DvidMakesThings/HW_10-In-Rack_PDU/docs/doxygen/latex/power__mgr_8c.tex

\doxysection{src/\+Software/\+ENERGIS\+\_\+\+RTOS/src/misc/power\+\_\+mgr.c File Reference}
\hypertarget{power__mgr_8c}{}\label{power__mgr_8c}\index{src/Software/ENERGIS\_RTOS/src/misc/power\_mgr.c@{src/Software/ENERGIS\_RTOS/src/misc/power\_mgr.c}}
{\ttfamily \#include "{}CONFIG.\+h"{}}\newline
Include dependency graph for power\+\_\+mgr.\+c\+:\nopagebreak
\begin{figure}[H]
\begin{center}
\leavevmode
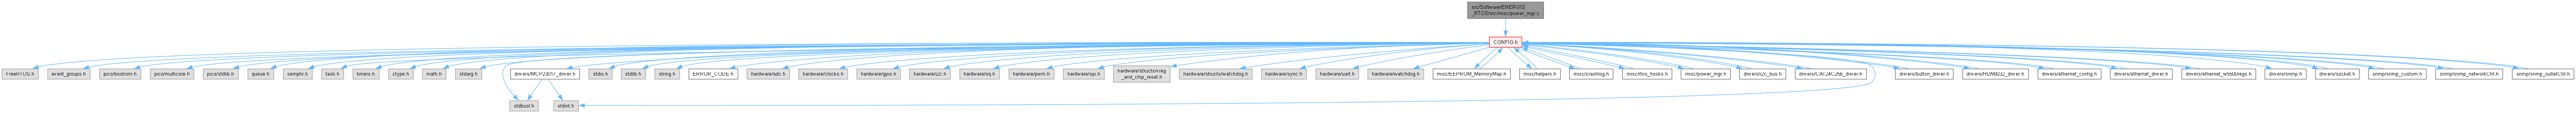
[picture p25: docs/doxygen/html/power__mgr_8c__incl.png]

\end{center}
\end{figure}
\doxysubsubsection*{Macros}
\begin{DoxyCompactItemize}
\item 
\#define \mbox{\hyperlink{power__mgr_8c_ab401161121a77906483bddf8a325013a}{POWER\+\_\+\+MGR\+\_\+\+TAG}}~"{}\mbox{[}Power\+Mgr\mbox{]}"{}
\end{DoxyCompactItemize}
\doxysubsubsection*{Functions}
\begin{DoxyCompactItemize}
\item 
static void \mbox{\hyperlink{power__mgr_8c_acf3f068b9c2b4714ec8b7b1eb2eff1e9}{turn\+\_\+off\+\_\+all\+\_\+relays}} (void)
\begin{DoxyCompactList}\small\item\em Disable all relay outputs using Switch\+Task API. \end{DoxyCompactList}\item 
static void \mbox{\hyperlink{power__mgr_8c_a61f31550510de9c4f3196700e41216ff}{turn\+\_\+off\+\_\+leds\+\_\+except\+\_\+pwr}} (void)
\begin{DoxyCompactList}\small\item\em Disable display LEDs except PWR\+\_\+\+LED for standby indication. \end{DoxyCompactList}\item 
static void \mbox{\hyperlink{power__mgr_8c_ae6615d2590136a1a1be071dce3a0690d}{turn\+\_\+off\+\_\+selection\+\_\+leds}} (void)
\begin{DoxyCompactList}\small\item\em Disable all channel selection LEDs. \end{DoxyCompactList}\item 
static void \mbox{\hyperlink{power__mgr_8c_af91a61d8ecbe1011e8a24851ca9602b6}{w5500\+\_\+hold\+\_\+reset}} (void)
\begin{DoxyCompactList}\small\item\em Assert W5500 hardware reset to disable Ethernet. \end{DoxyCompactList}\item 
static void \mbox{\hyperlink{power__mgr_8c_a0c57fadaa1a399b1257ebd7203e7884e}{w5500\+\_\+release\+\_\+reset}} (void)
\begin{DoxyCompactList}\small\item\em Deassert W5500 hardware reset to enable Ethernet. \end{DoxyCompactList}\item 
static void \mbox{\hyperlink{power__mgr_8c_afef33669bd179ec2e445c223bb1272a3}{set\+\_\+pwr\+\_\+led\+\_\+tracked}} (bool on)
\begin{DoxyCompactList}\small\item\em Set PWR\+\_\+\+LED state with change tracking. \end{DoxyCompactList}\item 
void \mbox{\hyperlink{group__misc3_ga83454e7bafa44edd5acce76b7aa91e0b}{Power\+\_\+\+Init}} (void)
\begin{DoxyCompactList}\small\item\em Initialize the power manager subsystem. \end{DoxyCompactList}\item 
\mbox{\hyperlink{group__misc3_gacd64982bf58e213a07ae1fe0f2235cb9}{power\+\_\+state\+\_\+t}} \mbox{\hyperlink{group__misc3_gad3252fba1863d278f2611cad531177f5}{Power\+\_\+\+Get\+State}} (void)
\begin{DoxyCompactList}\small\item\em Query the current system power state. \end{DoxyCompactList}\item 
void \mbox{\hyperlink{group__misc3_ga40de5935f9ba85f9141a9243b4d02c87}{Power\+\_\+\+Enter\+Standby}} (void)
\begin{DoxyCompactList}\small\item\em Enter standby mode. \end{DoxyCompactList}\item 
void \mbox{\hyperlink{group__misc3_gafa726e9d0fc140faa3f54c6905ac2520}{Power\+\_\+\+Exit\+Standby}} (void)
\begin{DoxyCompactList}\small\item\em Exit standby mode and return to normal operation. \end{DoxyCompactList}\item 
void \mbox{\hyperlink{group__misc3_ga0827dd667e39150cad0b7642a076d384}{Power\+\_\+\+Service\+Standby\+LED}} (void)
\begin{DoxyCompactList}\small\item\em Service LED indication in RUN and STANDBY modes. \end{DoxyCompactList}\end{DoxyCompactItemize}
\doxysubsubsection*{Variables}
\begin{DoxyCompactItemize}
\item 
static volatile \mbox{\hyperlink{group__misc3_gacd64982bf58e213a07ae1fe0f2235cb9}{power\+\_\+state\+\_\+t}} \mbox{\hyperlink{power__mgr_8c_aff8ae2fef9f0e3de41d83c40420a3da5}{s\+\_\+power\+\_\+state}} = \mbox{\hyperlink{group__misc3_ggacd64982bf58e213a07ae1fe0f2235cb9a63a8aa4bf635f74171bbfe8f145dd1cf}{PWR\+\_\+\+STATE\+\_\+\+RUN}}
\begin{DoxyCompactList}\small\item\em Current system power state (atomic access required) \end{DoxyCompactList}\item 
static volatile bool \mbox{\hyperlink{power__mgr_8c_a328078913eedcf9a440c49aa2805df76}{s\+\_\+pwr\+\_\+led\+\_\+state}} = false
\begin{DoxyCompactList}\small\item\em Tracks current PWR\+\_\+\+LED state to avoid redundant I2C writes. true = LED is ON, false = LED is OFF. \end{DoxyCompactList}\item 
\begin{tabbing}
xx\=xx\=xx\=xx\=xx\=xx\=xx\=xx\=xx\=\kill
struct \{\\
\>uint32\_t \mbox{\hyperlink{power__mgr_8c_a55c9db1db2e7f9a80337d744a4aef512}{last\_update\_ms}}\\
\>uint8\_t \mbox{\hyperlink{power__mgr_8c_a8f0aef86d47e45a899f77a8bb89d6432}{phase}}\\
\>uint8\_t \mbox{\hyperlink{power__mgr_8c_ac6116d5235e13e059e591879c46d7174}{direction}}\\
\} \mbox{\hyperlink{power__mgr_8c_a72aa8664ac0542eb9697aadbf5a93b1e}{s\_led\_anim}} = \{0, 0, 0\}\\

\end{tabbing}\begin{DoxyCompactList}\small\item\em Standby LED animation state. \end{DoxyCompactList}\end{DoxyCompactItemize}

\doxysubsection{Detailed Description}
\begin{DoxyAuthor}{Author}
Dvid\+Makes\+Things -\/ David Sipos
\end{DoxyAuthor}
\begin{DoxyVersion}{Version}
1.\+2.\+0 
\end{DoxyVersion}
\begin{DoxyDate}{Date}
2025-\/12-\/10
\end{DoxyDate}
Implementation of centralized power state management including standby mode entry/exit logic, hardware peripheral control coordination, and LED animation for standby indication.

This module coordinates multiple hardware peripherals (W5500, MCP23017, relays) and provides thread-\/safe state query for task behavior adaptation.

@project ENERGIS -\/ The Managed PDU Project for 10-\/Inch Rack @github \href{https://github.com/DvidMakesThings/HW_10-In-Rack_PDU}{\texttt{https\+://github.\+com/\+Dvid\+Makes\+Things/\+HW\+\_\+10-\/\+In-\/\+Rack\+\_\+\+PDU}} 

\label{doc-define-members}
\Hypertarget{power__mgr_8c_doc-define-members}
\doxysubsection{Macro Definition Documentation}
\Hypertarget{power__mgr_8c_ab401161121a77906483bddf8a325013a}\index{power\_mgr.c@{power\_mgr.c}!POWER\_MGR\_TAG@{POWER\_MGR\_TAG}}
\index{POWER\_MGR\_TAG@{POWER\_MGR\_TAG}!power\_mgr.c@{power\_mgr.c}}
\doxysubsubsection{\texorpdfstring{POWER\_MGR\_TAG}{POWER\_MGR\_TAG}}
{\footnotesize\ttfamily \label{power__mgr_8c_ab401161121a77906483bddf8a325013a} 
\#define POWER\+\_\+\+MGR\+\_\+\+TAG~"{}\mbox{[}Power\+Mgr\mbox{]}"{}}

\label{doc-func-members}
\Hypertarget{power__mgr_8c_doc-func-members}
\doxysubsection{Function Documentation}
\Hypertarget{power__mgr_8c_afef33669bd179ec2e445c223bb1272a3}\index{power\_mgr.c@{power\_mgr.c}!set\_pwr\_led\_tracked@{set\_pwr\_led\_tracked}}
\index{set\_pwr\_led\_tracked@{set\_pwr\_led\_tracked}!power\_mgr.c@{power\_mgr.c}}
\doxysubsubsection{\texorpdfstring{set\_pwr\_led\_tracked()}{set\_pwr\_led\_tracked()}}
{\footnotesize\ttfamily \label{power__mgr_8c_afef33669bd179ec2e445c223bb1272a3} 
void set\+\_\+pwr\+\_\+led\+\_\+tracked (\begin{DoxyParamCaption}\item[{bool}]{on}{}\end{DoxyParamCaption})\hspace{0.3cm}{\ttfamily [static]}}

Set PWR\+\_\+\+LED state with change tracking. 

Updates PWR\+\_\+\+LED state only if it differs from the current tracked state, avoiding redundant I2C write operations that can cause bus contention.

\begin{DoxyParams}{Parameters}
{\em on} & true to enable LED, false to disable LED\\
\hline
\end{DoxyParams}
\begin{DoxyReturn}{Returns}
None 
\end{DoxyReturn}
Here is the call graph for this function\+:\nopagebreak
\begin{figure}[H]
\begin{center}
\leavevmode

\end{center}
\end{figure}
Here is the caller graph for this function\+:\nopagebreak
\begin{figure}[H]
\begin{center}
\leavevmode

\end{center}
\end{figure}
\Hypertarget{power__mgr_8c_acf3f068b9c2b4714ec8b7b1eb2eff1e9}\index{power\_mgr.c@{power\_mgr.c}!turn\_off\_all\_relays@{turn\_off\_all\_relays}}
\index{turn\_off\_all\_relays@{turn\_off\_all\_relays}!power\_mgr.c@{power\_mgr.c}}
\doxysubsubsection{\texorpdfstring{turn\_off\_all\_relays()}{turn\_off\_all\_relays()}}
{\footnotesize\ttfamily \label{power__mgr_8c_acf3f068b9c2b4714ec8b7b1eb2eff1e9} 
void turn\+\_\+off\+\_\+all\+\_\+relays (\begin{DoxyParamCaption}\item[{void}]{}{}\end{DoxyParamCaption})\hspace{0.3cm}{\ttfamily [static]}}

Disable all relay outputs using Switch\+Task API. 

Enqueues a non-\/blocking command to turn off all relay outputs via the Switch\+Task message queue. This ensures serialized access to relay control hardware and prevents I2C bus contention.

\begin{DoxyReturn}{Returns}
None 
\end{DoxyReturn}
Here is the call graph for this function\+:\nopagebreak
\begin{figure}[H]
\begin{center}
\leavevmode
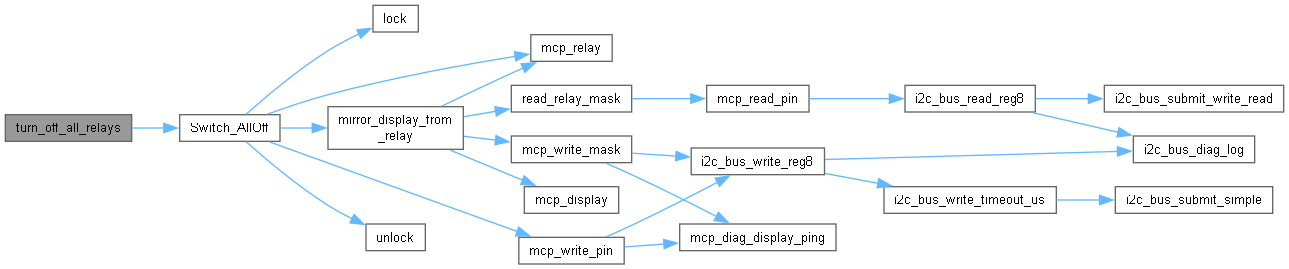
[picture p26: docs/doxygen/html/power__mgr_8c_acf3f068b9c2b4714ec8b7b1eb2eff1e9_cgraph.png]

\end{center}
\end{figure}
Here is the caller graph for this function\+:\nopagebreak
\begin{figure}[H]
\begin{center}
\leavevmode

\end{center}
\end{figure}
\Hypertarget{power__mgr_8c_a61f31550510de9c4f3196700e41216ff}\index{power\_mgr.c@{power\_mgr.c}!turn\_off\_leds\_except\_pwr@{turn\_off\_leds\_except\_pwr}}
\index{turn\_off\_leds\_except\_pwr@{turn\_off\_leds\_except\_pwr}!power\_mgr.c@{power\_mgr.c}}
\doxysubsubsection{\texorpdfstring{turn\_off\_leds\_except\_pwr()}{turn\_off\_leds\_except\_pwr()}}
{\footnotesize\ttfamily \label{power__mgr_8c_a61f31550510de9c4f3196700e41216ff} 
void turn\+\_\+off\+\_\+leds\+\_\+except\+\_\+pwr (\begin{DoxyParamCaption}\item[{void}]{}{}\end{DoxyParamCaption})\hspace{0.3cm}{\ttfamily [static]}}

Disable display LEDs except PWR\+\_\+\+LED for standby indication. 

Turns off FAULT and ETH LEDs while keeping PWR\+\_\+\+LED on. Uses Switch\+Task API to ensure serialized I2C access to the MCP23017 display controller. This prevents bus contention that can occur during concurrent access from multiple tasks.

\begin{DoxyReturn}{Returns}
None 
\end{DoxyReturn}
Here is the call graph for this function\+:\nopagebreak
\begin{figure}[H]
\begin{center}
\leavevmode
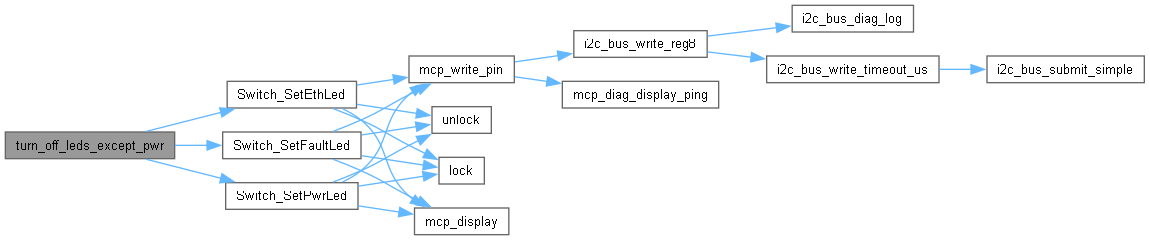
[picture p27: docs/doxygen/html/power__mgr_8c_a61f31550510de9c4f3196700e41216ff_cgraph.png]

\end{center}
\end{figure}
Here is the caller graph for this function\+:\nopagebreak
\begin{figure}[H]
\begin{center}
\leavevmode

\end{center}
\end{figure}
\Hypertarget{power__mgr_8c_ae6615d2590136a1a1be071dce3a0690d}\index{power\_mgr.c@{power\_mgr.c}!turn\_off\_selection\_leds@{turn\_off\_selection\_leds}}
\index{turn\_off\_selection\_leds@{turn\_off\_selection\_leds}!power\_mgr.c@{power\_mgr.c}}
\doxysubsubsection{\texorpdfstring{turn\_off\_selection\_leds()}{turn\_off\_selection\_leds()}}
{\footnotesize\ttfamily \label{power__mgr_8c_ae6615d2590136a1a1be071dce3a0690d} 
void turn\+\_\+off\+\_\+selection\+\_\+leds (\begin{DoxyParamCaption}\item[{void}]{}{}\end{DoxyParamCaption})\hspace{0.3cm}{\ttfamily [static]}}

Disable all channel selection LEDs. 

Turns off all selection LEDs using Switch\+Task API with 50ms timeout. Ensures serialized access to the selection LED MCP23017 controller.

\begin{DoxyReturn}{Returns}
None 
\end{DoxyReturn}
Here is the call graph for this function\+:\nopagebreak
\begin{figure}[H]
\begin{center}
\leavevmode

\end{center}
\end{figure}
Here is the caller graph for this function\+:\nopagebreak
\begin{figure}[H]
\begin{center}
\leavevmode

\end{center}
\end{figure}
\Hypertarget{power__mgr_8c_af91a61d8ecbe1011e8a24851ca9602b6}\index{power\_mgr.c@{power\_mgr.c}!w5500\_hold\_reset@{w5500\_hold\_reset}}
\index{w5500\_hold\_reset@{w5500\_hold\_reset}!power\_mgr.c@{power\_mgr.c}}
\doxysubsubsection{\texorpdfstring{w5500\_hold\_reset()}{w5500\_hold\_reset()}}
{\footnotesize\ttfamily \label{power__mgr_8c_af91a61d8ecbe1011e8a24851ca9602b6} 
void w5500\+\_\+hold\+\_\+reset (\begin{DoxyParamCaption}\item[{void}]{}{}\end{DoxyParamCaption})\hspace{0.3cm}{\ttfamily [static]}}

Assert W5500 hardware reset to disable Ethernet. 

Drives the W5500 RESET pin low, forcing the Ethernet controller into reset state. This disables the PHY, terminates all network connections, and stops all traffic. Power consumption is reduced as the chip enters a minimal state.

\begin{DoxyReturn}{Returns}
None 
\end{DoxyReturn}
Here is the caller graph for this function\+:\nopagebreak
\begin{figure}[H]
\begin{center}
\leavevmode

\end{center}
\end{figure}
\Hypertarget{power__mgr_8c_a0c57fadaa1a399b1257ebd7203e7884e}\index{power\_mgr.c@{power\_mgr.c}!w5500\_release\_reset@{w5500\_release\_reset}}
\index{w5500\_release\_reset@{w5500\_release\_reset}!power\_mgr.c@{power\_mgr.c}}
\doxysubsubsection{\texorpdfstring{w5500\_release\_reset()}{w5500\_release\_reset()}}
{\footnotesize\ttfamily \label{power__mgr_8c_a0c57fadaa1a399b1257ebd7203e7884e} 
void w5500\+\_\+release\+\_\+reset (\begin{DoxyParamCaption}\item[{void}]{}{}\end{DoxyParamCaption})\hspace{0.3cm}{\ttfamily [static]}}

Deassert W5500 hardware reset to enable Ethernet. 

Drives the W5500 RESET pin high, allowing the Ethernet controller to exit reset state and begin initialization. Net\+Task will detect the state change via \doxylink{group__misc3_gad3252fba1863d278f2611cad531177f5}{Power\+\_\+\+Get\+State()} and reinitialize network services.

\begin{DoxyReturn}{Returns}
None 
\end{DoxyReturn}
Here is the caller graph for this function\+:\nopagebreak
\begin{figure}[H]
\begin{center}
\leavevmode

\end{center}
\end{figure}

\label{doc-var-members}
\Hypertarget{power__mgr_8c_doc-var-members}
\doxysubsection{Variable Documentation}
\Hypertarget{power__mgr_8c_ac6116d5235e13e059e591879c46d7174}\index{power\_mgr.c@{power\_mgr.c}!direction@{direction}}
\index{direction@{direction}!power\_mgr.c@{power\_mgr.c}}
\doxysubsubsection{\texorpdfstring{direction}{direction}}
{\footnotesize\ttfamily \label{power__mgr_8c_ac6116d5235e13e059e591879c46d7174} 
uint8\+\_\+t direction}

0=fading in, 1=fading out \Hypertarget{power__mgr_8c_a55c9db1db2e7f9a80337d744a4aef512}\index{power\_mgr.c@{power\_mgr.c}!last\_update\_ms@{last\_update\_ms}}
\index{last\_update\_ms@{last\_update\_ms}!power\_mgr.c@{power\_mgr.c}}
\doxysubsubsection{\texorpdfstring{last\_update\_ms}{last\_update\_ms}}
{\footnotesize\ttfamily \label{power__mgr_8c_a55c9db1db2e7f9a80337d744a4aef512} 
uint32\+\_\+t last\+\_\+update\+\_\+ms}

Timestamp of last LED update \Hypertarget{power__mgr_8c_a8f0aef86d47e45a899f77a8bb89d6432}\index{power\_mgr.c@{power\_mgr.c}!phase@{phase}}
\index{phase@{phase}!power\_mgr.c@{power\_mgr.c}}
\doxysubsubsection{\texorpdfstring{phase}{phase}}
{\footnotesize\ttfamily \label{power__mgr_8c_a8f0aef86d47e45a899f77a8bb89d6432} 
uint8\+\_\+t phase}

Current phase in breathing cycle 0-\/255 \Hypertarget{power__mgr_8c_a72aa8664ac0542eb9697aadbf5a93b1e}\index{power\_mgr.c@{power\_mgr.c}!s\_led\_anim@{s\_led\_anim}}
\index{s\_led\_anim@{s\_led\_anim}!power\_mgr.c@{power\_mgr.c}}
\doxysubsubsection{\texorpdfstring{[struct]}{[struct]}}
{\footnotesize\ttfamily \label{power__mgr_8c_a72aa8664ac0542eb9697aadbf5a93b1e} 
struct  \{ ... \}  s\+\_\+led\+\_\+anim\hspace{0.3cm}{\ttfamily [static]}}

Standby LED animation state. 

\Hypertarget{power__mgr_8c_aff8ae2fef9f0e3de41d83c40420a3da5}\index{power\_mgr.c@{power\_mgr.c}!s\_power\_state@{s\_power\_state}}
\index{s\_power\_state@{s\_power\_state}!power\_mgr.c@{power\_mgr.c}}
\doxysubsubsection{\texorpdfstring{s\_power\_state}{s\_power\_state}}
{\footnotesize\ttfamily \label{power__mgr_8c_aff8ae2fef9f0e3de41d83c40420a3da5} 
volatile \mbox{\hyperlink{group__misc3_gacd64982bf58e213a07ae1fe0f2235cb9}{power\+\_\+state\+\_\+t}} s\+\_\+power\+\_\+state = \mbox{\hyperlink{group__misc3_ggacd64982bf58e213a07ae1fe0f2235cb9a63a8aa4bf635f74171bbfe8f145dd1cf}{PWR\+\_\+\+STATE\+\_\+\+RUN}}\hspace{0.3cm}{\ttfamily [static]}}

Current system power state (atomic access required) 

\Hypertarget{power__mgr_8c_a328078913eedcf9a440c49aa2805df76}\index{power\_mgr.c@{power\_mgr.c}!s\_pwr\_led\_state@{s\_pwr\_led\_state}}
\index{s\_pwr\_led\_state@{s\_pwr\_led\_state}!power\_mgr.c@{power\_mgr.c}}
\doxysubsubsection{\texorpdfstring{s\_pwr\_led\_state}{s\_pwr\_led\_state}}
{\footnotesize\ttfamily \label{power__mgr_8c_a328078913eedcf9a440c49aa2805df76} 
volatile bool s\+\_\+pwr\+\_\+led\+\_\+state = false\hspace{0.3cm}{\ttfamily [static]}}

Tracks current PWR\+\_\+\+LED state to avoid redundant I2C writes. true = LED is ON, false = LED is OFF.
