DvidMakesThings/HW_10-In-Rack_PDU/docs/doxygen/latex/snmp__power_mon_8h.tex

\doxysection{src/\+Software/\+ENERGIS\+\_\+\+RTOS/src/snmp/snmp\+\_\+power\+Mon.h File Reference}
\hypertarget{snmp__power_mon_8h}{}\label{snmp__power_mon_8h}\index{src/Software/ENERGIS\_RTOS/src/snmp/snmp\_powerMon.h@{src/Software/ENERGIS\_RTOS/src/snmp/snmp\_powerMon.h}}
{\ttfamily \#include "{}../\+CONFIG.\+h"{}}\newline
Include dependency graph for snmp\+\_\+power\+Mon.\+h\+:\nopagebreak
\begin{figure}[H]
\begin{center}
\leavevmode
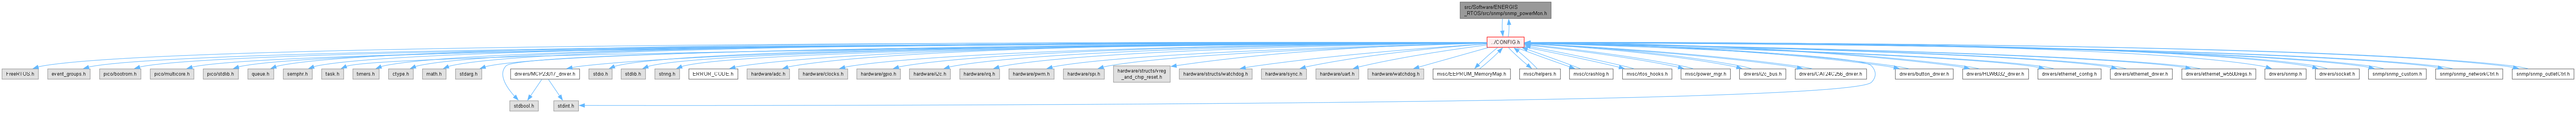
[picture p30: docs/doxygen/html/snmp__power_mon_8h__incl.png]

\end{center}
\end{figure}
This graph shows which files directly or indirectly include this file\+:\nopagebreak
\begin{figure}[H]
\begin{center}
\leavevmode
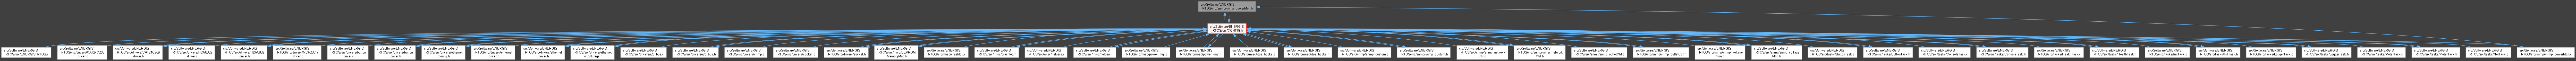
[picture p31: docs/doxygen/html/snmp__power_mon_8h__dep__incl.png]

\end{center}
\end{figure}
\doxysubsubsection*{Functions}
\begin{DoxyCompactItemize}
\item 
void \mbox{\hyperlink{group__snmp04_gaeddb705c447d49aea9383710d70e577f}{get\+\_\+power\+\_\+0\+\_\+\+MEAS\+\_\+\+VOLTAGE}} (void \texorpdfstring{$\ast$}{*}buf, uint8\+\_\+t \texorpdfstring{$\ast$}{*}len)
\begin{DoxyCompactList}\small\item\em SNMP getter for outlet 0 voltage \mbox{[}V\mbox{]}. \end{DoxyCompactList}\item 
void \mbox{\hyperlink{group__snmp04_ga7d3f514014d0ff13a8f767e419fc9ea4}{get\+\_\+power\+\_\+0\+\_\+\+MEAS\+\_\+\+CURRENT}} (void \texorpdfstring{$\ast$}{*}buf, uint8\+\_\+t \texorpdfstring{$\ast$}{*}len)
\begin{DoxyCompactList}\small\item\em SNMP getter for outlet 0 current \mbox{[}A\mbox{]}. \end{DoxyCompactList}\item 
void \mbox{\hyperlink{group__snmp04_gadb419836c678f41e04ad2da2f3c8f20c}{get\+\_\+power\+\_\+0\+\_\+\+MEAS\+\_\+\+WATT}} (void \texorpdfstring{$\ast$}{*}buf, uint8\+\_\+t \texorpdfstring{$\ast$}{*}len)
\begin{DoxyCompactList}\small\item\em SNMP getter for outlet 0 power \mbox{[}W\mbox{]}. \end{DoxyCompactList}\item 
void \mbox{\hyperlink{group__snmp04_ga7600c8a2b0563156b9c6e976a953c4c9}{get\+\_\+power\+\_\+0\+\_\+\+MEAS\+\_\+\+PF}} (void \texorpdfstring{$\ast$}{*}buf, uint8\+\_\+t \texorpdfstring{$\ast$}{*}len)
\begin{DoxyCompactList}\small\item\em SNMP getter for outlet 0 power factor. \end{DoxyCompactList}\item 
void \mbox{\hyperlink{group__snmp04_ga94f308f8eb3b1aefc1ea03e8483e9002}{get\+\_\+power\+\_\+0\+\_\+\+MEAS\+\_\+\+KWH}} (void \texorpdfstring{$\ast$}{*}buf, uint8\+\_\+t \texorpdfstring{$\ast$}{*}len)
\begin{DoxyCompactList}\small\item\em SNMP getter for outlet 0 accumulated energy \mbox{[}k\+Wh\mbox{]}. \end{DoxyCompactList}\item 
void \mbox{\hyperlink{group__snmp04_gafcb9a40de0c79059dbea47256843e022}{get\+\_\+power\+\_\+0\+\_\+\+MEAS\+\_\+\+UPTIME}} (void \texorpdfstring{$\ast$}{*}buf, uint8\+\_\+t \texorpdfstring{$\ast$}{*}len)
\begin{DoxyCompactList}\small\item\em SNMP getter for outlet 0 uptime \mbox{[}s\mbox{]}. \end{DoxyCompactList}\item 
void \mbox{\hyperlink{group__snmp04_ga86e7e6f79e7099c77e5a6b491b011f25}{get\+\_\+power\+\_\+1\+\_\+\+MEAS\+\_\+\+VOLTAGE}} (void \texorpdfstring{$\ast$}{*}buf, uint8\+\_\+t \texorpdfstring{$\ast$}{*}len)
\item 
void \mbox{\hyperlink{group__snmp04_gac2f98a31afbedb561913f7e71db59c6a}{get\+\_\+power\+\_\+1\+\_\+\+MEAS\+\_\+\+CURRENT}} (void \texorpdfstring{$\ast$}{*}buf, uint8\+\_\+t \texorpdfstring{$\ast$}{*}len)
\item 
void \mbox{\hyperlink{group__snmp04_ga31d0a6724bfe3548205d760b8d50c4aa}{get\+\_\+power\+\_\+1\+\_\+\+MEAS\+\_\+\+WATT}} (void \texorpdfstring{$\ast$}{*}buf, uint8\+\_\+t \texorpdfstring{$\ast$}{*}len)
\item 
void \mbox{\hyperlink{group__snmp04_gaf18599cd6961c9205b7bf508f087b86f}{get\+\_\+power\+\_\+1\+\_\+\+MEAS\+\_\+\+PF}} (void \texorpdfstring{$\ast$}{*}buf, uint8\+\_\+t \texorpdfstring{$\ast$}{*}len)
\item 
void \mbox{\hyperlink{group__snmp04_ga4e96087068a52153f8fca484c1aa1cf5}{get\+\_\+power\+\_\+1\+\_\+\+MEAS\+\_\+\+KWH}} (void \texorpdfstring{$\ast$}{*}buf, uint8\+\_\+t \texorpdfstring{$\ast$}{*}len)
\item 
void \mbox{\hyperlink{group__snmp04_ga4f7f1bc987837b712f0fc016c30f4dfb}{get\+\_\+power\+\_\+1\+\_\+\+MEAS\+\_\+\+UPTIME}} (void \texorpdfstring{$\ast$}{*}buf, uint8\+\_\+t \texorpdfstring{$\ast$}{*}len)
\item 
void \mbox{\hyperlink{group__snmp04_ga6999114896986c83f40e4a7e64650bee}{get\+\_\+power\+\_\+2\+\_\+\+MEAS\+\_\+\+VOLTAGE}} (void \texorpdfstring{$\ast$}{*}buf, uint8\+\_\+t \texorpdfstring{$\ast$}{*}len)
\item 
void \mbox{\hyperlink{group__snmp04_ga395609c13fbe74047f5f4e28df5eb2fe}{get\+\_\+power\+\_\+2\+\_\+\+MEAS\+\_\+\+CURRENT}} (void \texorpdfstring{$\ast$}{*}buf, uint8\+\_\+t \texorpdfstring{$\ast$}{*}len)
\item 
void \mbox{\hyperlink{group__snmp04_ga2d42680dc078a8f866d321d35324bec6}{get\+\_\+power\+\_\+2\+\_\+\+MEAS\+\_\+\+WATT}} (void \texorpdfstring{$\ast$}{*}buf, uint8\+\_\+t \texorpdfstring{$\ast$}{*}len)
\item 
void \mbox{\hyperlink{group__snmp04_gad744eb3629b153fec5307ec10b7fff8a}{get\+\_\+power\+\_\+2\+\_\+\+MEAS\+\_\+\+PF}} (void \texorpdfstring{$\ast$}{*}buf, uint8\+\_\+t \texorpdfstring{$\ast$}{*}len)
\item 
void \mbox{\hyperlink{group__snmp04_ga45047ccc0259bb4c316d24422c195dfe}{get\+\_\+power\+\_\+2\+\_\+\+MEAS\+\_\+\+KWH}} (void \texorpdfstring{$\ast$}{*}buf, uint8\+\_\+t \texorpdfstring{$\ast$}{*}len)
\item 
void \mbox{\hyperlink{group__snmp04_gaaa1e5b4d5f12f50ca19c3be0a9fb5441}{get\+\_\+power\+\_\+2\+\_\+\+MEAS\+\_\+\+UPTIME}} (void \texorpdfstring{$\ast$}{*}buf, uint8\+\_\+t \texorpdfstring{$\ast$}{*}len)
\item 
void \mbox{\hyperlink{group__snmp04_ga2aefb4399fd6e3d0f09698ef444c9b7f}{get\+\_\+power\+\_\+3\+\_\+\+MEAS\+\_\+\+VOLTAGE}} (void \texorpdfstring{$\ast$}{*}buf, uint8\+\_\+t \texorpdfstring{$\ast$}{*}len)
\item 
void \mbox{\hyperlink{group__snmp04_gabf7a057c1322f3f94b509e829c930856}{get\+\_\+power\+\_\+3\+\_\+\+MEAS\+\_\+\+CURRENT}} (void \texorpdfstring{$\ast$}{*}buf, uint8\+\_\+t \texorpdfstring{$\ast$}{*}len)
\item 
void \mbox{\hyperlink{group__snmp04_ga6e1b875b50c2466f4e94df604ba78dd3}{get\+\_\+power\+\_\+3\+\_\+\+MEAS\+\_\+\+WATT}} (void \texorpdfstring{$\ast$}{*}buf, uint8\+\_\+t \texorpdfstring{$\ast$}{*}len)
\item 
void \mbox{\hyperlink{group__snmp04_ga74b0174cff7145bacba6463db9f4acf8}{get\+\_\+power\+\_\+3\+\_\+\+MEAS\+\_\+\+PF}} (void \texorpdfstring{$\ast$}{*}buf, uint8\+\_\+t \texorpdfstring{$\ast$}{*}len)
\item 
void \mbox{\hyperlink{group__snmp04_ga08b3386b1eb4b9344670862509b5c1ac}{get\+\_\+power\+\_\+3\+\_\+\+MEAS\+\_\+\+KWH}} (void \texorpdfstring{$\ast$}{*}buf, uint8\+\_\+t \texorpdfstring{$\ast$}{*}len)
\item 
void \mbox{\hyperlink{group__snmp04_gad4f817dbe1d7bf7a05c2fc578dbb8240}{get\+\_\+power\+\_\+3\+\_\+\+MEAS\+\_\+\+UPTIME}} (void \texorpdfstring{$\ast$}{*}buf, uint8\+\_\+t \texorpdfstring{$\ast$}{*}len)
\item 
void \mbox{\hyperlink{group__snmp04_ga4272024a4b19d4dfcd2a297ece67f33a}{get\+\_\+power\+\_\+4\+\_\+\+MEAS\+\_\+\+VOLTAGE}} (void \texorpdfstring{$\ast$}{*}buf, uint8\+\_\+t \texorpdfstring{$\ast$}{*}len)
\item 
void \mbox{\hyperlink{group__snmp04_ga0089b6508cc43155c3d575b126af2d20}{get\+\_\+power\+\_\+4\+\_\+\+MEAS\+\_\+\+CURRENT}} (void \texorpdfstring{$\ast$}{*}buf, uint8\+\_\+t \texorpdfstring{$\ast$}{*}len)
\item 
void \mbox{\hyperlink{group__snmp04_ga392660365480bb251231263c106515e1}{get\+\_\+power\+\_\+4\+\_\+\+MEAS\+\_\+\+WATT}} (void \texorpdfstring{$\ast$}{*}buf, uint8\+\_\+t \texorpdfstring{$\ast$}{*}len)
\item 
void \mbox{\hyperlink{group__snmp04_gac9b5a90014130673828656560a1a05aa}{get\+\_\+power\+\_\+4\+\_\+\+MEAS\+\_\+\+PF}} (void \texorpdfstring{$\ast$}{*}buf, uint8\+\_\+t \texorpdfstring{$\ast$}{*}len)
\item 
void \mbox{\hyperlink{group__snmp04_ga0636c725bad0de2b92bd4e0e19624ba6}{get\+\_\+power\+\_\+4\+\_\+\+MEAS\+\_\+\+KWH}} (void \texorpdfstring{$\ast$}{*}buf, uint8\+\_\+t \texorpdfstring{$\ast$}{*}len)
\item 
void \mbox{\hyperlink{group__snmp04_ga3ba5522da3bf9dada9c54e4255664f19}{get\+\_\+power\+\_\+4\+\_\+\+MEAS\+\_\+\+UPTIME}} (void \texorpdfstring{$\ast$}{*}buf, uint8\+\_\+t \texorpdfstring{$\ast$}{*}len)
\item 
void \mbox{\hyperlink{group__snmp04_ga413ebbf84e354a13a6b3a0e877016d91}{get\+\_\+power\+\_\+5\+\_\+\+MEAS\+\_\+\+VOLTAGE}} (void \texorpdfstring{$\ast$}{*}buf, uint8\+\_\+t \texorpdfstring{$\ast$}{*}len)
\item 
void \mbox{\hyperlink{group__snmp04_ga2d54ebdbcbda1e673078a883bbd3f823}{get\+\_\+power\+\_\+5\+\_\+\+MEAS\+\_\+\+CURRENT}} (void \texorpdfstring{$\ast$}{*}buf, uint8\+\_\+t \texorpdfstring{$\ast$}{*}len)
\item 
void \mbox{\hyperlink{group__snmp04_ga099bef93da26675aee7ed6a5364fd84d}{get\+\_\+power\+\_\+5\+\_\+\+MEAS\+\_\+\+WATT}} (void \texorpdfstring{$\ast$}{*}buf, uint8\+\_\+t \texorpdfstring{$\ast$}{*}len)
\item 
void \mbox{\hyperlink{group__snmp04_gaf3f2471baf1ec75a77406f8d2d408a7d}{get\+\_\+power\+\_\+5\+\_\+\+MEAS\+\_\+\+PF}} (void \texorpdfstring{$\ast$}{*}buf, uint8\+\_\+t \texorpdfstring{$\ast$}{*}len)
\item 
void \mbox{\hyperlink{group__snmp04_gaa8a57c3439938ecab0ffda554bee351c}{get\+\_\+power\+\_\+5\+\_\+\+MEAS\+\_\+\+KWH}} (void \texorpdfstring{$\ast$}{*}buf, uint8\+\_\+t \texorpdfstring{$\ast$}{*}len)
\item 
void \mbox{\hyperlink{group__snmp04_ga2db328f572e9dfadddfe9b52bef80437}{get\+\_\+power\+\_\+5\+\_\+\+MEAS\+\_\+\+UPTIME}} (void \texorpdfstring{$\ast$}{*}buf, uint8\+\_\+t \texorpdfstring{$\ast$}{*}len)
\item 
void \mbox{\hyperlink{group__snmp04_ga898e7752a6a2e4915e9559790affa434}{get\+\_\+power\+\_\+6\+\_\+\+MEAS\+\_\+\+VOLTAGE}} (void \texorpdfstring{$\ast$}{*}buf, uint8\+\_\+t \texorpdfstring{$\ast$}{*}len)
\item 
void \mbox{\hyperlink{group__snmp04_ga310ed582360138222f16032b32609149}{get\+\_\+power\+\_\+6\+\_\+\+MEAS\+\_\+\+CURRENT}} (void \texorpdfstring{$\ast$}{*}buf, uint8\+\_\+t \texorpdfstring{$\ast$}{*}len)
\item 
void \mbox{\hyperlink{group__snmp04_ga27e74e157a229565c78eb28d2fad2ef7}{get\+\_\+power\+\_\+6\+\_\+\+MEAS\+\_\+\+WATT}} (void \texorpdfstring{$\ast$}{*}buf, uint8\+\_\+t \texorpdfstring{$\ast$}{*}len)
\item 
void \mbox{\hyperlink{group__snmp04_ga48f6203e2a2853657a3d8e5cb3a6be45}{get\+\_\+power\+\_\+6\+\_\+\+MEAS\+\_\+\+PF}} (void \texorpdfstring{$\ast$}{*}buf, uint8\+\_\+t \texorpdfstring{$\ast$}{*}len)
\item 
void \mbox{\hyperlink{group__snmp04_ga8ffc3344b86d1382e242b777b08eff68}{get\+\_\+power\+\_\+6\+\_\+\+MEAS\+\_\+\+KWH}} (void \texorpdfstring{$\ast$}{*}buf, uint8\+\_\+t \texorpdfstring{$\ast$}{*}len)
\item 
void \mbox{\hyperlink{group__snmp04_ga2873bf645f6829dd2e9de2f8fd671746}{get\+\_\+power\+\_\+6\+\_\+\+MEAS\+\_\+\+UPTIME}} (void \texorpdfstring{$\ast$}{*}buf, uint8\+\_\+t \texorpdfstring{$\ast$}{*}len)
\item 
void \mbox{\hyperlink{group__snmp04_ga6a32893fce4272e8763b7ead30d8c220}{get\+\_\+power\+\_\+7\+\_\+\+MEAS\+\_\+\+VOLTAGE}} (void \texorpdfstring{$\ast$}{*}buf, uint8\+\_\+t \texorpdfstring{$\ast$}{*}len)
\item 
void \mbox{\hyperlink{group__snmp04_ga8eb883070f6ca2ea1fcc1b565542f666}{get\+\_\+power\+\_\+7\+\_\+\+MEAS\+\_\+\+CURRENT}} (void \texorpdfstring{$\ast$}{*}buf, uint8\+\_\+t \texorpdfstring{$\ast$}{*}len)
\item 
void \mbox{\hyperlink{group__snmp04_ga0795a0f8103ea3c4ee78fb2ed1c55720}{get\+\_\+power\+\_\+7\+\_\+\+MEAS\+\_\+\+WATT}} (void \texorpdfstring{$\ast$}{*}buf, uint8\+\_\+t \texorpdfstring{$\ast$}{*}len)
\item 
void \mbox{\hyperlink{group__snmp04_ga1b3b965bb98b3d5ceb613faa26d40e4b}{get\+\_\+power\+\_\+7\+\_\+\+MEAS\+\_\+\+PF}} (void \texorpdfstring{$\ast$}{*}buf, uint8\+\_\+t \texorpdfstring{$\ast$}{*}len)
\item 
void \mbox{\hyperlink{group__snmp04_gac68a3d7b770aa85c6d2a039ea997ed8f}{get\+\_\+power\+\_\+7\+\_\+\+MEAS\+\_\+\+KWH}} (void \texorpdfstring{$\ast$}{*}buf, uint8\+\_\+t \texorpdfstring{$\ast$}{*}len)
\item 
void \mbox{\hyperlink{group__snmp04_gae98cdc15b6029754491f3142021dffe6}{get\+\_\+power\+\_\+7\+\_\+\+MEAS\+\_\+\+UPTIME}} (void \texorpdfstring{$\ast$}{*}buf, uint8\+\_\+t \texorpdfstring{$\ast$}{*}len)
\item 
void \mbox{\hyperlink{group__snmp04_gac66c88289a827019e9d7d2fd52c8a25d}{get\+\_\+ocp\+\_\+\+STATE}} (void \texorpdfstring{$\ast$}{*}buf, uint8\+\_\+t \texorpdfstring{$\ast$}{*}len)
\begin{DoxyCompactList}\small\item\em SNMP getter for overcurrent protection state. \end{DoxyCompactList}\item 
void \mbox{\hyperlink{group__snmp04_gac64f180957717b1f72f3bb0d46657f7c}{get\+\_\+ocp\+\_\+\+TOTAL\+\_\+\+CURRENT\+\_\+A}} (void \texorpdfstring{$\ast$}{*}buf, uint8\+\_\+t \texorpdfstring{$\ast$}{*}len)
\begin{DoxyCompactList}\small\item\em SNMP getter for total measured current across all outlets \mbox{[}A\mbox{]}. \end{DoxyCompactList}\item 
void \mbox{\hyperlink{group__snmp04_gab7ffa6c94b3c4085b6ceb7fec2b08723}{get\+\_\+ocp\+\_\+\+LIMIT\+\_\+A}} (void \texorpdfstring{$\ast$}{*}buf, uint8\+\_\+t \texorpdfstring{$\ast$}{*}len)
\begin{DoxyCompactList}\small\item\em SNMP getter for configured OCP current limit \mbox{[}A\mbox{]}. \end{DoxyCompactList}\item 
void \mbox{\hyperlink{group__snmp04_ga59836958c7dde04d045c218bc4bfa82c}{get\+\_\+ocp\+\_\+\+WARNING\+\_\+\+THRESHOLD\+\_\+A}} (void \texorpdfstring{$\ast$}{*}buf, uint8\+\_\+t \texorpdfstring{$\ast$}{*}len)
\begin{DoxyCompactList}\small\item\em SNMP getter for OCP warning threshold \mbox{[}A\mbox{]}. \end{DoxyCompactList}\item 
void \mbox{\hyperlink{group__snmp04_gad078fc7ee62f370b56ba305985db7faf}{get\+\_\+ocp\+\_\+\+CRITICAL\+\_\+\+THRESHOLD\+\_\+A}} (void \texorpdfstring{$\ast$}{*}buf, uint8\+\_\+t \texorpdfstring{$\ast$}{*}len)
\begin{DoxyCompactList}\small\item\em SNMP getter for OCP critical threshold \mbox{[}A\mbox{]}. \end{DoxyCompactList}\item 
void \mbox{\hyperlink{group__snmp04_ga298c0c01b328703f6ab782a3aefdb475}{get\+\_\+ocp\+\_\+\+RECOVERY\+\_\+\+THRESHOLD\+\_\+A}} (void \texorpdfstring{$\ast$}{*}buf, uint8\+\_\+t \texorpdfstring{$\ast$}{*}len)
\begin{DoxyCompactList}\small\item\em SNMP getter for OCP recovery threshold \mbox{[}A\mbox{]}. \end{DoxyCompactList}\item 
void \mbox{\hyperlink{group__snmp04_ga4f79c8b9c7d28d59cff221808b47f082}{get\+\_\+ocp\+\_\+\+LAST\+\_\+\+TRIPPED\+\_\+\+CH}} (void \texorpdfstring{$\ast$}{*}buf, uint8\+\_\+t \texorpdfstring{$\ast$}{*}len)
\begin{DoxyCompactList}\small\item\em SNMP getter for last tripped channel. \end{DoxyCompactList}\item 
void \mbox{\hyperlink{group__snmp04_gaeb4bf92301309e943f28678b8a92cadb}{get\+\_\+ocp\+\_\+\+TRIP\+\_\+\+COUNT}} (void \texorpdfstring{$\ast$}{*}buf, uint8\+\_\+t \texorpdfstring{$\ast$}{*}len)
\begin{DoxyCompactList}\small\item\em SNMP getter for OCP trip count since boot. \end{DoxyCompactList}\item 
void \mbox{\hyperlink{group__snmp04_gad08889d91475184951158037ae7988e3}{get\+\_\+ocp\+\_\+\+LAST\+\_\+\+TRIP\+\_\+\+MS}} (void \texorpdfstring{$\ast$}{*}buf, uint8\+\_\+t \texorpdfstring{$\ast$}{*}len)
\begin{DoxyCompactList}\small\item\em SNMP getter for last trip timestamp in milliseconds since boot. \end{DoxyCompactList}\item 
void \mbox{\hyperlink{group__snmp04_ga397cba4cff16c21da10f1da4a86235d2}{get\+\_\+ocp\+\_\+\+SWITCHING\+\_\+\+ALLOWED}} (void \texorpdfstring{$\ast$}{*}buf, uint8\+\_\+t \texorpdfstring{$\ast$}{*}len)
\begin{DoxyCompactList}\small\item\em SNMP getter for switching-\/allowed flag. \end{DoxyCompactList}\item 
void \mbox{\hyperlink{group__snmp04_gade7b106ecfdbb74b00cd434f7d23104b}{get\+\_\+ocp\+\_\+\+RESET}} (void \texorpdfstring{$\ast$}{*}buf, uint8\+\_\+t \texorpdfstring{$\ast$}{*}len)
\begin{DoxyCompactList}\small\item\em SNMP getter for OCP reset control value. \end{DoxyCompactList}\item 
void \mbox{\hyperlink{group__snmp04_gaf8f7c0a54cdf6546c526e37786b80baa}{set\+\_\+ocp\+\_\+\+RESET}} (int32\+\_\+t v)
\begin{DoxyCompactList}\small\item\em SNMP setter to clear OCP lockout. \end{DoxyCompactList}\end{DoxyCompactItemize}

\doxysubsection{Detailed Description}
\begin{DoxyAuthor}{Author}
Dvid\+Makes\+Things -\/ David Sipos 
\end{DoxyAuthor}
