DvidMakesThings/HW_10-In-Rack_PDU/docs/doxygen/latex/snmp__voltage_mon_8h.tex

\doxysection{src/\+Software/\+ENERGIS\+\_\+\+RTOS/src/snmp/snmp\+\_\+voltage\+Mon.h File Reference}
\hypertarget{snmp__voltage_mon_8h}{}\label{snmp__voltage_mon_8h}\index{src/Software/ENERGIS\_RTOS/src/snmp/snmp\_voltageMon.h@{src/Software/ENERGIS\_RTOS/src/snmp/snmp\_voltageMon.h}}
{\ttfamily \#include "{}../\+CONFIG.\+h"{}}\newline
Include dependency graph for snmp\+\_\+voltage\+Mon.\+h\+:\nopagebreak
\begin{figure}[H]
\begin{center}
\leavevmode
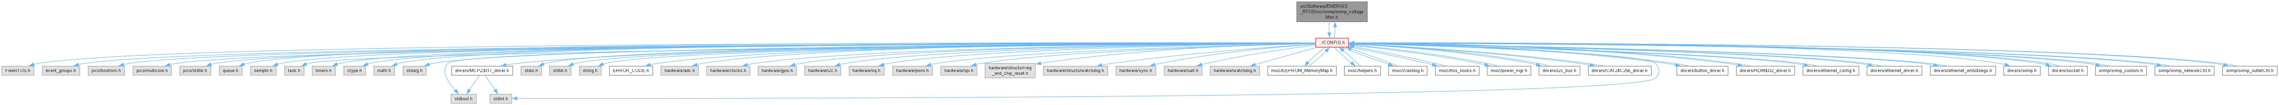
[picture p33: docs/doxygen/html/snmp__voltage_mon_8h__incl.png]

\end{center}
\end{figure}
This graph shows which files directly or indirectly include this file\+:\nopagebreak
\begin{figure}[H]
\begin{center}
\leavevmode
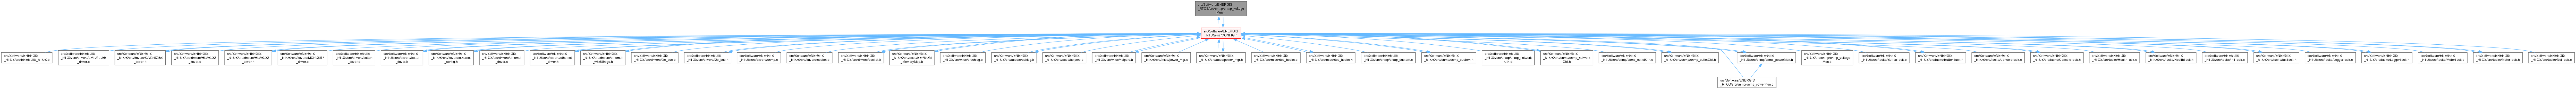
[picture p34: docs/doxygen/html/snmp__voltage_mon_8h__dep__incl.png]

\end{center}
\end{figure}
\doxysubsubsection*{Functions}
\begin{DoxyCompactItemize}
\item 
void \mbox{\hyperlink{group__snmp05_ga49b2857ddaab294f0f73932f5c16eddb}{get\+\_\+temp\+Sensor\+Voltage}} (void \texorpdfstring{$\ast$}{*}buf, uint8\+\_\+t \texorpdfstring{$\ast$}{*}len)
\begin{DoxyCompactList}\small\item\em SNMP getter for on-\/die temperature sensor voltage \mbox{[}V\mbox{]}. \end{DoxyCompactList}\item 
void \mbox{\hyperlink{group__snmp05_ga07d36a9715f0433b1988b447807b3015}{get\+\_\+temp\+Sensor\+Temperature}} (void \texorpdfstring{$\ast$}{*}buf, uint8\+\_\+t \texorpdfstring{$\ast$}{*}len)
\begin{DoxyCompactList}\small\item\em SNMP getter for on-\/die temperature \mbox{[}°C\mbox{]}. \end{DoxyCompactList}\item 
void \mbox{\hyperlink{group__snmp05_ga2618c7cb453d6e0a9d958bc932d38a9a}{get\+\_\+\+VSUPPLY}} (void \texorpdfstring{$\ast$}{*}buf, uint8\+\_\+t \texorpdfstring{$\ast$}{*}len)
\begin{DoxyCompactList}\small\item\em SNMP getter for V\+\_\+\+SUPPLY rail voltage \mbox{[}V\mbox{]}. \end{DoxyCompactList}\item 
void \mbox{\hyperlink{group__snmp05_ga574d71ccd641800ba60092a96698aae3}{get\+\_\+\+VUSB}} (void \texorpdfstring{$\ast$}{*}buf, uint8\+\_\+t \texorpdfstring{$\ast$}{*}len)
\begin{DoxyCompactList}\small\item\em SNMP getter for V\+\_\+\+USB rail voltage \mbox{[}V\mbox{]}. \end{DoxyCompactList}\item 
void \mbox{\hyperlink{group__snmp05_gae1abd1add9071497c30abed555937772}{get\+\_\+\+VSUPPLY\+\_\+divider}} (void \texorpdfstring{$\ast$}{*}buf, uint8\+\_\+t \texorpdfstring{$\ast$}{*}len)
\begin{DoxyCompactList}\small\item\em SNMP getter for V\+\_\+\+SUPPLY divider tap voltage \mbox{[}V\mbox{]}. \end{DoxyCompactList}\item 
void \mbox{\hyperlink{group__snmp05_ga0c98fc2539c1c130d4ffba0bbf9224d3}{get\+\_\+\+VUSB\+\_\+divider}} (void \texorpdfstring{$\ast$}{*}buf, uint8\+\_\+t \texorpdfstring{$\ast$}{*}len)
\begin{DoxyCompactList}\small\item\em SNMP getter for V\+\_\+\+USB divider tap voltage \mbox{[}V\mbox{]}. \end{DoxyCompactList}\item 
void \mbox{\hyperlink{group__snmp05_ga55c9f217632f7444fea3b3ff5fbc7332}{get\+\_\+core\+VREG}} (void \texorpdfstring{$\ast$}{*}buf, uint8\+\_\+t \texorpdfstring{$\ast$}{*}len)
\begin{DoxyCompactList}\small\item\em SNMP getter for core VREG voltage \mbox{[}V\mbox{]}. \end{DoxyCompactList}\item 
void \mbox{\hyperlink{group__snmp05_ga3906d2584f13fb4dbb04d8cb3d29a881}{get\+\_\+core\+VREG\+\_\+status}} (void \texorpdfstring{$\ast$}{*}buf, uint8\+\_\+t \texorpdfstring{$\ast$}{*}len)
\begin{DoxyCompactList}\small\item\em SNMP getter for core VREG status. \end{DoxyCompactList}\item 
void \mbox{\hyperlink{group__snmp05_ga6dfa68d52f72c963b8b84259854db6c9}{get\+\_\+bandgap\+Ref}} (void \texorpdfstring{$\ast$}{*}buf, uint8\+\_\+t \texorpdfstring{$\ast$}{*}len)
\begin{DoxyCompactList}\small\item\em SNMP getter for bandgap reference voltage \mbox{[}V\mbox{]}. \end{DoxyCompactList}\item 
void \mbox{\hyperlink{group__snmp05_gad373e18c9aff32c0faf35c41f0a4050b}{get\+\_\+usb\+PHYrail}} (void \texorpdfstring{$\ast$}{*}buf, uint8\+\_\+t \texorpdfstring{$\ast$}{*}len)
\begin{DoxyCompactList}\small\item\em SNMP getter for USB PHY rail voltage \mbox{[}V\mbox{]}. \end{DoxyCompactList}\item 
void \mbox{\hyperlink{group__snmp05_ga7437bd619910f7c801d6b5368154eb4f}{get\+\_\+io\+Rail}} (void \texorpdfstring{$\ast$}{*}buf, uint8\+\_\+t \texorpdfstring{$\ast$}{*}len)
\begin{DoxyCompactList}\small\item\em SNMP getter for IO rail voltage \mbox{[}V\mbox{]}. \end{DoxyCompactList}\end{DoxyCompactItemize}

\doxysubsection{Detailed Description}
\begin{DoxyAuthor}{Author}
Dvid\+Makes\+Things -\/ David Sipos 
\end{DoxyAuthor}
