DvidMakesThings/HW_10-In-Rack_PDU/docs/doxygen/latex/topics.tex

\doxysection{Topics}
Here is a list of all topics with brief descriptions\+:\begin{DoxyCompactList}
\item \contentsline{section}{Configuration Files}{\pageref{group__config}}{}
\begin{DoxyCompactList}
\item \contentsline{section}{1. Hardware Configuration}{\pageref{group__config01}}{}
\begin{DoxyCompactList}
\item \contentsline{section}{Overcurrent Protection Thresholds}{\pageref{group__overcurrent__thresholds}}{}
\end{DoxyCompactList}
\item \contentsline{section}{2. W5500 Ethernet Configuration}{\pageref{group__config02}}{}
\begin{DoxyCompactList}
\item \contentsline{section}{Hardware Pin Configuration}{\pageref{group___w5500___h_w}}{}
\item \contentsline{section}{Socket Memory Allocation}{\pageref{group___w5500___m_e_m}}{}
\item \contentsline{section}{Network Configuration Defaults}{\pageref{group___w5500___n_e_t}}{}
\item \contentsline{section}{Protocol Support Flags}{\pageref{group___w5500___p_r_o_t_o}}{}
\item \contentsline{section}{RTOS Integration Parameters}{\pageref{group___w5500___r_t_o_s}}{}
\item \contentsline{section}{Advanced TCP/\+IP Tuning}{\pageref{group___w5500___a_d_v}}{}
\item \contentsline{section}{Debug and Logging}{\pageref{group___w5500___d_b_g}}{}
\end{DoxyCompactList}
\item \contentsline{section}{3. W5500 Register definitions}{\pageref{group__config03}}{}
\item \contentsline{section}{4. Error Coding Configuration}{\pageref{group__config04}}{}
\item \contentsline{section}{5. RTOS Configuration}{\pageref{group__config05}}{}
\item \contentsline{section}{6. EEPROM Memory Map}{\pageref{group__config06}}{}
\end{DoxyCompactList}
\item \contentsline{section}{Drivers}{\pageref{group__drivers}}{}
\begin{DoxyCompactList}
\item \contentsline{section}{1. Button Driver}{\pageref{group__driver01}}{}
\item \contentsline{section}{2. EEPROM Driver}{\pageref{group__driver02}}{}
\item \contentsline{section}{3. W5500 Driver Implementation}{\pageref{group__drivers03}}{}
\item \contentsline{section}{4. HLW8032 Power Measurement Driver}{\pageref{group__drivers04}}{}
\item \contentsline{section}{5. I2C Bus Manager}{\pageref{group__drivers05}}{}
\item \contentsline{section}{6. MCP23017 Driver}{\pageref{group__drivers06}}{}
\item \contentsline{section}{7. SNMP Agent Implementation}{\pageref{group__drivers07}}{}
\item \contentsline{section}{8. Ethernet Socket Implementation}{\pageref{group__drivers08}}{}
\end{DoxyCompactList}
\item \contentsline{section}{Main}{\pageref{group__main}}{}
\begin{DoxyCompactList}
\item \contentsline{section}{1. ENERGIS Main file -\/ Core 0}{\pageref{group__main01}}{}
\end{DoxyCompactList}
\item \contentsline{section}{Miscellaneous Utilities}{\pageref{group__misc}}{}
\begin{DoxyCompactList}
\item \contentsline{section}{1. Crash Log Module}{\pageref{group__misc1}}{}
\item \contentsline{section}{2. Helpers Module}{\pageref{group__misc2}}{}
\item \contentsline{section}{3. Power Manager Module}{\pageref{group__misc3}}{}
\item \contentsline{section}{4. RTOS Hooks Module}{\pageref{group__misc4}}{}
\end{DoxyCompactList}
\item \contentsline{section}{SNMP Agent}{\pageref{group__snmp}}{}
\begin{DoxyCompactList}
\item \contentsline{section}{1. SNMP Agent -\/ ENERGIS OID Table}{\pageref{group__snmp01}}{}
\item \contentsline{section}{2. SNMP Agent -\/ Network Configuration}{\pageref{group__snmp02}}{}
\item \contentsline{section}{3. SNMP Agent -\/ Outlet Control}{\pageref{group__snmp03}}{}
\item \contentsline{section}{4. SNMP Agent -\/ Power Monitoring}{\pageref{group__snmp04}}{}
\item \contentsline{section}{5. SNMP Agent -\/ Voltage Monitoring}{\pageref{group__snmp05}}{}
\end{DoxyCompactList}
\item \contentsline{section}{Tasks}{\pageref{group__tasks}}{}
\begin{DoxyCompactList}
\item \contentsline{section}{1. Button Task}{\pageref{group__tasks01}}{}
\item \contentsline{section}{2. Console Task}{\pageref{group__tasks02}}{}
\item \contentsline{section}{3. Health}{\pageref{group__tasks03}}{}
\item \contentsline{section}{4. Init Task -\/ RTOS Initialization}{\pageref{group__tasks04}}{}
\item \contentsline{section}{5. Logger Task}{\pageref{group__tasks05}}{}
\item \contentsline{section}{6. Meter Task}{\pageref{group__tasks06}}{}
\item \contentsline{section}{7. Network Task}{\pageref{group__tasks07}}{}
\item \contentsline{section}{8. Overcurrent Protection Module}{\pageref{group__tasks08}}{}
\item \contentsline{section}{9. Provisioning Command Handlers Header}{\pageref{group__tasks09}}{}
\item \contentsline{section}{10. Storage Task}{\pageref{group__tasks10}}{}
\begin{DoxyCompactList}
\item \contentsline{section}{1. Sensor Calibration}{\pageref{group__storage01}}{}
\item \contentsline{section}{2. Channel Labels}{\pageref{group__storage02}}{}
\item \contentsline{section}{3. Device Identity Module}{\pageref{group__storage03}}{}
\item \contentsline{section}{4. Energy Monitoring}{\pageref{group__storage04}}{}
\item \contentsline{section}{5. Event Logging}{\pageref{group__storage05}}{}
\item \contentsline{section}{6. Factory Defaults}{\pageref{group__storage06}}{}
\item \contentsline{section}{7. Network Configuration}{\pageref{group__storage07}}{}
\item \contentsline{section}{8. Storage Common}{\pageref{group__storage08}}{}
\item \contentsline{section}{9. User Output}{\pageref{group__storage09}}{}
\item \contentsline{section}{11. User Preferences}{\pageref{group__storage11}}{}
\end{DoxyCompactList}
\item \contentsline{section}{11. Switch Task}{\pageref{group__tasks11}}{}
\end{DoxyCompactList}
\item \contentsline{section}{Web-\/\+UI Handlers}{\pageref{group__webhandlers}}{}
\begin{DoxyCompactList}
\item \contentsline{section}{1. Control Handler}{\pageref{group__webui01}}{}
\item \contentsline{section}{2. HTTP Server}{\pageref{group__webui02}}{}
\item \contentsline{section}{3. Metrics Handler}{\pageref{group__webui03}}{}
\item \contentsline{section}{4. Page Content}{\pageref{group__webui04}}{}
\item \contentsline{section}{6. Preset Handler}{\pageref{group__webui6}}{}
\item \contentsline{section}{5. Settings Handler}{\pageref{group__webui05}}{}
\item \contentsline{section}{6. Status Handler}{\pageref{group__webui06}}{}
\end{DoxyCompactList}
\end{DoxyCompactList}
