DvidMakesThings/HW_10-In-Rack_PDU/docs/Tests/report_tc_network_pcap/tc_network_pcap_report.html

# ENERGIS Test Report

Overall: PASS Started: 2025-10-05 22:53:24 Session ID: dc284baf

Passed: 8

Failed: 0

Unknown: 0

Total: 8

### Environment

Test Session ID

dc284baf

Hostname

DPC

Os

Windows 11 (10.0.26100)

Python

3.13.7 (tags/v3.13.7:bcee1c3, Aug 14 2025, 14:15:11) [MSC v.1944 64 bit (AMD64)]

Generated_at

2025-10-05 22:54:02

Log_file

G:\_GitHub\HW_10-In-Rack_PDU\tests\tc_network_pcap\report_tc_network_pcap\tc_network_pcap_results.log

### Steps

PRE-STEP 1 Reboot device via UART

PASS

Started | Finished
2025-10-05 22:53:24 | 2025-10-05 22:53:35

Step Log

DETAIL

#### Log

[2025-10-05 22:53:24] [PRE-STEP 1] Reboot device via UART
[2025-10-05 22:53:24] [INFO] [SERIAL] send_command() called
[2025-10-05 22:53:24] [INFO] [SERIAL]   port=COM11, command='REBOOT', baudrate=115200, timeout=2.0s
[2025-10-05 22:53:24] [INFO] [SERIAL] Opening connection to port=COM11
[2025-10-05 22:53:24] [INFO] [SERIAL]   Configuration: baudrate=115200, timeout=2.0s, write_timeout=2.0s
[2025-10-05 22:53:24] [INFO] [SERIAL]   Flow control: xonxoff=False, rtscts=False, dsrdtr=False
[2025-10-05 22:53:24] [INFO] [SERIAL] Port COM11 opened successfully
[2025-10-05 22:53:24] [INFO] [SERIAL] Stabilizing connection (100ms delay)...
[2025-10-05 22:53:24] [INFO] [SERIAL] Resetting input and output buffers
[2025-10-05 22:53:24] [INFO] [SERIAL] Connection ready: port=COM11, baudrate=115200, timeout=2.0s
[2025-10-05 22:53:24] [INFO] [SERIAL TX] Sending command: 'REBOOT'
[2025-10-05 22:53:24] [INFO] [SERIAL TX] Payload length: 8 bytes (including CR+LF)
[2025-10-05 22:53:24] [INFO] [SERIAL TX] Hex dump:
[2025-10-05 22:53:24] [INFO]   0000  52 45 42 4F 4F 54 0D 0A                           |REBOOT..|
[2025-10-05 22:53:24] [INFO] [SERIAL TX] Wrote 8 bytes to port
[2025-10-05 22:53:24] [INFO] [SERIAL TX] Waiting 50ms for device processing...
[2025-10-05 22:53:24] [INFO] [SERIAL RX] Starting to read response (timeout=2.0s)
[2025-10-05 22:53:25] [INFO] [SERIAL RX] Chunk #1: received 32 bytes (elapsed: 0.377s, total: 32 bytes)
[2025-10-05 22:53:25] [ERROR] [SERIAL ERROR] Exception during send_command:
[2025-10-05 22:53:25] [ERROR] [SERIAL ERROR]   Type: SerialException
[2025-10-05 22:53:25] [ERROR] [SERIAL ERROR]   Message: ClearCommError failed (PermissionError(13, 'The device does not recognize the command.', None, 22))
[2025-10-05 22:53:25] [ERROR] [SERIAL ERROR]   Port: COM11, Command: 'REBOOT'
[2025-10-05 22:53:25] [INFO] [SERIAL] Closing port COM11
[2025-10-05 22:53:25] [INFO] [SERIAL] Port COM11 closed successfully
[2025-10-05 22:53:25] [INFO] [SERIAL] wait_for_reboot_and_ready() called
[2025-10-05 22:53:25] [INFO] [SERIAL]   port=COM11, ready_token='SYSTEM READY', baudrate=115200, timeout=15.0s
[2025-10-05 22:53:25] [INFO] [SERIAL] Waiting 200ms for device to start rebooting...
[2025-10-05 22:53:25] [INFO] [SERIAL] Connection attempt #1 (remaining timeout: 14.8s)
[2025-10-05 22:53:25] [INFO] [SERIAL] Connection attempt #1 failed: SerialException: could not open port 'COM11': FileNotFoundError(2, 'The system cannot find the file specified.', None, 2)
[2025-10-05 22:53:25] [INFO] [SERIAL] Waiting 200ms before next attempt...
[2025-10-05 22:53:25] [INFO] [SERIAL] Connection attempt #2 (remaining timeout: 14.6s)
[2025-10-05 22:53:25] [INFO] [SERIAL] Connection attempt #2 failed: SerialException: could not open port 'COM11': FileNotFoundError(2, 'The system cannot find the file specified.', None, 2)
[2025-10-05 22:53:25] [INFO] [SERIAL] Waiting 200ms before next attempt...
[2025-10-05 22:53:25] [INFO] [SERIAL] Connection attempt #3 (remaining timeout: 14.4s)
[2025-10-05 22:53:25] [INFO] [SERIAL] Connection attempt #3 failed: SerialException: could not open port 'COM11': FileNotFoundError(2, 'The system cannot find the file specified.', None, 2)
[2025-10-05 22:53:25] [INFO] [SERIAL] Waiting 200ms before next attempt...
[2025-10-05 22:53:25] [INFO] [SERIAL] Connection attempt #4 (remaining timeout: 14.2s)
[2025-10-05 22:53:25] [INFO] [SERIAL] Connection attempt #4 failed: SerialException: could not open port 'COM11': FileNotFoundError(2, 'The system cannot find the file specified.', None, 2)
[2025-10-05 22:53:25] [INFO] [SERIAL] Waiting 200ms before next attempt...
[2025-10-05 22:53:26] [INFO] [SERIAL] Connection attempt #5 (remaining timeout: 14.0s)
[2025-10-05 22:53:26] [INFO] [SERIAL] Connection attempt #5 failed: SerialException: could not open port 'COM11': FileNotFoundError(2, 'The system cannot find the file specified.', None, 2)
[2025-10-05 22:53:26] [INFO] [SERIAL] Waiting 200ms before next attempt...
[2025-10-05 22:53:26] [INFO] [SERIAL] Connection attempt #6 (remaining timeout: 13.8s)
[2025-10-05 22:53:26] [INFO] [SERIAL] Connection attempt #6 failed: SerialException: could not open port 'COM11': FileNotFoundError(2, 'The system cannot find the file specified.', None, 2)
[2025-10-05 22:53:26] [INFO] [SERIAL] Waiting 200ms before next attempt...
[2025-10-05 22:53:26] [INFO] [SERIAL] Connection attempt #7 (remaining timeout: 13.6s)
[2025-10-05 22:53:26] [INFO] [SERIAL] Connected to port COM11 on attempt #7
[2025-10-05 22:53:26] [INFO] [SERIAL RX] Monitoring for ready token: 'SYSTEM READY'
[2025-10-05 22:53:29] [INFO] [SERIAL RX] Chunk #1: 393 bytes
[2025-10-05 22:53:29] [INFO] [SERIAL RX] Content: [INFO] Core 0 initializing...<CR><LF>
	[ECHO] Device Serial : SN-369366060325<CR><LF>
	[ECHO] Firmware Ver  : 1.0.0<CR><LF>
	[ECHO] Core voltage  : 1.15 V (vsel = 1)<CR><LF>
	[ECHO] Clock Sources :<CR><LF>
	[ECHO] 	SYS: 200000000 Hz (200 MHz)<CR><LF>
	[ECHO] 	USB: 48000000 Hz (48 MHz)<CR><LF>
	[ECHO] 	PER: 48000000 Hz (48 MHz)<CR><LF>
	[ECHO] 	ADC: 48000000 Hz (48 MHz)<CR><LF>
[INFO] ADC initializing<CR><LF>
VREG register: 0x000010D1<CR><LF>
[INFO] I2C scanning...<CR><LF>

[2025-10-05 22:53:29] [INFO] [SERIAL RX] Chunk #2: 64 bytes
[2025-10-05 22:53:29] [INFO] [SERIAL RX] Content: [INFO] EEPROM initializing...<CR><LF>
[INFO] MCP23017 initializing...<CR><LF>

[2025-10-05 22:53:31] [INFO] [SERIAL RX] Chunk #3: 162 bytes
[2025-10-05 22:53:31] [INFO] [SERIAL RX] Content: [INFO] Headless mode, skipping display initialization<CR><LF>
[INFO] Initializing HLW8032...<CR><LF>
[INFO] Initializing buttons...<CR><LF>
[INFO] Loaded network config from EEPROM.<CR><LF>

[2025-10-05 22:53:33] [INFO] [SERIAL RX] Chunk #4: 456 bytes
[2025-10-05 22:53:33] [INFO] [SERIAL RX] Content: [INFO] W5500 version: 0x04<CR><LF>
[INFO] W5500 PHY link is up<CR><LF>
	[ECHO] =============================================<CR><LF>
	[ECHO]  W5500 network configuration : static<CR><LF>
	[ECHO]  MAC         : 00:08:DC:BE:EF:91<CR><LF>
	[ECHO]  IP          : 192.168.0.11<CR><LF>
	[ECHO]  Subnet Mask : 255.255.255.0<CR><LF>
	[ECHO]  Gateway     : 192.168.0.1<CR><LF>
	[ECHO]  DNS         : 8.8.8.8<CR><LF>
	[ECHO] =============================================<CR><LF>
<CR><LF>
SYSTEM READY<CR><LF>
[INFO] - SNMP : Start SNMP Agent Daemon<CR><LF>

[2025-10-05 22:53:33] [INFO] [SERIAL] Ready token 'SYSTEM READY' detected!
[2025-10-05 22:53:33] [INFO] [SERIAL RX] Total response: 1075 bytes in 4 chunks
[2025-10-05 22:53:33] [INFO] [SERIAL RX] Elapsed time: 8.299s
[2025-10-05 22:53:33] [INFO] [SERIAL RX] Full response:
[2025-10-05 22:53:33] [INFO] [INFO] Core 0 initializing...\r\n
	[ECHO] Device Serial : SN-369366060325\r\n
	[ECHO] Firmware Ver  : 1.0.0\r\n
	[ECHO] Core voltage  : 1.15 V (vsel = 1)\r\n
	[ECHO] Clock Sources :\r\n
	[ECHO] 	SYS: 200000000 Hz (200 MHz)\r\n
	[ECHO] 	USB: 48000000 Hz (48 MHz)\r\n
	[ECHO] 	PER: 48000000 Hz (48 MHz)\r\n
	[ECHO] 	ADC: 48000000 Hz (48 MHz)\r\n
[INFO] ADC initializing\r\n
VREG register: 0x000010D1\r\n
[INFO] I2C scanning...\r\n
[INFO] EEPROM initializing...\r\n
[INFO] MCP23017 initializing...\r\n
[INFO] Headless mode, skipping display initialization\r\n
[INFO] Initializing HLW8032...\r\n
[INFO] Initializing buttons...\r\n
[INFO] Loaded network config from EEPROM.\r\n
[INFO] W5500 version: 0x04\r\n
[INFO] W5500 PHY link is up\r\n
	[ECHO] =============================================\r\n
	[ECHO]  W5500 network configuration : static\r\n
	[ECHO]  MAC         : 00:08:DC:BE:EF:91\r\n
	[ECHO]  IP          : 192.168.0.11\r\n
	[ECHO]  Subnet Mask : 255.255.255.0\r\n
	[ECHO]  Gateway     : 192.168.0.1\r\n
	[ECHO]  DNS         : 8.8.8.8\r\n
	[ECHO] =============================================\r\n
\r\n
SYSTEM READY\r\n
[INFO] - SNMP : Start SNMP Agent Daemon\r\n

[2025-10-05 22:53:33] [INFO] [SERIAL RX] Hex dump:
[2025-10-05 22:53:33] [INFO]   0000  5B 49 4E 46 4F 5D 20 43 6F 72 65 20 30 20 69 6E   |[INFO] Core 0 in|
  0010  69 74 69 61 6C 69 7A 69 6E 67 2E 2E 2E 0D 0A 09   |itializing......|
  0020  5B 45 43 48 4F 5D 20 44 65 76 69 63 65 20 53 65   |[ECHO] Device Se|
  0030  72 69 61 6C 20 3A 20 53 4E 2D 33 36 39 33 36 36   |rial : SN-369366|
  0040  30 36 30 33 32 35 0D 0A 09 5B 45 43 48 4F 5D 20   |060325...[ECHO] |
  0050  46 69 72 6D 77 61 72 65 20 56 65 72 20 20 3A 20   |Firmware Ver  : |
  0060  31 2E 30 2E 30 0D 0A 09 5B 45 43 48 4F 5D 20 43   |1.0.0...[ECHO] C|
  0070  6F 72 65 20 76 6F 6C 74 61 67 65 20 20 3A 20 31   |ore voltage  : 1|
  0080  2E 31 35 20 56 20 28 76 73 65 6C 20 3D 20 31 29   |.15 V (vsel = 1)|
  0090  0D 0A 09 5B 45 43 48 4F 5D 20 43 6C 6F 63 6B 20   |...[ECHO] Clock |
  00A0  53 6F 75 72 63 65 73 20 3A 0D 0A 09 5B 45 43 48   |Sources :...[ECH|
  00B0  4F 5D 20 09 53 59 53 3A 20 32 30 30 30 30 30 30   |O] .SYS: 2000000|
  00C0  30 30 20 48 7A 20 28 32 30 30 20 4D 48 7A 29 0D   |00 Hz (200 MHz).|
  00D0  0A 09 5B 45 43 48 4F 5D 20 09 55 53 42 3A 20 34   |..[ECHO] .USB: 4|
  00E0  38 30 30 30 30 30 30 20 48 7A 20 28 34 38 20 4D   |8000000 Hz (48 M|
  00F0  48 7A 29 0D 0A 09 5B 45 43 48 4F 5D 20 09 50 45   |Hz)...[ECHO] .PE|
  0100  52 3A 20 34 38 30 30 30 30 30 30 20 48 7A 20 28   |R: 48000000 Hz (|
  0110  34 38 20 4D 48 7A 29 0D 0A 09 5B 45 43 48 4F 5D   |48 MHz)...[ECHO]|
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
[2025-10-05 22:53:35] [INFO] [PCAP-CAPTURE] _dumpcap_list_interfaces() called
[2025-10-05 22:53:35] [INFO] [PCAP-CAPTURE]   dumpcap_exe=C:\Program Files\Wireshark\dumpcap.exe
[2025-10-05 22:53:35] [INFO] [PCAP-CAPTURE]   cwd=G:\_GitHub\HW_10-In-Rack_PDU\tests\tc_network_pcap
[2025-10-05 22:53:35] [INFO] [PCAP-CAPTURE] dumpcap -D returned 9 interfaces
[2025-10-05 22:53:35] [INFO] [PCAP-CAPTURE]   1. \Device\NPF_{CED0C9EE-D3D8-4AF6-A642-236D14517B9D} (Bluetooth Network Connection)
[2025-10-05 22:53:35] [INFO] [PCAP-CAPTURE]   2. \Device\NPF_{50788C95-4726-4446-BEF9-1BDAD79385DF} (Wi-Fi)
[2025-10-05 22:53:35] [INFO] [PCAP-CAPTURE]   3. \Device\NPF_{F7EF8ACA-533A-4582-A44C-AA6FD3B30B80} (Local Area Connection* 10)
[2025-10-05 22:53:35] [INFO] [PCAP-CAPTURE]   4. \Device\NPF_{D62A827E-C7BA-46D2-ACE5-772C43BD80F7} (Local Area Connection* 9)
[2025-10-05 22:53:35] [INFO] [PCAP-CAPTURE]   5. \Device\NPF_{FCE23F70-F218-4EDE-B551-6FCAD6766D9B} (Ethernet 4)
[2025-10-05 22:53:35] [INFO] [PCAP-CAPTURE]   6. \Device\NPF_{1342939B-DAE3-4B54-A305-87408E83C962} (Ethernet 2)
[2025-10-05 22:53:35] [INFO] [PCAP-CAPTURE]   7. \Device\NPF_{8FBED501-71F5-4B70-96B8-C2464A93CE8E} (Ethernet)
[2025-10-05 22:53:35] [INFO] [PCAP-CAPTURE]   8. \Device\NPF_{7CB6D269-0786-7E57-C13F-6CDFFF02FB02} (Eddie)
[2025-10-05 22:53:35] [INFO] [PCAP-CAPTURE]   9. \Device\NPF_Loopback (Adapter for loopback traffic capture)
[2025-10-05 22:53:35] [INFO] [PCAP-CAPTURE] Trying exact match on description or device...
[2025-10-05 22:53:35] [INFO] [PCAP-CAPTURE] Exact match found: idx=7, dev=\Device\NPF_{8FBED501-71F5-4B70-96B8-C2464A93CE8E}, desc=Ethernet
[2025-10-05 22:53:35] [INFO] [PCAP-CAPTURE] _dumpcap_resolve_interface() called
[2025-10-05 22:53:35] [INFO] [PCAP-CAPTURE]   requested=Ethernet
[2025-10-05 22:53:35] [INFO] [PCAP-CAPTURE] _dumpcap_list_interfaces() called
[2025-10-05 22:53:35] [INFO] [PCAP-CAPTURE]   dumpcap_exe=C:\Program Files\Wireshark\dumpcap.exe
[2025-10-05 22:53:35] [INFO] [PCAP-CAPTURE]   cwd=G:\_GitHub\HW_10-In-Rack_PDU\tests\tc_network_pcap
[2025-10-05 22:53:35] [INFO] [PCAP-CAPTURE] dumpcap -D returned 9 interfaces
[2025-10-05 22:53:35] [INFO] [PCAP-CAPTURE]   1. \Device\NPF_{CED0C9EE-D3D8-4AF6-A642-236D14517B9D} (Bluetooth Network Connection)
[2025-10-05 22:53:35] [INFO] [PCAP-CAPTURE]   2. \Device\NPF_{50788C95-4726-4446-BEF9-1BDAD79385DF} (Wi-Fi)
[2025-10-05 22:53:35] [INFO] [PCAP-CAPTURE]   3. \Device\NPF_{F7EF8ACA-533A-4582-A44C-AA6FD3B30B80} (Local Area Connection* 10)
[2025-10-05 22:53:35] [INFO] [PCAP-CAPTURE]   4. \Device\NPF_{D62A827E-C7BA-46D2-ACE5-772C43BD80F7} (Local Area Connection* 9)
[2025-10-05 22:53:35] [INFO] [PCAP-CAPTURE]   5. \Device\NPF_{FCE23F70-F218-4EDE-B551-6FCAD6766D9B} (Ethernet 4)
[2025-10-05 22:53:35] [INFO] [PCAP-CAPTURE]   6. \Device\NPF_{1342939B-DAE3-4B54-A305-87408E83C962} (Ethernet 2)
[2025-10-05 22:53:35] [INFO] [PCAP-CAPTURE]   7. \Device\NPF_{8FBED501-71F5-4B70-96B8-C2464A93CE8E} (Ethernet)
[2025-10-05 22:53:35] [INFO] [PCAP-CAPTURE]   8. \Device\NPF_{7CB6D269-0786-7E57-C13F-6CDFFF02FB02} (Eddie)
[2025-10-05 22:53:35] [INFO] [PCAP-CAPTURE]   9. \Device\NPF_Loopback (Adapter for loopback traffic capture)
[2025-10-05 22:53:35] [INFO] [PCAP-CAPTURE] Trying exact match on description or device...
[2025-10-05 22:53:35] [INFO] [PCAP-CAPTURE] Exact match found: idx=7, dev=\Device\NPF_{8FBED501-71F5-4B70-96B8-C2464A93CE8E}, desc=Ethernet

STEP 1 Wait for device to boot fully

PASS

Started | Finished
2025-10-05 22:53:35 | 2025-10-05 22:53:37

Step Log

DETAIL

#### Log

[2025-10-05 22:53:35] [STEP 1] Wait for device to boot fully
[2025-10-05 22:53:35] [INFO] Starting NOP wait for 2000ms
[2025-10-05 22:53:36] [INFO] NOP waiting... 1.0s elapsed
[2025-10-05 22:53:37] [INFO] NOP wait complete. Actual duration: 2000.24ms
[2025-10-05 22:53:37] [PASS] STEP 1 completed successfully

STEP 2 Start capturing settings page

PASS

Started | Finished
2025-10-05 22:53:37 | 2025-10-05 22:53:45

#### Substeps

STEP 2.1 Capture PCAP

UNKNOWN

Started | Finished
2025-10-05 22:53:37 | 2025-10-05 22:53:38

#### Log

[2025-10-05 22:53:37] [STEP 2.1] Capture PCAP
[2025-10-05 22:53:37] [INFO] [PCAP-CAPTURE] tag=CH3EAQ dumpcap -D:
1. \Device\NPF_{CED0C9EE-D3D8-4AF6-A642-236D14517B9D} (Bluetooth Network Connection)
2. \Device\NPF_{50788C95-4726-4446-BEF9-1BDAD79385DF} (Wi-Fi)
3. \Device\NPF_{F7EF8ACA-533A-4582-A44C-AA6FD3B30B80} (Local Area Connection* 10)
4. \Device\NPF_{D62A827E-C7BA-46D2-ACE5-772C43BD80F7} (Local Area Connection* 9)
5. \Device\NPF_{FCE23F70-F218-4EDE-B551-6FCAD6766D9B} (Ethernet 4)
6. \Device\NPF_{1342939B-DAE3-4B54-A305-87408E83C962} (Ethernet 2)
7. \Device\NPF_{8FBED501-71F5-4B70-96B8-C2464A93CE8E} (Ethernet)
8. \Device\NPF_{7CB6D269-0786-7E57-C13F-6CDFFF02FB02} (Eddie)
9. \Device\NPF_Loopback (Adapter for loopback traffic capture)
[2025-10-05 22:53:37] [INFO] [PCAP-CAPTURE] tag=CH3EAQ resolved interface 'Ethernet' -> '7'
[2025-10-05 22:53:37] [INFO] [PCAP-CAPTURE] tag=CH3EAQ validating BPF filter: host 192.168.0.11
[2025-10-05 22:53:37] [INFO] [PCAP-CAPTURE] tag=CH3EAQ tool=dumpcap exe=C:\Program Files\Wireshark\dumpcap.exe
[2025-10-05 22:53:37] [INFO] [PCAP-CAPTURE] tag=CH3EAQ interface='Ethernet' promiscuous=False snaplen=1518 duration_s=8 packet_count=None file_format=pcap ring_files=None ring_megabytes=None
[2025-10-05 22:53:37] [INFO] [PCAP-CAPTURE] tag=CH3EAQ bpf='host 192.168.0.11'
[2025-10-05 22:53:37] [INFO] [PCAP-CAPTURE] tag=CH3EAQ output_path=G:\_GitHub\HW_10-In-Rack_PDU\tests\tc_network_pcap\report_tc_network_pcap\capture_settings.pcap
[2025-10-05 22:53:37] [INFO] [PCAP-CAPTURE] tag=CH3EAQ cwd=G:\_GitHub\HW_10-In-Rack_PDU\tests\tc_network_pcap
[2025-10-05 22:53:37] [INFO] [PCAP-CAPTURE] tag=CH3EAQ argv="C:\Program Files\Wireshark\dumpcap.exe" -i 7 -F pcap -w G:\_GitHub\HW_10-In-Rack_PDU\tests\tc_network_pcap\report_tc_network_pcap\capture_settings.pcap -p -s 1518 -a duration:8 -f "host 192.168.0.11"
[2025-10-05 22:53:37] [INFO] [PCAP-CAPTURE] tag=CH3EAQ waiting for capture tool to initialize...
[2025-10-05 22:53:37] [INFO] [PCAP-CAPTURE] tag=CH3EAQ output file created, dumpcap is ready

STEP 2.2 Access the settings page

PASS

Started | Finished
2025-10-05 22:53:38 | 2025-10-05 22:53:45

#### Log

[2025-10-05 22:53:38] [STEP 2.2] Access the settings page
[2025-10-05 22:53:38] [INFO] [ETHERNET] _url() called: base=http://192.168.0.11:80, path=/settings.html
[2025-10-05 22:53:38] [INFO] [ETHERNET] _url() result: http://192.168.0.11:80/settings.html
[2025-10-05 22:53:38] [INFO] [ETHERNET] _http_request() called
[2025-10-05 22:53:38] [INFO] [ETHERNET]   method=GET
[2025-10-05 22:53:38] [INFO] [ETHERNET]   url=http://192.168.0.11:80/settings.html
[2025-10-05 22:53:38] [INFO] [ETHERNET]   timeout=5.0s
[2025-10-05 22:53:38] [INFO] [ETHERNET]   headers=None
[2025-10-05 22:53:38] [INFO] [ETHERNET]   data_bytes=0 bytes
[2025-10-05 22:53:38] [INFO] [HTTP GET] http://192.168.0.11:80/settings.html timeout=5.0s headers=none data_len=0
[2025-10-05 22:53:38] [INFO] [ETHERNET] _http_request() opening connection...
[2025-10-05 22:53:38] [INFO] [ETHERNET] _http_request() response status: 200
[2025-10-05 22:53:38] [INFO] [ETHERNET] _http_request() response headers: {'Content-Type': 'text/html', 'Content-Length': '3287'}
[2025-10-05 22:53:38] [INFO] [ETHERNET] _http_request() received 3287 bytes
[2025-10-05 22:53:38] [INFO] [ETHERNET] _http_request() success on attempt 1
[2025-10-05 22:53:38] [INFO] [ETHERNET] _dump_http() called
[2025-10-05 22:53:38] [INFO] [ETHERNET]   base_url=http://192.168.0.11:80
[2025-10-05 22:53:38] [INFO] [ETHERNET]   path=/settings.html
[2025-10-05 22:53:38] [INFO] [ETHERNET]   method=GET
[2025-10-05 22:53:38] [INFO] [ETHERNET]   status=200
[2025-10-05 22:53:38] [INFO] [ETHERNET]   headers=2 entries
[2025-10-05 22:53:38] [INFO] [ETHERNET]   body=3287 bytes
[2025-10-05 22:53:38] [INFO] [ETHERNET]   dump_subdir=None
[2025-10-05 22:53:38] [INFO] [ETHERNET] _dump_http() skipped (no dump_dir available)
[2025-10-05 22:53:38] [PASS] STEP 2.2 completed successfully
[2025-10-05 22:53:45] [INFO] [PCAP-CAPTURE] tag=CH3EAQ exit_code=0 elapsed_s=8.141 timed_stop=False
[2025-10-05 22:53:45] [INFO] [PCAP-CAPTURE STDERR]
Capturing on 'Ethernet'
File: G:\_GitHub\HW_10-In-Rack_PDU\tests\tc_network_pcap\report_tc_network_pcap\capture_settings.pcap

Packets: 1 
Packets: 13 
Packets captured: 13
Packets received/dropped on interface 'Ethernet': 13/0 (pcap:0/dumpcap:0/flushed:0/ps_ifdrop:0) (100.0%)
[2025-10-05 22:53:45] [INFO] [PCAP-CAPTURE] tag=CH3EAQ file size after capture: 4414 bytes
[2025-10-05 22:53:45] [INFO] [PCAP-CAPTURE] tag=CH3EAQ output_size=4414 bytes
[2025-10-05 22:53:45] [PASS] STEP 2.1 completed successfully

STEP 3 Analyze captured settings page

PASS

Started | Finished
2025-10-05 22:53:45 | 2025-10-05 22:53:50

#### Substeps

STEP 3.1 Validate IP address

PASS

Started | Finished
2025-10-05 22:53:45 | 2025-10-05 22:53:45

#### Log

[2025-10-05 22:53:45] [STEP 3.1] Validate IP address
[2025-10-05 22:53:45] [INFO] [PCAP-EXPECT] checkFrames start path=G:\_GitHub\HW_10-In-Rack_PDU\tests\tc_network_pcap\report_tc_network_pcap\capture_settings.pcap filter=http.response and ip.addr==192.168.0.11 ordered=False expect_count=None n_expected=1
[2025-10-05 22:53:45] [INFO] [PCAP-READ] read_PCAPFrames() execute called
[2025-10-05 22:53:45] [INFO] [PCAP-READ]   pcap_path=G:\_GitHub\HW_10-In-Rack_PDU\tests\tc_network_pcap\report_tc_network_pcap\capture_settings.pcap
[2025-10-05 22:53:45] [INFO] [PCAP-READ]   display_filter=http.response and ip.addr==192.168.0.11
[2025-10-05 22:53:45] [INFO] [PCAP-READ] File exists, size=4414 bytes
[2025-10-05 22:53:45] [INFO] [PCAP-READ] Running tshark to extract fields...
[2025-10-05 22:53:45] [INFO] [PCAP-CHECK] tshark fields start filter=http.response and ip.addr==192.168.0.11
[2025-10-05 22:53:45] [TSHARK-FIELDS] cmd=tshark -r G:\_GitHub\HW_10-In-Rack_PDU\tests\tc_network_pcap\report_tc_network_pcap\capture_settings.pcap -o tcp.desegment_tcp_streams:TRUE -o http.desegment_body:TRUE -T fields -E header=n -E separator=	 -E occurrence=f -e frame.number -e frame.len -e frame.time_epoch -e eth.src -e eth.dst -e vlan.id -e vlan.priority -e http.file_data -e tcp.reassembled.data -e tcp.payload -e data.data -Y "http.response and ip.addr==192.168.0.11"
[2025-10-05 22:53:45] [TSHARK-FIELDS] rc=0
[2025-10-05 22:53:45] [TSHARK-FIELDS OUT]
9	421	1759697618.167510000	00:08:dc:be:ef:91	10:ff:e0:03:49:ac			3c21444f43545950452068746d6c3e3c68746d6c3e3c686561643e3c6d65746120636861727365743d225554462d38223e3c6d657461206e616d653d2276696577706f72742220636f6e74656e743d2277696474683d6465766963652d77696474682c696e697469616c2d7363616c653d312e30223e3c7469746c653e454e455247495320504455202d2053657474696e67733c2f7469746c653e3c7374796c653e2a7b6d617267696e3a303b70616464696e673a303b626f782d73697a696e673a626f726465722d626f783b666f6e742d66616d696c793a73616e732d73657269667d626f64797b6261636b67726f756e643a233161316432333b636f6c6f723a236534653465347d617b636f6c6f723a236161613b746578742d6465636f726174696f6e3a6e6f6e657d613a686f7665727b636f6c6f723a236666667d2e746f706261727b77696474683a3130303b6865696768743a353070783b6261636b67726f756e643a233234323733313b646973706c61793a666c65783b616c69676e2d6974656d733a63656e7465723b70616464696e673a3020323070787d2e746f706261722068317b666f6e742d73697a653a312e3272656d3b636f6c6f723a236666667d2e636f6e7461696e65727b646973706c61793a666c65783b77696474683a3130303b6865696768743a63616c63283130307668202d2035307078297d2e736964656261727b77696474683a32323070783b6261636b67726f756e643a233265333233633b70616464696e673a3230707820307d2e7369646562617220756c7b6c6973742d7374796c653a6e6f6e657d2e7369646562617220756c206c697b70616464696e673a3130707820323070787d2e7369646562617220756c206c693a686f7665727b6261636b67726f756e643a233362343034647d2e6d61696e2d636f6e74656e747b666c65783a313b70616464696e673a323070783b6f766572666c6f772d793a61757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
[2025-10-05 22:53:45] [PASS] STEP 3.1 completed successfully

STEP 3.2 Validate Gateway address

PASS

Started | Finished
2025-10-05 22:53:45 | 2025-10-05 22:53:45

#### Log

[2025-10-05 22:53:45] [STEP 3.2] Validate Gateway address
[2025-10-05 22:53:45] [INFO] [PCAP-EXPECT] checkFrames start path=G:\_GitHub\HW_10-In-Rack_PDU\tests\tc_network_pcap\report_tc_network_pcap\capture_settings.pcap filter=http.response and ip.addr==192.168.0.11 ordered=False expect_count=None n_expected=1
[2025-10-05 22:53:45] [INFO] [PCAP-READ] read_PCAPFrames() execute called
[2025-10-05 22:53:45] [INFO] [PCAP-READ]   pcap_path=G:\_GitHub\HW_10-In-Rack_PDU\tests\tc_network_pcap\report_tc_network_pcap\capture_settings.pcap
[2025-10-05 22:53:45] [INFO] [PCAP-READ]   display_filter=http.response and ip.addr==192.168.0.11
[2025-10-05 22:53:45] [INFO] [PCAP-READ] File exists, size=4414 bytes
[2025-10-05 22:53:45] [INFO] [PCAP-READ] Running tshark to extract fields...
[2025-10-05 22:53:45] [INFO] [PCAP-CHECK] tshark fields start filter=http.response and ip.addr==192.168.0.11
[2025-10-05 22:53:45] [TSHARK-FIELDS] cmd=tshark -r G:\_GitHub\HW_10-In-Rack_PDU\tests\tc_network_pcap\report_tc_network_pcap\capture_settings.pcap -o tcp.desegment_tcp_streams:TRUE -o http.desegment_body:TRUE -T fields -E header=n -E separator=	 -E occurrence=f -e frame.number -e frame.len -e frame.time_epoch -e eth.src -e eth.dst -e vlan.id -e vlan.priority -e http.file_data -e tcp.reassembled.data -e tcp.payload -e data.data -Y "http.response and ip.addr==192.168.0.11"
[2025-10-05 22:53:45] [TSHARK-FIELDS] rc=0
[2025-10-05 22:53:45] [TSHARK-FIELDS OUT]
9	421	1759697618.167510000	00:08:dc:be:ef:91	10:ff:e0:03:49:ac			3c21444f43545950452068746d6c3e3c68746d6c3e3c686561643e3c6d65746120636861727365743d225554462d38223e3c6d657461206e616d653d2276696577706f72742220636f6e74656e743d2277696474683d6465766963652d77696474682c696e697469616c2d7363616c653d312e30223e3c7469746c653e454e455247495320504455202d2053657474696e67733c2f7469746c653e3c7374796c653e2a7b6d617267696e3a303b70616464696e673a303b626f782d73697a696e673a626f726465722d626f783b666f6e742d66616d696c793a73616e732d73657269667d626f64797b6261636b67726f756e643a233161316432333b636f6c6f723a236534653465347d617b636f6c6f723a236161613b746578742d6465636f726174696f6e3a6e6f6e657d613a686f7665727b636f6c6f723a236666667d2e746f706261727b77696474683a3130303b6865696768743a353070783b6261636b67726f756e643a233234323733313b646973706c61793a666c65783b616c69676e2d6974656d733a63656e7465723b70616464696e673a3020323070787d2e746f706261722068317b666f6e742d73697a653a312e3272656d3b636f6c6f723a236666667d2e636f6e7461696e65727b646973706c61793a666c65783b77696474683a3130303b6865696768743a63616c63283130307668202d2035307078297d2e736964656261727b77696474683a32323070783b6261636b67726f756e643a233265333233633b70616464696e673a3230707820307d2e7369646562617220756c7b6c6973742d7374796c653a6e6f6e657d2e7369646562617220756c206c697b70616464696e673a3130707820323070787d2e7369646562617220756c206c693a686f7665727b6261636b67726f756e643a233362343034647d2e6d61696e2d636f6e74656e747b666c65783a313b70616464696e673a323070783b6f766572666c6f772d793a61757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
[2025-10-05 22:53:45] [PASS] STEP 3.2 completed successfully

STEP 3.3 Validate Subnet mask

PASS

Started | Finished
2025-10-05 22:53:45 | 2025-10-05 22:53:46

#### Log

[2025-10-05 22:53:45] [STEP 3.3] Validate Subnet mask
[2025-10-05 22:53:45] [INFO] [PCAP-EXPECT] checkFrames start path=G:\_GitHub\HW_10-In-Rack_PDU\tests\tc_network_pcap\report_tc_network_pcap\capture_settings.pcap filter=http.response and ip.addr==192.168.0.11 ordered=False expect_count=None n_expected=1
[2025-10-05 22:53:45] [INFO] [PCAP-READ] read_PCAPFrames() execute called
[2025-10-05 22:53:45] [INFO] [PCAP-READ]   pcap_path=G:\_GitHub\HW_10-In-Rack_PDU\tests\tc_network_pcap\report_tc_network_pcap\capture_settings.pcap
[2025-10-05 22:53:45] [INFO] [PCAP-READ]   display_filter=http.response and ip.addr==192.168.0.11
[2025-10-05 22:53:45] [INFO] [PCAP-READ] File exists, size=4414 bytes
[2025-10-05 22:53:45] [INFO] [PCAP-READ] Running tshark to extract fields...
[2025-10-05 22:53:45] [INFO] [PCAP-CHECK] tshark fields start filter=http.response and ip.addr==192.168.0.11
[2025-10-05 22:53:46] [TSHARK-FIELDS] cmd=tshark -r G:\_GitHub\HW_10-In-Rack_PDU\tests\tc_network_pcap\report_tc_network_pcap\capture_settings.pcap -o tcp.desegment_tcp_streams:TRUE -o http.desegment_body:TRUE -T fields -E header=n -E separator=	 -E occurrence=f -e frame.number -e frame.len -e frame.time_epoch -e eth.src -e eth.dst -e vlan.id -e vlan.priority -e http.file_data -e tcp.reassembled.data -e tcp.payload -e data.data -Y "http.response and ip.addr==192.168.0.11"
[2025-10-05 22:53:46] [TSHARK-FIELDS] rc=0
[2025-10-05 22:53:46] [TSHARK-FIELDS OUT]
9	421	1759697618.167510000	00:08:dc:be:ef:91	10:ff:e0:03:49:ac			3c21444f43545950452068746d6c3e3c68746d6c3e3c686561643e3c6d65746120636861727365743d225554462d38223e3c6d657461206e616d653d2276696577706f72742220636f6e74656e743d2277696474683d6465766963652d77696474682c696e697469616c2d7363616c653d312e30223e3c7469746c653e454e455247495320504455202d2053657474696e67733c2f7469746c653e3c7374796c653e2a7b6d617267696e3a303b70616464696e673a303b626f782d73697a696e673a626f726465722d626f783b666f6e742d66616d696c793a73616e732d73657269667d626f64797b6261636b67726f756e643a233161316432333b636f6c6f723a236534653465347d617b636f6c6f723a236161613b746578742d6465636f726174696f6e3a6e6f6e657d613a686f7665727b636f6c6f723a236666667d2e746f706261727b77696474683a3130303b6865696768743a353070783b6261636b67726f756e643a233234323733313b646973706c61793a666c65783b616c69676e2d6974656d733a63656e7465723b70616464696e673a3020323070787d2e746f706261722068317b666f6e742d73697a653a312e3272656d3b636f6c6f723a236666667d2e636f6e7461696e65727b646973706c61793a666c65783b77696474683a3130303b6865696768743a63616c63283130307668202d2035307078297d2e736964656261727b77696474683a32323070783b6261636b67726f756e643a233265333233633b70616464696e673a3230707820307d2e7369646562617220756c7b6c6973742d7374796c653a6e6f6e657d2e7369646562617220756c206c697b70616464696e673a3130707820323070787d2e7369646562617220756c206c693a686f7665727b6261636b67726f756e643a233362343034647d2e6d61696e2d636f6e74656e747b666c65783a313b70616464696e673a323070783b6f766572666c6f772d793a61757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
[2025-10-05 22:53:46] [PASS] STEP 3.3 completed successfully

STEP 3.4 Validate DNS address

PASS

Started | Finished
2025-10-05 22:53:46 | 2025-10-05 22:53:46

#### Log

[2025-10-05 22:53:46] [STEP 3.4] Validate DNS address
[2025-10-05 22:53:46] [INFO] [PCAP-EXPECT] checkFrames start path=G:\_GitHub\HW_10-In-Rack_PDU\tests\tc_network_pcap\report_tc_network_pcap\capture_settings.pcap filter=http.response and ip.addr==192.168.0.11 ordered=False expect_count=None n_expected=1
[2025-10-05 22:53:46] [INFO] [PCAP-READ] read_PCAPFrames() execute called
[2025-10-05 22:53:46] [INFO] [PCAP-READ]   pcap_path=G:\_GitHub\HW_10-In-Rack_PDU\tests\tc_network_pcap\report_tc_network_pcap\capture_settings.pcap
[2025-10-05 22:53:46] [INFO] [PCAP-READ]   display_filter=http.response and ip.addr==192.168.0.11
[2025-10-05 22:53:46] [INFO] [PCAP-READ] File exists, size=4414 bytes
[2025-10-05 22:53:46] [INFO] [PCAP-READ] Running tshark to extract fields...
[2025-10-05 22:53:46] [INFO] [PCAP-CHECK] tshark fields start filter=http.response and ip.addr==192.168.0.11
[2025-10-05 22:53:46] [TSHARK-FIELDS] cmd=tshark -r G:\_GitHub\HW_10-In-Rack_PDU\tests\tc_network_pcap\report_tc_network_pcap\capture_settings.pcap -o tcp.desegment_tcp_streams:TRUE -o http.desegment_body:TRUE -T fields -E header=n -E separator=	 -E occurrence=f -e frame.number -e frame.len -e frame.time_epoch -e eth.src -e eth.dst -e vlan.id -e vlan.priority -e http.file_data -e tcp.reassembled.data -e tcp.payload -e data.data -Y "http.response and ip.addr==192.168.0.11"
[2025-10-05 22:53:46] [TSHARK-FIELDS] rc=0
[2025-10-05 22:53:46] [TSHARK-FIELDS OUT]
9	421	1759697618.167510000	00:08:dc:be:ef:91	10:ff:e0:03:49:ac			3c21444f43545950452068746d6c3e3c68746d6c3e3c686561643e3c6d65746120636861727365743d225554462d38223e3c6d657461206e616d653d2276696577706f72742220636f6e74656e743d2277696474683d6465766963652d77696474682c696e697469616c2d7363616c653d312e30223e3c7469746c653e454e455247495320504455202d2053657474696e67733c2f7469746c653e3c7374796c653e2a7b6d617267696e3a303b70616464696e673a303b626f782d73697a696e673a626f726465722d626f783b666f6e742d66616d696c793a73616e732d73657269667d626f64797b6261636b67726f756e643a233161316432333b636f6c6f723a236534653465347d617b636f6c6f723a236161613b746578742d6465636f726174696f6e3a6e6f6e657d613a686f7665727b636f6c6f723a236666667d2e746f706261727b77696474683a3130303b6865696768743a353070783b6261636b67726f756e643a233234323733313b646973706c61793a666c65783b616c69676e2d6974656d733a63656e7465723b70616464696e673a3020323070787d2e746f706261722068317b666f6e742d73697a653a312e3272656d3b636f6c6f723a236666667d2e636f6e7461696e65727b646973706c61793a666c65783b77696474683a3130303b6865696768743a63616c63283130307668202d2035307078297d2e736964656261727b77696474683a32323070783b6261636b67726f756e643a233265333233633b70616464696e673a3230707820307d2e7369646562617220756c7b6c6973742d7374796c653a6e6f6e657d2e7369646562617220756c206c697b70616464696e673a3130707820323070787d2e7369646562617220756c206c693a686f7665727b6261636b67726f756e643a233362343034647d2e6d61696e2d636f6e74656e747b666c65783a313b70616464696e673a323070783b6f766572666c6f772d793a61757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
[2025-10-05 22:53:46] [PASS] STEP 3.4 completed successfully

STEP 3.5 Settings: Device Name present

PASS

Started | Finished
2025-10-05 22:53:46 | 2025-10-05 22:53:46

#### Log

[2025-10-05 22:53:46] [STEP 3.5] Settings: Device Name present
[2025-10-05 22:53:46] [INFO] [PCAP-EXPECT] checkFrames start path=G:\_GitHub\HW_10-In-Rack_PDU\tests\tc_network_pcap\report_tc_network_pcap\capture_settings.pcap filter=http.response and ip.addr==192.168.0.11 ordered=False expect_count=None n_expected=1
[2025-10-05 22:53:46] [INFO] [PCAP-READ] read_PCAPFrames() execute called
[2025-10-05 22:53:46] [INFO] [PCAP-READ]   pcap_path=G:\_GitHub\HW_10-In-Rack_PDU\tests\tc_network_pcap\report_tc_network_pcap\capture_settings.pcap
[2025-10-05 22:53:46] [INFO] [PCAP-READ]   display_filter=http.response and ip.addr==192.168.0.11
[2025-10-05 22:53:46] [INFO] [PCAP-READ] File exists, size=4414 bytes
[2025-10-05 22:53:46] [INFO] [PCAP-READ] Running tshark to extract fields...
[2025-10-05 22:53:46] [INFO] [PCAP-CHECK] tshark fields start filter=http.response and ip.addr==192.168.0.11
[2025-10-05 22:53:46] [TSHARK-FIELDS] cmd=tshark -r G:\_GitHub\HW_10-In-Rack_PDU\tests\tc_network_pcap\report_tc_network_pcap\capture_settings.pcap -o tcp.desegment_tcp_streams:TRUE -o http.desegment_body:TRUE -T fields -E header=n -E separator=	 -E occurrence=f -e frame.number -e frame.len -e frame.time_epoch -e eth.src -e eth.dst -e vlan.id -e vlan.priority -e http.file_data -e tcp.reassembled.data -e tcp.payload -e data.data -Y "http.response and ip.addr==192.168.0.11"
[2025-10-05 22:53:46] [TSHARK-FIELDS] rc=0
[2025-10-05 22:53:46] [TSHARK-FIELDS OUT]
9	421	1759697618.167510000	00:08:dc:be:ef:91	10:ff:e0:03:49:ac			3c21444f43545950452068746d6c3e3c68746d6c3e3c686561643e3c6d65746120636861727365743d225554462d38223e3c6d657461206e616d653d2276696577706f72742220636f6e74656e743d2277696474683d6465766963652d77696474682c696e697469616c2d7363616c653d312e30223e3c7469746c653e454e455247495320504455202d2053657474696e67733c2f7469746c653e3c7374796c653e2a7b6d617267696e3a303b70616464696e673a303b626f782d73697a696e673a626f726465722d626f783b666f6e742d66616d696c793a73616e732d73657269667d626f64797b6261636b67726f756e643a233161316432333b636f6c6f723a236534653465347d617b636f6c6f723a236161613b746578742d6465636f726174696f6e3a6e6f6e657d613a686f7665727b636f6c6f723a236666667d2e746f706261727b77696474683a3130303b6865696768743a353070783b6261636b67726f756e643a233234323733313b646973706c61793a666c65783b616c69676e2d6974656d733a63656e7465723b70616464696e673a3020323070787d2e746f706261722068317b666f6e742d73697a653a312e3272656d3b636f6c6f723a236666667d2e636f6e7461696e65727b646973706c61793a666c65783b77696474683a3130303b6865696768743a63616c63283130307668202d2035307078297d2e736964656261727b77696474683a32323070783b6261636b67726f756e643a233265333233633b70616464696e673a3230707820307d2e7369646562617220756c7b6c6973742d7374796c653a6e6f6e657d2e7369646562617220756c206c697b70616464696e673a3130707820323070787d2e7369646562617220756c206c693a686f7665727b6261636b67726f756e643a233362343034647d2e6d61696e2d636f6e74656e747b666c65783a313b70616464696e673a323070783b6f766572666c6f772d793a61757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
[2025-10-05 22:53:46] [PASS] STEP 3.5 completed successfully

STEP 3.6 Settings: Device Location present

PASS

Started | Finished
2025-10-05 22:53:46 | 2025-10-05 22:53:46

#### Log

[2025-10-05 22:53:46] [STEP 3.6] Settings: Device Location present
[2025-10-05 22:53:46] [INFO] [PCAP-EXPECT] checkFrames start path=G:\_GitHub\HW_10-In-Rack_PDU\tests\tc_network_pcap\report_tc_network_pcap\capture_settings.pcap filter=http.response and ip.addr==192.168.0.11 ordered=False expect_count=None n_expected=1
[2025-10-05 22:53:46] [INFO] [PCAP-READ] read_PCAPFrames() execute called
[2025-10-05 22:53:46] [INFO] [PCAP-READ]   pcap_path=G:\_GitHub\HW_10-In-Rack_PDU\tests\tc_network_pcap\report_tc_network_pcap\capture_settings.pcap
[2025-10-05 22:53:46] [INFO] [PCAP-READ]   display_filter=http.response and ip.addr==192.168.0.11
[2025-10-05 22:53:46] [INFO] [PCAP-READ] File exists, size=4414 bytes
[2025-10-05 22:53:46] [INFO] [PCAP-READ] Running tshark to extract fields...
[2025-10-05 22:53:46] [INFO] [PCAP-CHECK] tshark fields start filter=http.response and ip.addr==192.168.0.11
[2025-10-05 22:53:46] [TSHARK-FIELDS] cmd=tshark -r G:\_GitHub\HW_10-In-Rack_PDU\tests\tc_network_pcap\report_tc_network_pcap\capture_settings.pcap -o tcp.desegment_tcp_streams:TRUE -o http.desegment_body:TRUE -T fields -E header=n -E separator=	 -E occurrence=f -e frame.number -e frame.len -e frame.time_epoch -e eth.src -e eth.dst -e vlan.id -e vlan.priority -e http.file_data -e tcp.reassembled.data -e tcp.payload -e data.data -Y "http.response and ip.addr==192.168.0.11"
[2025-10-05 22:53:46] [TSHARK-FIELDS] rc=0
[2025-10-05 22:53:46] [TSHARK-FIELDS OUT]
9	421	1759697618.167510000	00:08:dc:be:ef:91	10:ff:e0:03:49:ac			3c21444f43545950452068746d6c3e3c68746d6c3e3c686561643e3c6d65746120636861727365743d225554462d38223e3c6d657461206e616d653d2276696577706f72742220636f6e74656e743d2277696474683d6465766963652d77696474682c696e697469616c2d7363616c653d312e30223e3c7469746c653e454e455247495320504455202d2053657474696e67733c2f7469746c653e3c7374796c653e2a7b6d617267696e3a303b70616464696e673a303b626f782d73697a696e673a626f726465722d626f783b666f6e742d66616d696c793a73616e732d73657269667d626f64797b6261636b67726f756e643a233161316432333b636f6c6f723a236534653465347d617b636f6c6f723a236161613b746578742d6465636f726174696f6e3a6e6f6e657d613a686f7665727b636f6c6f723a236666667d2e746f706261727b77696474683a3130303b6865696768743a353070783b6261636b67726f756e643a233234323733313b646973706c61793a666c65783b616c69676e2d6974656d733a63656e7465723b70616464696e673a3020323070787d2e746f706261722068317b666f6e742d73697a653a312e3272656d3b636f6c6f723a236666667d2e636f6e7461696e65727b646973706c61793a666c65783b77696474683a3130303b6865696768743a63616c63283130307668202d2035307078297d2e736964656261727b77696474683a32323070783b6261636b67726f756e643a233265333233633b70616464696e673a3230707820307d2e7369646562617220756c7b6c6973742d7374796c653a6e6f6e657d2e7369646562617220756c206c697b70616464696e673a3130707820323070787d2e7369646562617220756c206c693a686f7665727b6261636b67726f756e643a233362343034647d2e6d61696e2d636f6e74656e747b666c65783a313b70616464696e673a323070783b6f766572666c6f772d793a61757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
[2025-10-05 22:53:46] [PASS] STEP 3.6 completed successfully

STEP 3.7 Settings: Page title present

PASS

Started | Finished
2025-10-05 22:53:46 | 2025-10-05 22:53:47
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
