DvidMakesThings/HW_10-In-Rack_PDU/docs/Tests/report_tc_pcap_capture/tc_pcap_capture_report.html

# ENERGIS Test Report

Overall: PASS Started: 2025-10-05 22:55:04 Session ID: 7982e4c1

Passed: 6

Failed: 0

Unknown: 0

Total: 6

### Environment

Test Session ID

7982e4c1

Hostname

DPC

Os

Windows 11 (10.0.26100)

Python

3.13.7 (tags/v3.13.7:bcee1c3, Aug 14 2025, 14:15:11) [MSC v.1944 64 bit (AMD64)]

Generated_at

2025-10-05 22:55:20

Log_file

G:\_GitHub\HW_10-In-Rack_PDU\tests\tc_pcap_capture\report_tc_pcap_capture\tc_pcap_capture_results.log

### Steps

PRE-STEP 1 Reboot device via UART

PASS

Started | Finished
2025-10-05 22:55:04 | 2025-10-05 22:55:14

Step Log

DETAIL

#### Log

[2025-10-05 22:55:04] [PRE-STEP 1] Reboot device via UART
[2025-10-05 22:55:04] [INFO] [SERIAL] send_command() called
[2025-10-05 22:55:04] [INFO] [SERIAL]   port=COM11, command='REBOOT', baudrate=115200, timeout=2.0s
[2025-10-05 22:55:04] [INFO] [SERIAL] Opening connection to port=COM11
[2025-10-05 22:55:04] [INFO] [SERIAL]   Configuration: baudrate=115200, timeout=2.0s, write_timeout=2.0s
[2025-10-05 22:55:04] [INFO] [SERIAL]   Flow control: xonxoff=False, rtscts=False, dsrdtr=False
[2025-10-05 22:55:04] [INFO] [SERIAL] Port COM11 opened successfully
[2025-10-05 22:55:04] [INFO] [SERIAL] Stabilizing connection (100ms delay)...
[2025-10-05 22:55:04] [INFO] [SERIAL] Resetting input and output buffers
[2025-10-05 22:55:04] [INFO] [SERIAL] Connection ready: port=COM11, baudrate=115200, timeout=2.0s
[2025-10-05 22:55:04] [INFO] [SERIAL TX] Sending command: 'REBOOT'
[2025-10-05 22:55:04] [INFO] [SERIAL TX] Payload length: 8 bytes (including CR+LF)
[2025-10-05 22:55:04] [INFO] [SERIAL TX] Hex dump:
[2025-10-05 22:55:04] [INFO]   0000  52 45 42 4F 4F 54 0D 0A                           |REBOOT..|
[2025-10-05 22:55:04] [INFO] [SERIAL TX] Wrote 8 bytes to port
[2025-10-05 22:55:04] [INFO] [SERIAL TX] Waiting 50ms for device processing...
[2025-10-05 22:55:04] [INFO] [SERIAL RX] Starting to read response (timeout=2.0s)
[2025-10-05 22:55:04] [INFO] [SERIAL RX] Chunk #1: received 32 bytes (elapsed: 0.126s, total: 32 bytes)
[2025-10-05 22:55:04] [ERROR] [SERIAL ERROR] Exception during send_command:
[2025-10-05 22:55:04] [ERROR] [SERIAL ERROR]   Type: SerialException
[2025-10-05 22:55:04] [ERROR] [SERIAL ERROR]   Message: ClearCommError failed (PermissionError(13, 'The device does not recognize the command.', None, 22))
[2025-10-05 22:55:04] [ERROR] [SERIAL ERROR]   Port: COM11, Command: 'REBOOT'
[2025-10-05 22:55:04] [INFO] [SERIAL] Closing port COM11
[2025-10-05 22:55:04] [INFO] [SERIAL] Port COM11 closed successfully
[2025-10-05 22:55:04] [INFO] [SERIAL] wait_for_reboot_and_ready() called
[2025-10-05 22:55:04] [INFO] [SERIAL]   port=COM11, ready_token='SYSTEM READY', baudrate=115200, timeout=15.0s
[2025-10-05 22:55:04] [INFO] [SERIAL] Waiting 200ms for device to start rebooting...
[2025-10-05 22:55:04] [INFO] [SERIAL] Connection attempt #1 (remaining timeout: 14.8s)
[2025-10-05 22:55:04] [INFO] [SERIAL] Connection attempt #1 failed: SerialException: could not open port 'COM11': FileNotFoundError(2, 'The system cannot find the file specified.', None, 2)
[2025-10-05 22:55:04] [INFO] [SERIAL] Waiting 200ms before next attempt...
[2025-10-05 22:55:05] [INFO] [SERIAL] Connection attempt #2 (remaining timeout: 14.6s)
[2025-10-05 22:55:05] [INFO] [SERIAL] Connection attempt #2 failed: SerialException: could not open port 'COM11': FileNotFoundError(2, 'The system cannot find the file specified.', None, 2)
[2025-10-05 22:55:05] [INFO] [SERIAL] Waiting 200ms before next attempt...
[2025-10-05 22:55:05] [INFO] [SERIAL] Connection attempt #3 (remaining timeout: 14.4s)
[2025-10-05 22:55:05] [INFO] [SERIAL] Connection attempt #3 failed: SerialException: could not open port 'COM11': FileNotFoundError(2, 'The system cannot find the file specified.', None, 2)
[2025-10-05 22:55:05] [INFO] [SERIAL] Waiting 200ms before next attempt...
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
