DvidMakesThings/HW_10-In-Rack_PDU/docs/Compliance_Documents/ENE-TDOC-LABEL/ENE-TDOC-LABEL-SN-0167662.png

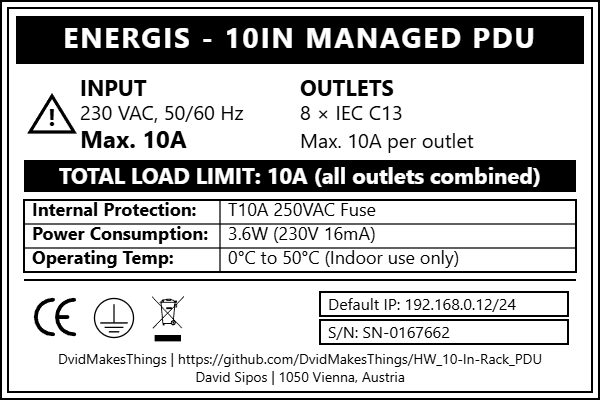
docs/Compliance_Documents/ENE-TDOC-LABEL/ENE-TDOC-LABEL-SN-0167662.png
