DvidMakesThings/HW_10-In-Rack_PDU/images/_proto/Controller Board/Rev2.0/Controller-Board_2.0_Top.png

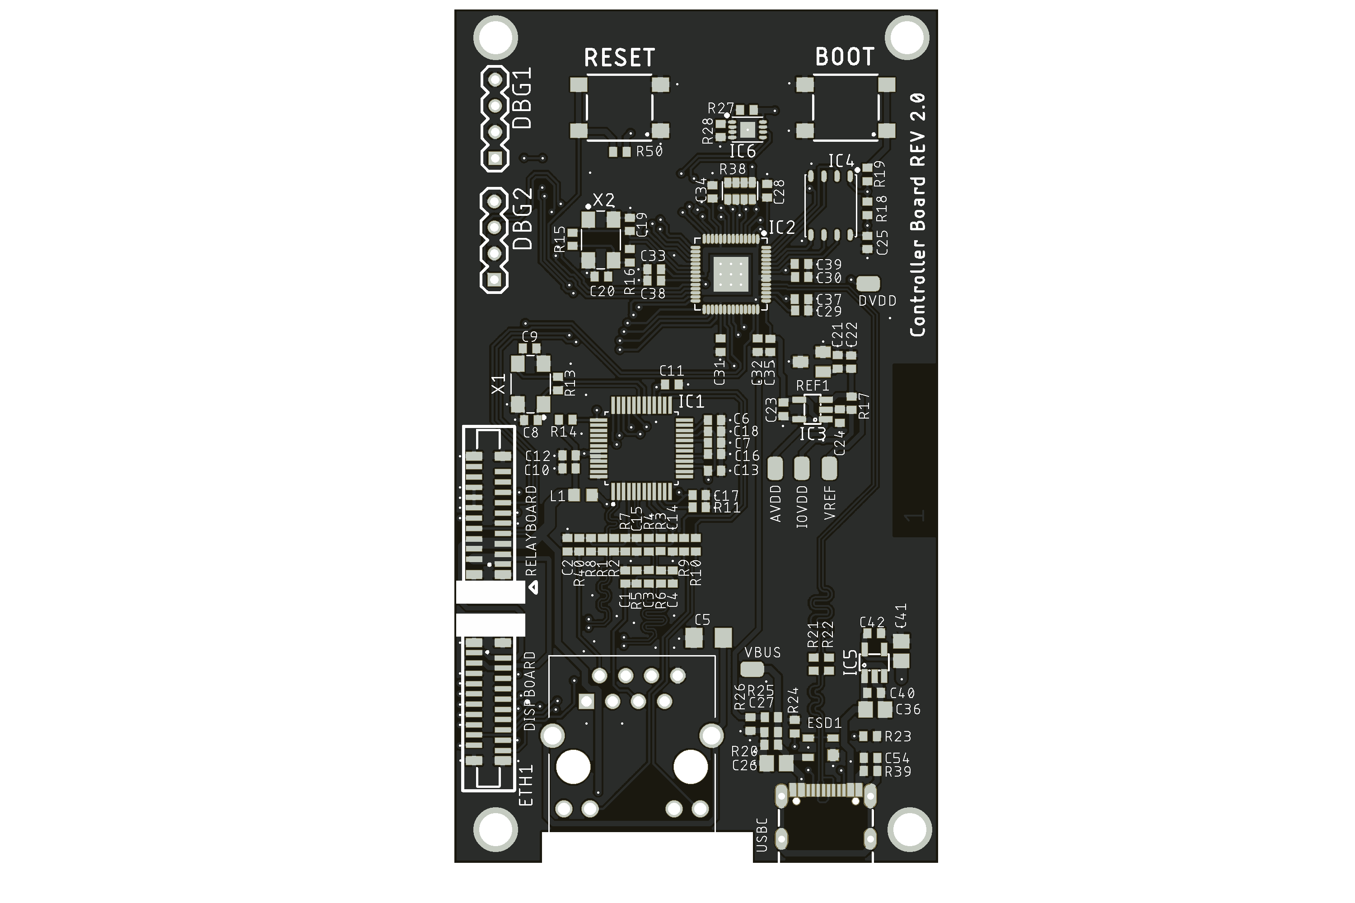
images/_proto/Controller Board/Rev2.0/Controller-Board_2.0_Top.png
