DvidMakesThings/HW_10-In-Rack_PDU/images/_proto/Controller Board/Rev2.0/ControllerBoard_2.0_3D-1.png

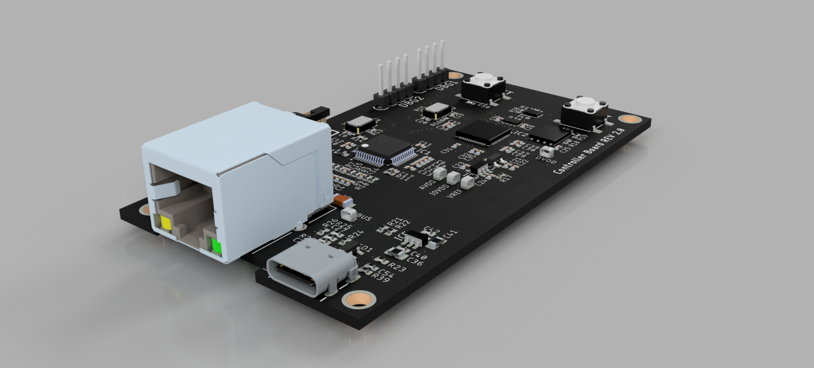
images/_proto/Controller Board/Rev2.0/ControllerBoard_2.0_3D-1.png
