DvidMakesThings/HW_10-In-Rack_PDU/images/_proto/Display Board/Rev2.0/Display-board_2.0_Bottom.png

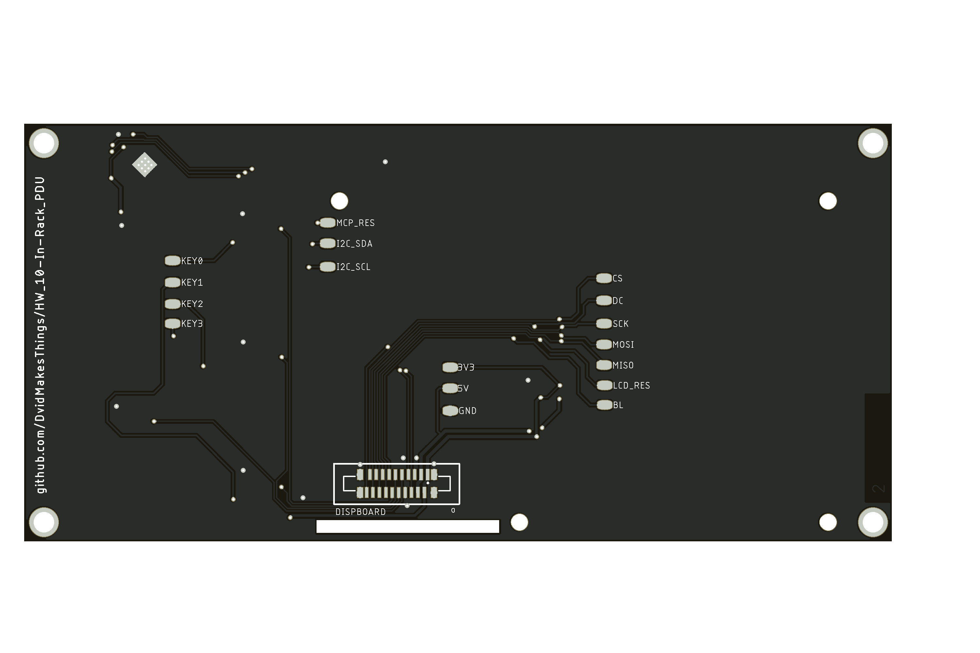
images/_proto/Display Board/Rev2.0/Display-board_2.0_Bottom.png
