DvidMakesThings/HW_10-In-Rack_PDU/images/_proto/Display Board/Rev2.0/DisplayBoard_2.0_3D-2.png

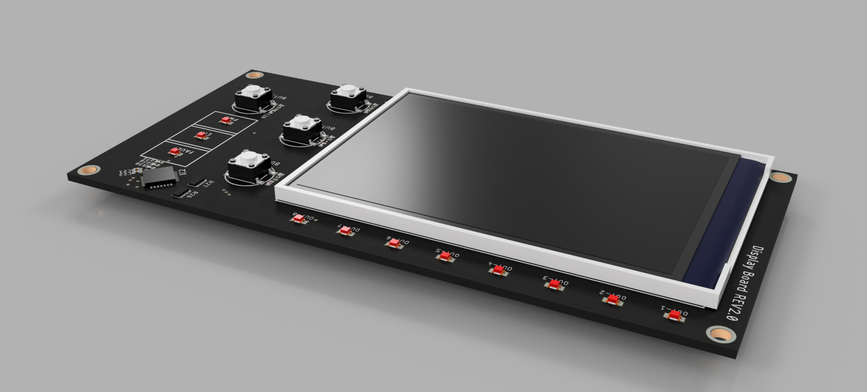
images/_proto/Display Board/Rev2.0/DisplayBoard_2.0_3D-2.png
