DvidMakesThings/HW_10-In-Rack_PDU/images/_proto/Relay Board/Rev2.1/Relay-Board_Rack-PDU_2.1_Bottom.png

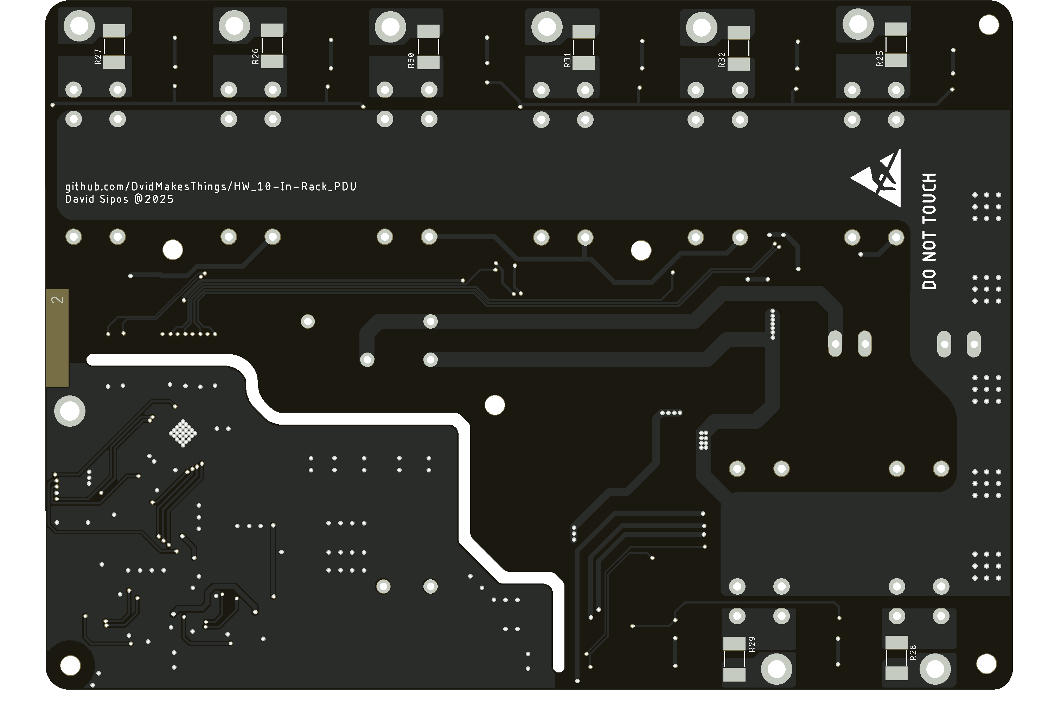
images/_proto/Relay Board/Rev2.1/Relay-Board_Rack-PDU_2.1_Bottom.png
