DvidMakesThings/HW_10-In-Rack_PDU/images/_proto/Relay Board/Rev2.1/RelayBoard_2.1_3D-1.png

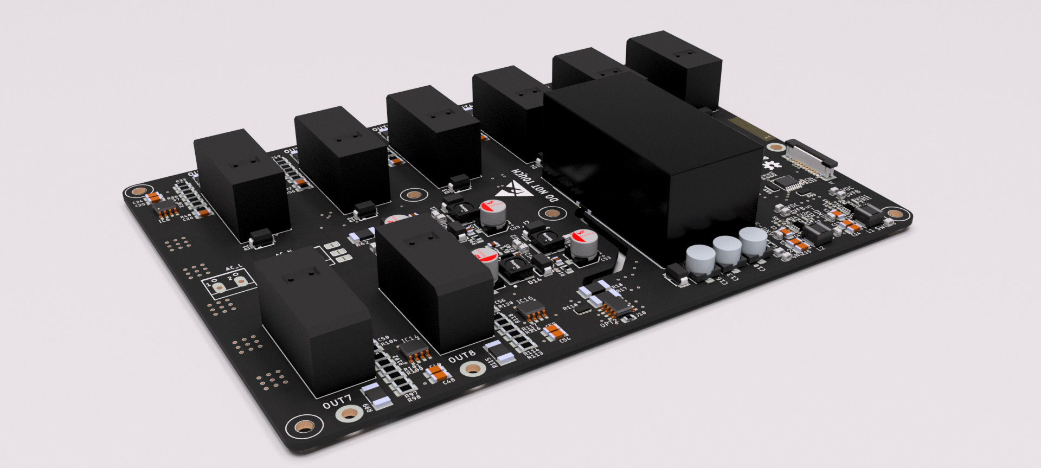
images/_proto/Relay Board/Rev2.1/RelayBoard_2.1_3D-1.png
