DvidMakesThings/HW_10-In-Rack_PDU/images/ENERGIS_1.1.0/Images for docs/ENERGIS-_Sheetmetal_Enclosure_front.png

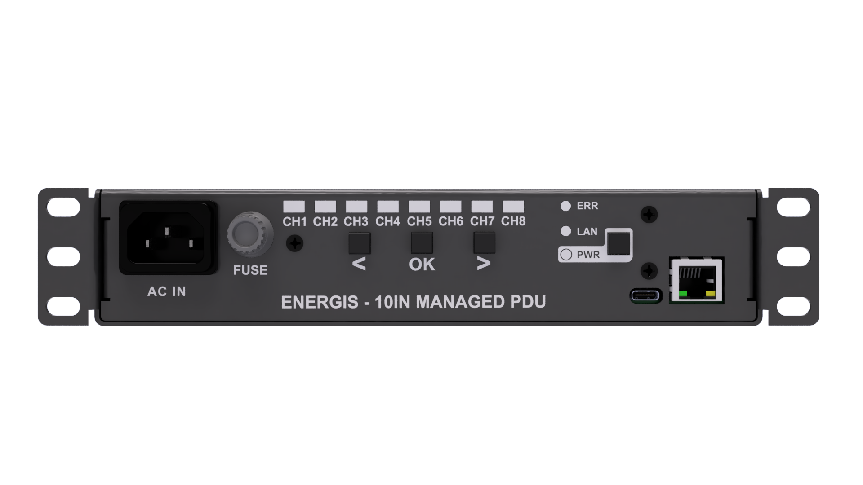
images/ENERGIS_1.1.0/Images for docs/ENERGIS-_Sheetmetal_Enclosure_front.png
