DvidMakesThings/HW_10-In-Rack_PDU/images/ENERGIS_1.1.0/PCB/ENERGIS-3D-PEM_ADAPTER_1.0.0.jpg

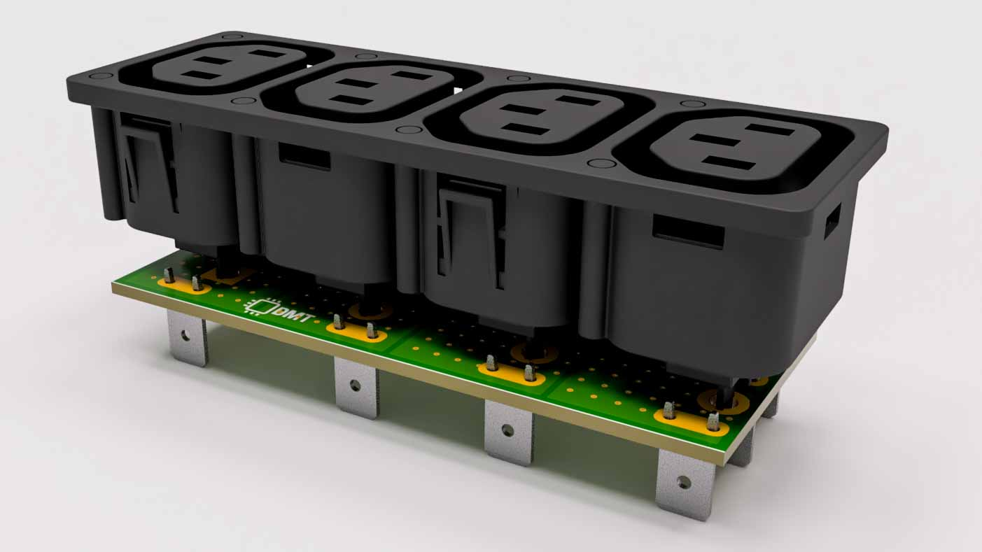
images/ENERGIS_1.1.0/PCB/ENERGIS-3D-PEM_ADAPTER_1.0.0.jpg
