DvidMakesThings/HW_10-In-Rack_PDU/images/photos/Enclosure_arrived.jpeg

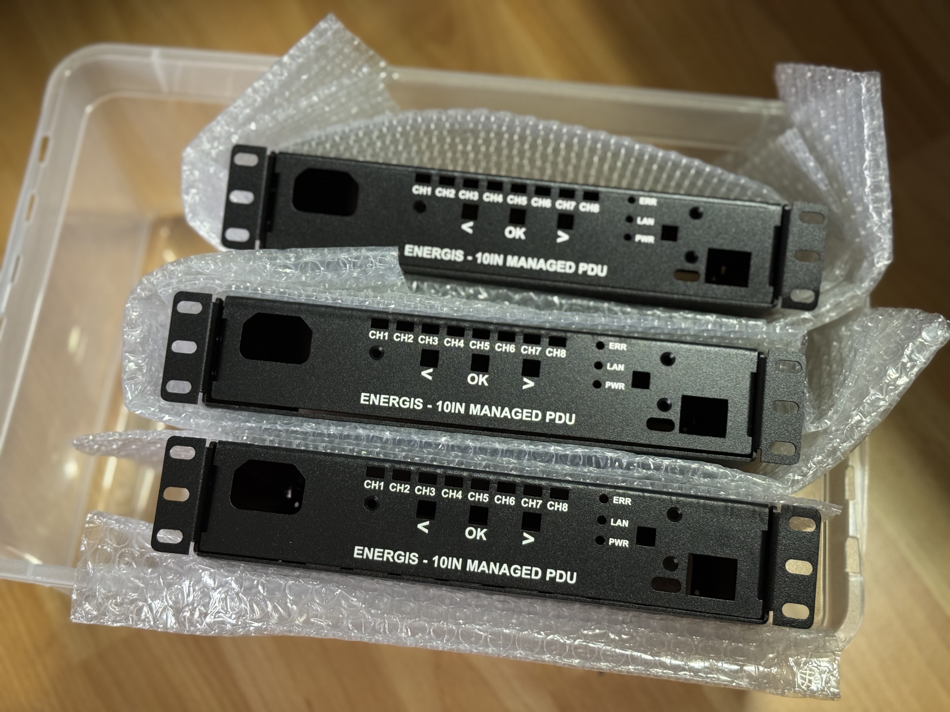
images/photos/Enclosure_arrived.jpeg
