DvidMakesThings/HW_10-In-Rack_PDU/src/Enclosure-Design/SheetMetal/Bottom_FrontView.png

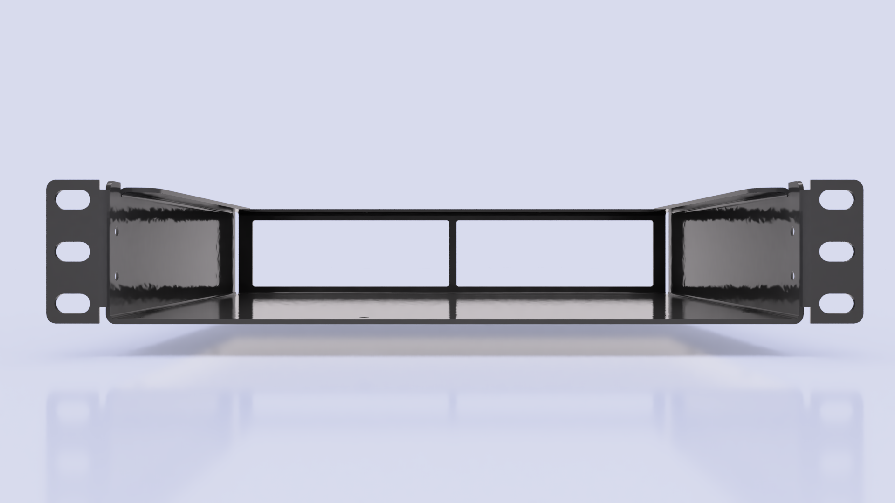
src/Enclosure-Design/SheetMetal/Bottom_FrontView.png
