DvidMakesThings/HW_10-In-Rack_PDU/src/Enclosure-Design/SheetMetal/Top_FrontView.PNG

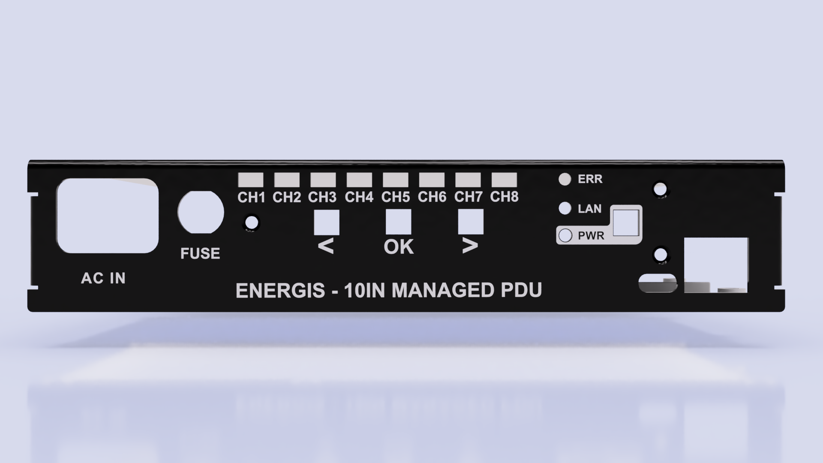
src/Enclosure-Design/SheetMetal/Top_FrontView.PNG
