DvidMakesThings/HW_10-In-Rack_PDU/src/Hardware-Design/ENERGIS/Rev1.1.0/Gerber/DisplayBoard/GERBER-ENERGIS_DispBrd_Rack-PDU_1.1.0/L4.png

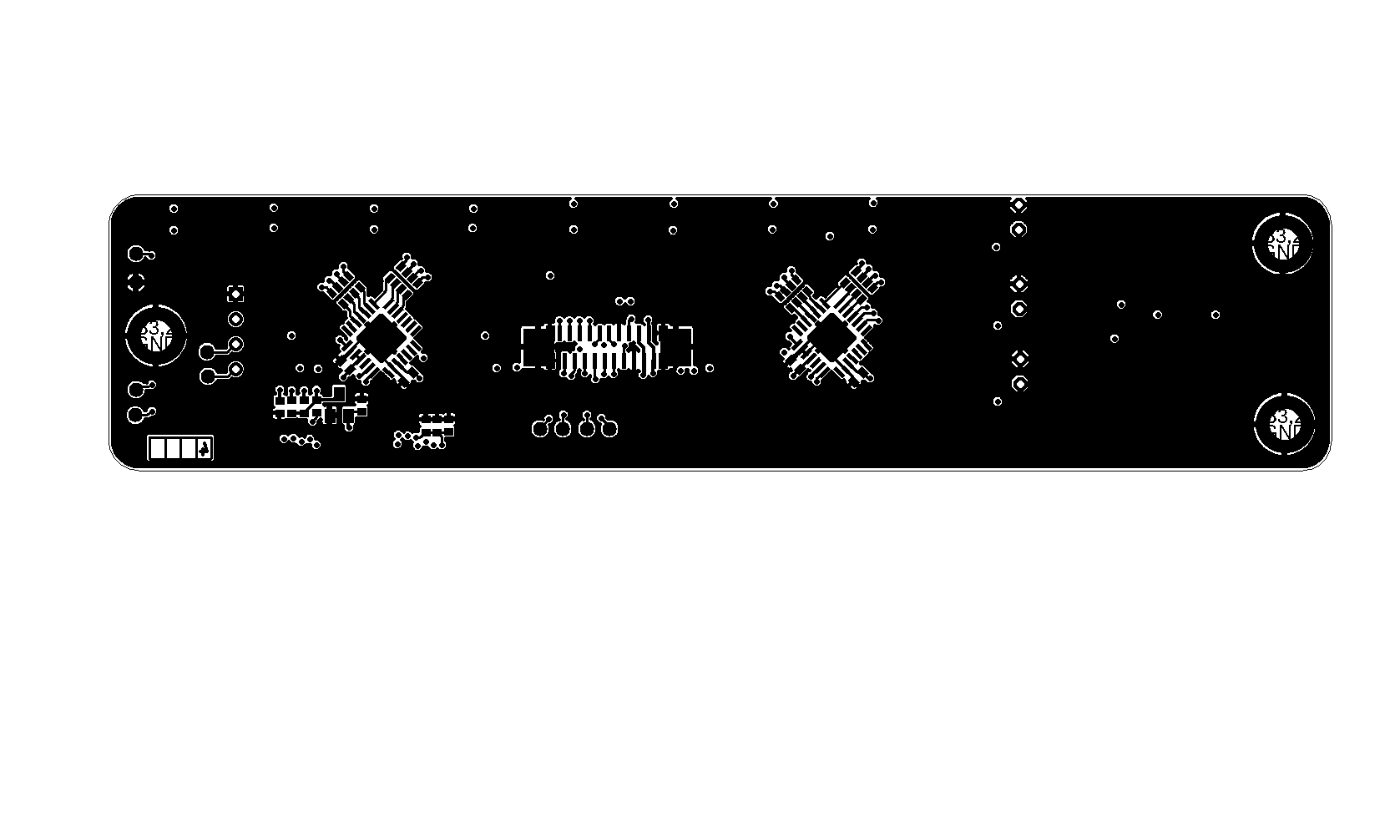
src/Hardware-Design/ENERGIS/Rev1.1.0/Gerber/DisplayBoard/GERBER-ENERGIS_DispBrd_Rack-PDU_1.1.0/L4.png
