DvidMakesThings/HW_10-In-Rack_PDU/src/Hardware-Design/ENERGIS/Rev1.1.0/Gerber/MainBoard/GERBER-ENERGIS_Rack-PDU_1.1.0/L1.png

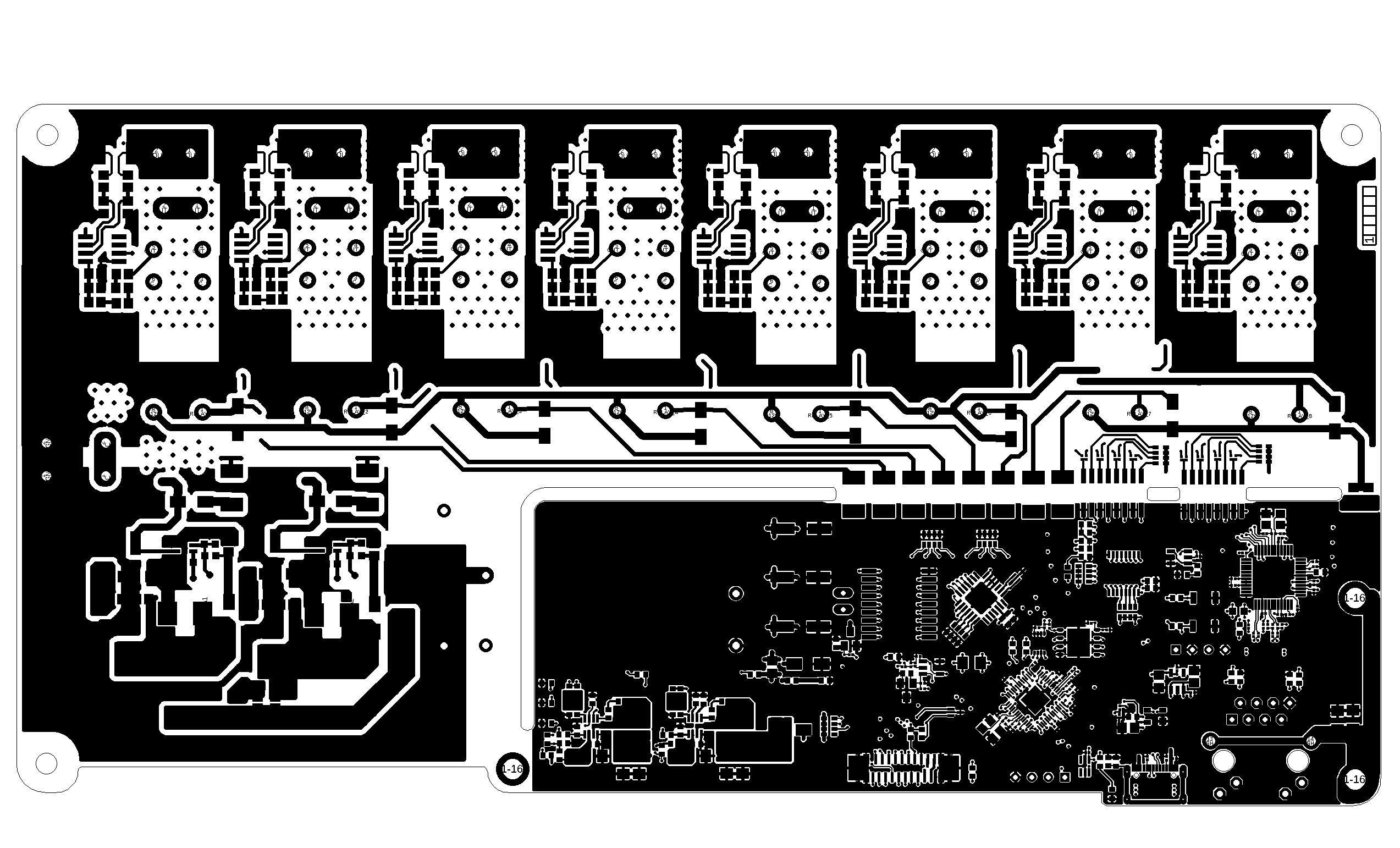
src/Hardware-Design/ENERGIS/Rev1.1.0/Gerber/MainBoard/GERBER-ENERGIS_Rack-PDU_1.1.0/L1.png
