DvidMakesThings/HW_10-In-Rack_PDU/src/Software/ENERGIS_RTOS/docs/DSCF1252.jpg

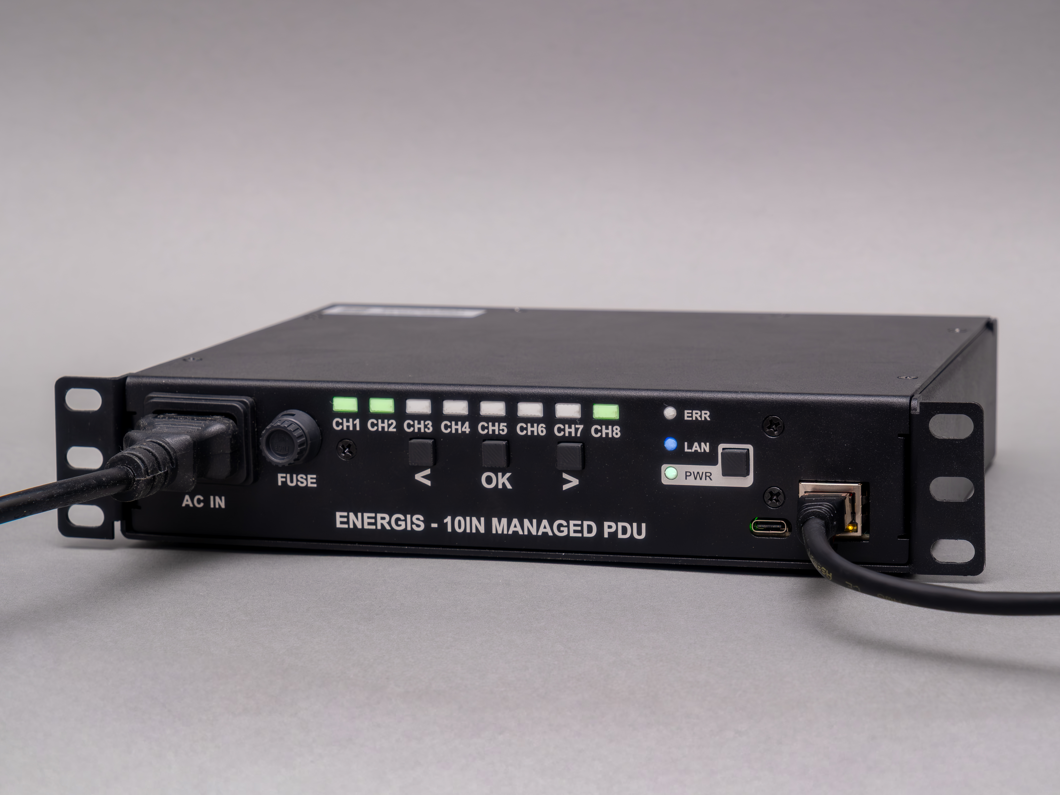
src/Software/ENERGIS_RTOS/docs/DSCF1252.jpg
