DvidMakesThings/HW_10-In-Rack_PDU/docs/Manuals/ENERGIS_AssemblyInstructions_rev_1.0.0.docx

ASSEMBLY INSTRUCTIONS

ENERGIS

8 Channel Managed PDU

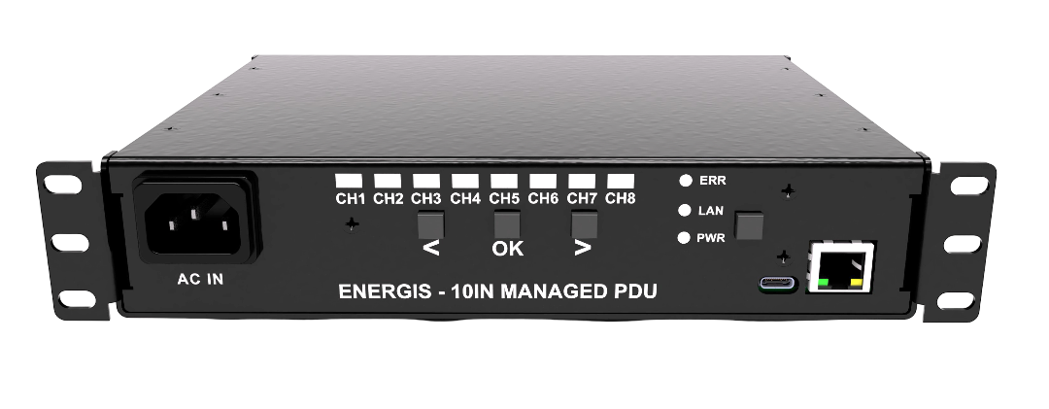
[picture p112: figure]
A képen elektronika, képernyőkép, Elektronikus eszköz, szöveg látható Előfordulhat, hogy az AI által létrehozott tartalom helytelen.

# Contents

# 1. Scope and prerequisites

This document describes the mechanical and final assembly of a single ENERGIS unit from bare PCBs and mechanical parts into a fully enclosed, tested device. It is meant to be followed step by step on a bench and assumes that all electronic assemblies and mechanical parts listed in the project BoM are available.

The instructions are written for people who already have basic experience with electronics handling and small mechanical assemblies. It is not an end user document and it is not intended to teach basic soldering, mains wiring or safety practices.

- What this document covers:
  - Assembly of one ENERGIS PDU from:
    - Pre-assembled ENERGIS Main Board and Display Board
    - Enclosure parts (top, bottom)
    - Connectors, 3D printed insulators, diffusers and fasteners
  - Mechanical integration, wiring of connectors where required
  - Final closure of the enclosure and basic functional checks
- Who this document is for
  - Technicians building small batches of units
  - System integrators assembling devices from kits
  - The original designer during manufacturing and service work
- What is not covered
  - PCB population and rework (SMD/through hole soldering on the bare boards)
  - Firmware development, debugging or modification
  - Detailed troubleshooting of faulty units
  - In depth safety analysis; for that, refer to the ENERGIS User Manual and local regulations

Where other documents are required (for example firmware programming or automated test procedures), they are referenced by name and link.

# 2. Tools, equipment, and materials

The following tools and materials are required or recommended to assemble an ENERGIS unit reliably and repeatably. Using the correct tools helps avoid mechanical damage to the enclosure, stripped threads and ESD damage to electronic assemblies.

## 2.1 Tools

- ESD work area
  - ESD mat connected to protective earth
  - ESD wrist strap with verified continuity
- Hand tools
  - Precision screwdrivers in the sizes actually used in the design (specified in the BoM)
  - Nut drivers or small spanners for standoffs and panel nuts, where used
  - Small side cutters for trimming cable ties or leads
  - Small flat nose pliers for guiding wires and holding nuts in tight spaces
- Optional tools
  - Torque screwdriver for panel and mounting screws, if torque limits are specified
  - Headlamp or bench light to inspect clearances and internal wiring

## 2.2 Consumables and auxiliary materials

- Cleaning and handling
  - Isopropyl alcohol and lint free wipes for cleaning PCB surfaces and enclosure panels before final closure
  - Compressed air (optional) to remove dust and particles from inside the enclosure
- Fastening and identification
  - Threadlocker (medium strength) for screws that are explicitly marked for its use in the assembly steps
  - Cable ties or adhesive cable clips for strain relief and bundling of internal wiring, if included in the design
  - Labels or a permanent marker for applying serial numbers and date codes to the device

Only use threadlocker and additional consumables where explicitly indicated in later sections of this document. Overuse on small screws or plastic parts can make future service more difficult or cause damage.

# 3. Safety and ESD notes

Assembly work on ENERGIS involves both sensitive electronics and mains-rated parts. The points below are intended to prevent avoidable damage and unsafe conditions during assembly.

WARNING – Risk of electric shock, fire or personal injury if instructions are ignored. All work on mains wiring must be carried out by qualified personnel.

CAUTION – Risk of equipment damage or loss of calibration if PCBs are handled incorrectly.

## 3.1 ESD handling

- Always work on an earthed ESD mat and wear a wrist strap when handling the Main Board, Display Board or any other electronic assemblies.
- Store PCBs in ESD-safe packaging (shielding bags or trays) until they are installed in the enclosure.
- Avoid touching IC pins, exposed pads, oscillator cans and connector contacts directly; handle boards by their edges where possible.
- Do not place PCBs on metal surfaces, tools or loose packing material that can hold static charge.

## 3.2 Mains safety during assembly

- Never perform any mains wiring or manipulation of the IEC inlet/outlets while the unit is plugged in. The mains cord must be disconnected from the wall outlet at all times during assembly.
- Do not apply mains power to an open or partially assembled unit. High-voltage areas must be fully enclosed and all protective covers and insulators installed before the first powered test.
- Ensure that the protective earth connection from the IEC inlet to the chassis and to the Main Board is present, correctly tightened and not obstructed by paint or anodizing. Do not defeat or bypass protective earth connections for any reason.
- After any mechanical change near mains parts (inlet, outlets, insulators), re-check clearances and creepage distances before powering the unit.

## 3.3 Powering during test

- When powered on the bench, use an isolation transformer or protected test outlet if available, and keep one hand away from the device when probing near mains areas.
- Do not power the Main Board in free air with mains wiring exposed or hanging loose. All live conductors must be mechanically secured and insulated as intended by the design.
- Use insulated tools for any measurements or adjustments made on a powered unit, and do not leave the device unattended while powered and open.

## 3.4 General precautions

- Do not modify the enclosure cut-outs, drill additional holes or remove insulator parts unless explicitly required by an engineering change. Any modification affecting mains wiring or shielding must be reviewed for safety.
- Do not substitute parts (connectors, fuses, wires, screws) with lower-rated or unknown components. If a part is unavailable, use an equivalent with equal or better electrical and mechanical ratings.
- If any damage is observed (cracked PCB, burnt marks, deformed connectors, damaged insulation), stop assembly and quarantine the unit for inspection instead of “making it fit”.

Following these rules is a condition for safe assembly. The detailed user-facing safety information remains in the ENERGIS User Manual and does not replace the installer’s obligation to follow local electrical regulations.

# 4. Bill of Materials (TO BE EDITED)

This section lists the parts required to assemble one complete ENERGIS unit from pre-built PCBs and mechanical components. It is not a full electrical BoM; only items relevant to mechanical integration and final assembly are included.

For practical use, it is recommended to keep this BoM in table form with at least the following columns: Item, Description, Quantity per unit, Reference / part number, and Assembly step (the step in this document where the part is installed).

## 4.1 Electronics sub-assemblies

Item ID | Description | Part number | Qty/ unit | Assembly step
E1 | ENERGIS Main Board | Main Board v1.0.0 | 1 | Step X.X
E2 | ENERGIS Display Board | Display Board v1.1.0 | 1 | Step X.X
E3 | Main–Display interconnect harness | (specify type & length) | 1 | Step X.X
E4 | Front-panel button caps (set) | (specify) | 1 set | Step X.X
E5 | Light pipes / LED diffusers (set) | (specify) | 1 set | Step X.X

## 4.2 Enclosure and mechanical parts

Item ID | Description | Part number | Qty / unit | Assembly step
M1 | Enclosure top cover, Al 5052 | Top rev X.Y | 1 | Step X.X
M2 | Enclosure bottom cover, Al 5052 | Bottom rev X.Y | 1 | Step X.X
M3 | Rack mounting ears (left + right) | (if separate) | 1 set | Step X.X
M4 | 3D printed insulator – type A | (specify) | n pcs | Step X.X
M5 | 3D printed insulator – type B | (specify) | n pcs | Step X.X
M6 | 3D printed LED diffuser block – channel | (specify) | n pcs | Step X.X
M7 | M3×6 pan head screw (display board) | (specify finish) | n pcs | Step X.X
M8 | M3×8 countersunk screw (top–bottom) | (specify finish) | n pcs | Step X.X
M9 | M3 standoff, length __ mm (main board) | (specify) | n pcs | Step X.X
M10 | Additional spacers / supports (if used) | (specify) | n pcs | Step X.X

## 4.3 Connectors and external hardware

Item ID | Description | Part number / type | Qty / unit | Assembly step
C1 | IEC mains inlet | (specify type) | 1 | Step X.X
C2 | IEC C13 outlet block / 8× individual C13 | (specify) | 1 block / 8 | Step X.X
C3 | RJ45 Ethernet connector / panel feedthrough | (specify) | 1 | Step X.X
C4 | USB-C connector / panel extension (if used) | (specify) | 1 | Step X.X
C5 | Security seal (tamper-evident) | (specify) | 1 | Step X.X
C6 | Rating label | (specify) | 1 | Step X.X
C7 | Serial number label | (specify) | 1 | Step X.X
C8 | Additional safety / warning labels | (specify) | as req. | Step X.X

# 5. PCB preparation and inspection (TO BE EDITED)

Before installing the PCBs into the enclosure, each board should be checked and, if applicable, pre-tested. This avoids having to disassemble a finished unit to correct basic issues.

## 5.1 Visual inspection

Perform a quick but systematic visual check on every Main Board and Display Board:

- Mechanical condition
  - No visible cracks, warping, or delamination of the PCB.
  - No bent, loose or damaged connectors (RJ45, USB, headers, terminal blocks, IEC-related parts if present on the board).
  - Relays, transformers and other tall components are seated correctly and not tilted or mechanically stressed.
- Component population
  - All “large” and safety-relevant parts are present: fuses, relays, terminal blocks, mains connectors, Ethernet and USB connectors, major ICs.
  - No obviously missing or misaligned parts, especially around the mains section and interface connectors.
  - No foreign objects (loose solder balls, wire strands) on the board.
- Solder quality
  - No visible solder bridges on connector pins, relay pins, or mains-related pads.
  - No burnt or discolored areas indicating previous overheating or rework problems.

If any issues are found, correct them or reject the board before continuing.

## 5.2 Basic electrical checks

If you have the equipment and procedures available, perform simple checks before enclosure assembly:

- Measure resistance between the mains input pins to confirm there is no hard short (expect high resistance or open circuit for an unpowered board).
- Verify continuity of the protective earth path from the inlet earth pin to the designated earth points on the PCB and chassis connection holes.
- The board design includes test pads for power rails, check for obvious shorts between main rails and ground using a multimeter.

These quick checks help avoid powering a board with a catastrophic fault.

  5.3 Revision labelling

To keep units traceable, confirm the board revision printed on the silk screen matches the intended hardware version (e.g. “Main Board v1.0.0”, “Display Board v1.1.0”). Apply any internal barcode or PCB ID labels.

# 6. Sub-assembly steps

This chapter describes the preparation of the main and display assemblies, including wiring of the IEC inlet and outlets, installation of 3D-printed parts and mounting of the PCBs onto the enclosure parts. All work in this section is carried out with the unit completely disconnected from the mains supply.

## 6.1 Main Board sub-assembly

This step prepares the mains inlet and outlet wiring and mounts the Main Board into the lower part of the enclosure.

### 6.1.1 Prepare IEC C14 inlet harness

- Cut live, neutral and earth conductors to the length required to reach from the inlet position to the Main Board Faston or screw terminals without tension.
- Strip the insulation to the length specified for the terminals.
- Slide the appropriate heatshrink sleeves onto each conductor before crimping.
- Crimp the Faston terminals (or solder connections, if used) to the IEC C14 inlet contacts according to the wiring diagram (L, N, PE).
- Slide an additional heatshrink sleeve onto each conductor, away from the stripped end. Do not shrink these sleeves yet

### 6.1.2 Prepare IEC C13 outlet harness

- For each IEC C13 outlet (CH1–CH8), cut live and neutral conductors to reach the corresponding Main Board terminals with sufficient slack for routing.
- Strip insulation and slide heatshrink sleeves onto each conductor.
- Crimp (or solder) the conductors to the C13 outlets in accordance with the polarity/terminal markings.
- Slide an additional heatshrink sleeve onto each conductor, away from the stripped end. Do not shrink these sleeves yet
- Group the conductors per channel (CH1…CH8) and, if required, label them so they can be matched to the correct channel positions on the Main Board later.

### 6.1.3 Install standoffs in the bottom cover

- Fit the M3 screws into the marked holes provided in the bottom cover for the Main Board mounting.
- Carefully add the insulator part and make sure all screws align with the insulator holes in the same position.

### 6.1.4 Install the Main Board onto the standoffs

- Place the Main Board onto the previously installed standoffs, aligning the mounting holes and any connector cut-outs with the enclosure openings.
- Secure the Main Board with M3 nuts and tighten them evenly. Do not over-tighten to avoid bending the PCB.

### 6.1.5 Install IEC C13 outlets into the bottom housing

- Insert the pre-cabled IEC C13 outlets into the rear panel cut-outs from the outside.
- Ensure each outlet is properly oriented and fully seated.
- The outlets must fit tightly after the audible click of the self-locking mechanism.
- Route the outlet wires inside the bottom housing so they lie roughly in the direction of the Main Board terminal area without crossing sharp edges.

### 6.1.6 Connect outlet harness to Main Board

- Route each channel’s live and neutral conductors to the corresponding Faston or screw terminals on the Main Board.
- Confirm correct mapping (CH1 wire set to CH1 terminals, etc.) before making connections.
- Connect each conductor firmly; after connection, slide the heatshrink sleeves into their final position over the board-side terminals and shrink them so that all exposed metal is covered.
- Arrange the wiring so that it does not obstruct other components and maintains adequate clearance to high-voltage parts and the enclosure walls.

### 6.1.7 Protective earth and clearance check

- Verify that the protective earth connection points on the Main Board and the chassis are accessible and free of paint or other insulating coatings where contact is required.
- Connect the protective earth cable to the main board and fix it with a M3 screw
- Confirm that the live and neutral conductors from the outlets are routed so they do not press against sharp edges, mounting screws or uninsulated metal.
- Check that clearances between high-voltage parts (inlet area, outlet wiring, mains side of the board) and the enclosure or other components match the mechanical design.

At the end of this step, the Main Board is mounted in the bottom enclosure, the IEC C13 outlets are installed and wired to the board.

## 6.2 Display Board and front panel

This step prepares the “top” assembly that carries the user interface and the IEC C14 inlet.

### 6.2.1 Install light diffusers and button hardware

- Insert the 3D-printed light diffuser blocks into the front panel openings for channel and status LEDs.
- Fit the pushbuttons and caps into their respective holes, ensuring correct orientation and smooth travel.
- Place 3pcs M3 screws into the front panel holes as shown

### 6.2.2 Mount the Display Board

- Position the Display Board behind the front panel so that the LEDs and button actuators align with the diffusers, button caps and the mounting screws from the previous 6.2.1 step.
- Use 1-1 M3 nuts for each mounting screws to fix the Display Board in position.
- Verify that each button operates freely and that no LED or component is mechanically stressed.

### 6.2.3 Connect the FPC cable to the Display Board

- Open the connector latch.
- Insert the FPC cable into the Display Board connector.
- Close the connector latch securely.

### 6.2.4 Install the IEC C14 inlet into the top assembly

- Insert the pre-cabled IEC C14 Power-entry module into its panel cut-out from the outside of the front/top assembly.
- Ensure correct orientation and that any gasket or reinforcement is in place.
- The Power-entry module shall fix itself tightly with an audible click of the self-latching mechanism.

After this step, the front panel with Display Board, diffusers, buttons, FPC cable and mounted IEC inlet forms a complete sub-assembly ready to be joined with the bottom part.

# 7. Enclosure assembly

## 7.1 Fitting together the top and bottom parts

This chapter describes how to combine the prepared sub-assemblies into a closed enclosure and complete all internal connections.

### 7.1.1 Join bottom assembly and front/top assembly

- Place the bottom assembly (Main Board, outlets, insulators installed) on the bench.
- Carefully bring the front/top assembly (front panel, Display Board, IEC inlet, FPC cable) into position above it.
- Guide the FPC cable and inlet harness into the enclosure so that they do not get trapped between the covers.

### 7.1.2 Connect IEC C14 inlet harness to Main Board

- Route the inlet harness to the mains input terminals on the Main Board.
- Connect live, neutral and earth conductors to the correct terminals according to the wiring diagram.
- Slide the heatshrink sleeves into their final position over the board-side terminations and shrink them so that all exposed metal is covered.
- Verify that the earth connection has a solid mechanical contact to both the Main Board and chassis where required.

### 7.1.3 Connect FPC cable to Main Board

- Plug the FPC cable (already attached to the Display Board) into the corresponding connector on the Main Board.
- Close the connector latch securely.
- Ensure there is enough slack in the cable to allow for slight movement of the covers without stressing the cable.

### 7.1.4 Cable routing and clearance check

- Arrange all internal wiring so that it follows clean routes and does not cross sharp edges or moveable joints.
- Make sure no cable is pinched between standoffs, insulators or enclosure walls.
- Confirm again that all clearances in the mains area are maintained and that insulators remain in place.

### 7.1.5 Close the enclosure

- Align the top and bottom covers fully and ensure that the front and rear faces sit flush.
- Install the screws joining the top and bottom parts in the pattern defined by the mechanical drawing (a “screw map” is recommended).
- Tighten the screws evenly; if a torque specification exists, apply it consistently.

### 7.1.6 Labels and security seal

- Apply labels and security seal
- Apply the rating label, serial number label and any required safety/warning labels to the enclosure in the designated positions.
- Apply the tamper-evident security seal so that opening the enclosure or removing the cover breaks the seal visibly.

After these steps, the ENERGIS unit is mechanically complete and wired. The next stage is final programming and functional test, which should be carried out according to the dedicated test procedure before the unit is considered ready for shipment.
