DvidMakesThings/HW_10-In-Rack_PDU/images/photos/quick assembly.jpeg

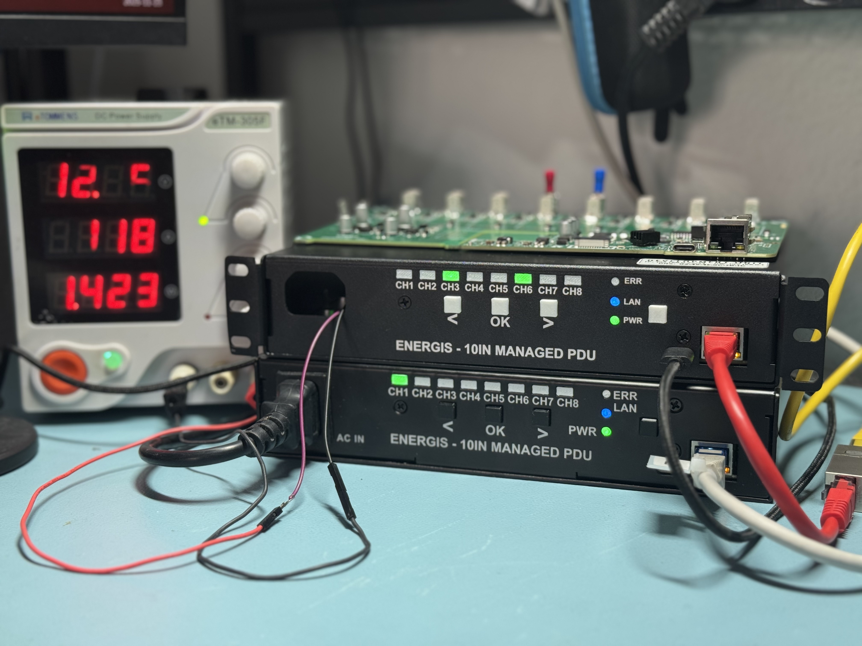
images/photos/quick assembly.jpeg
