DvidMakesThings/HW_10-In-Rack_PDU/src/Enclosure-Design/SheetMetal/ENERGIS_Assembled-1.png

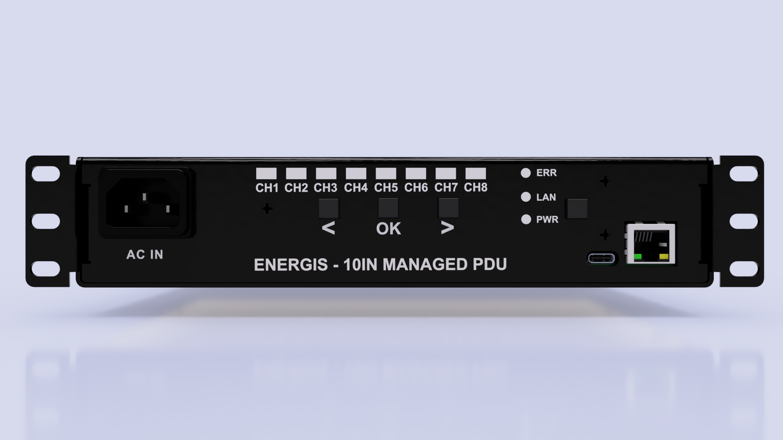
src/Enclosure-Design/SheetMetal/ENERGIS_Assembled-1.png
