DvidMakesThings/HW_10-In-Rack_PDU/tests/Nightly_regression/test_suite_Nightly_Tests_20251005_232014.html

# Test Suite: Nightly Tests

Overall: PASS Started: 2025-10-05 23:13:43 Duration: 390.46s Session ID: fa559c7a
Extended nightly test suite with stress testing

Passed: 8

Failed: 0

Timeout: 0

Error: 0

Skipped: 0

Total: 8

### Test Results

# | Test Name | Status | Duration | Details

1 | Sanity Check Test📄 Report | PASS | 12.12s
2 | Serial Communication Test📄 Report | PASS | 75.31s
3 | SNMP Test📄 Report | PASS | 39.42s
4 | Network PCAP Test📄 Report | PASS | 37.50s
5 | PCAP Capture Test📄 Report | PASS | 16.09s
6 | EEPROM Persistence Test📄 Report | PASS | 98.56s
7 | Power Meter HLW8032 Test📄 Report | PASS | 47.81s
8 | Stress Test - Rapid Switching📄 Report | PASS | 63.66s

### Environment

Session ID

fa559c7a

Hostname

DPC

OS

Windows 11

Python

3.13.7

Config

G:\_GitHub\HW_10-In-Rack_PDU\tests\.test_suites\nightly.yaml

Reports Dir

G:\_GitHub\HW_10-In-Rack_PDU\tests\Nightly_regression
