DvidMakesThings/HW_10-In-Rack_PDU/docs/doxygen/latex/calibration_8c_a94bdbf3b5ab88d4cfad2295e4b32b5c2_icgraph.pdf

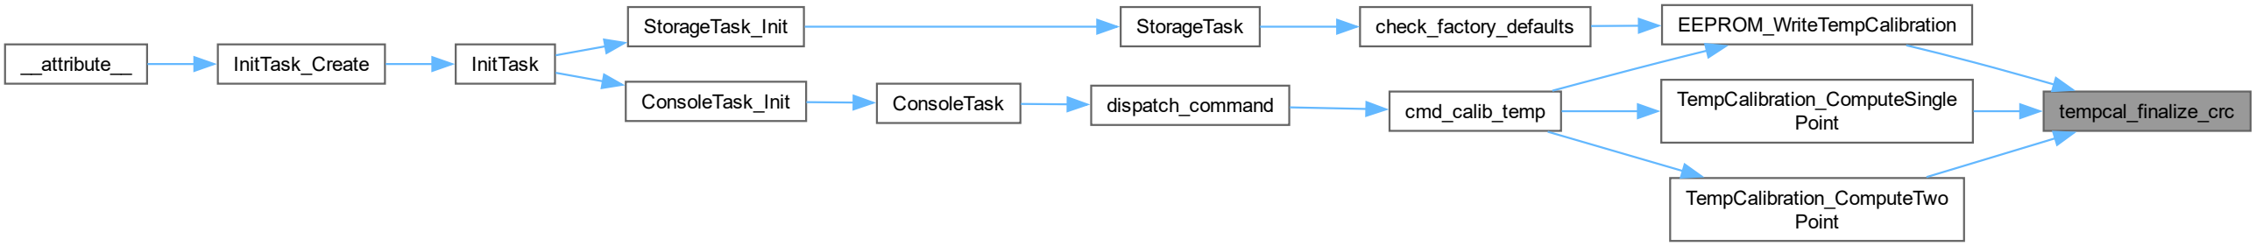
[picture p149: figure]
tempcal_finalize_crc; EEPROM_WriteTempCalibration; TempCalibration_ComputeSingle Point; TempCalibration_ComputeTwo Point; check_factory_defaults; cmd_calib_temp; StorageTask_Init; StorageTask; __attribute__; InitTask_Create; InitTask; ConsoleTask_Init; ConsoleTask; dispatch_command
