DvidMakesThings/HW_10-In-Rack_PDU/docs/doxygen/latex/calibration_8c_ac2a5362a8e4606ad12cb0d6c9941ef6d_icgraph.pdf

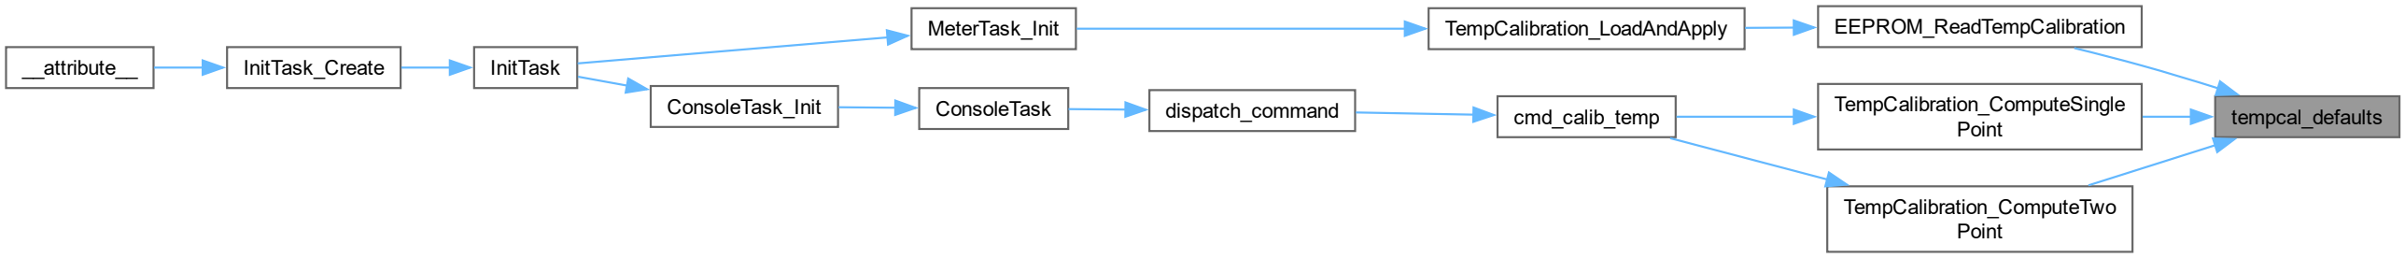
[picture p150: figure]
tempcal_defaults; EEPROM_ReadTempCalibration; TempCalibration_ComputeSingle Point; TempCalibration_ComputeTwo Point; MeterTask_Init; TempCalibration_LoadAndApply; __attribute__; InitTask_Create; InitTask; cmd_calib_temp ConsoleTask_Init; ConsoleTask; dispatch_command
