DvidMakesThings/HW_10-In-Rack_PDU/docs/Compliance_Documents/ENE-TDOC-MIR/ENE-TDOC-MIR-Electrical_Test_Report_PEM-Adapter_1.0.0.pdf

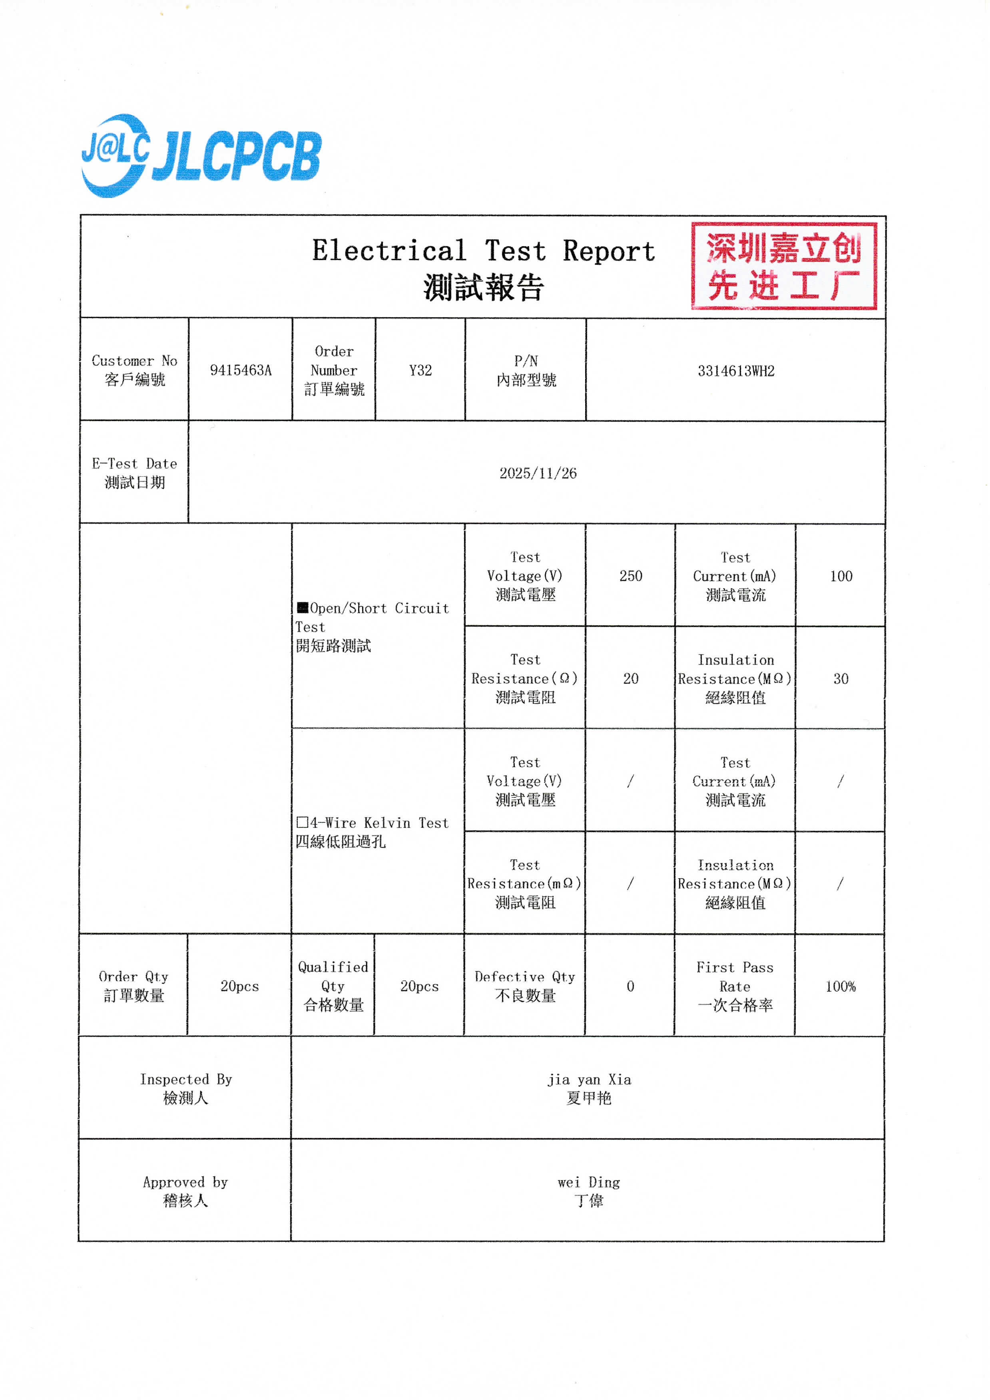
[picture p151: page 1]
