DvidMakesThings/HW_10-In-Rack_PDU/docs/Compliance_Documents/ENE-TDOC-RHSC/ENE-TDOC-RHSC-ROHS_Test_Report_PEM-Adapter_1.0.0.pdf

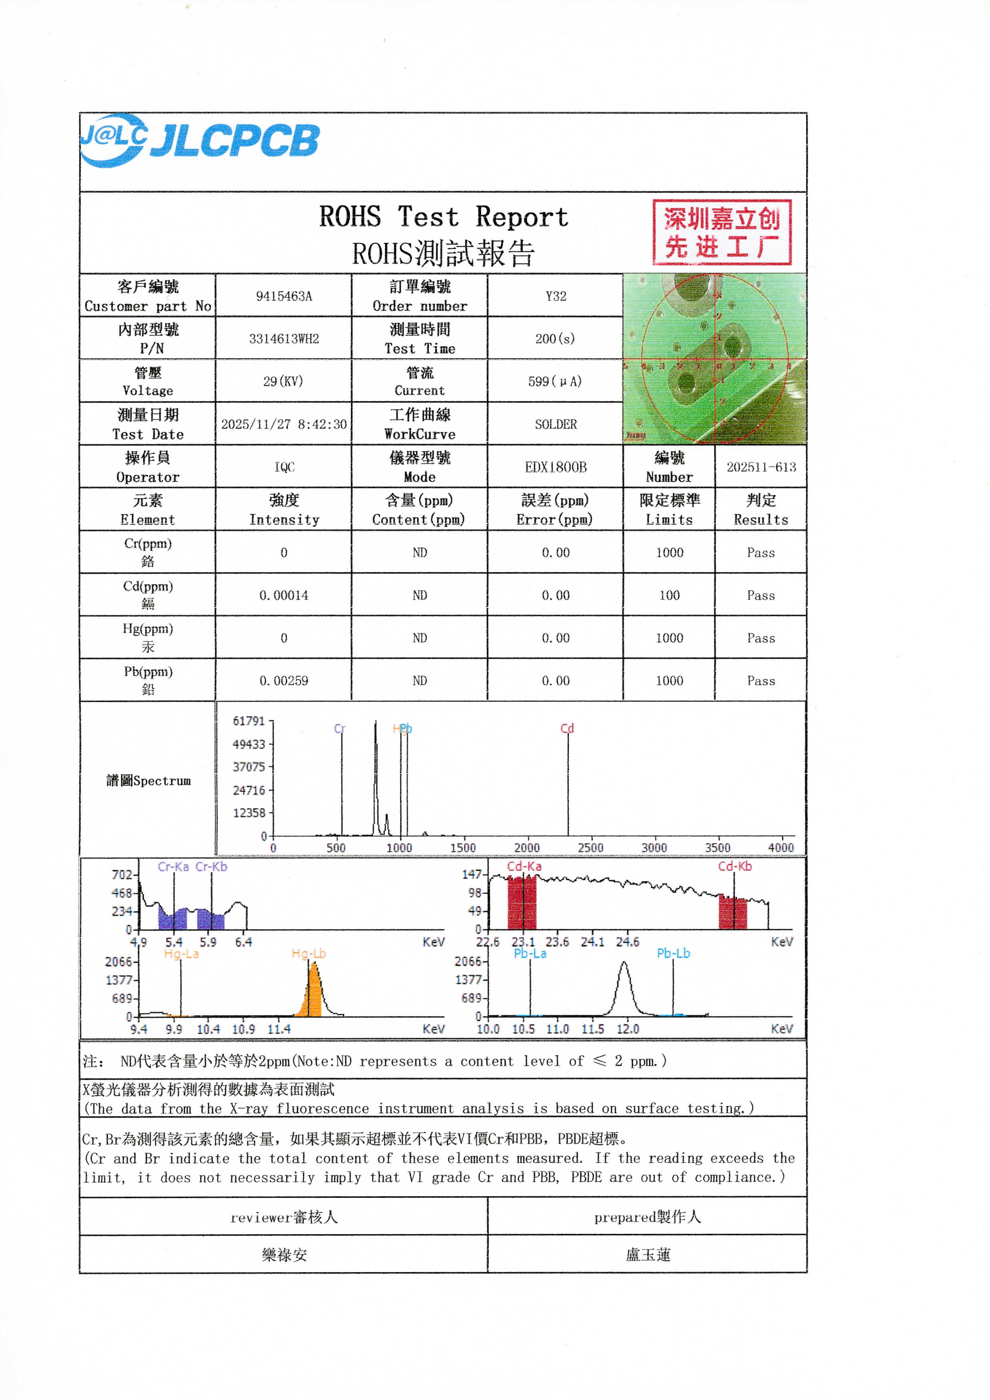
[picture p152: page 1]
