DvidMakesThings/HW_10-In-Rack_PDU/docs/doxygen/latex/calibration_8h__dep__incl.pdf

src/Software/ENERGIS
_RTOS/src/tasks/storage
_submodule/calibration.h

_RTOS/src/CONFIG.h

_RTOS/src/drivers/button

_RTOS/src/drivers/ethernet

_RTOS/src/drivers/snmp.c

_RTOS/src/drivers/socket.c

_RTOS/src/drivers/socket.h

_RTOS/src/misc/EEPROM

_RTOS/src/misc/crashlog.c

_RTOS/src/misc/crashlog.h

_RTOS/src/misc/helpers.c

_RTOS/src/misc/helpers.h

_RTOS/src/tasks/ButtonTask.c

_RTOS/src/tasks/ButtonTask.h

_RTOS/src/tasks/ConsoleTask.c

_RTOS/src/tasks/ConsoleTask.h

_RTOS/src/tasks/HealthTask.c

_RTOS/src/tasks/HealthTask.h

_RTOS/src/tasks/InitTask.c

_RTOS/src/tasks/InitTask.h

_RTOS/src/tasks/LoggerTask.c

_RTOS/src/tasks/LoggerTask.h

_RTOS/src/tasks/MeterTask.c

_RTOS/src/snmp/snmp_powerMon.c
