DvidMakesThings/HW_10-In-Rack_PDU/docs/doxygen/latex/calibration_8h__incl.pdf

src/Software/ENERGIS
_RTOS/src/tasks/storage
_submodule/calibration.h
