DvidMakesThings/HW_10-In-Rack_PDU/docs/Compliance_Documents/ENE-TDOC-Schematics/ENE-TDOC-Schematics-Main-Board-1.1.0-Schematic-Documentation.pdf

Author | David Sipos
Document number: | ENE-TDOC-Schematics-100
Document name: | ENE-TDOC-Schematics-100-Main-Board-1.1.0- Schematic-Documentation
Revision: | 1.0.0
Status: | Released
Date: | 14.12.2025
Document status: | Internal - CE Technical File

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

# ENERGIS 10IN Managed PDU

# Main Board 1.1.0 Schematic Documentation

# Revision History

A revision is a new edition of the document and affects all sections of this document.

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

# Contents

# 1. Introduction

# This document provides general technical information related to the electrical schematics used within the ENERGIS 10-inch managed PDU system. It applies to all schematic diagrams

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

# 1.1 Purpose

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

# context of the schematic diagrams. It does not describe firmware behaviour in detail and

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

# This document is applicable to the schematic versions identified in the corresponding design documentation and engineering outputs. Any future revisions may require an update

or extension of this document where relevant.

# 2. General Information

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

implemented in accordance with the product design and enclosure specifications.

# The schematics are developed using standard electronic design principles and documented using industry-standard EDA tools. Component selection and circuit topology are based on performance requirements, availability, and compliance with applicable regulatory

standards, including RoHS where applicable. All circuits are intended for indoor use within

# controlled environmental conditions as specified in the product documentation. The

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

# Detailed design data, including schematics, PCB layouts, manufacturing outputs, and

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

# 3. ENERGIS_MainBoard_1.1.0 Schematics

# RP2040 MICROCONTROLLER

A

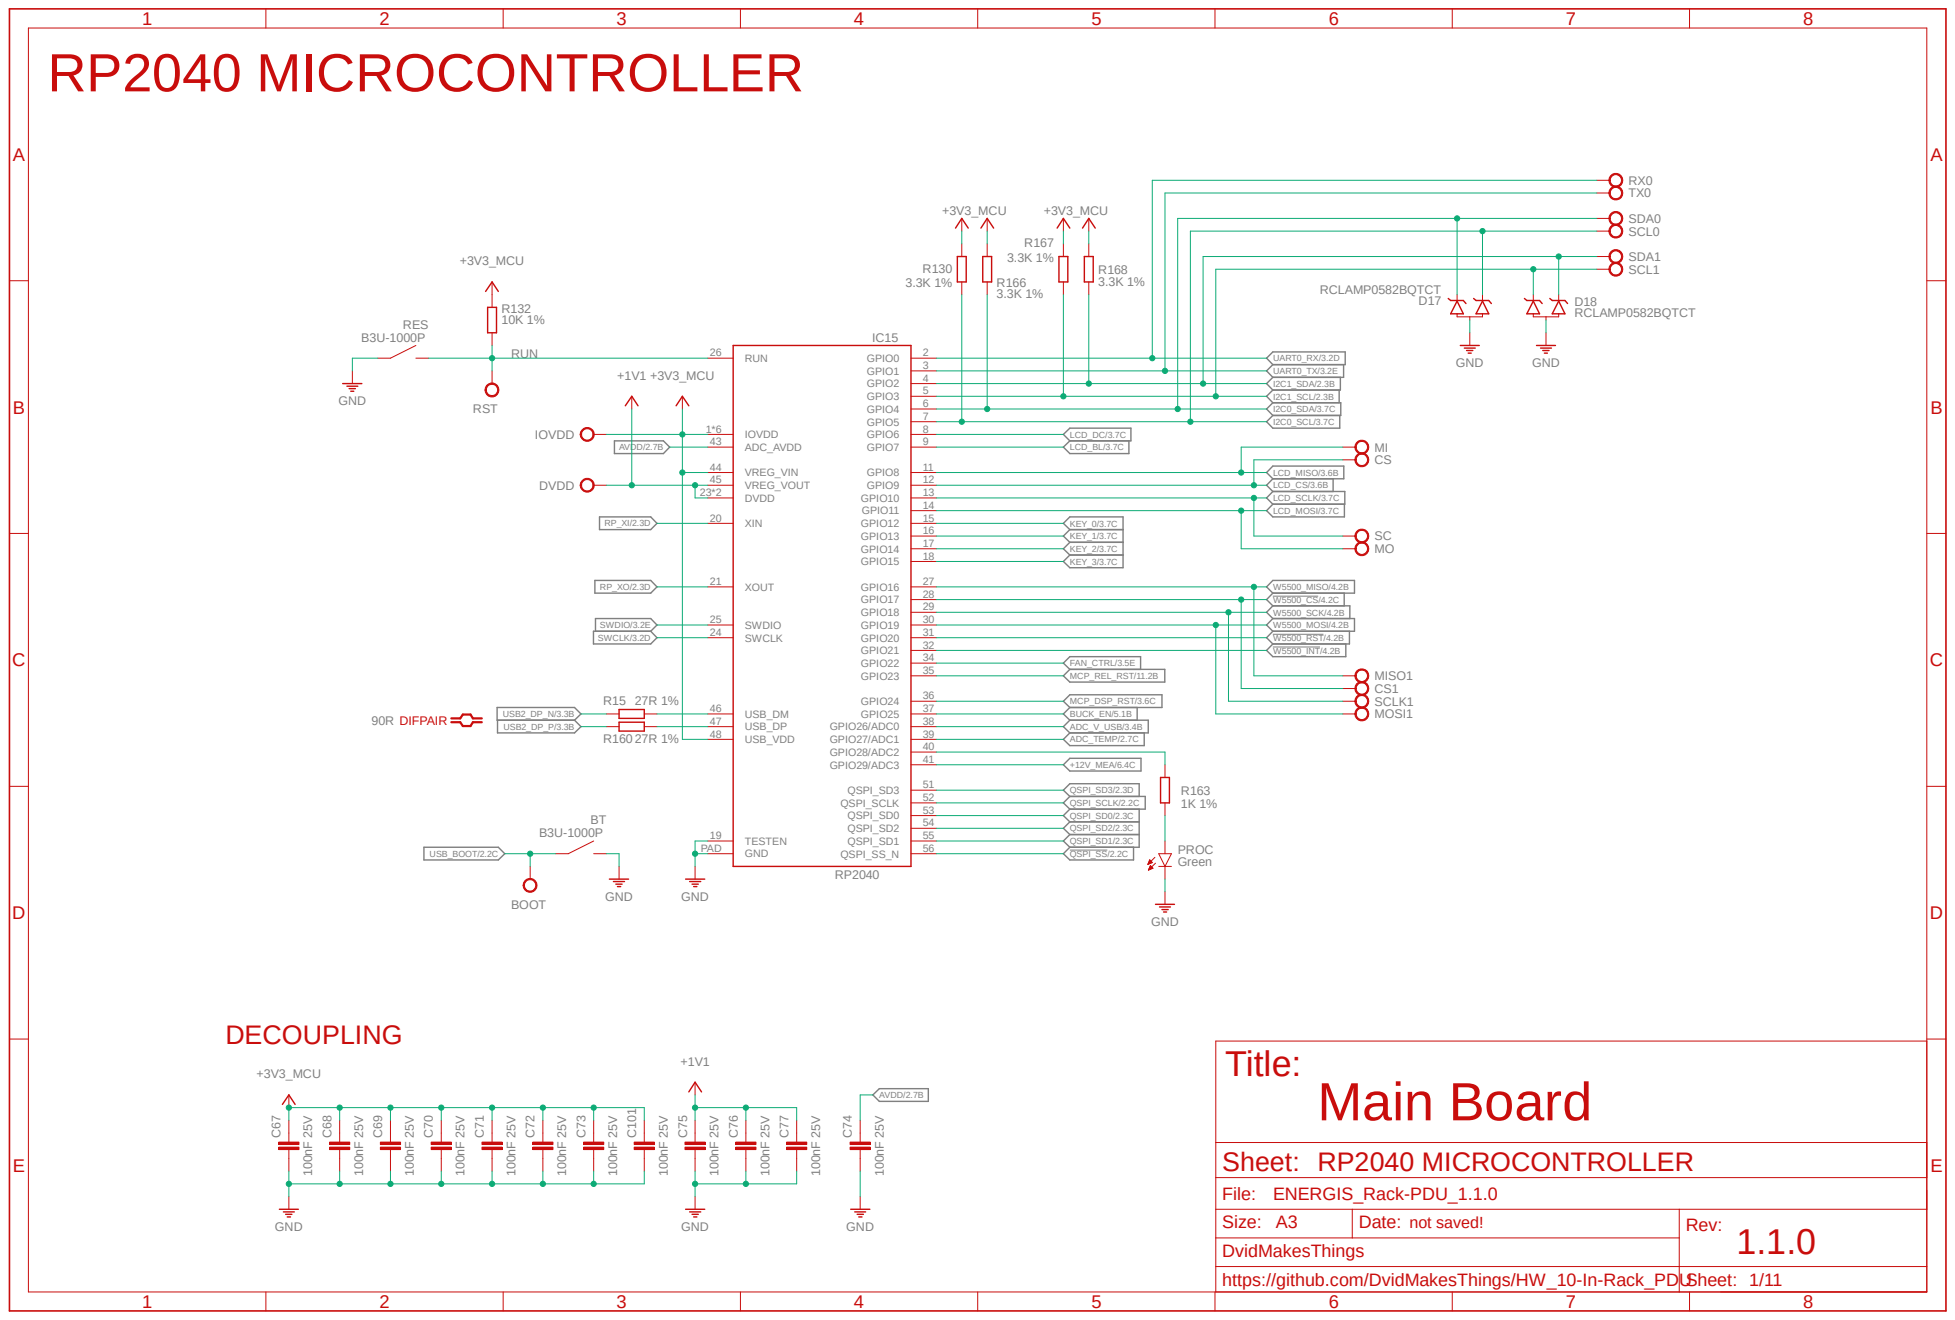
[picture p153: page 5]

https://github.com/DvidMakesThings/HW_10-In-Rack_PDU

USER MEMORY | ADC VREF

# PERIPHERALS

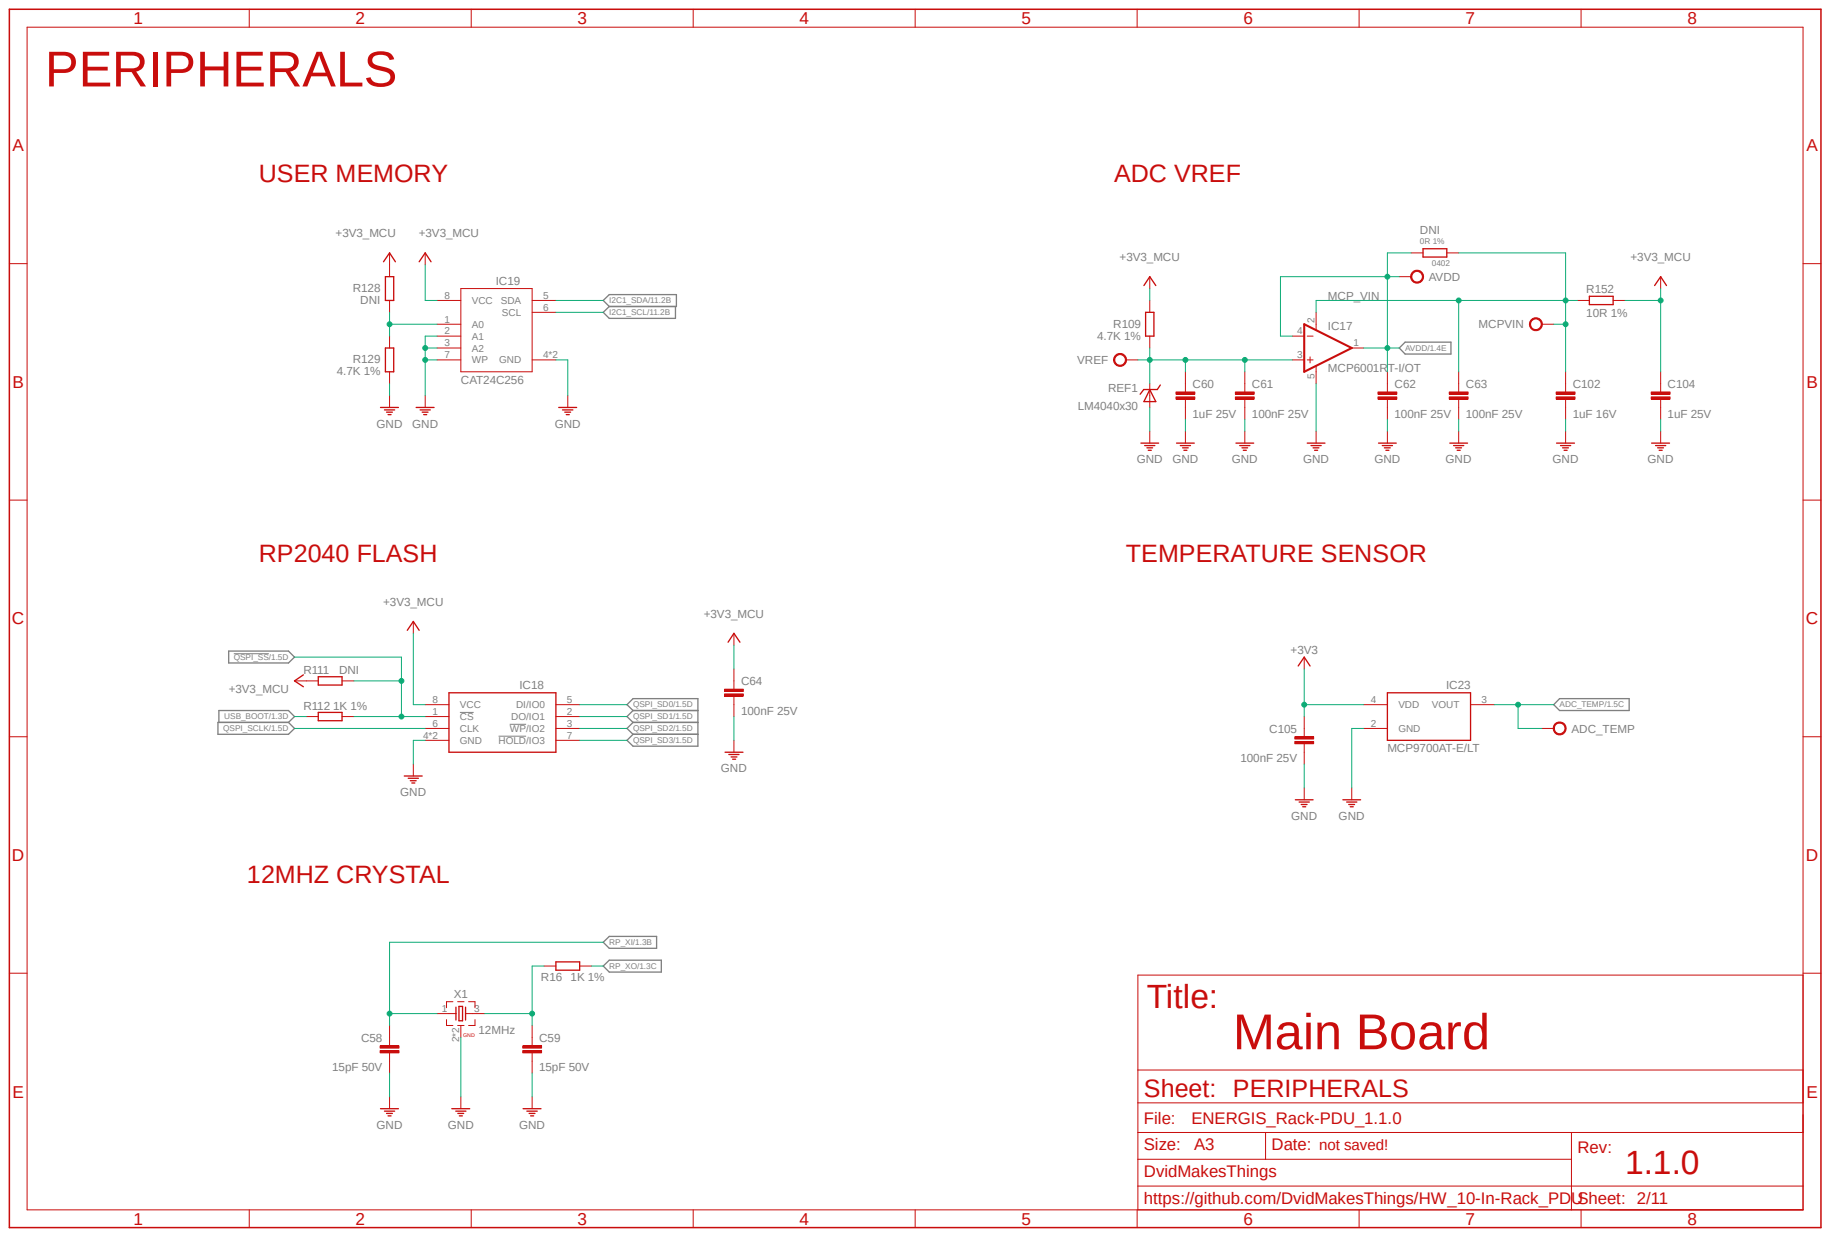
[picture p154: page 6]

# USB-C CONNECTOR

# BOARD CONNECTOR

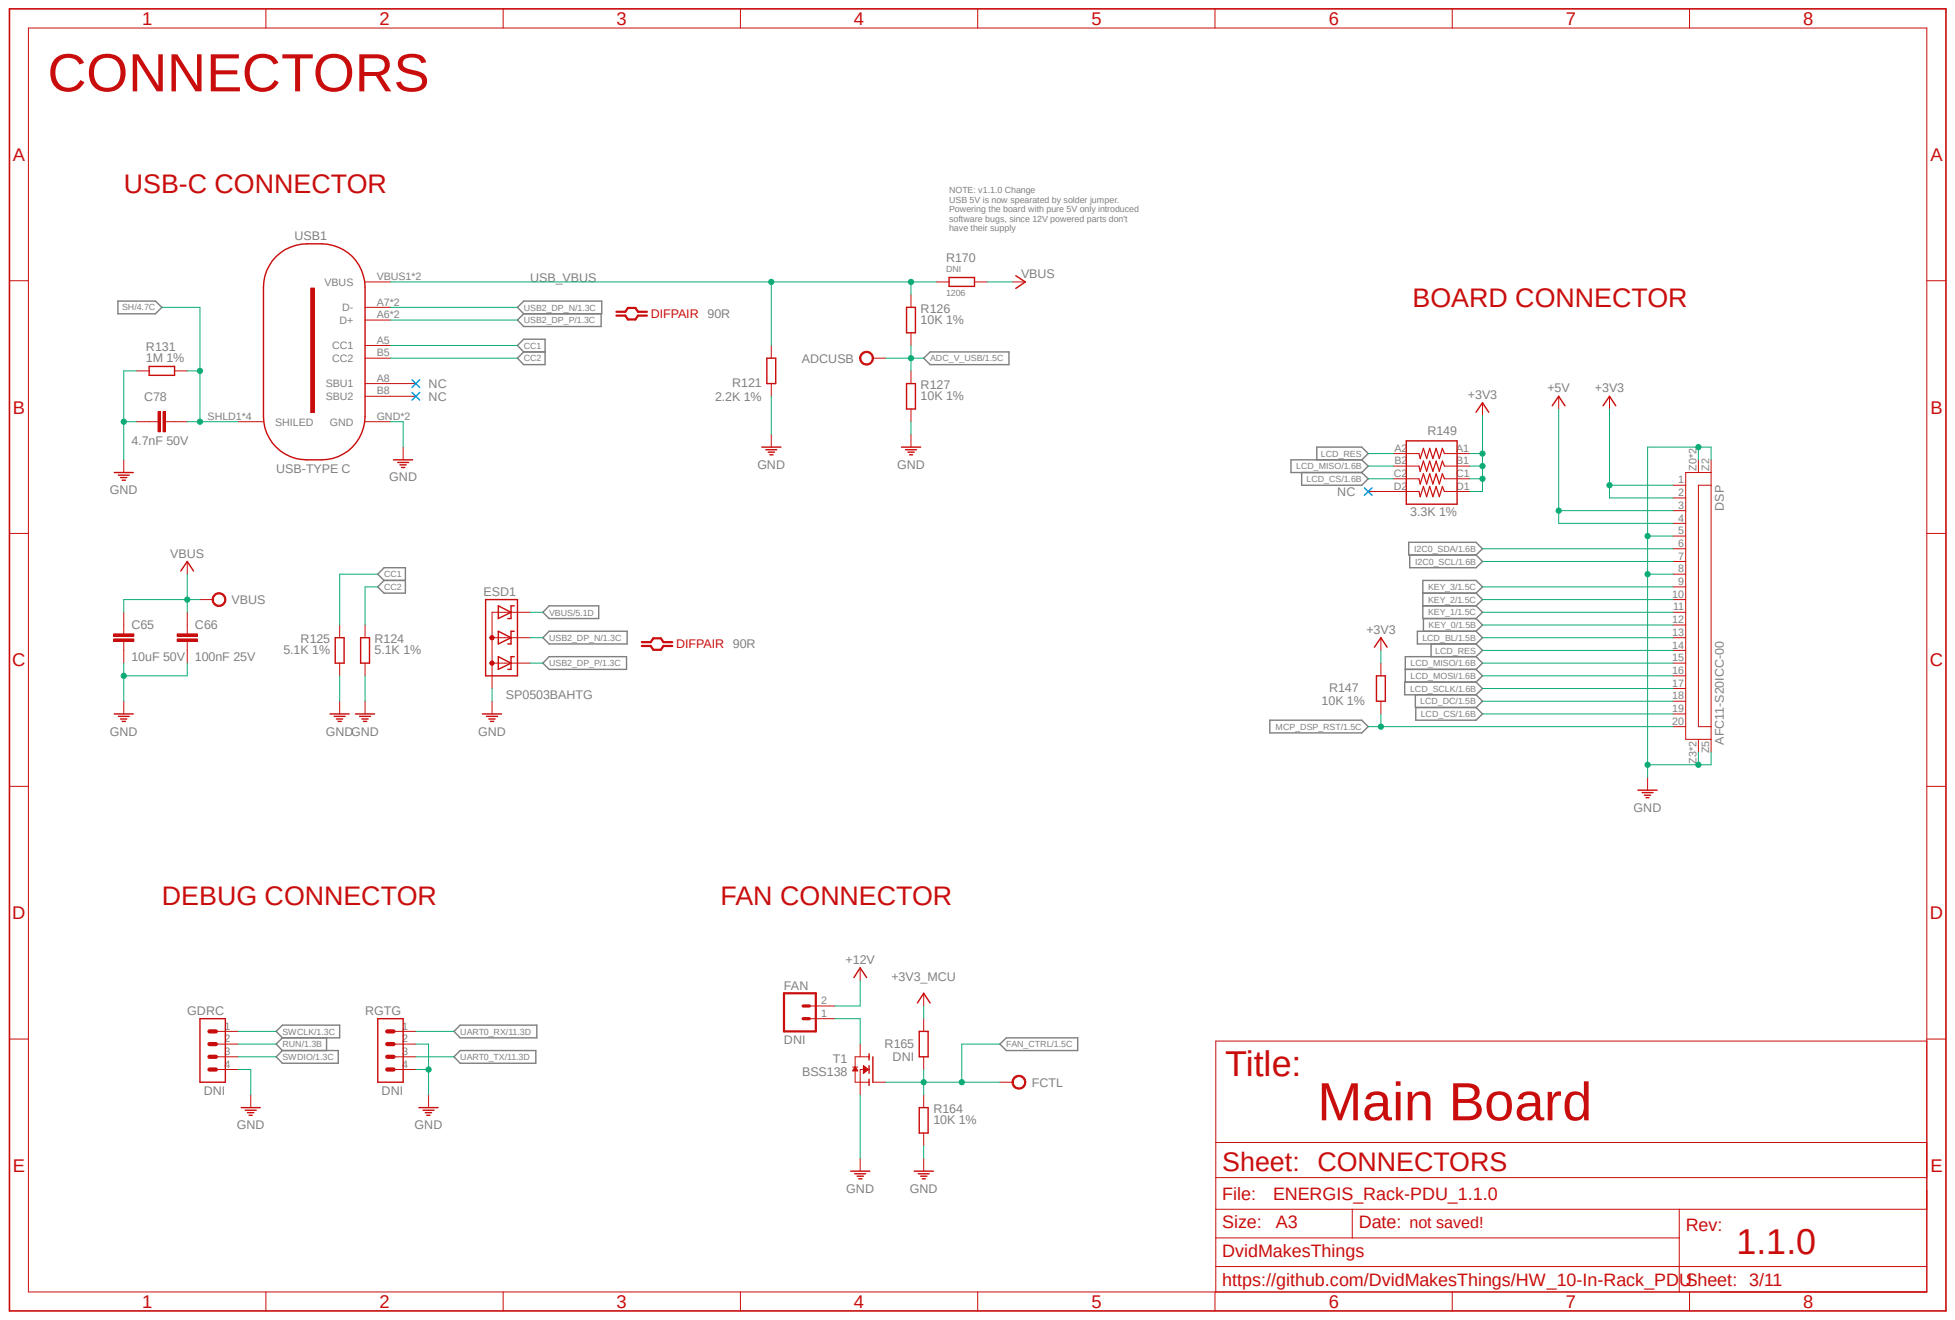
[picture p155: page 7]

NOTE: v1.1.0 Change
USB 5V is now spearated by solder jumper.
Powering the board with pure 5V only introduced
software bugs, since 12V powered parts don't
have their supply

# W5500 ETHERNET CONTROLLER

A

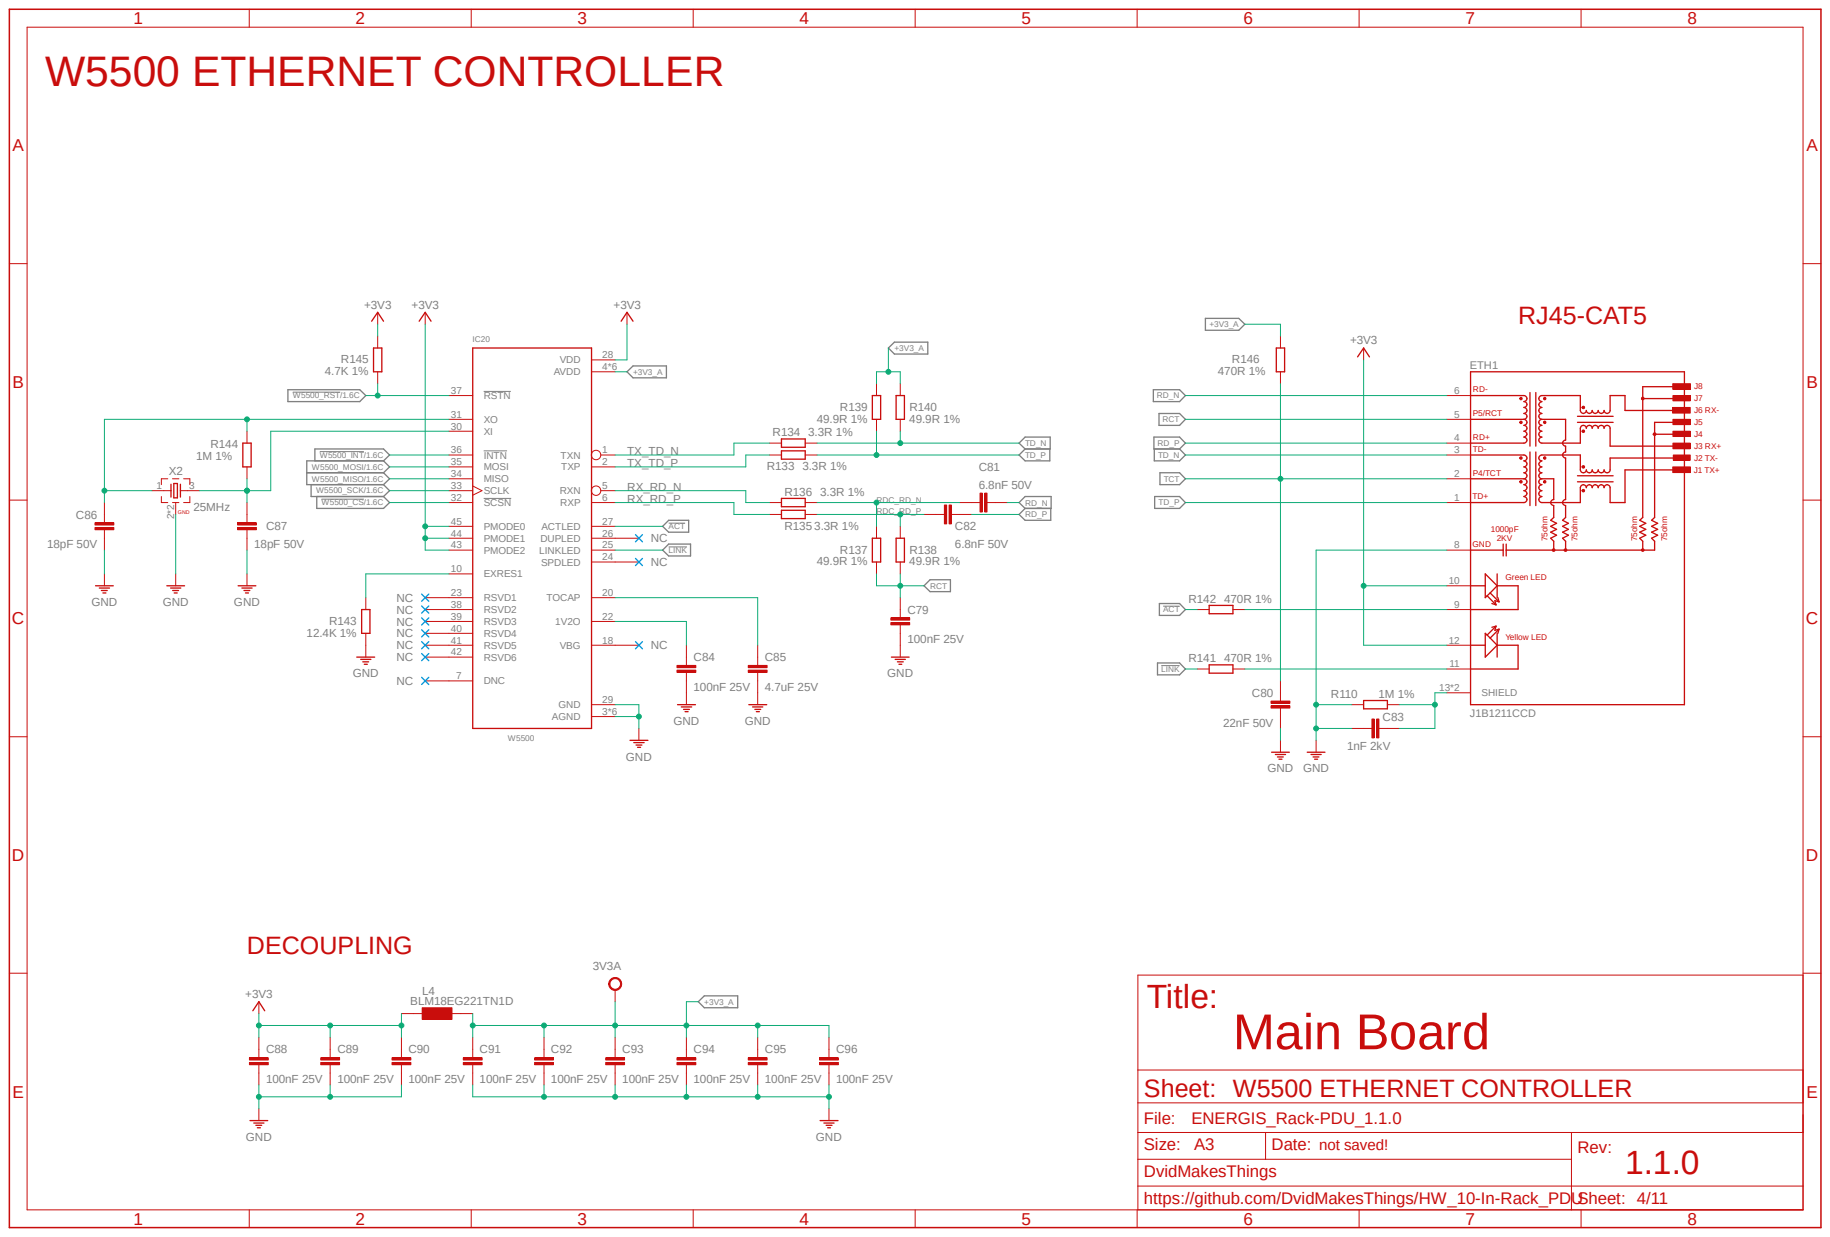
[picture p156: page 8]

# 5V DC-DC CONVERTER

# 230VAC

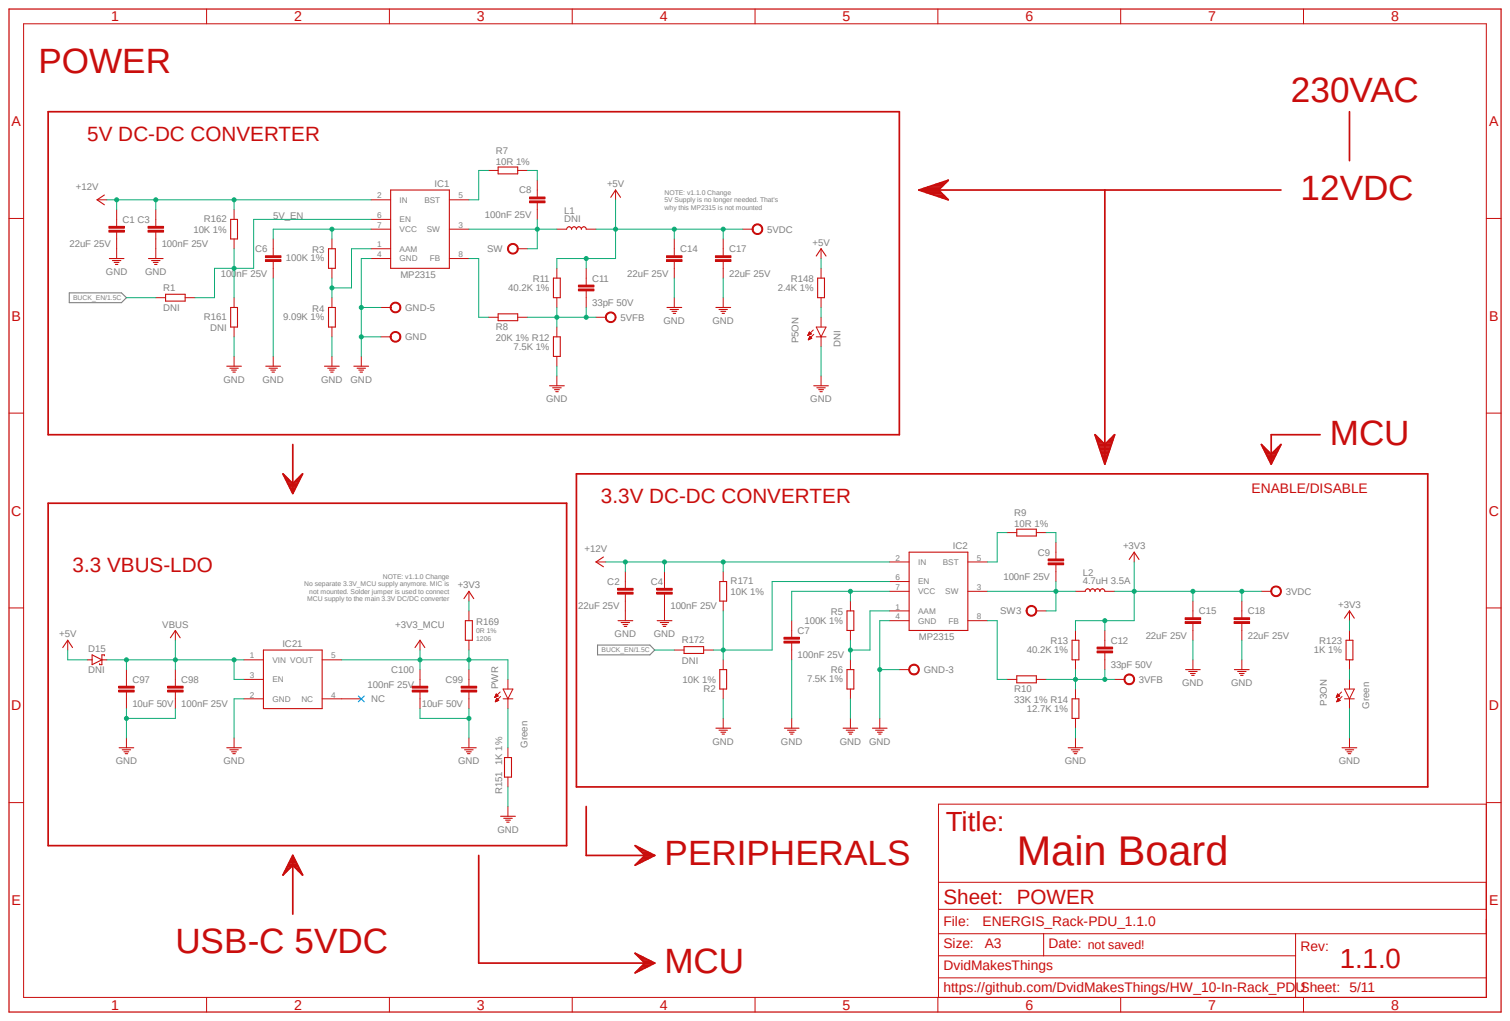
[picture p157: page 9]

NOTE: v1.1.0 Change
5V Supply is no longer needed. That's
why this MP2315 is not mounted

No separate 3.3V_MCU supply anymore. MIC is
not mounted. Solder jumper is used to connect
MCU supply to the main 3.3V DC/DC converter

# AC-POWER

# 5V 200MA NON-ISOLATED POWER SUPPLY

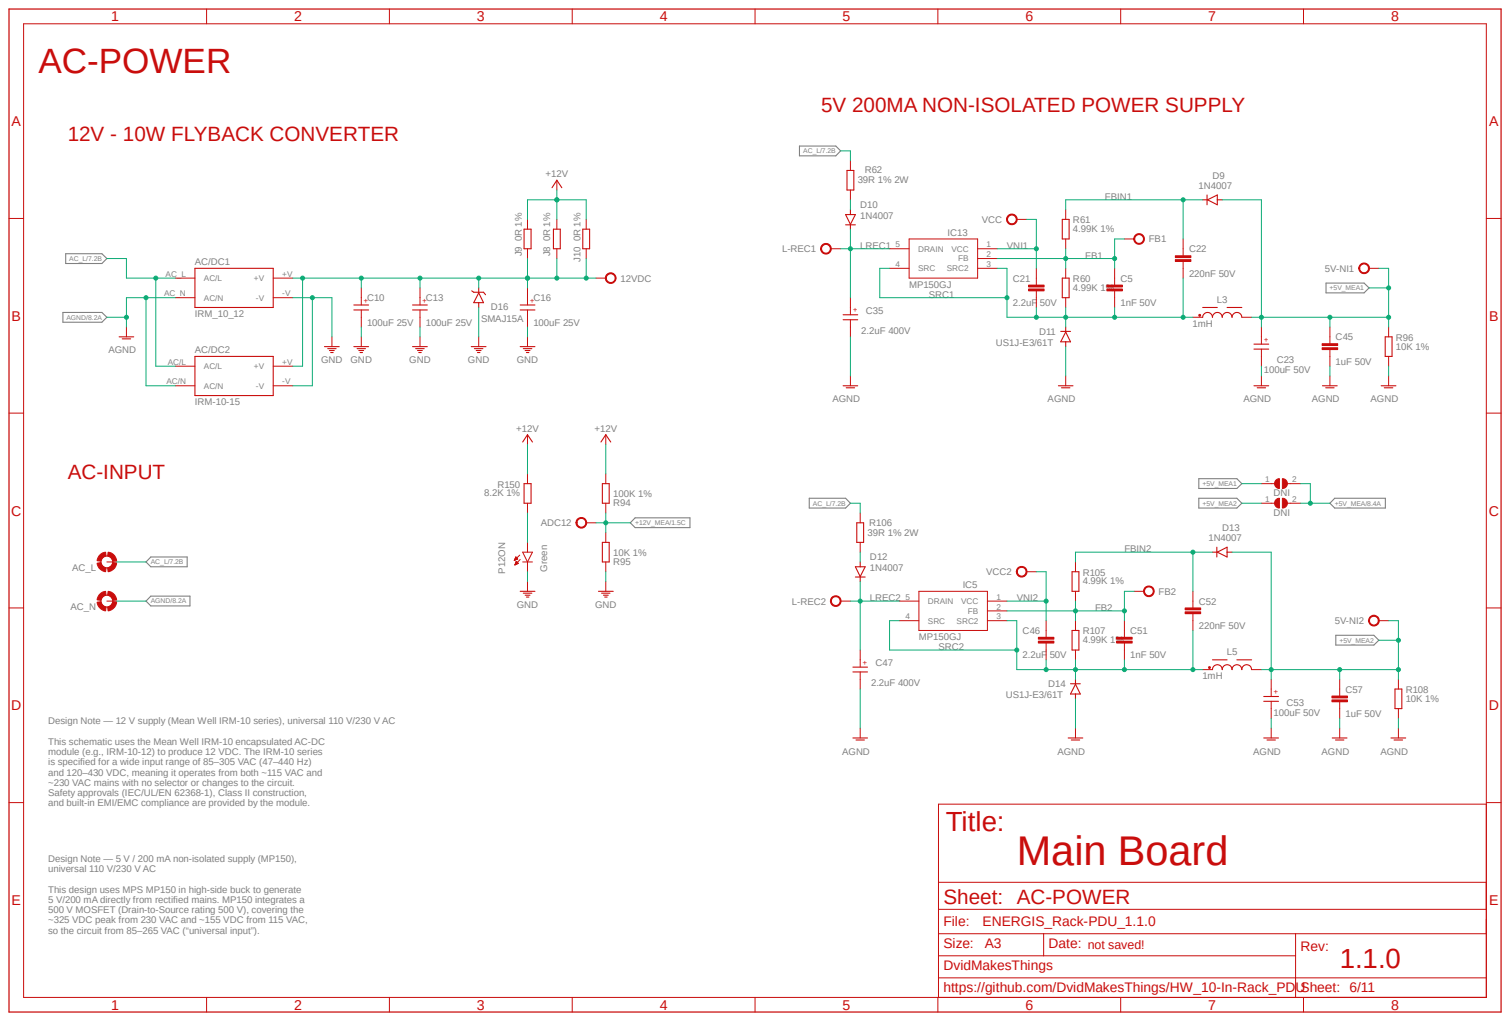
[picture p158: page 10]

Design Note — 12 V supply (Mean Well IRM-10 series), universal 110 V/230 V AC
This schematic uses the Mean Well IRM-10 encapsulated AC-DC
module (e.g., IRM-10-12) to produce 12 VDC. The IRM-10 series
is specified for a wide input range of 85–305 VAC (47–440 Hz)
and 120–430 VDC, meaning it operates from both ~115 VAC and
~230 VAC mains with no selector or changes to the circuit.
Safety approvals (IEC/UL/EN 62368-1), Class II construction,
and built-in EMI/EMC compliance are provided by the module.

Design Note — 5 V / 200 mA non-isolated supply (MP150),
universal 110 V/230 V AC
This design uses MPS MP150 in high-side buck to generate

5 V/200 mA directly from rectified mains. MP150 integrates a
500 V MOSFET (Drain-to-Source rating 500 V), covering the
~325 VDC peak from 230 VAC and ~155 VDC from 115 VAC,
so the circuit from 85–265 VAC (“universal input”).

# OUTPUT RELAYS

A

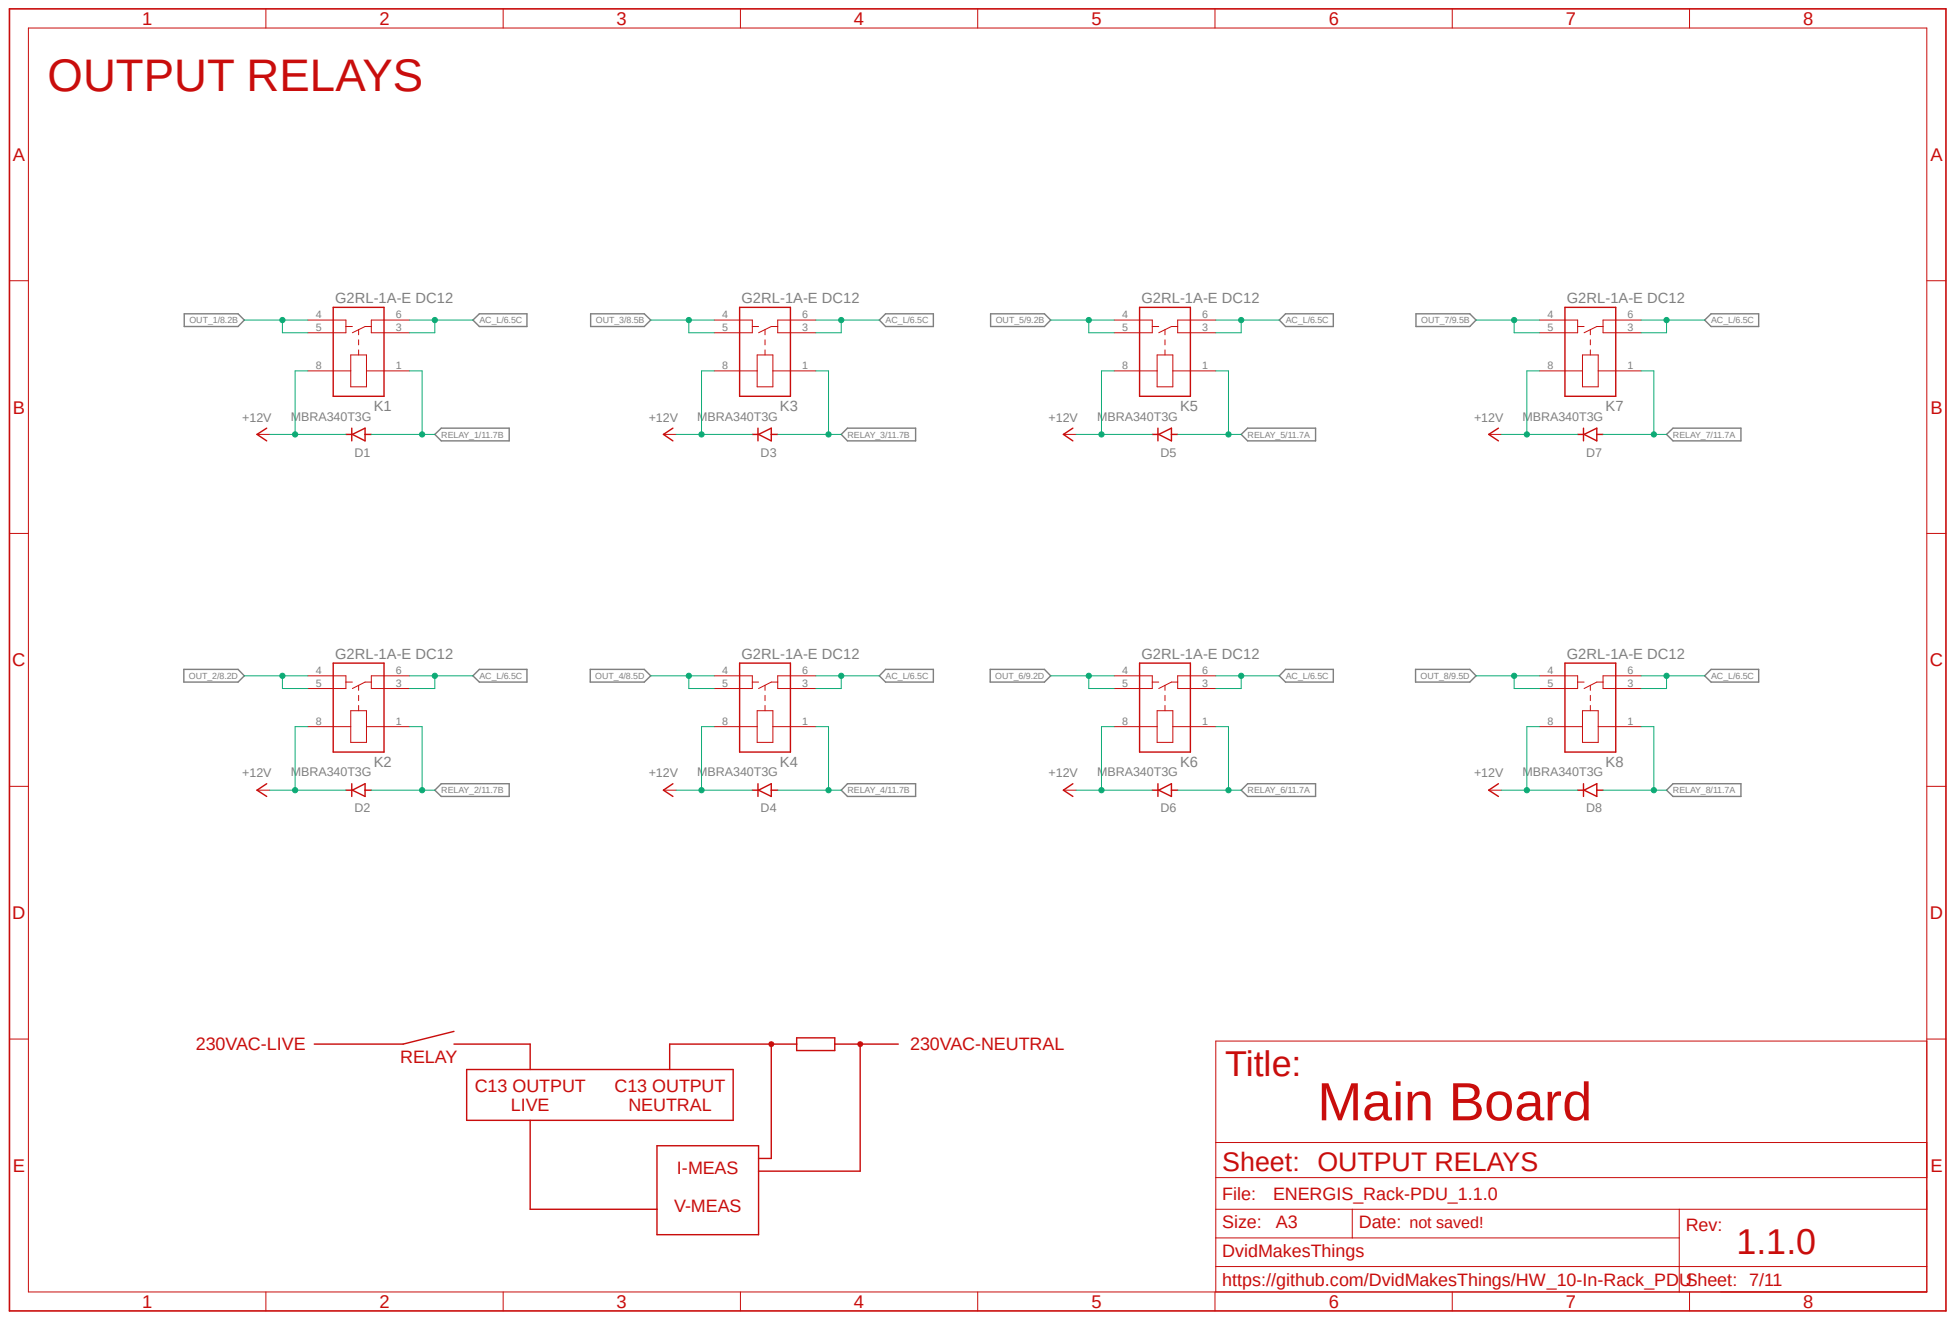
[picture p159: page 11]

AC CHANNEL MEASUREMENT I.

FROM DEVICE > | 2x 0.002R= 0.001R

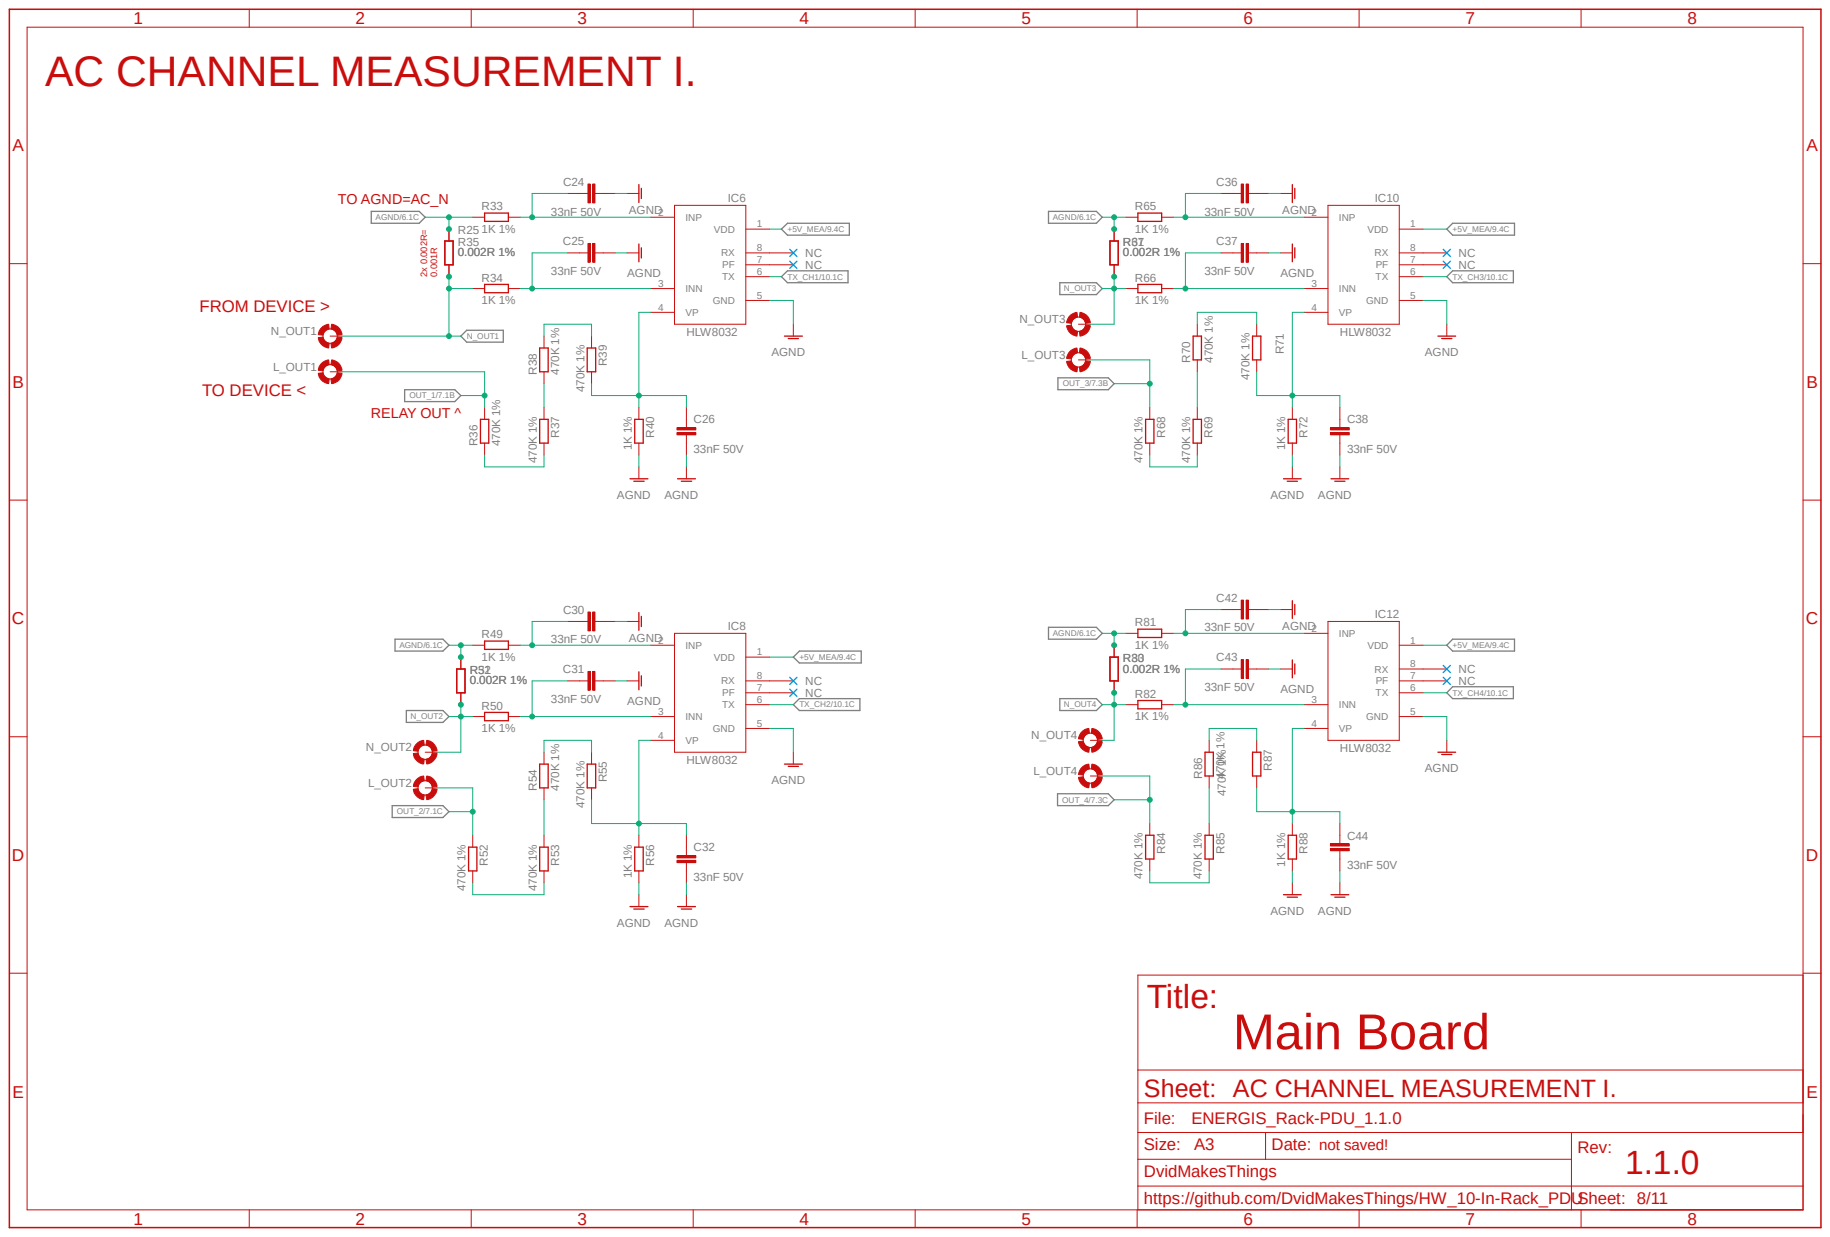
[picture p160: page 12]

AC CHANNEL MEASUREMENT II.

A

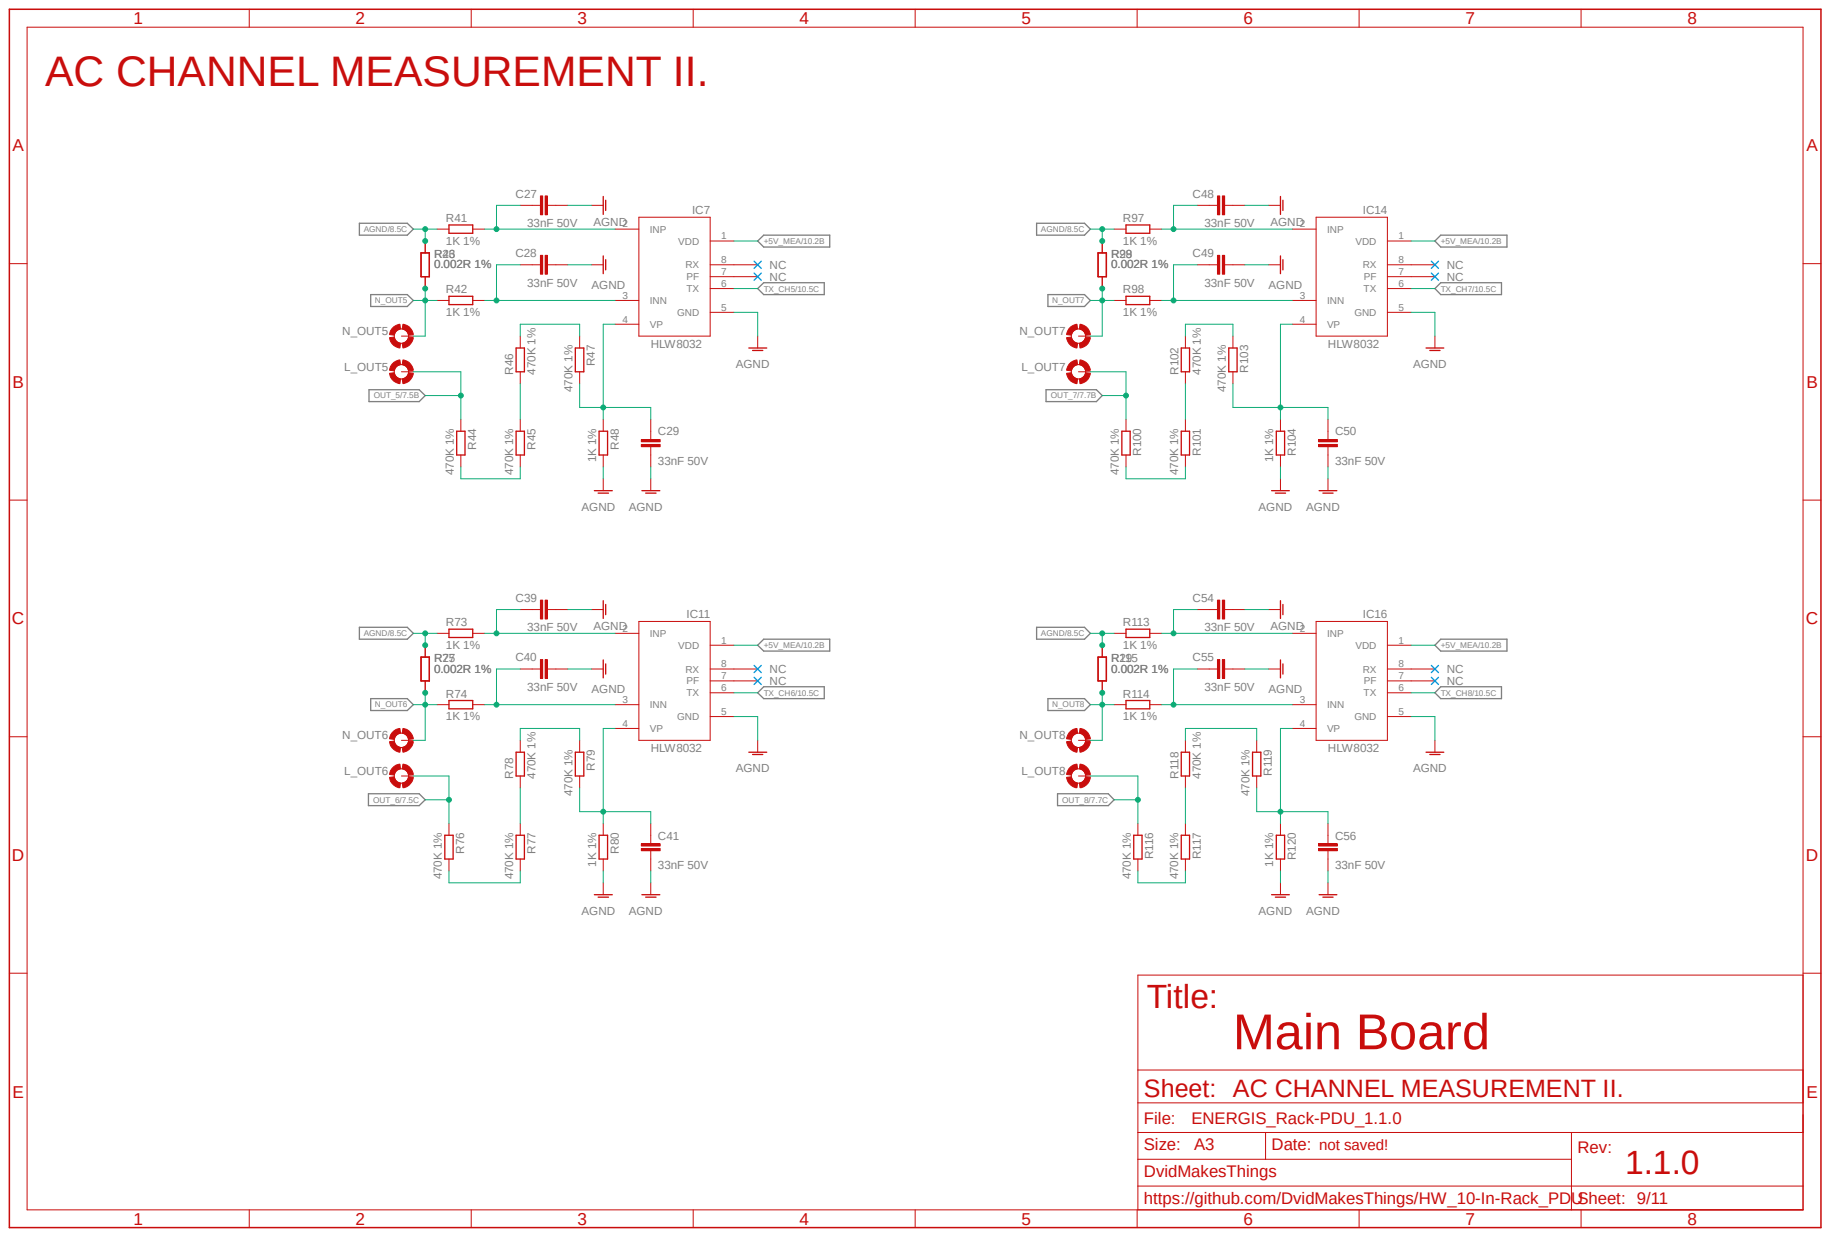
[picture p161: page 13]

AC CHANNEL MEASUREMENT II.
ENERGIS_Rack-PDU_1.1.0

# SERIAL OPTOISOLATOR

A

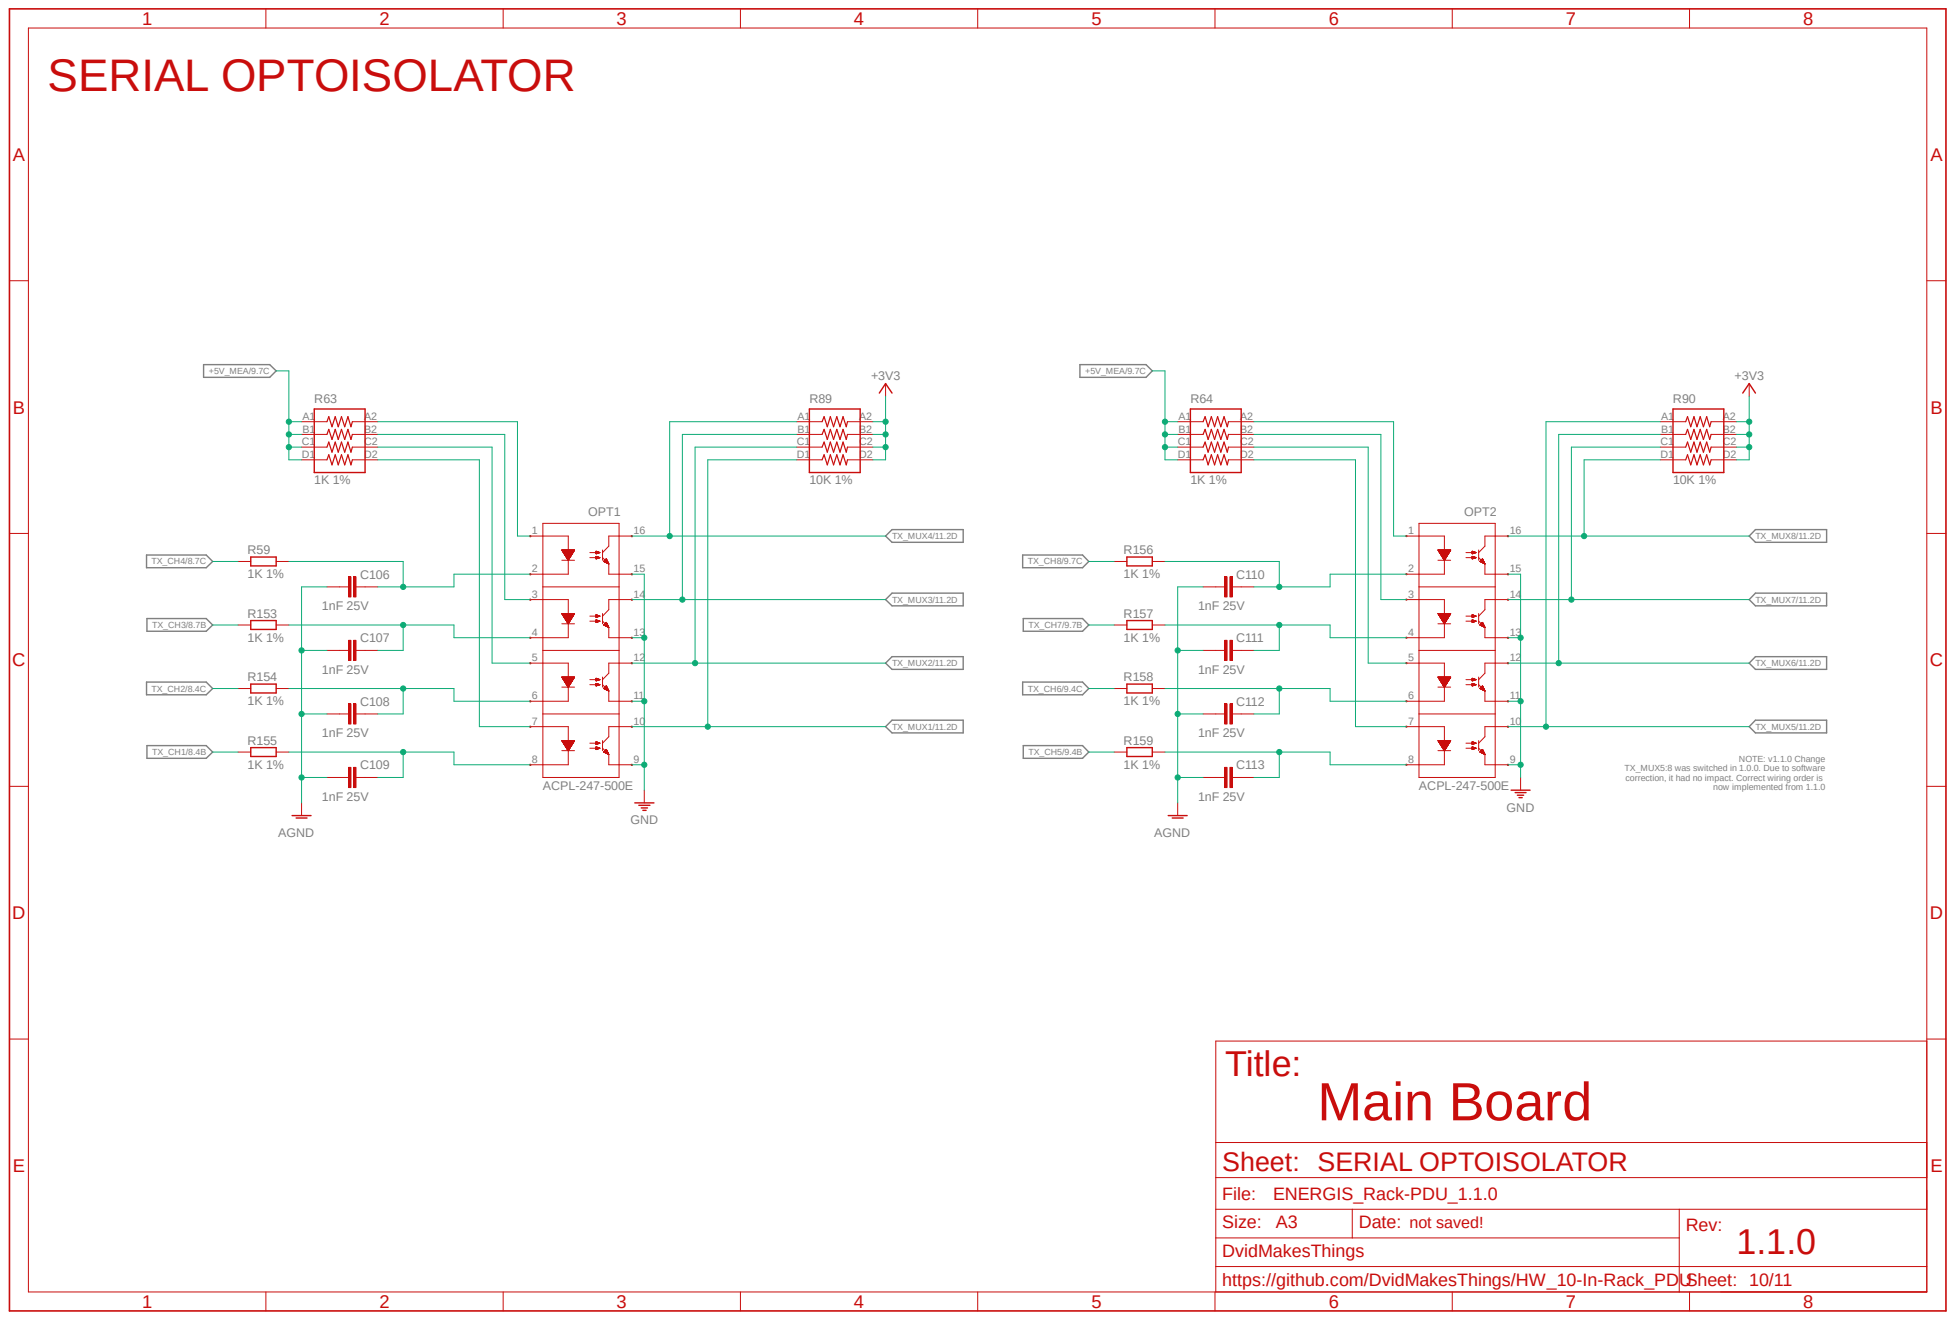
[picture p162: page 14]

TX_MUX5:8 was switched in 1.0.0. Due to software

VDD 5 | VSS 6*2
REL7 RN¹A | RN²A

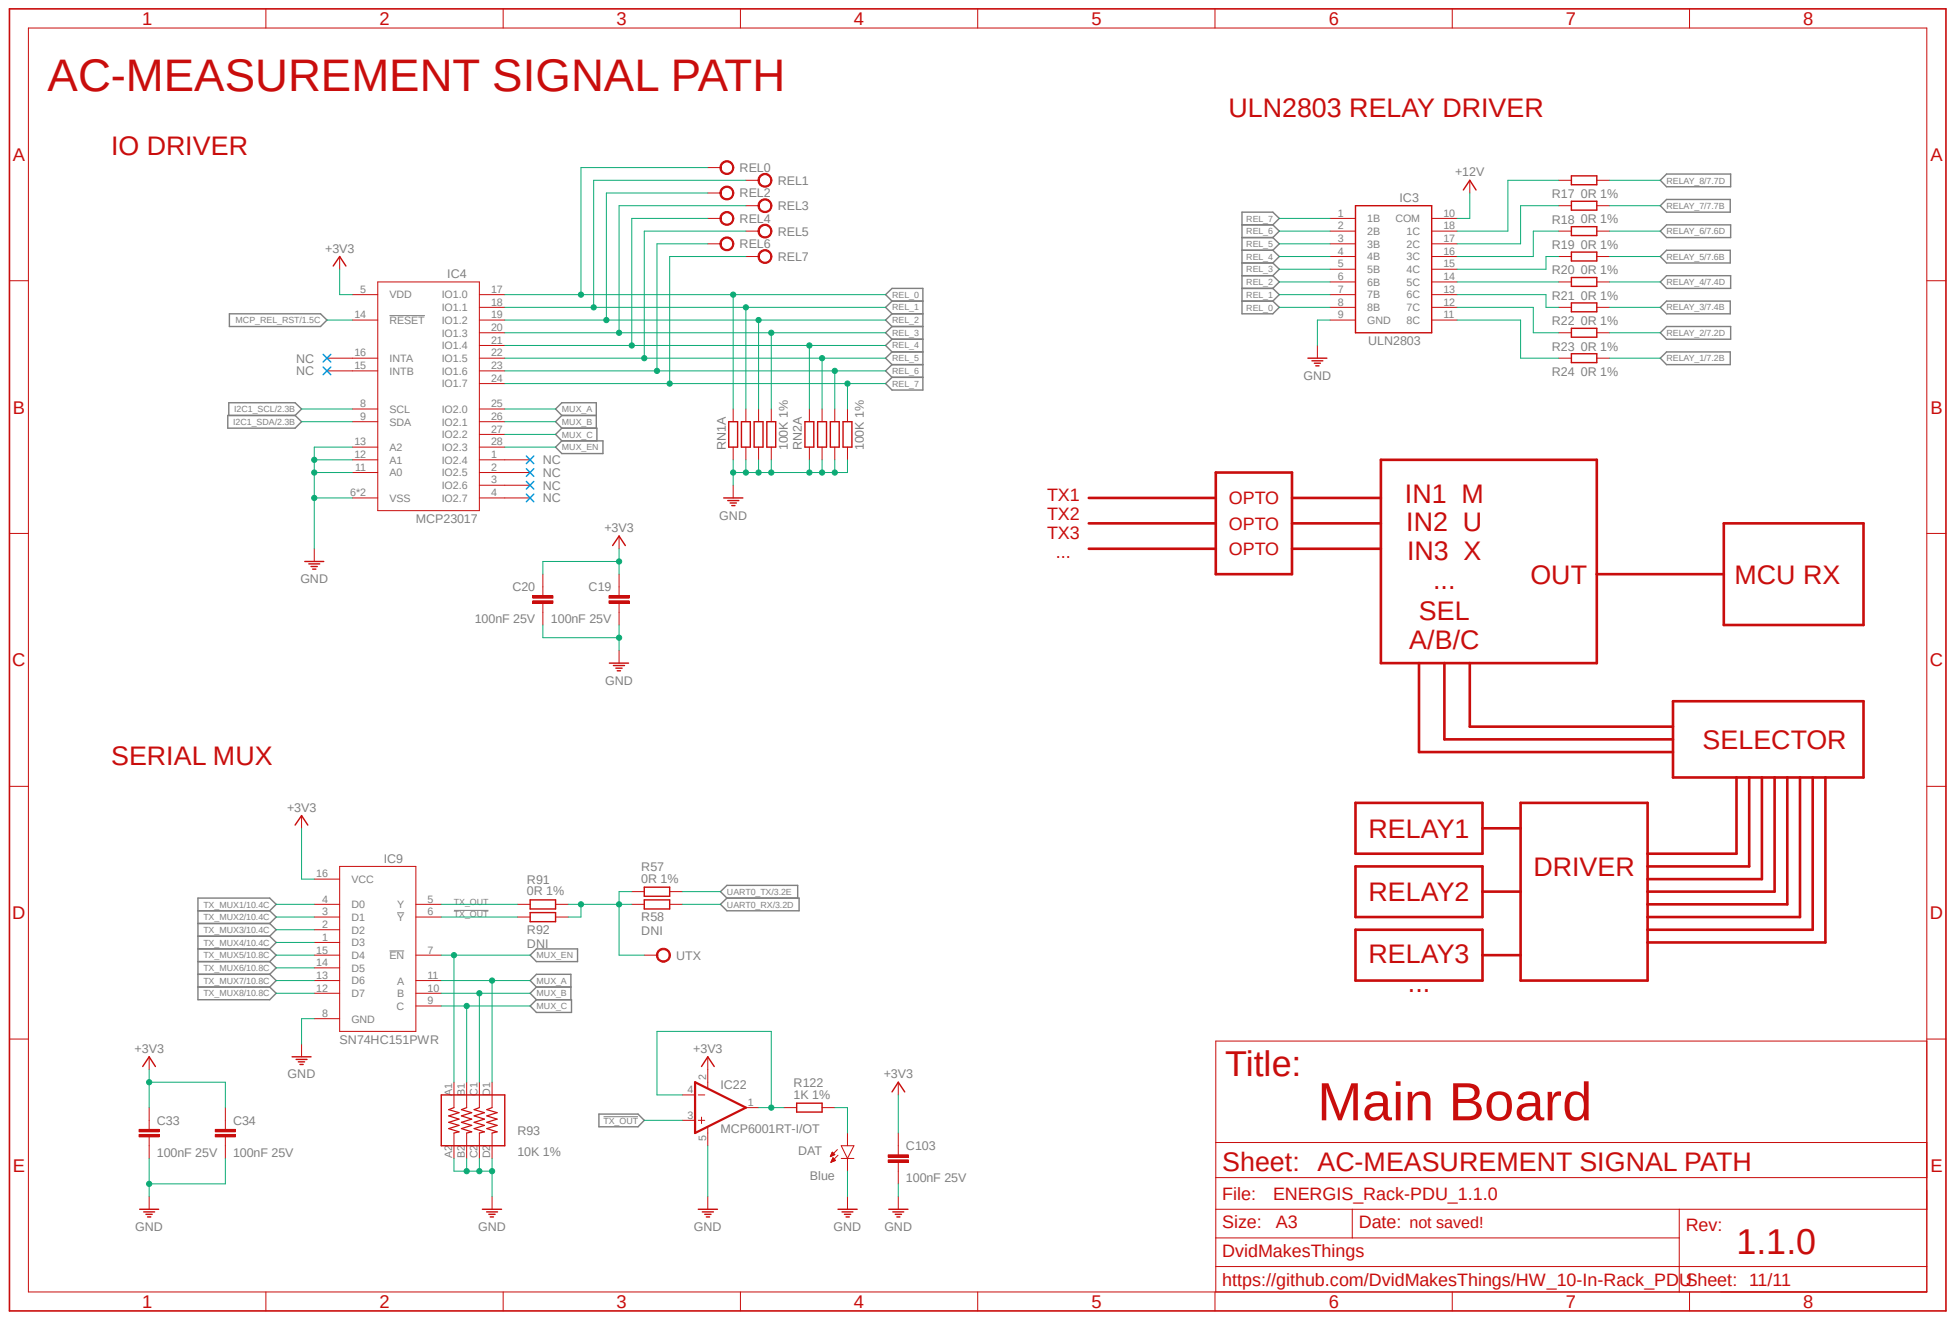
[picture p163: page 15]

AC-MEASUREMENT SIGNAL PATH

10

ENERGIS_Rack-PDU_1.1.0
