DvidMakesThings/HW_10-In-Rack_PDU/src/Enclosure-Design/Shielding/DisplayBoard_Shielding.pdf

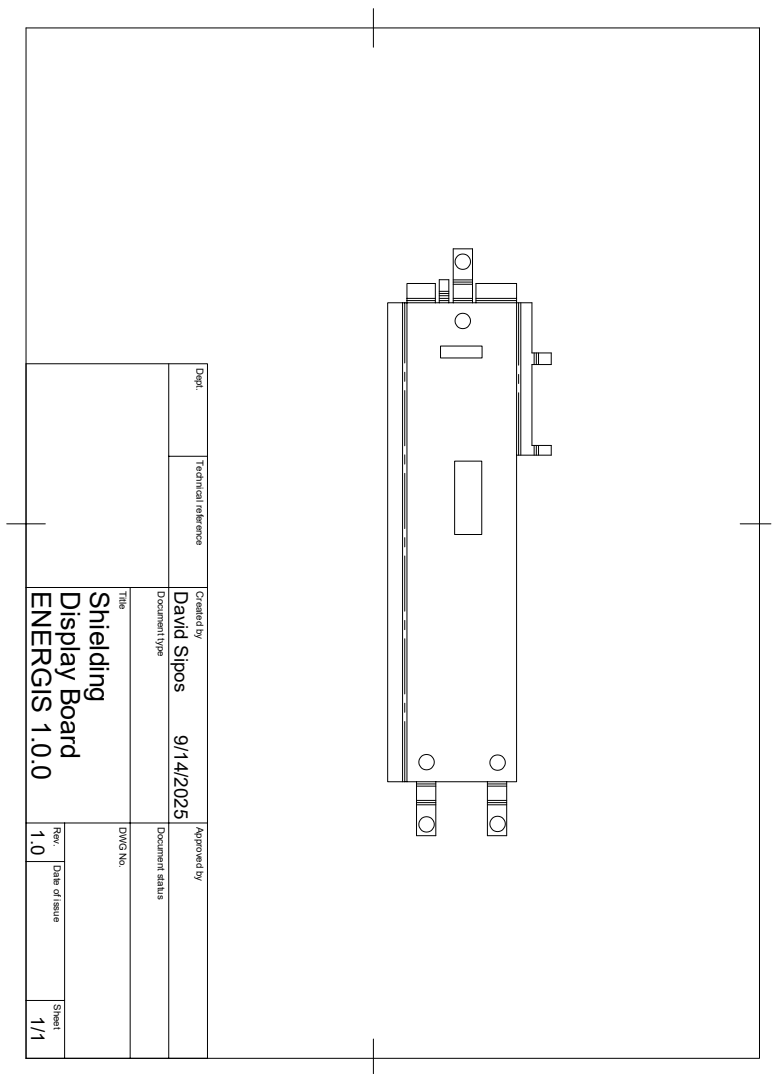
[picture p164: page 1]

Dept. Technical reference Created by Approved by Title DWG No. Document type Document status 1.0 Rev. Date of issue Sheet ENERGIS 1.0.0 9/14/2025 1/1 Display Board Shielding David Sipos
