DvidMakesThings/HW_10-In-Rack_PDU/src/Enclosure-Design/Shielding/MainBoard_Shielding.pdf

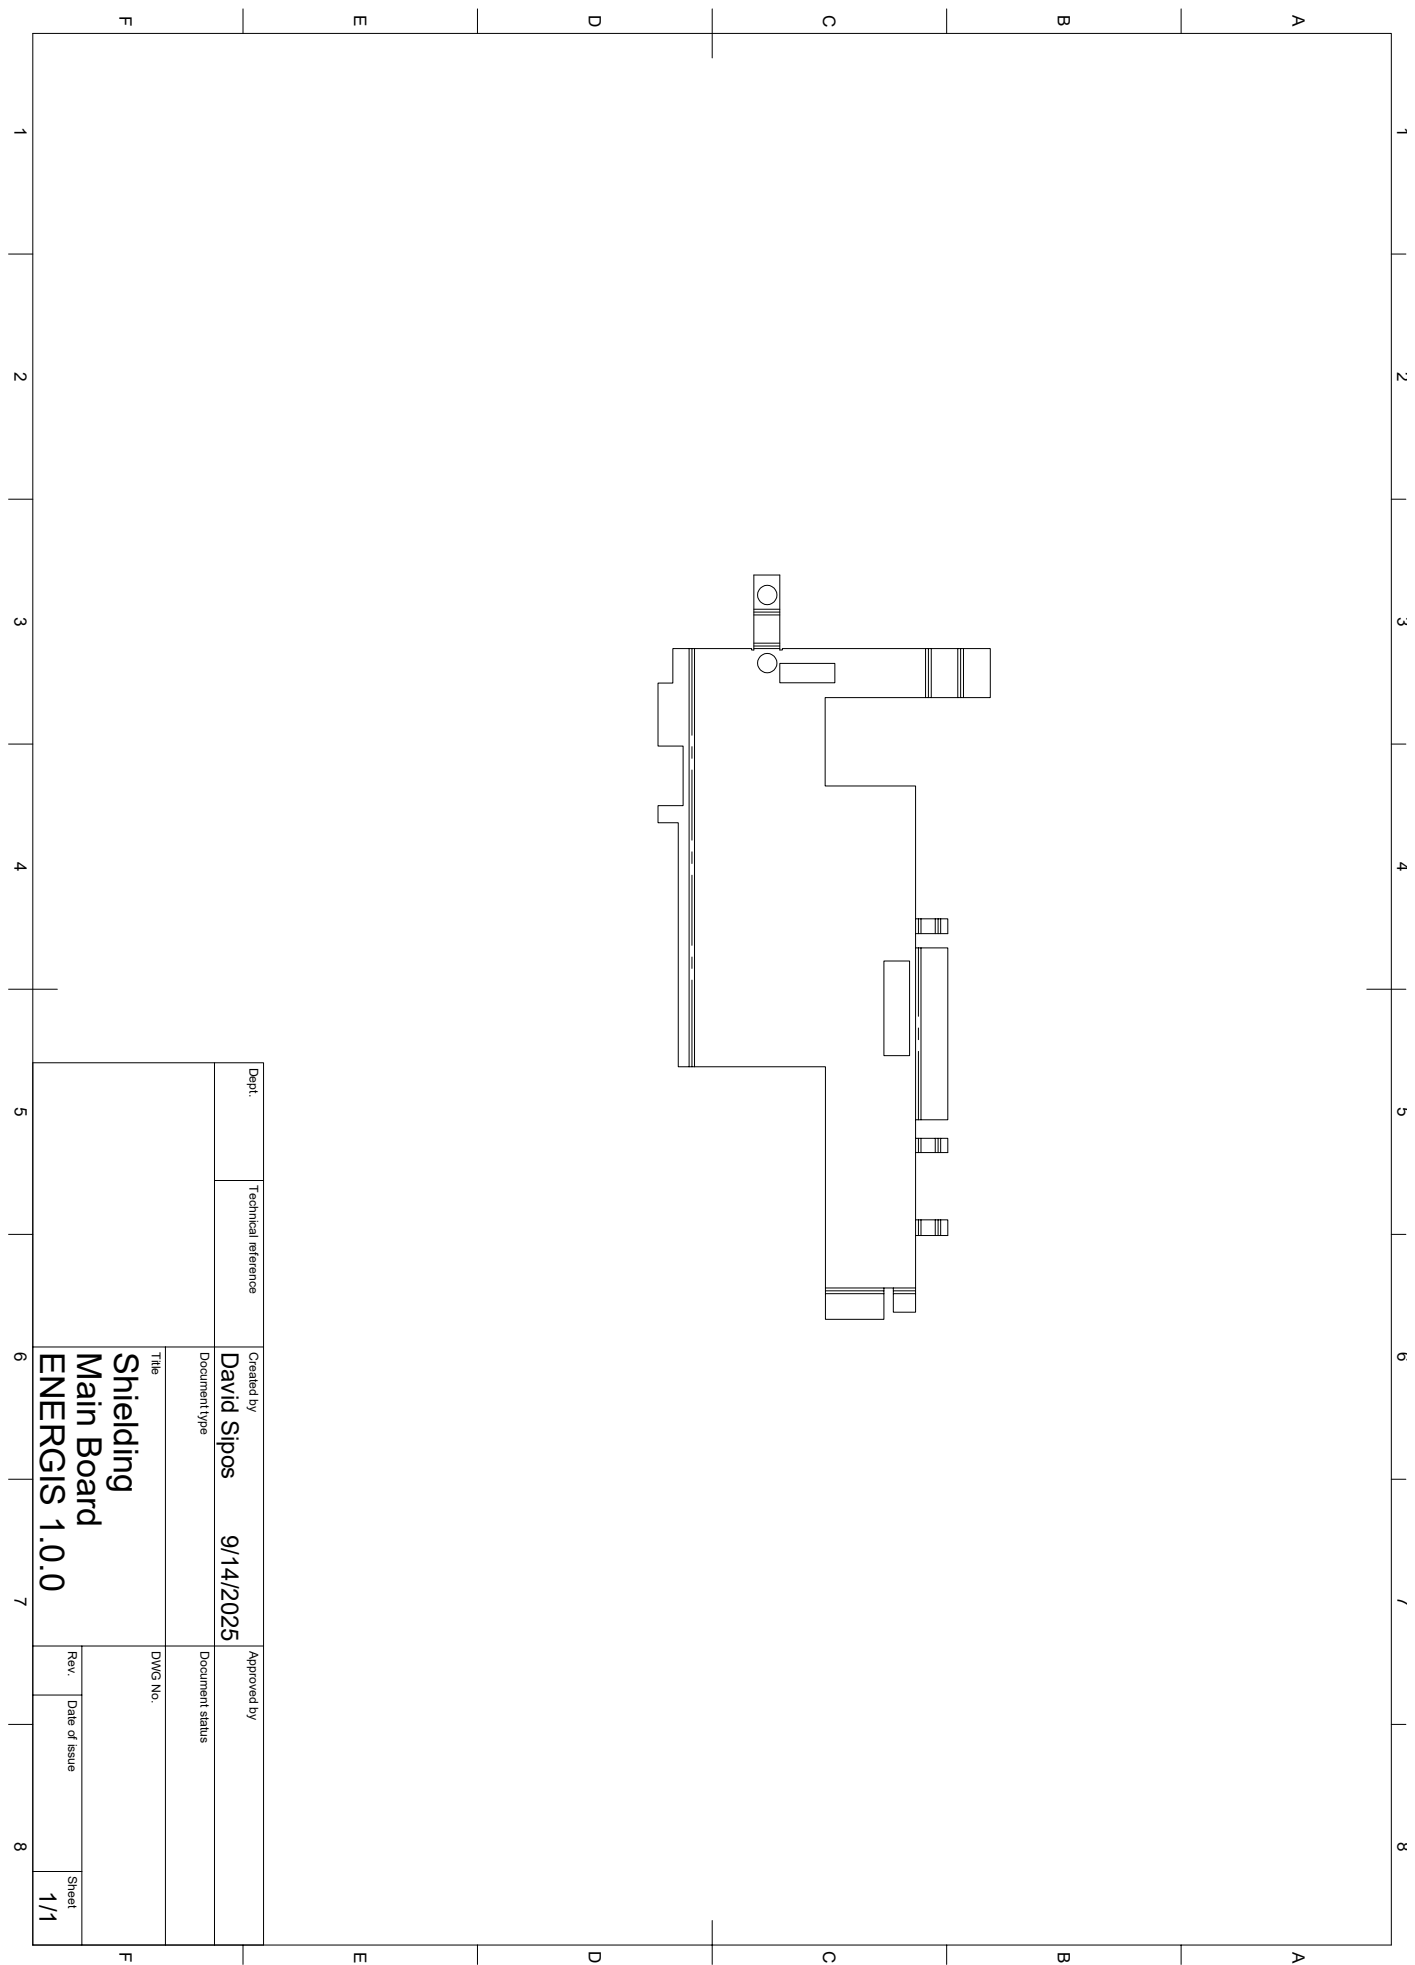
[picture p165: page 1]

1 A 2 3 4 5 6 7 8 1 2 3 4 5 6 7 8 FEDCB FEDCBA Dept. Technical reference Created by Approved by Title DWG No. Document type Document status Rev. Date of issue Sheet ENERGIS 1.0.0 9/14/2025 1/1 Main Board Shielding David Sipos
