DvidMakesThings/HW_10-In-Rack_PDU/src/Enclosure-Design/SheetMetal/Bottom_Enclosure/Energis-Enclosure-Bottom-Holes.pdf

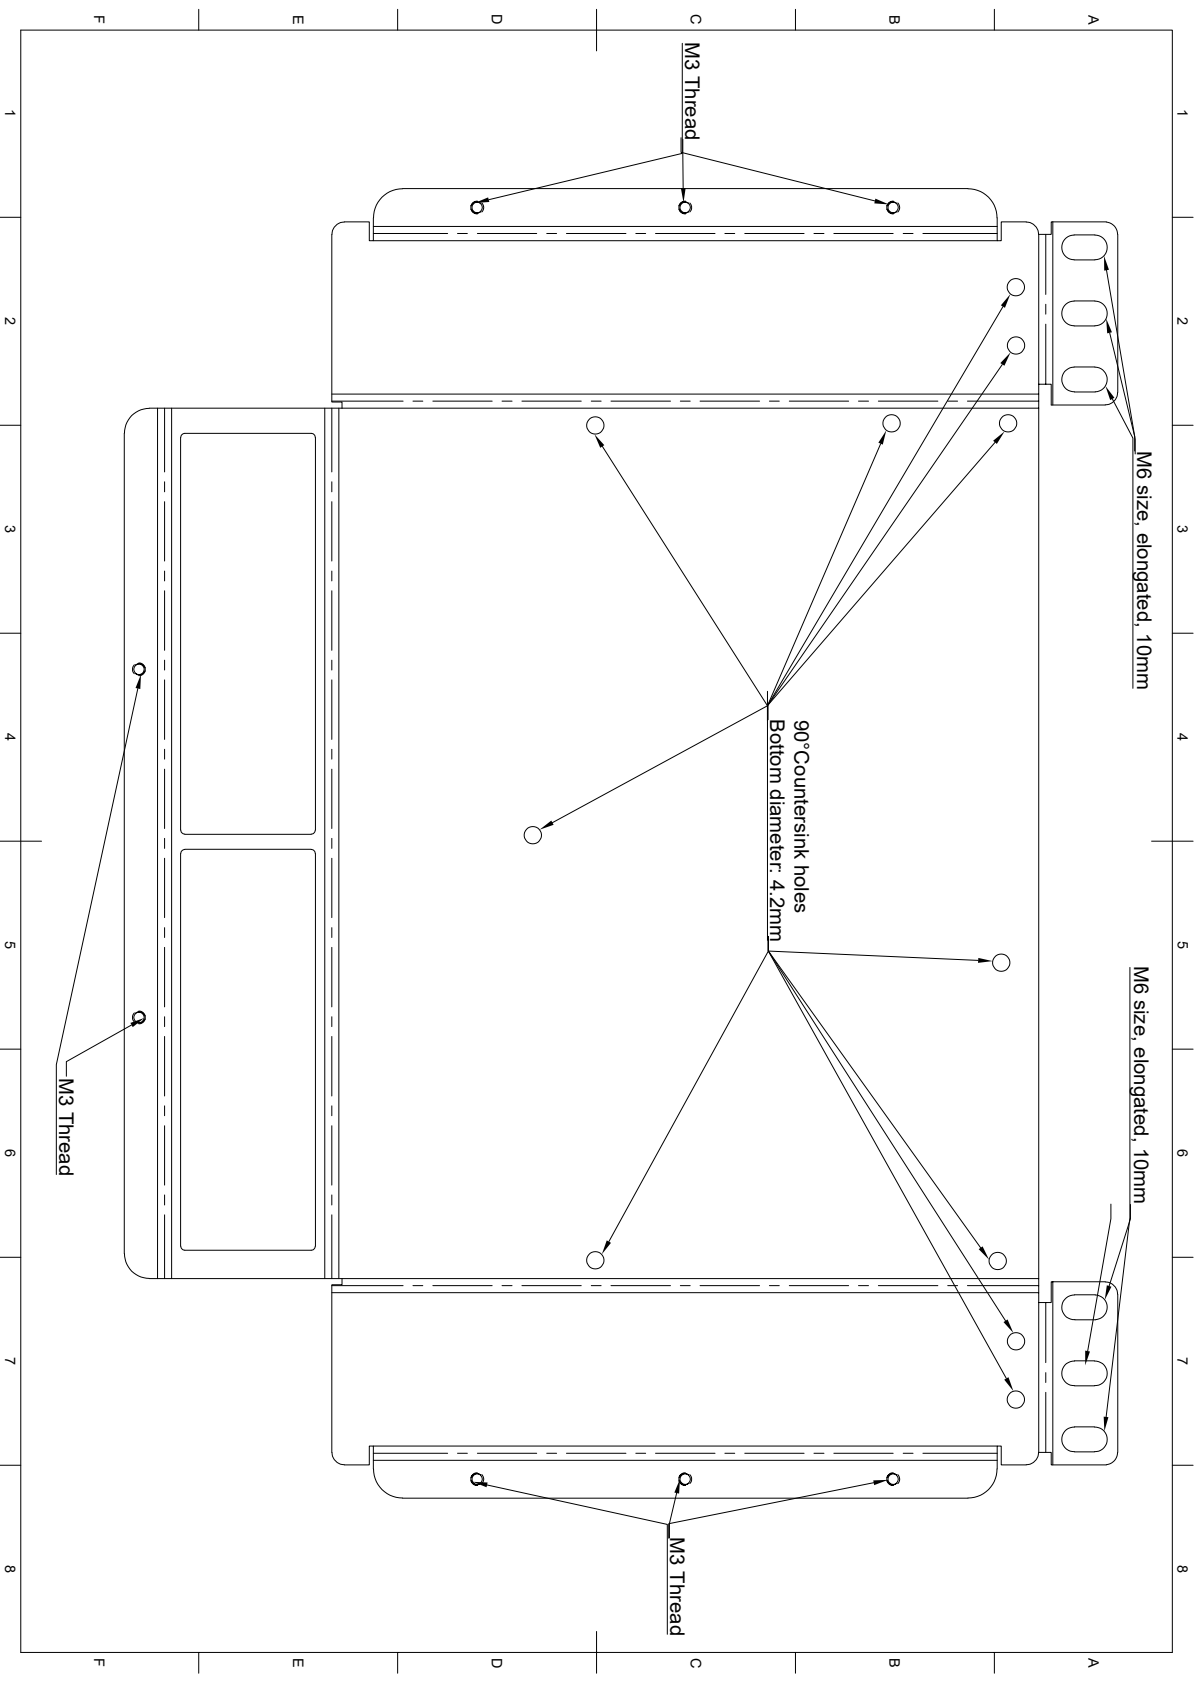
[picture p166: page 1]

1 A 2 3 4 5 6 7 8 1 2 3 4 5 6 7 8 FEDCB FEDCBA Bottom diameter: 4.2mm 90°Countersink holes M3 Thread M3 Thread M3 Thread M6 size, elongated, 10mm M6 size, elongated, 10mm
