DvidMakesThings/HW_10-In-Rack_PDU/src/Enclosure-Design/SheetMetal/Top_Enclosure/Energis-Enclosure-Top-Holes.pdf

10.94 5.16

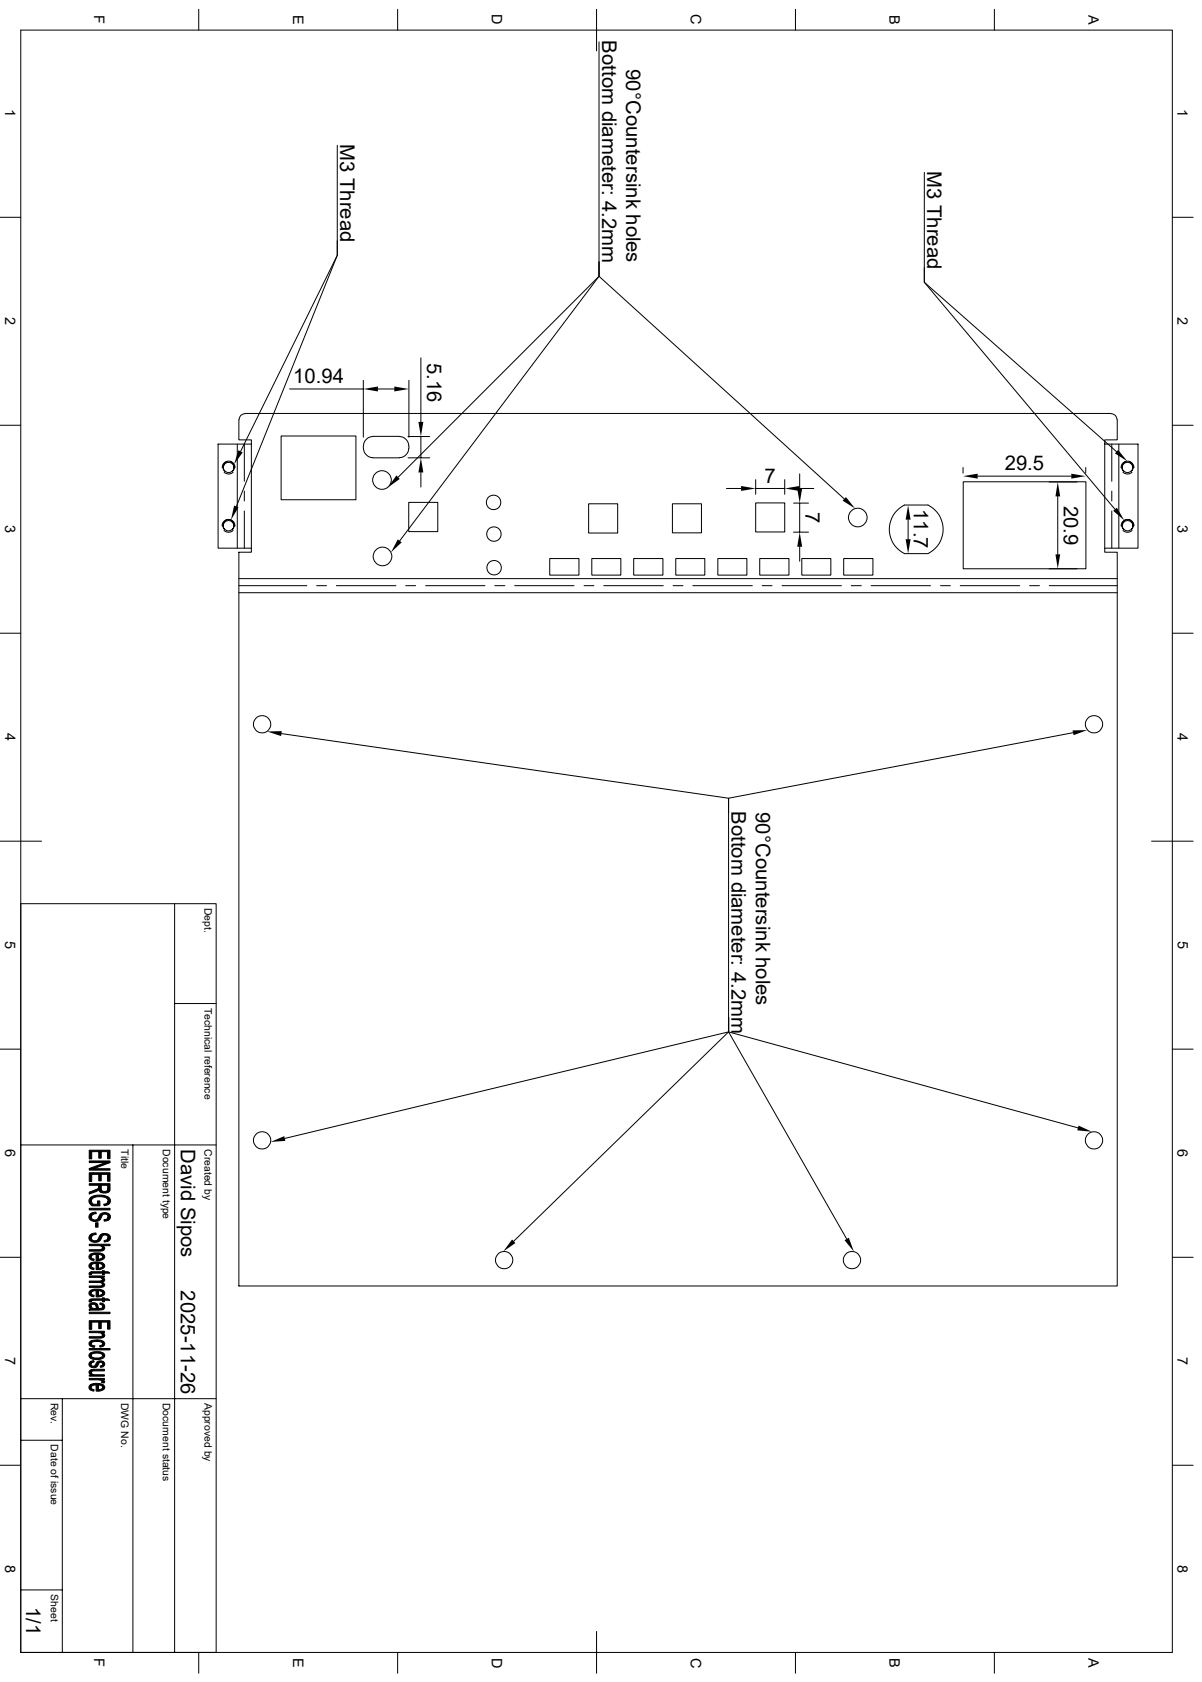
[picture p167: page 1]

1 A 2 3 4 5 6 7 8 1 2 3 4 5 6 7 8 FEDCB FEDCBA Dept. Technical reference Created by Approved by Title DWG No. Document type Document status Rev. Date of issue Sheet 2025-11-26 1/1 David Sipos Bottom diameter: 4.2mm 90°Countersink holes 90°Countersink holes Bottom diameter: 4.2mm M3 Thread M3 Thread
