DvidMakesThings/HW_10-In-Rack_PDU/src/PDF/_proto/Relay-Board/Rev2.1/Relay-Board_2.1_Schematics.pdf

## 5V, 200mA non-isolated power supply

A

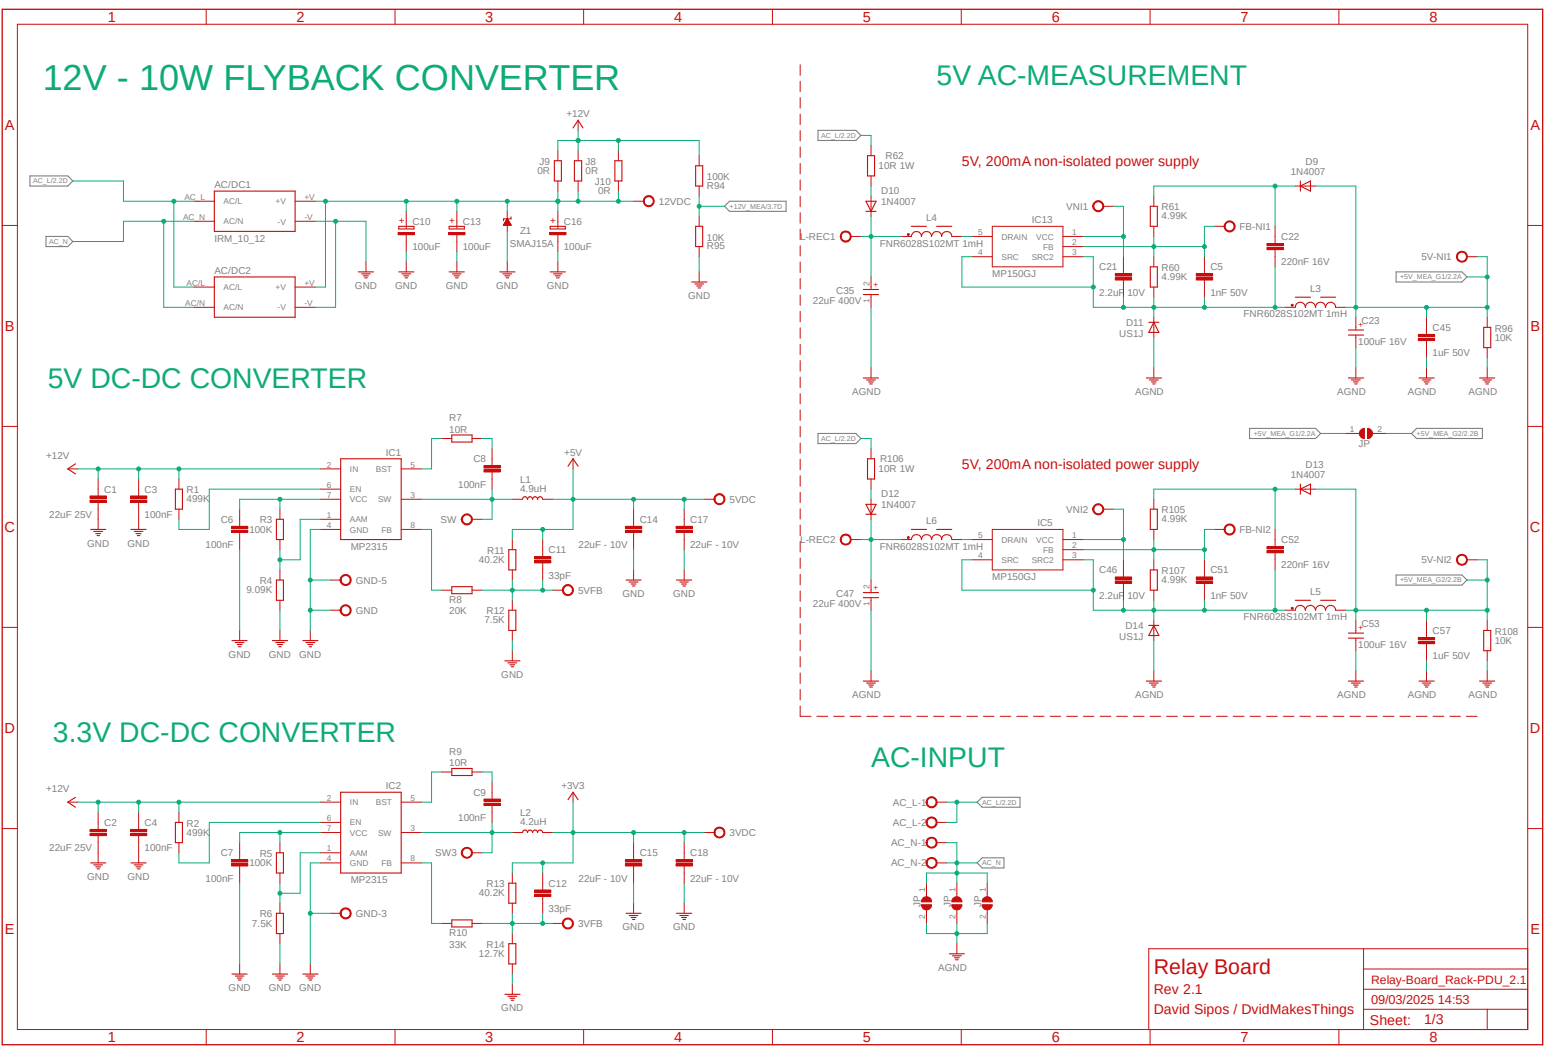
[picture p168: page 1]

5V, 200mA non-isolated power supply

AAM 1

Relay Board Rev 2.1 David Sipos / DvidMakesThings

Sheet: 1/3

A

A

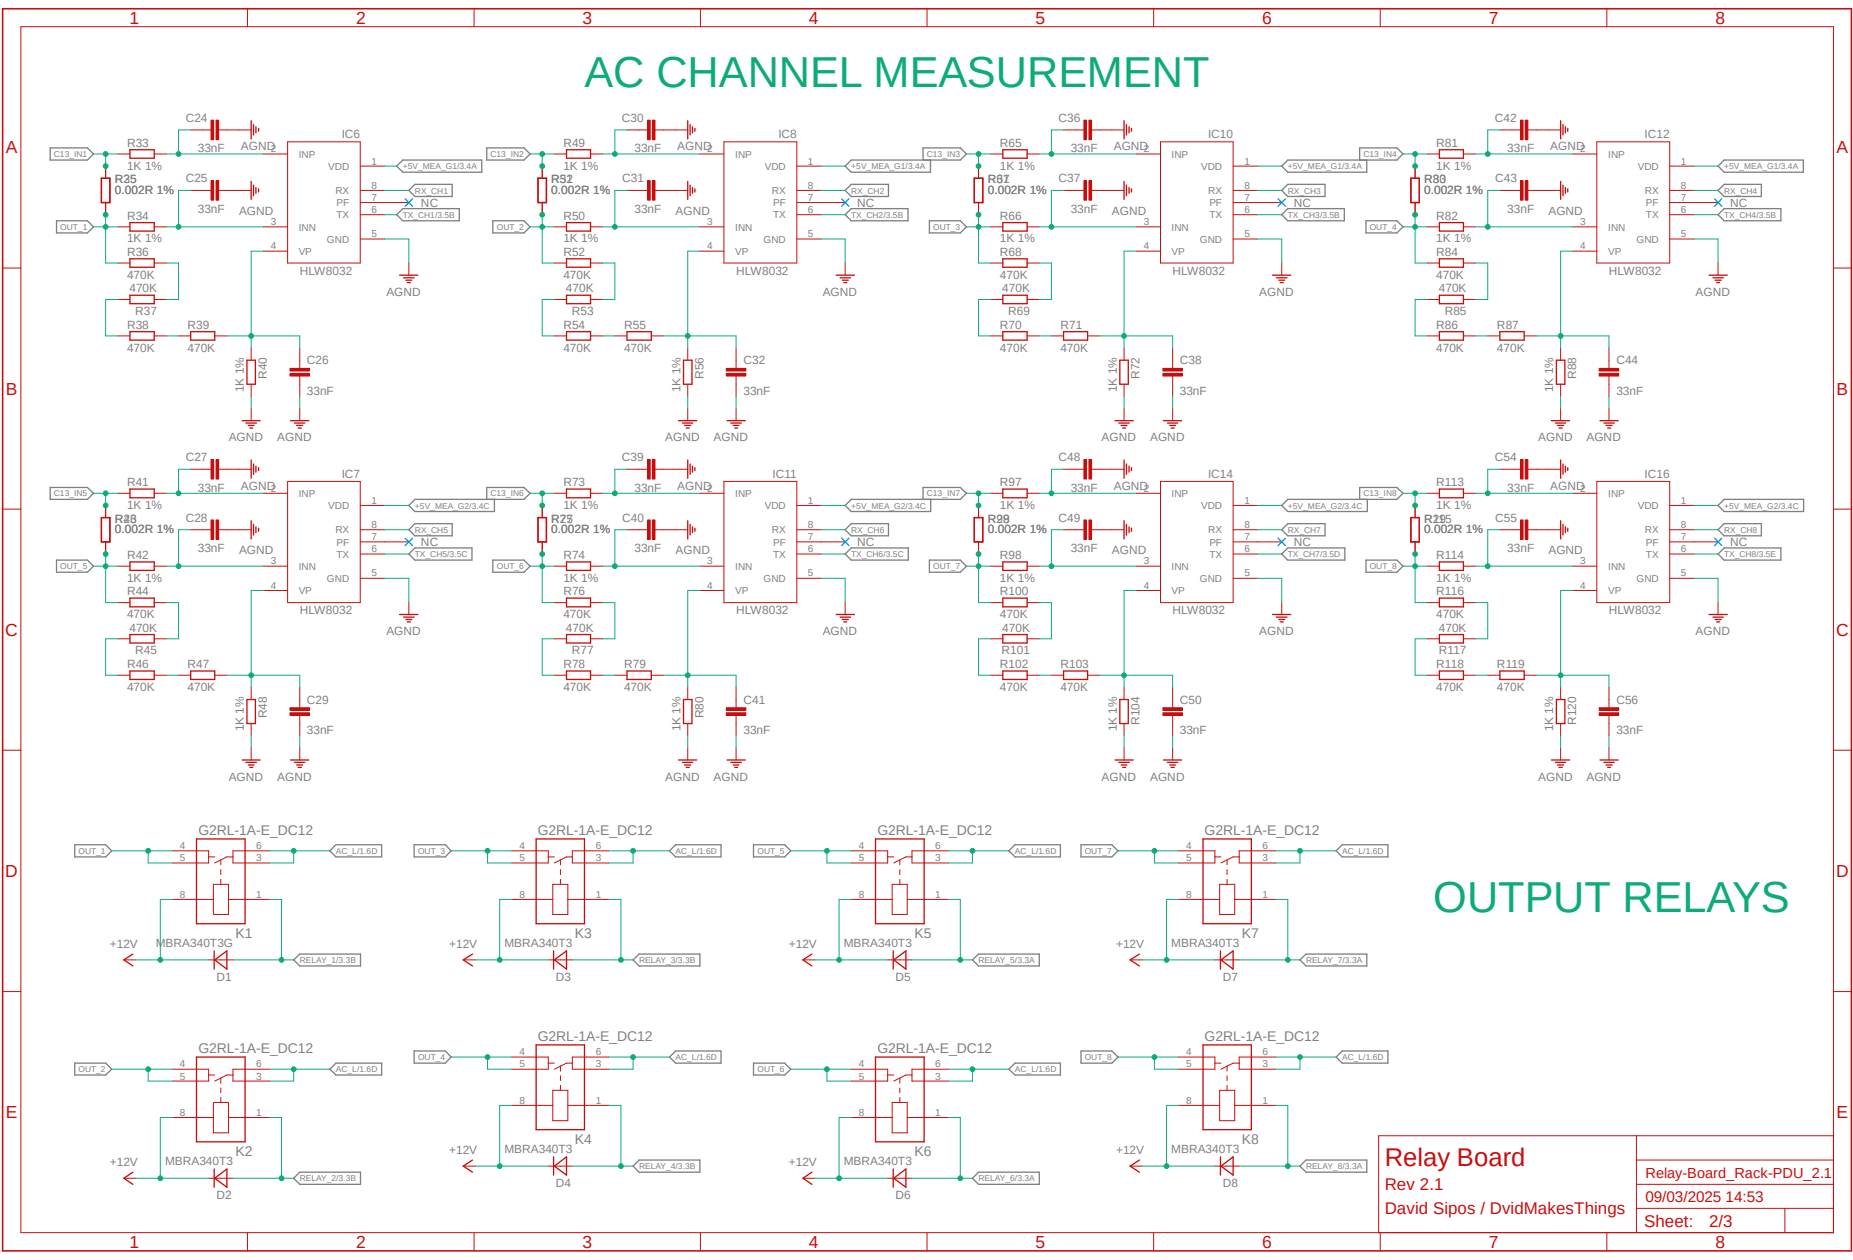
[picture p169: page 2]

Relay Board David Sipos / DvidMakesThings

Sheet: 2/3

A

A

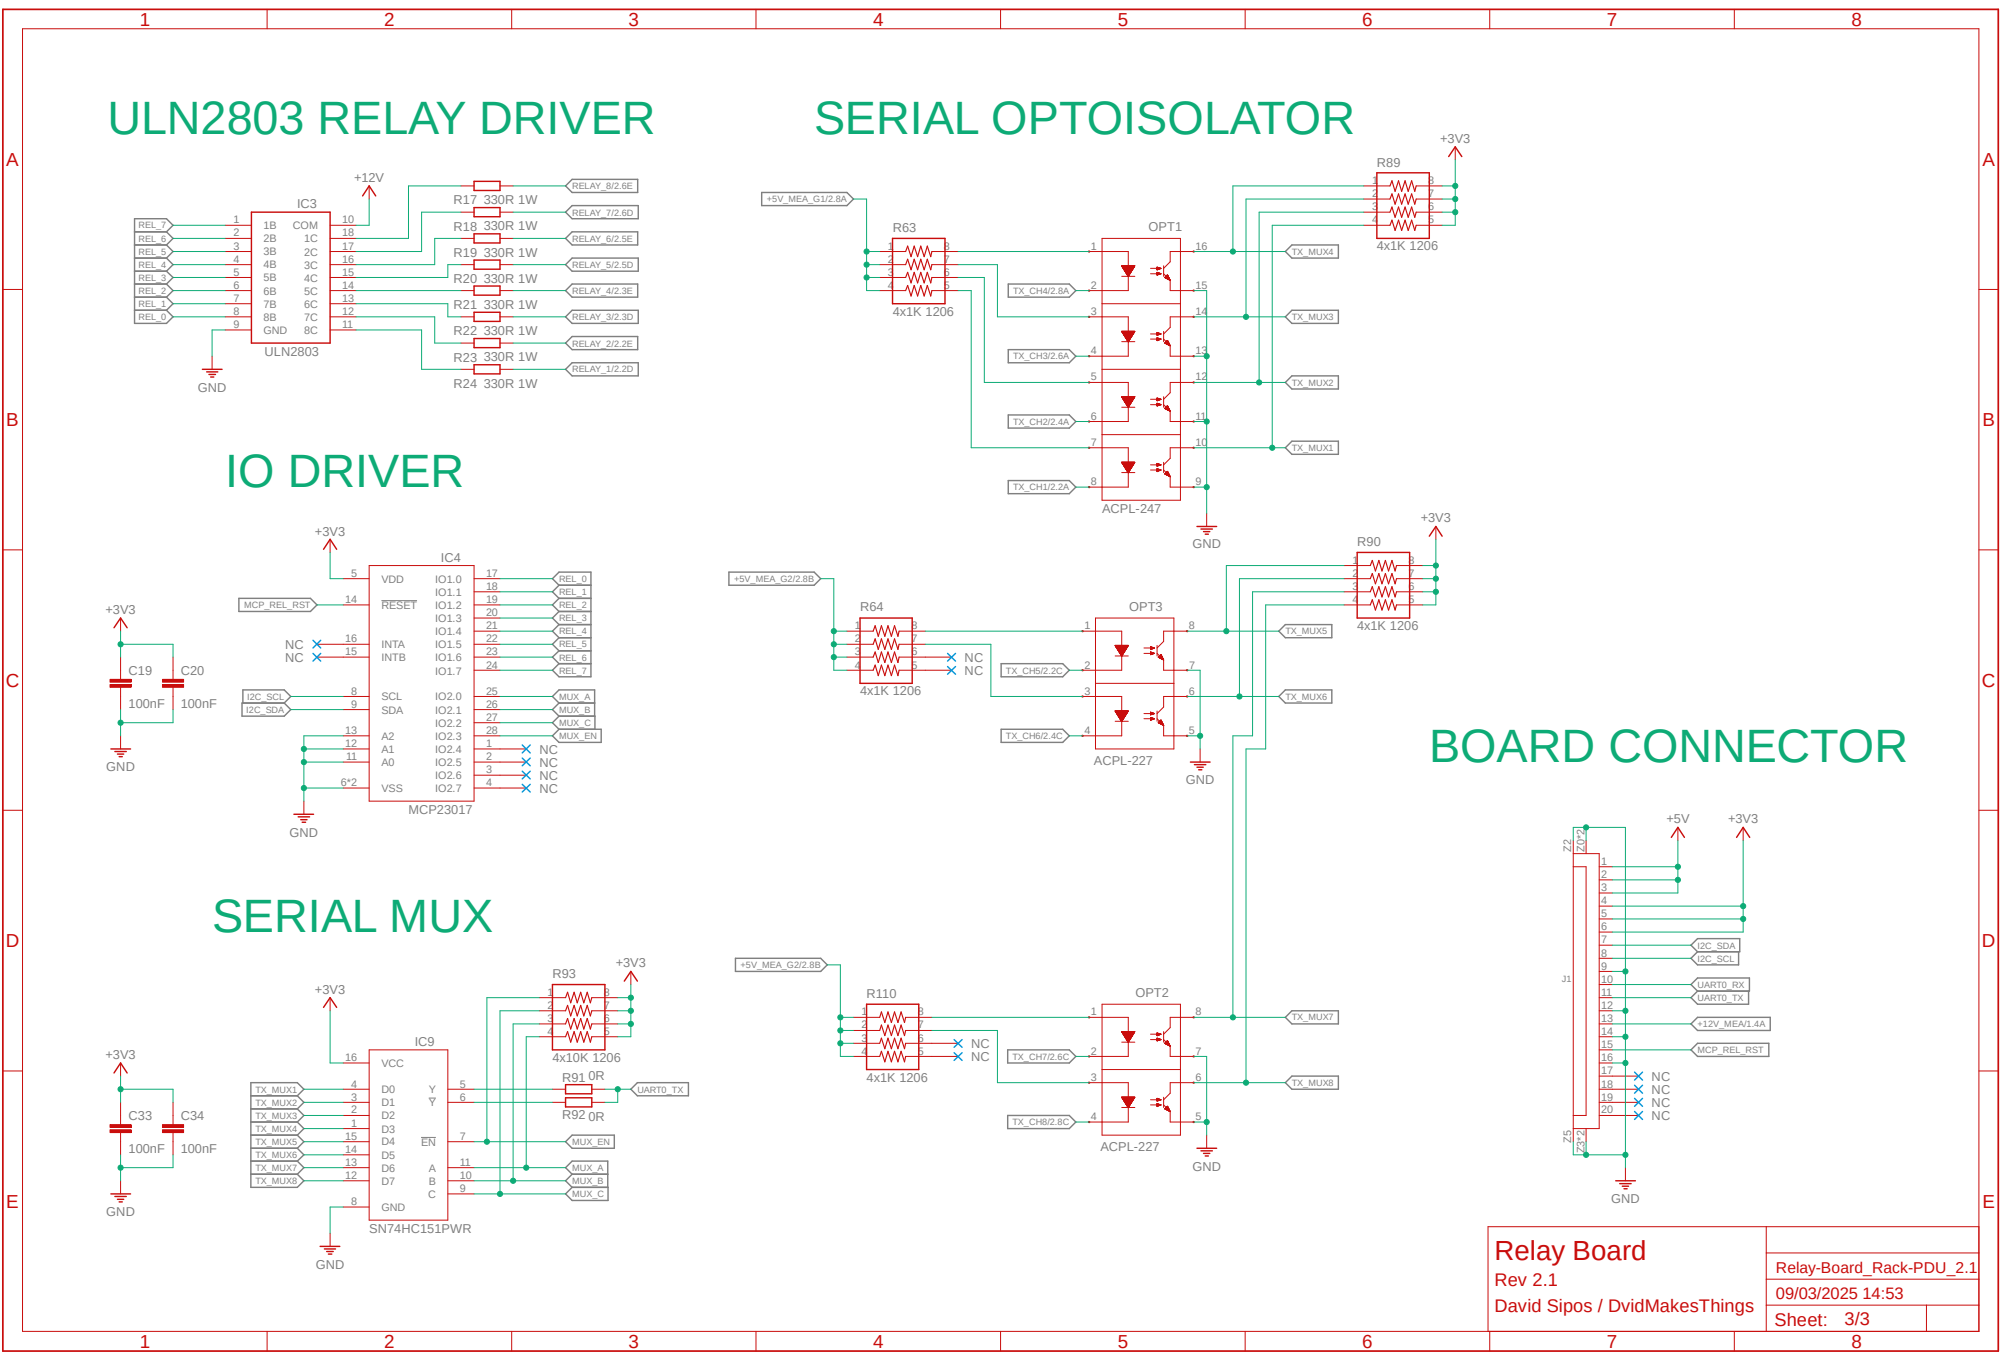
[picture p170: page 3]

7 8 9

David Sipos / DvidMakesThings

Sheet: 3/3
