DvidMakesThings/HW_10-In-Rack_PDU/src/PDF/_proto/Controller-Board/Rev 2.0/Controller-Board_2.0_Schematics.pdf

A

A

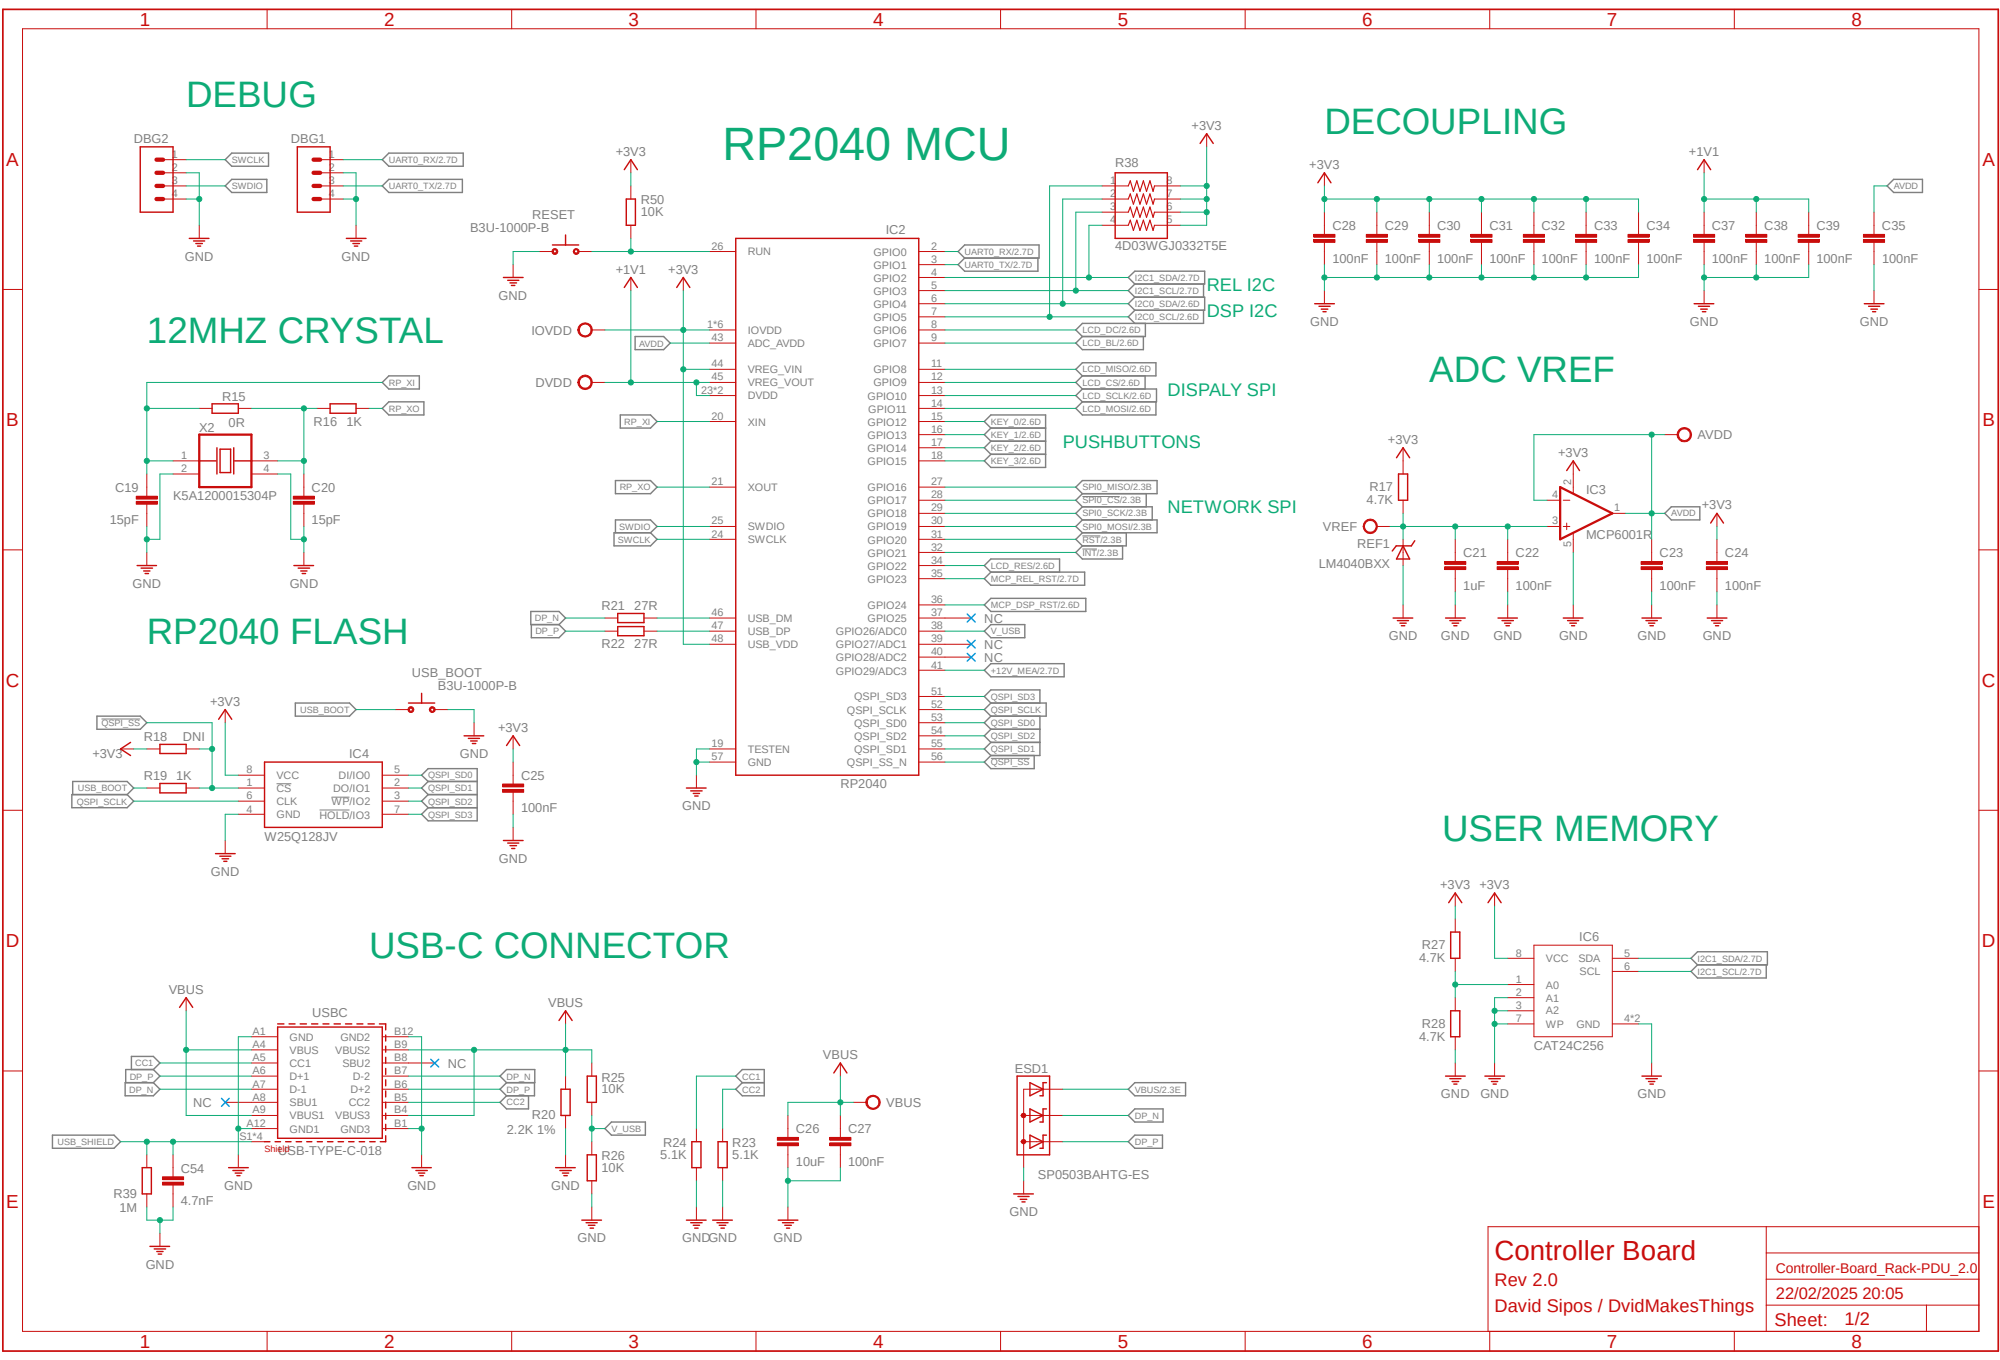
[picture p171: page 1]

ADC_AVDD 43 VREG_VIN 44

VREG_VOUT 45 | LCD_MISO/2.6D

R15 | | | DVDD 23*2

XIN 20 XOUT 21 SWCLK 24 SWDIO 25 USB_DM 46 | LCD_SCLK/2.6D

DP_P | USB_VDD 48

QSPI_SCLK | GND 4 HOLD/IO3 | QSPI_SD2 7

Controller Board Rev 2.0 David Sipos / DvidMakesThings

Sheet: 1/2

A

A

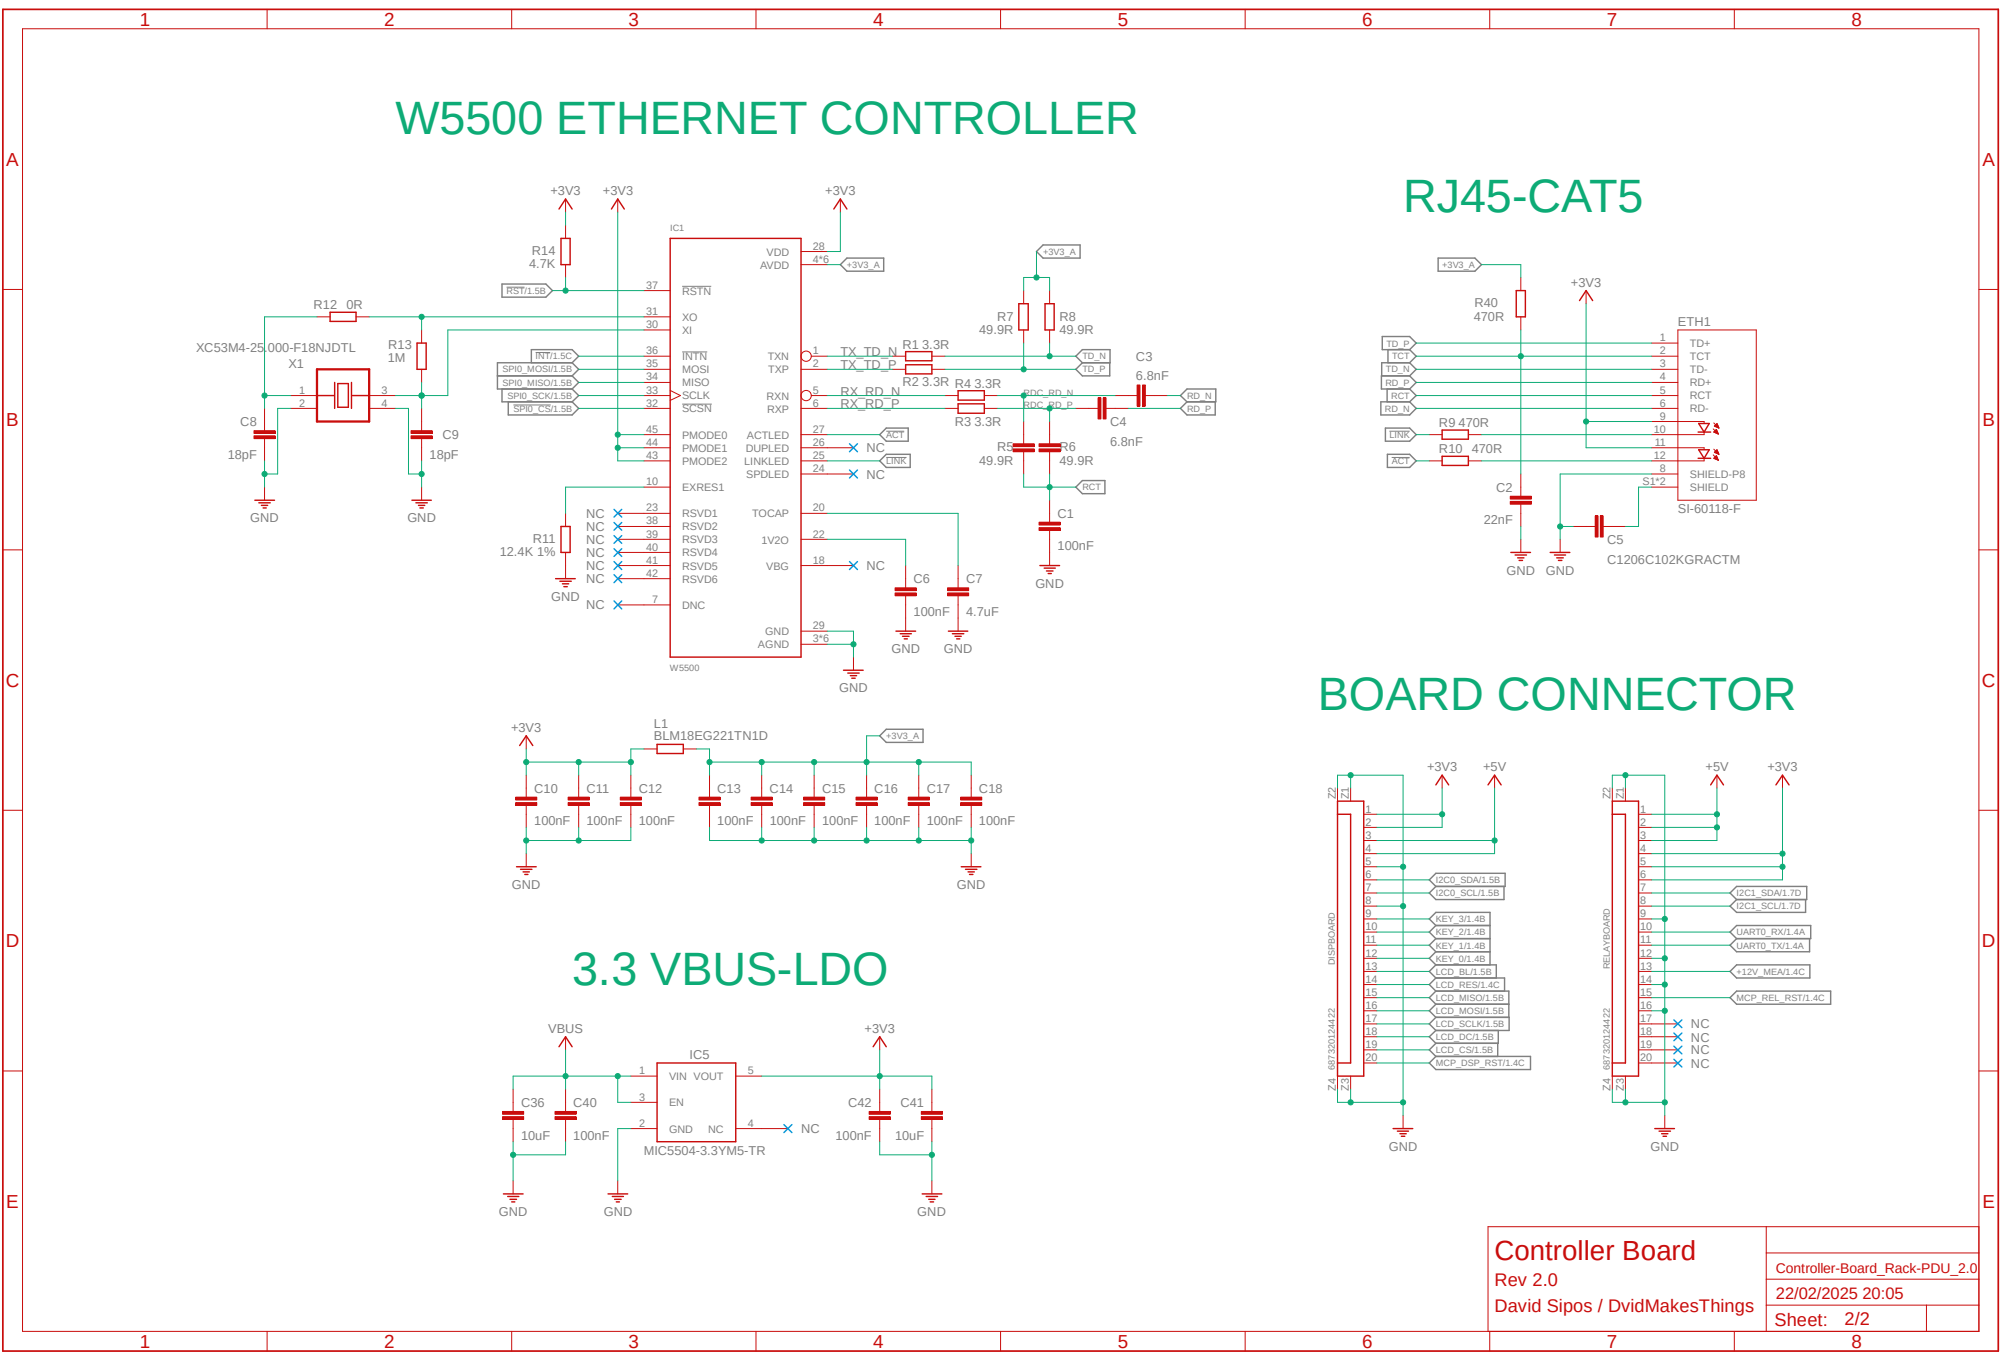
[picture p172: page 2]

Rev 2.0 David Sipos / DvidMakesThings
Sheet: 2/2
