DvidMakesThings/HW_10-In-Rack_PDU/docs/doxygen/latex/button__driver_8c__incl.pdf

src/Software/ENERGIS
_RTOS/src/drivers/button
