DvidMakesThings/HW_10-In-Rack_PDU/docs/doxygen/latex/device__identity_8c__incl.pdf

src/Software/ENERGIS
_RTOS/src/tasks/storage
_submodule/device_identity.c
