DvidMakesThings/HW_10-In-Rack_PDU/docs/doxygen/latex/calibration_8c_ae8658b50ad7475f4740593d8f35c9999_icgraph.pdf

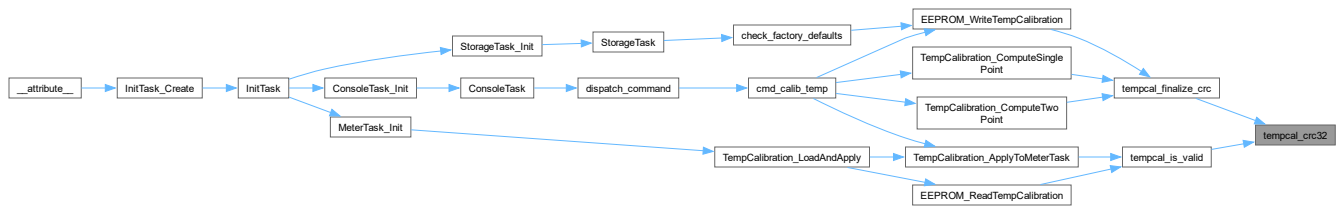
[picture p173: page 1]
tempcal_crc32; tempcal_finalize_crc; tempcal_is_valid; EEPROM_WriteTempCalibration; TempCalibration_ComputeSingle Point; TempCalibration_ComputeTwo Point; check_factory_defaults; cmd_calib_temp; StorageTask StorageTask_Init; __attribute__; InitTask_Create; InitTask; ConsoleTask_Init; ConsoleTask; dispatch_command; EEPROM_ReadTempCalibration; TempCalibration_LoadAndApply; TempCalibration_ApplyToMeterTask; MeterTask_Init
