DvidMakesThings/HW_10-In-Rack_PDU/docs/Compliance_Documents/ENE-TDOC-MIR/ENE-TDOC-MIR-Inspection_Report_MainBoard_1.1.0.pdf

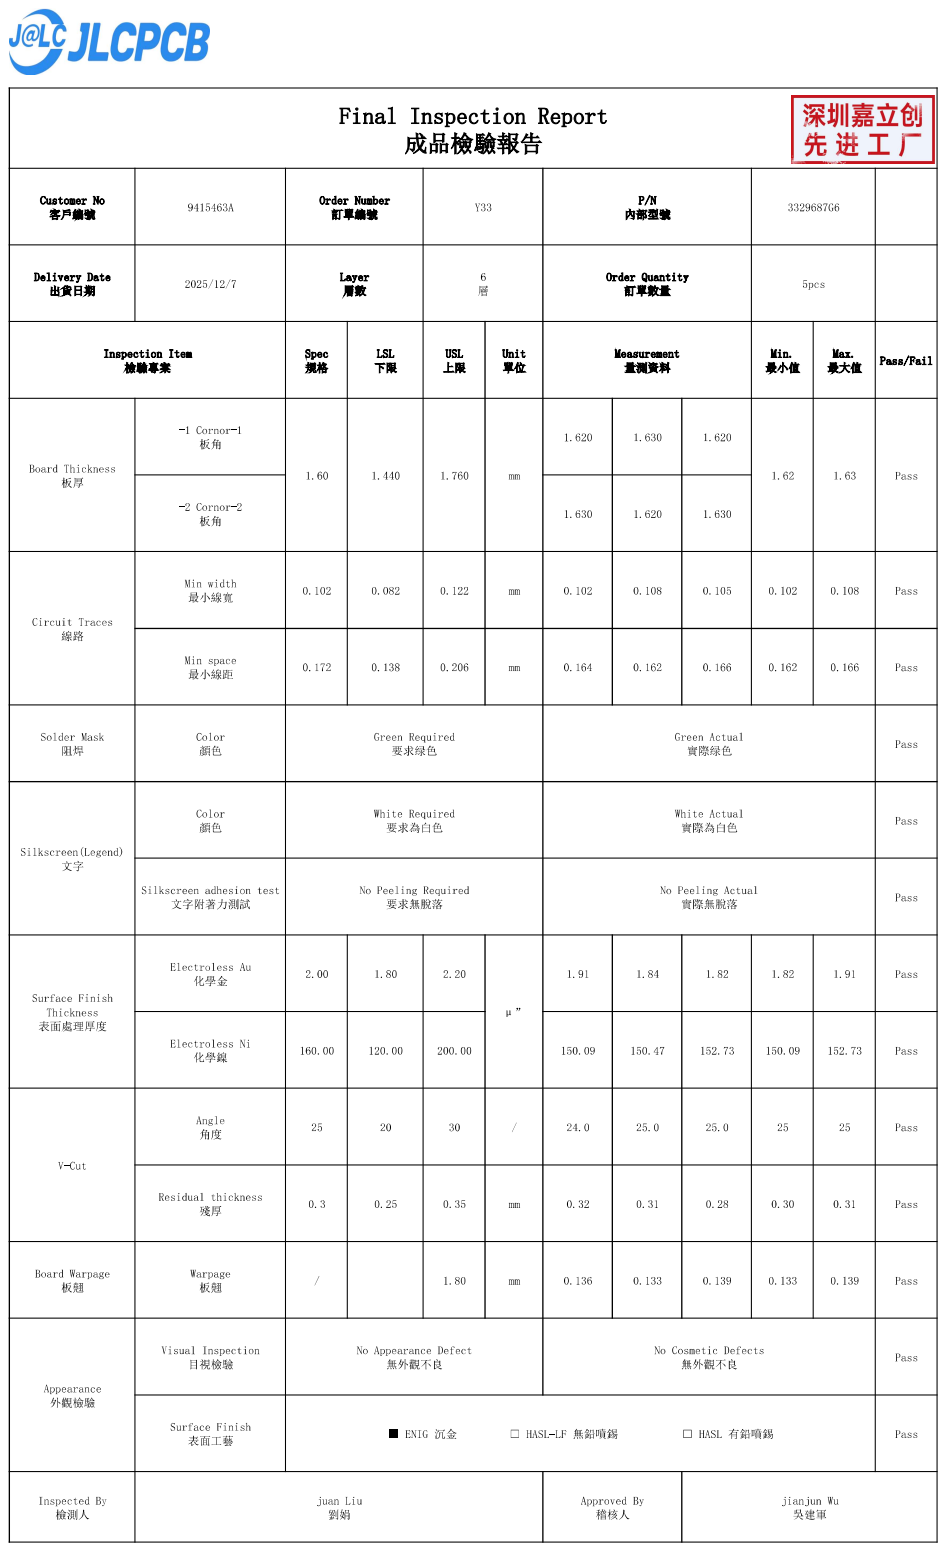
[picture p175: page 1]
