DvidMakesThings/HW_10-In-Rack_PDU/docs/Compliance_Documents/ENE-TDOC-RHSC/ENE-TDOC-RHSC-ROHS_Test_Report_DisplayBoard_1.1.0.pdf

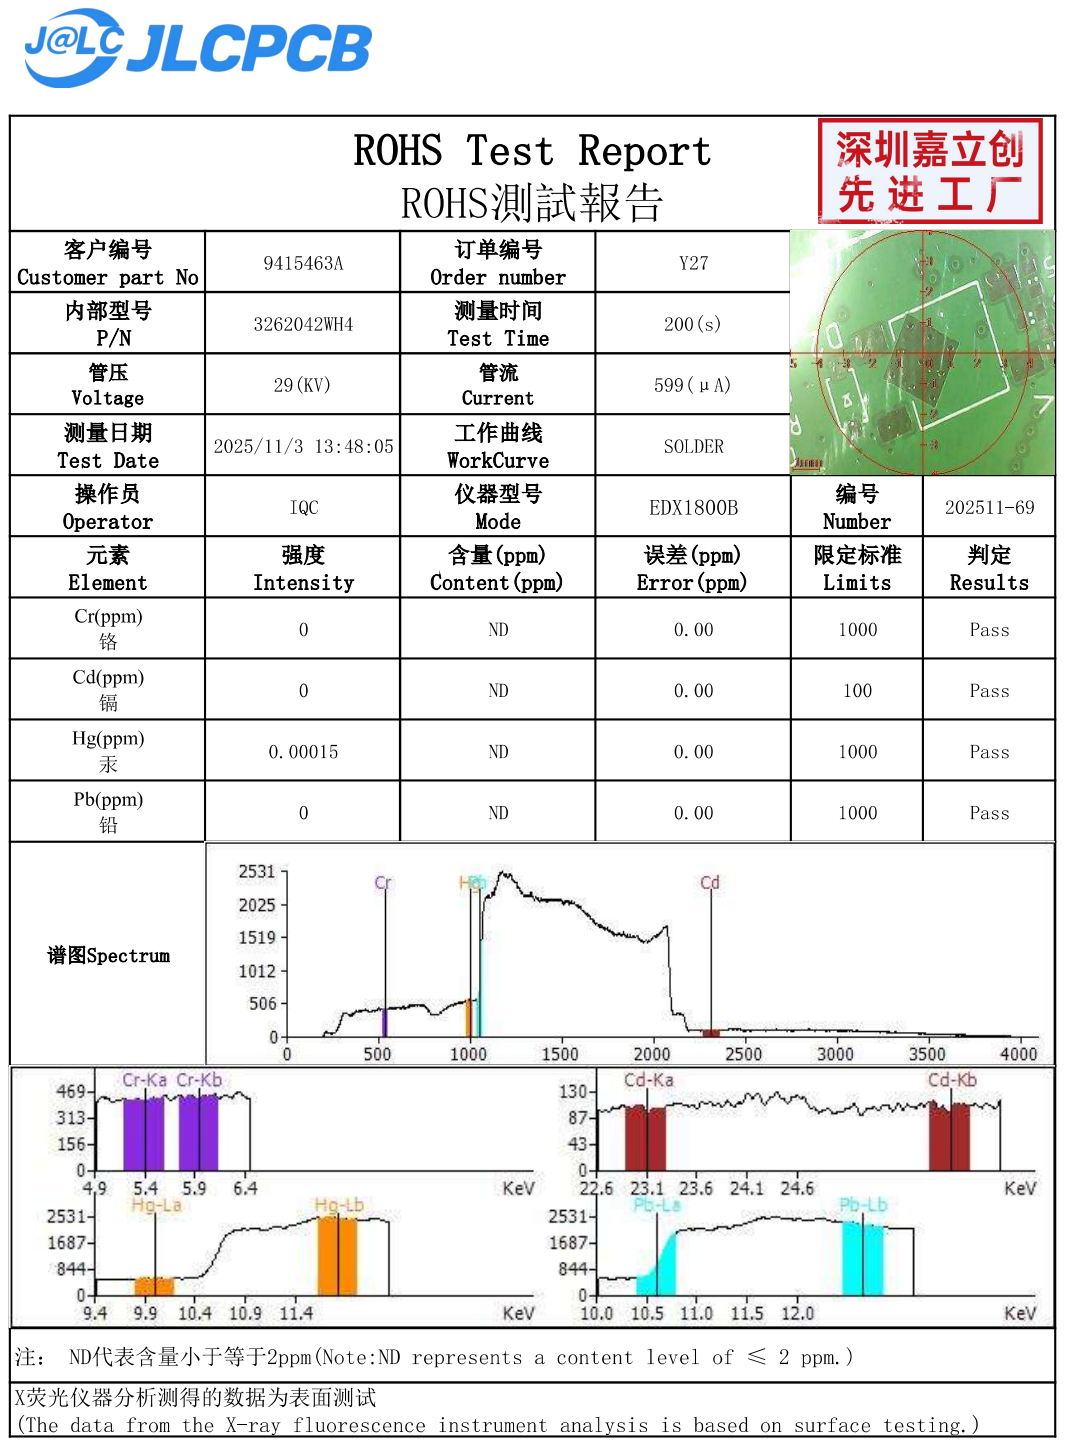
[picture p178: page 1]

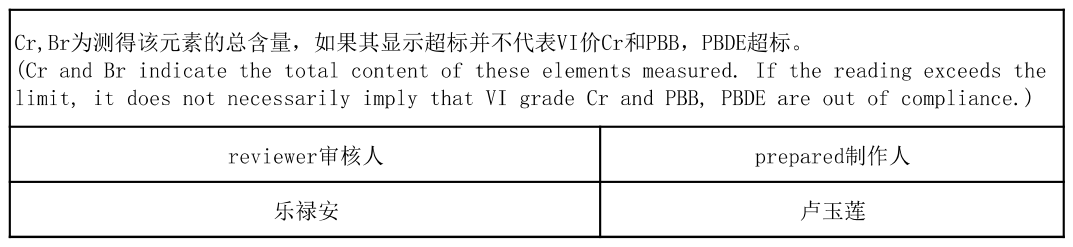
[picture p179: page 2]
