DvidMakesThings/HW_10-In-Rack_PDU/docs/Compliance_Documents/ENE-TDOC-RHSC/ENE-TDOC-RHSC-ROHS_Test_Report_MainBoard_1.1.0.pdf

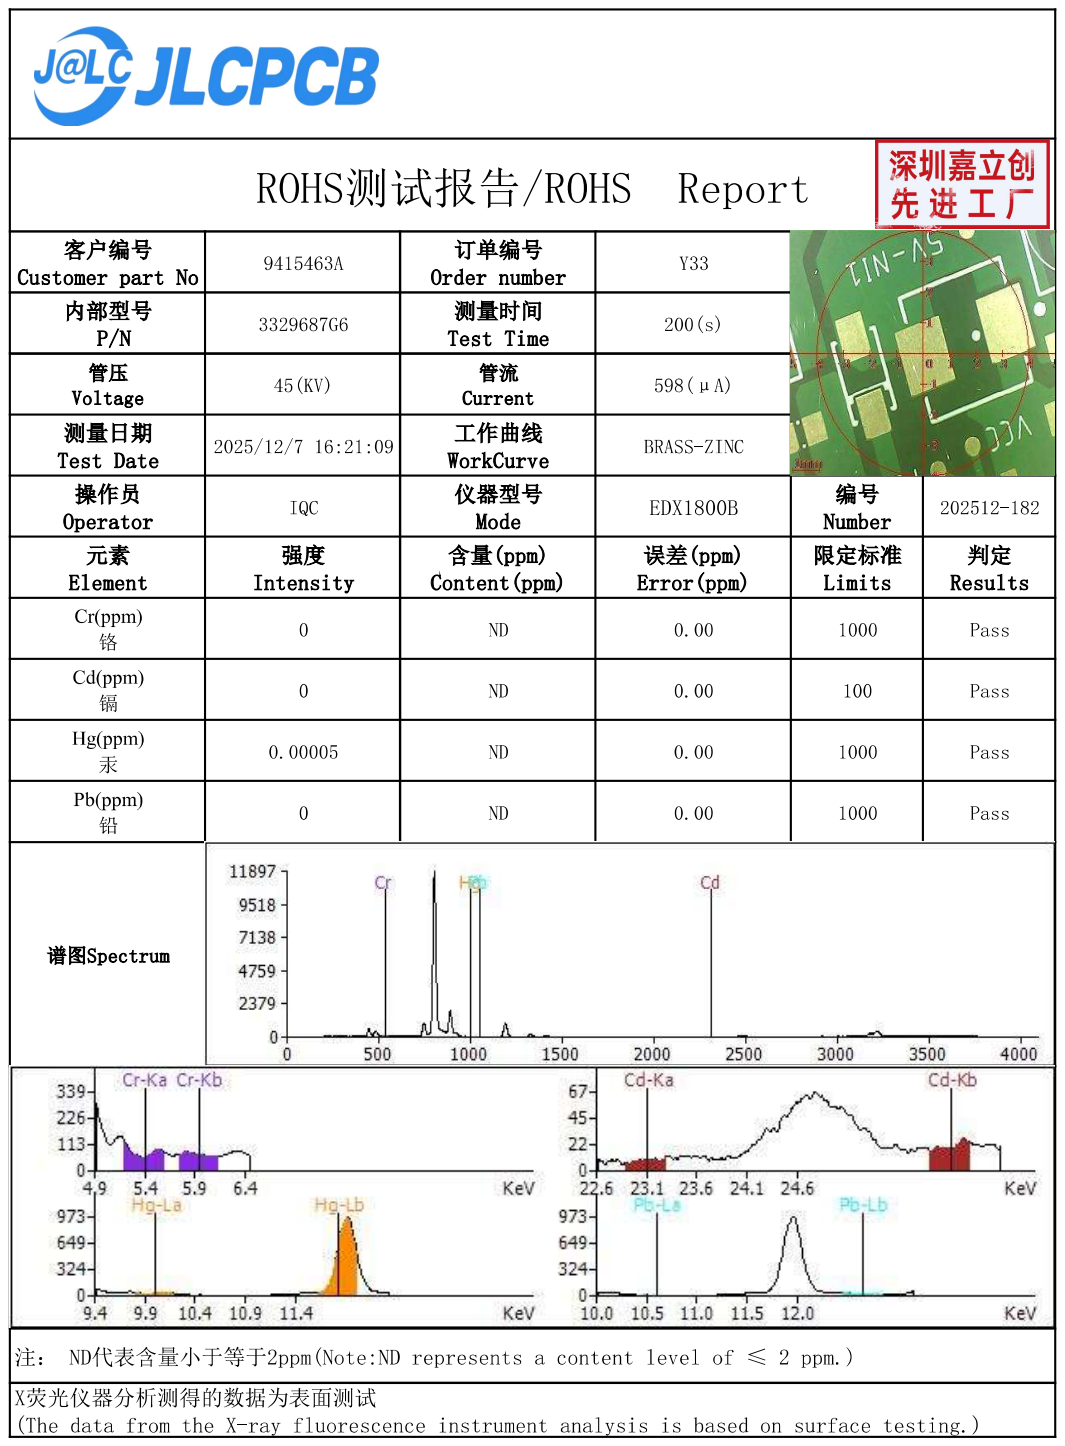
[picture p180: page 1]

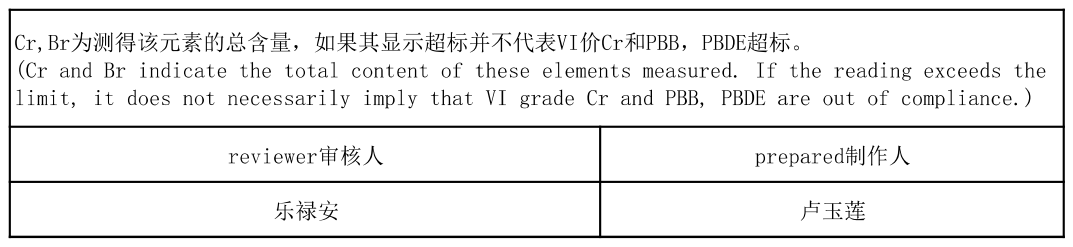
[picture p181: page 2]
