DvidMakesThings/HW_10-In-Rack_PDU/src/PDF/_proto/Display-Board/Rev 2.0/Display-Board_2.0_Schematics.pdf

# R3 Z2 Z1 1

A

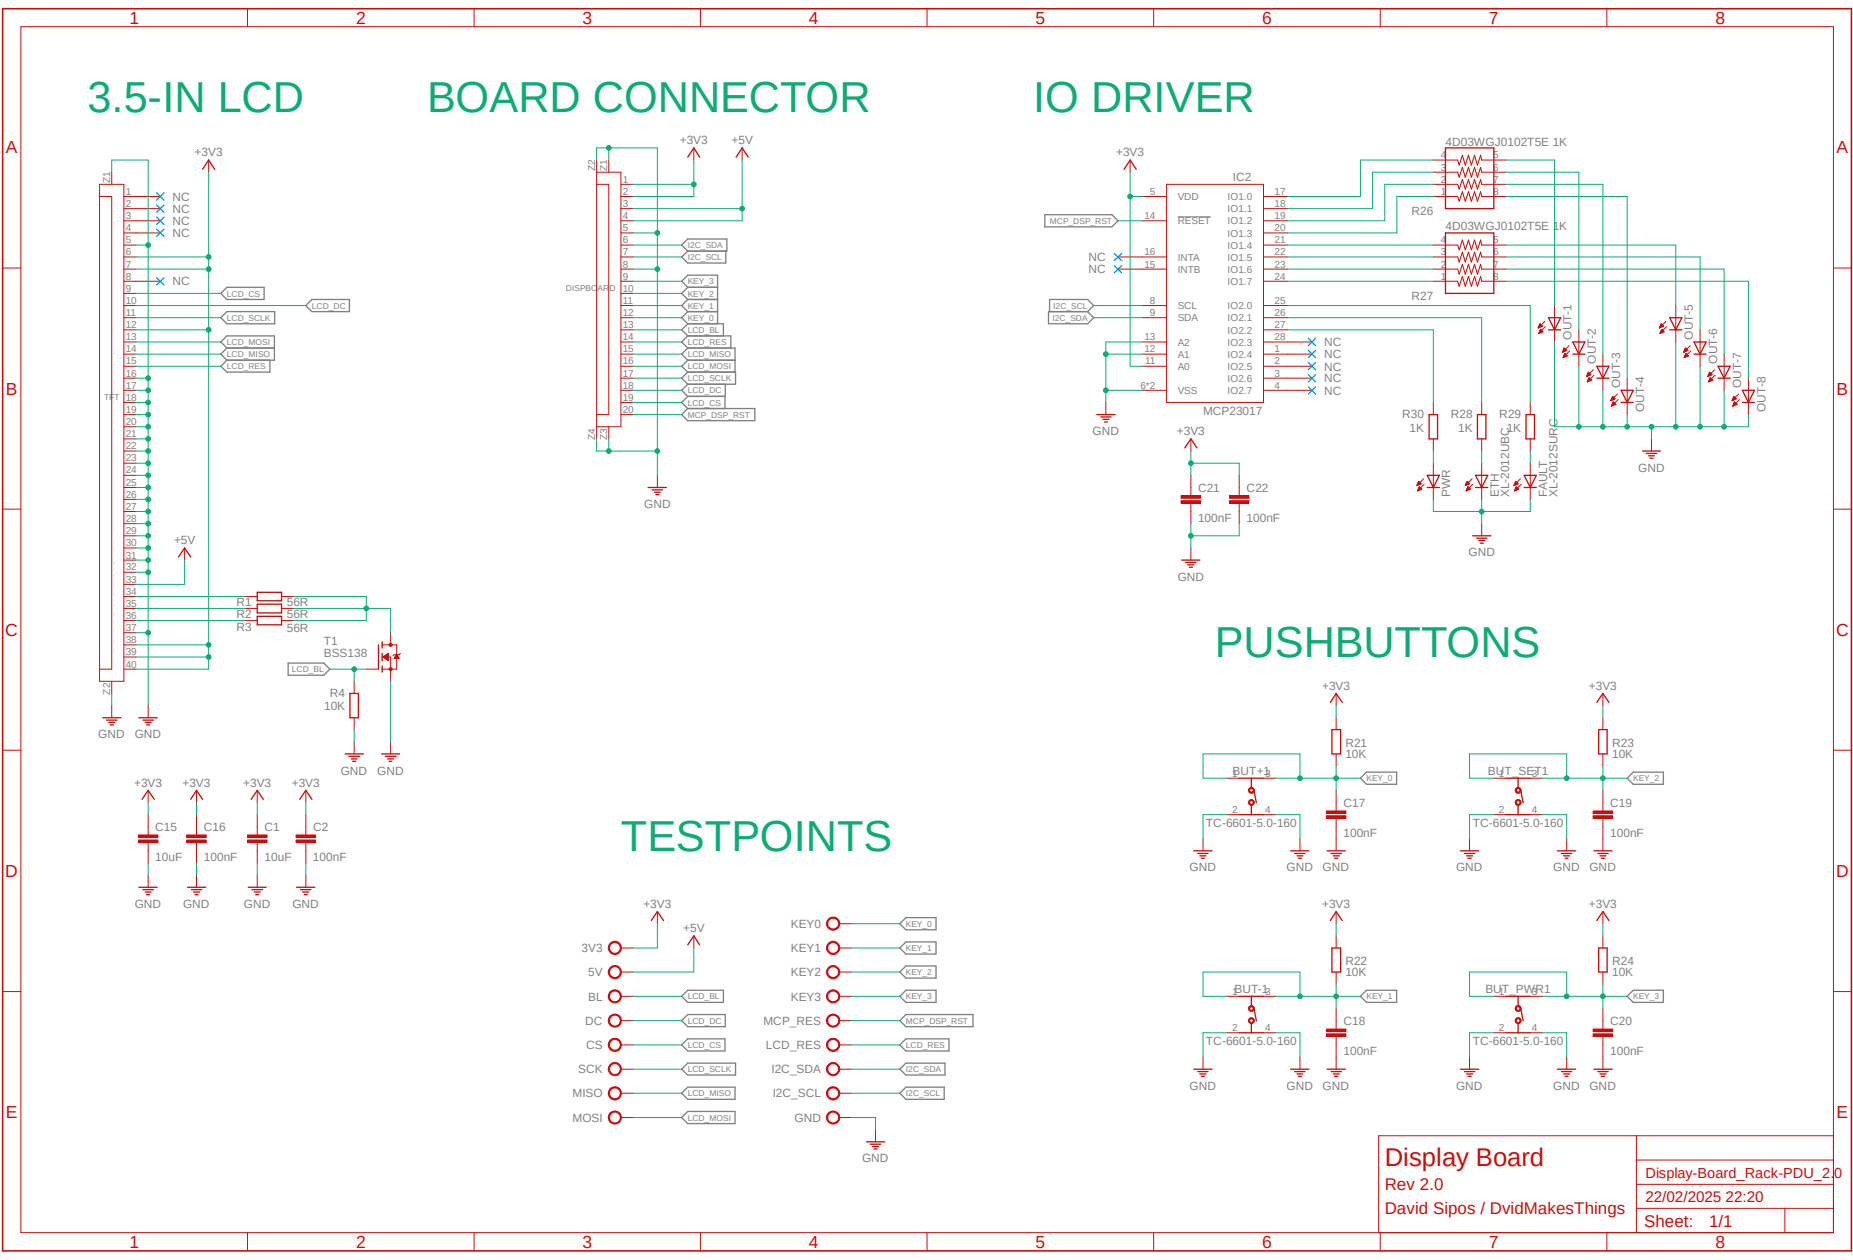
[picture p182: page 1]

35 | R1 56R
36 | R2 56R
37

39
40

Rev 2.0 David Sipos / DvidMakesThings
Sheet: 1/1
