DvidMakesThings/HW_10-In-Rack_PDU/src/Hardware-Design/ENERGIS/Rev1.1.0/Gerber/FPC_Cable/Stiffner_EMI.pdf

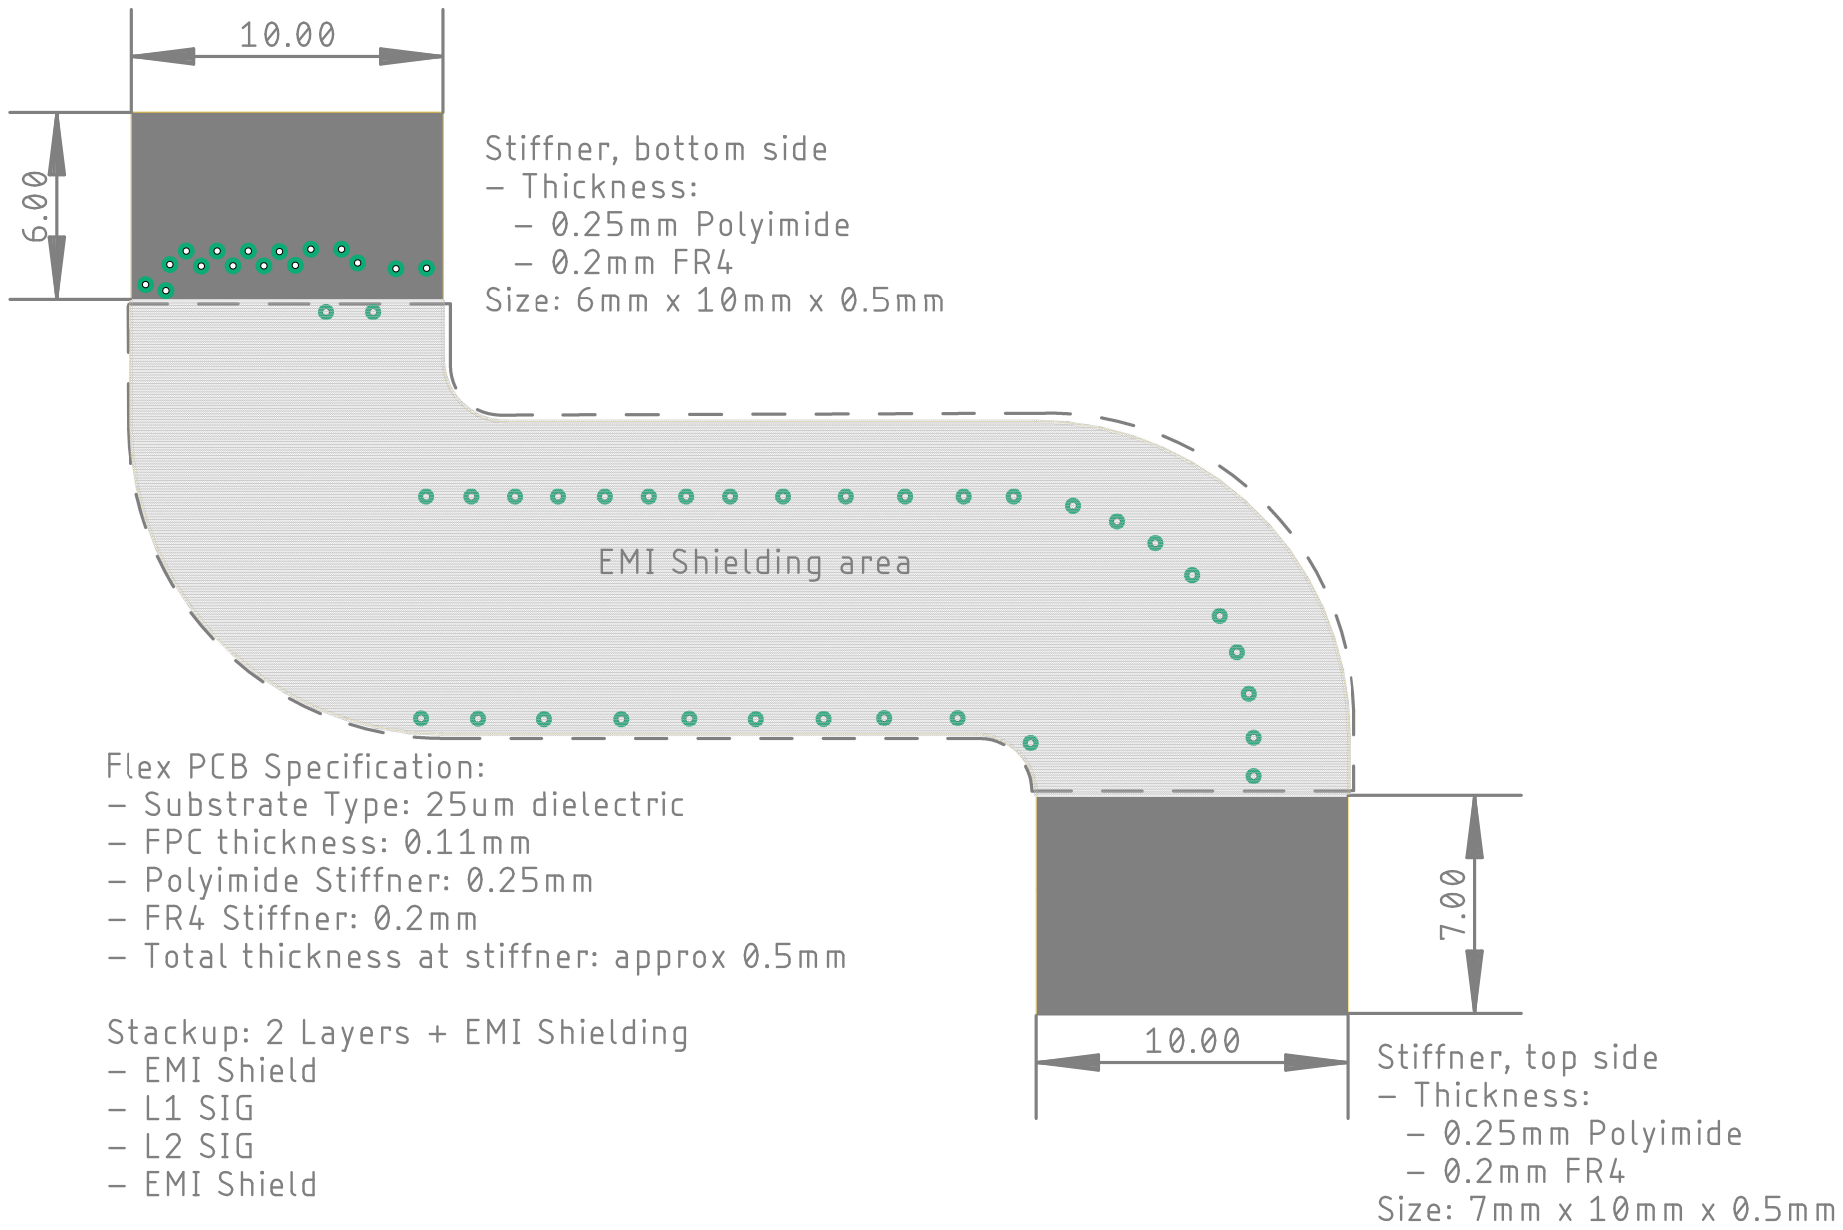
[picture p183: page 1]
