DvidMakesThings/HW_10-In-Rack_PDU/docs/doxygen/latex/crashlog_8c_a19fbb6b4d2a38070175773953f6fb5db_icgraph.pdf

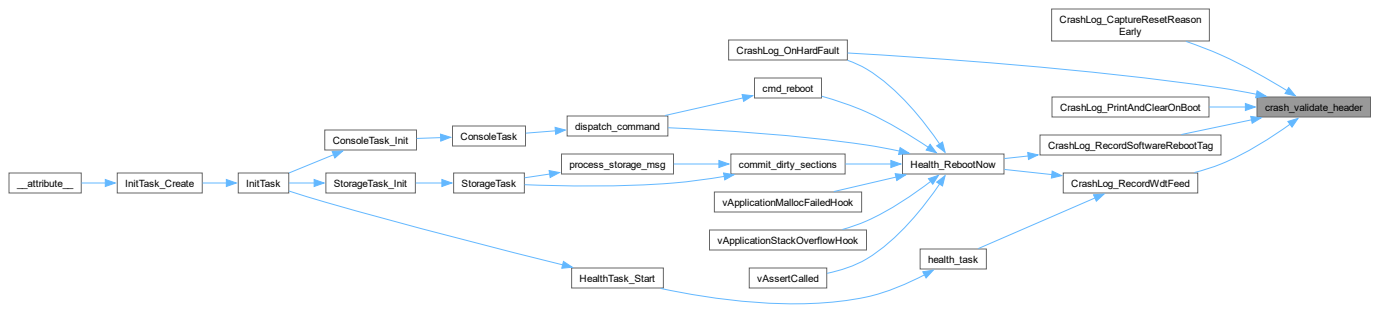
[picture p184: page 1]
crash_validate_header; CrashLog_CaptureResetReason Early; CrashLog_OnHardFault; CrashLog_PrintAndClearOnBoot; CrashLog_RecordSoftwareRebootTag; CrashLog_RecordWdtFeed; Health_RebootNow; cmd_reboot; dispatch_command; commit_dirty_sections; vApplicationMallocFailedHook; vApplicationStackOverflowHook; vAssertCalled; ConsoleTask ConsoleTask_Init; __attribute__; InitTask_Create; InitTask; process_storage_msg; StorageTask_Init; StorageTask; health_task; HealthTask_Start
