DvidMakesThings/HW_10-In-Rack_PDU/docs/doxygen/latex/crashlog_8c_a50f52af1f76175e818dad1ef9f2bc3eb_icgraph.pdf

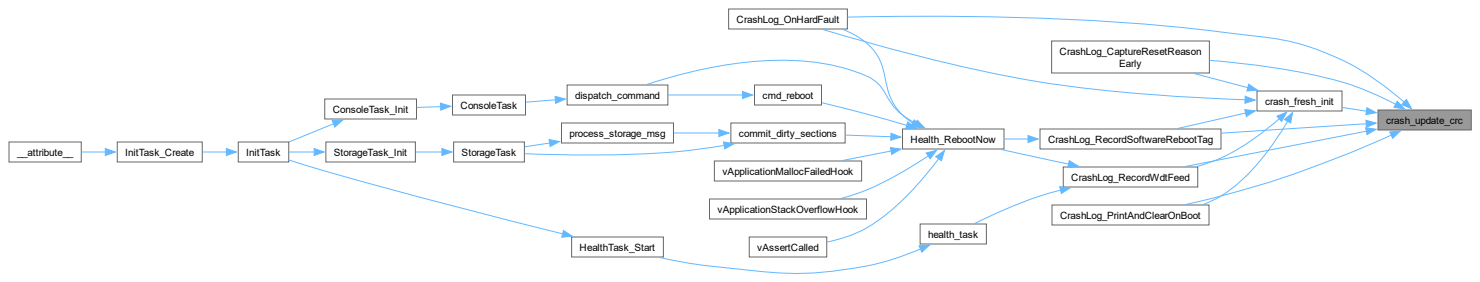
[picture p185: page 1]
crash_update_crc; crash_fresh_init; CrashLog_CaptureResetReason Early; CrashLog_OnHardFault; CrashLog_PrintAndClearOnBoot; CrashLog_RecordSoftwareRebootTag; CrashLog_RecordWdtFeed; Health_RebootNow; dispatch_command; cmd_reboot; commit_dirty_sections; vApplicationMallocFailedHook; vApplicationStackOverflowHook; vAssertCalled; ConsoleTask ConsoleTask_Init; __attribute__; InitTask_Create; InitTask; process_storage_msg; StorageTask_Init; StorageTask; health_task; HealthTask_Start
