DvidMakesThings/HW_10-In-Rack_PDU/docs/doxygen/latex/crashlog_8c_ae55aac5d65874421d290cce57ce04ed5_icgraph.pdf

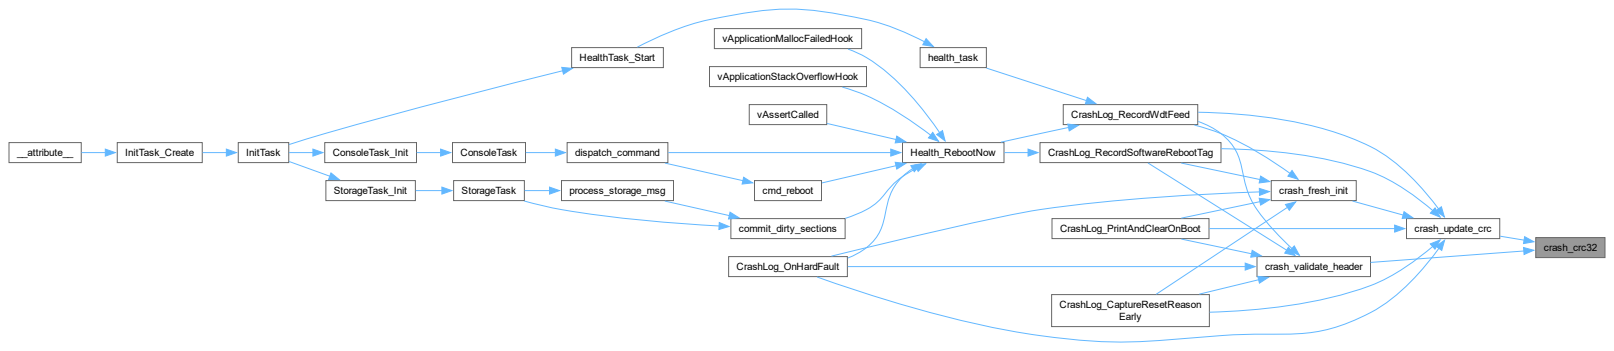
[picture p186: page 1]
crash_crc32; crash_update_crc; crash_validate_header; crash_fresh_init; CrashLog_CaptureResetReason Early; CrashLog_OnHardFault; CrashLog_PrintAndClearOnBoot; CrashLog_RecordSoftwareRebootTag; CrashLog_RecordWdtFeed; Health_RebootNow; cmd_reboot; dispatch_command; commit_dirty_sections; vApplicationMallocFailedHook; vApplicationStackOverflowHook; vAssertCalled; __attribute__; InitTask_Create; InitTask; ConsoleTask_Init; ConsoleTask; StorageTask_Init; StorageTask; process_storage_msg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
