DvidMakesThings/HW_10-In-Rack_PDU/src/HardwareDesign/Controller-Board_Rack-PDU.sch

## EAGLE design src/HardwareDesign/Controller-Board_Rack-PDU.sch (2025-02-10)

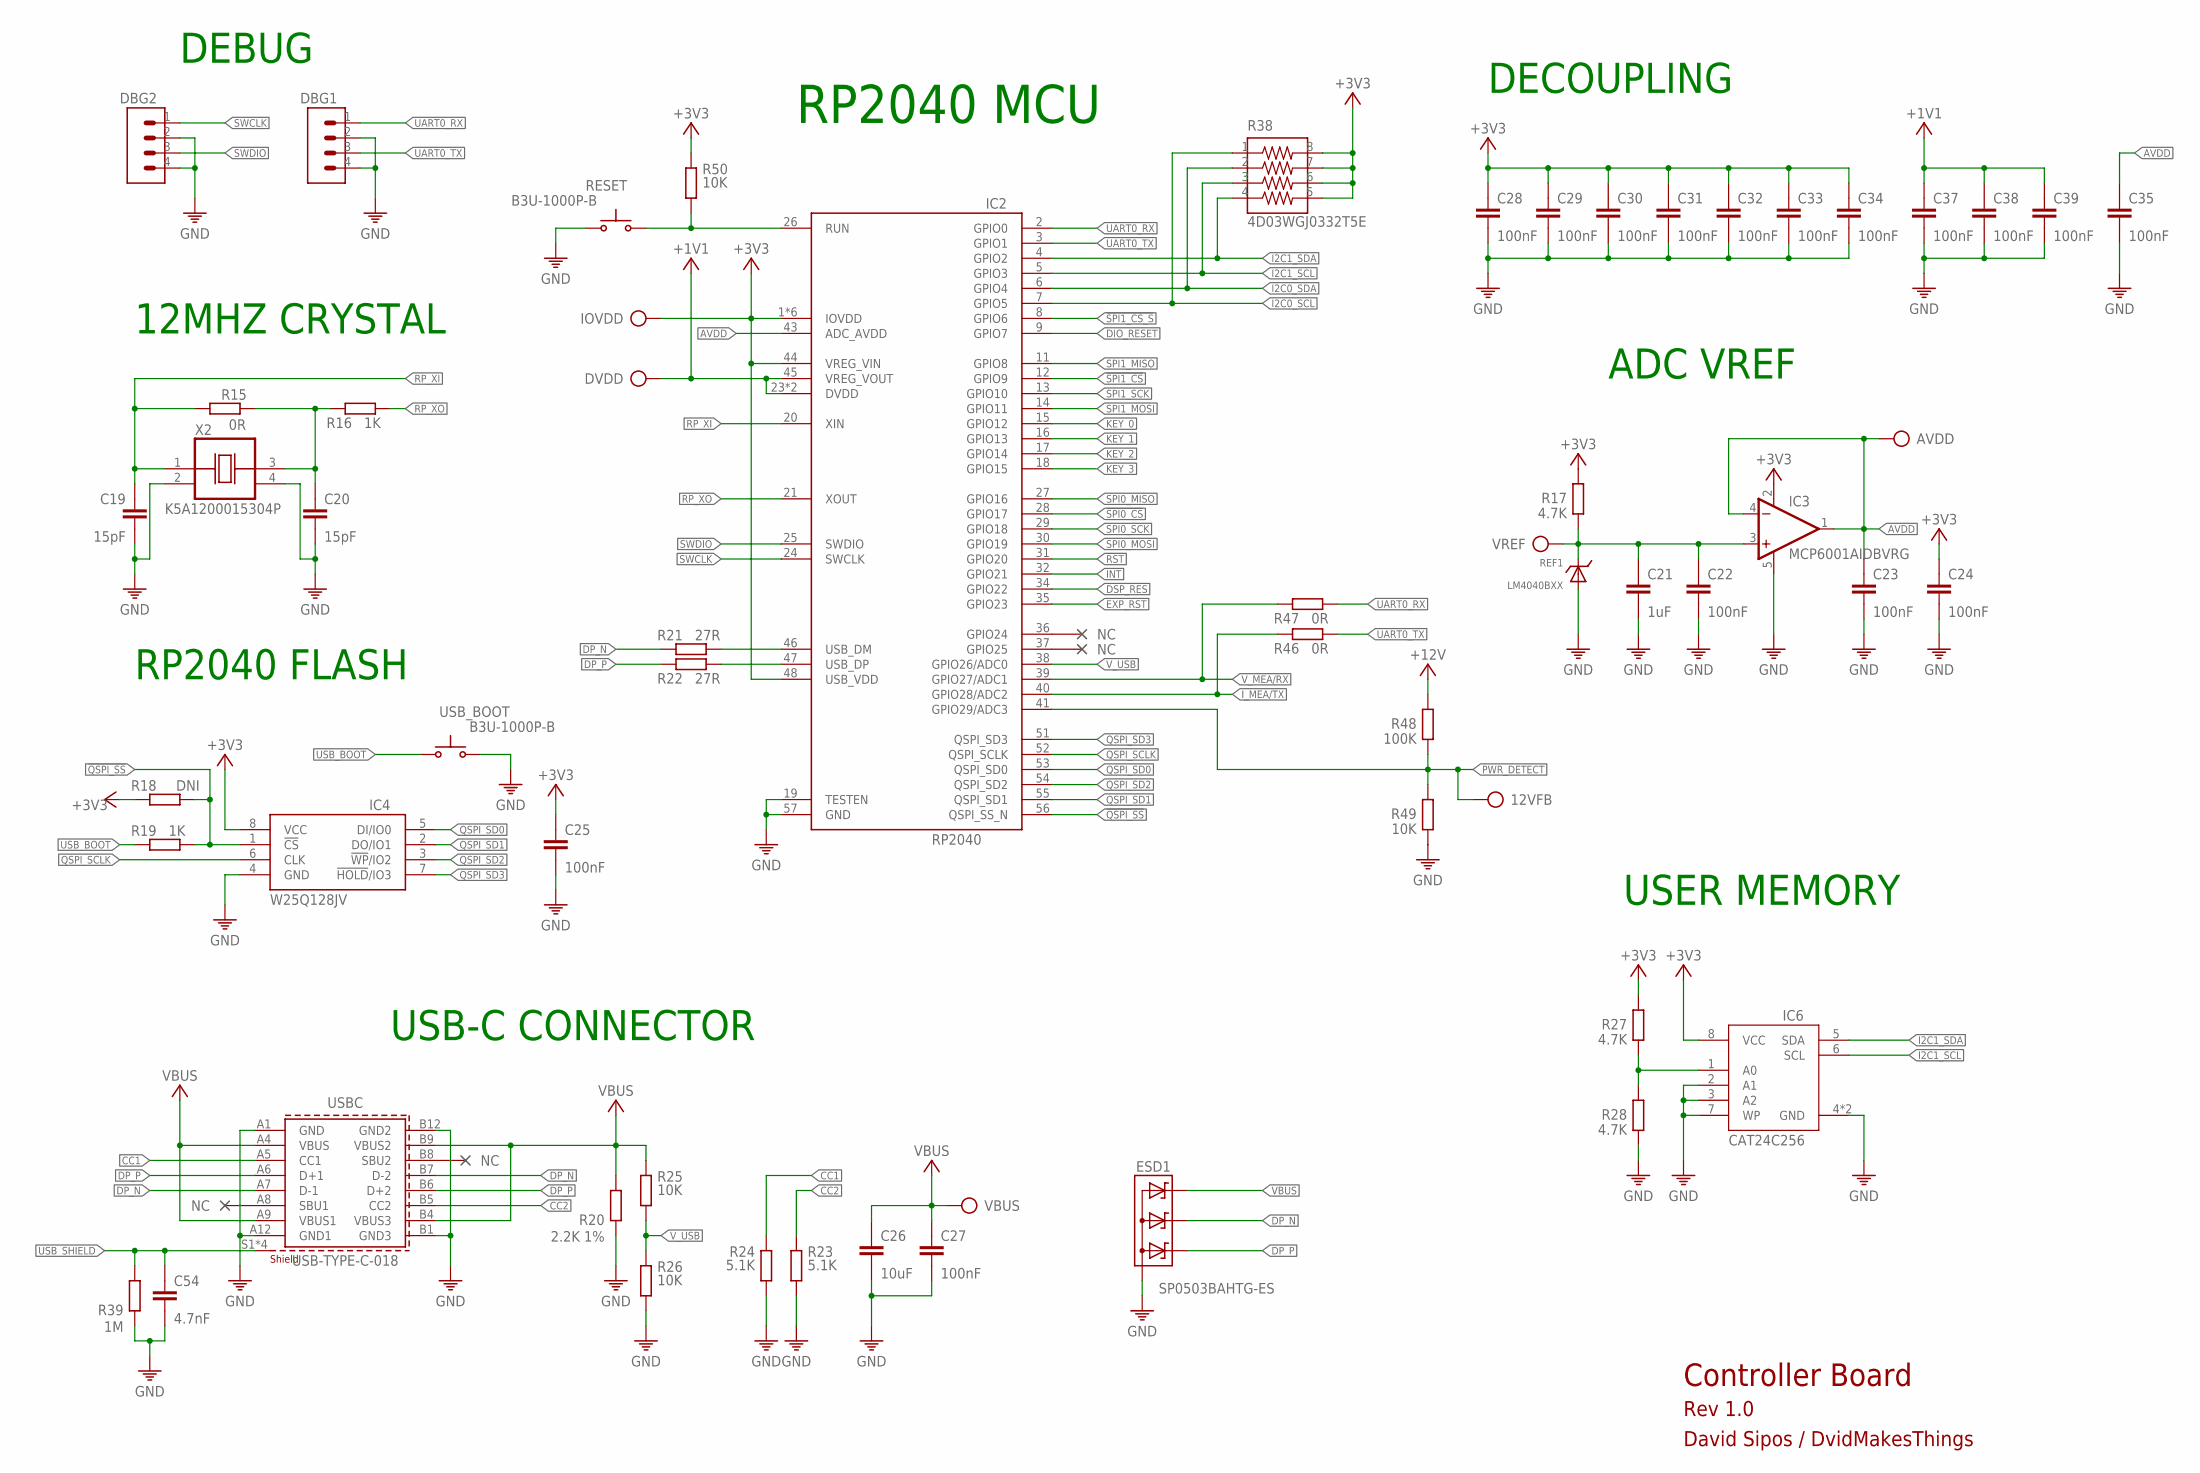
[picture p208: schematic Controller-Board_Rack-PDU.sch, sheet 1]

Parts:
12VFB: TP
AVDD: TP
C19, C20: 15pF; C0402
C21: 1uF; C0402
C22, C23, C24, C25, C28, C29, C30, C31, C32, C33, C34, C35, C37, C38, C39: 100nF; C0402
C26: 10uF; 0805
C27: 100nF; 0402
C54: 4.7nF; 0402
DBG1, DBG2: CON-1X4; 1X4
DVDD: TP
ESD1: SP0503BAHTG-ES; SOT143
IC2: RP2040; QFN40P700X700X100-57T510
IC3: MCP6001AIDBVRG; SOT23-5
IC4: W25Q128JVPIQ; SON127P600X500X75-8N
IC6: CAT24C256HU4IGT3; SON50P300X200X50-9T130X140N
IOVDD: TP
R15, R46, R47: 0R; 0402
R16, R19: 1K; 0402
R17, R27, R28: 4.7K; 0402
R18: DNI; 0402
R20: 2.2K 1%; 0402
R21, R22: 27R; 0402
R23, R24: 5.1K; 0402
R25, R26, R49, R50: 10K; 0402
R38: 4D03WGJ0332T5E; 742C083103JP
R39: 1M; 0402
R48: 100K; 0402
REF1: LM4040BXX; SOT23
RESET: B3U-1000P-B; SWITCH-OMRON_B3U-1000P
USBC: USB-TYPE-C-018; 629722000214
USB_BOOT: B3U-1000P-B; SWITCH-OMRON_B3U-1000P
VBUS: TP
VREF: TP
X2: K5A1200015304P; OSCCC500X320X130

Connections:
!INT: IC2.32 (GPIO21)
!QSPI_SS: IC2.56 (QSPI_SS_N), IC4.1 (!CS), R18.1, R19.2
!RST: IC2.31 (GPIO20)
!SPI0_CS: IC2.28 (GPIO17)
!SPI1_CS: IC2.12 (GPIO9)
!SPI1_CS_S: IC2.8 (GPIO6)
+1V1: C37.1, C38.1, C39.1, DVDD.TP, IC2.23 (DVDD), IC2.45 (VREG_VOUT)
+3V3: C24.1, C25.1, C28.1, C29.1, C30.1, C31.1, C32.1, C33.1, C34.1, IC2.1 (IOVDD), IC2.44 (VREG_VIN), IC2.48 (USB_VDD), IC3.2 (V+), IC4.8 (VCC), IC6.8 (VCC), IOVDD.TP, R17.2, R18.2, R27.2, R38.5, R38.6, R38.7, R38.8, R50.1
+12V: R48.2
AVDD: AVDD.TP, C23.1, C35.1, IC2.43 (ADC_AVDD), IC3.1 (OUT), IC3.4 (-IN)
CC1: R24.1, USBC.A5 (CC1)
CC2: R23.1, USBC.B5 (CC2)
DIO_RESET: IC2.9 (GPIO7)
DP_N: ESD1.3 (C2), R21.1, USBC.A7 (D-1), USBC.B7 (D-2)
DP_P: ESD1.2 (C1), R22.1, USBC.A6 (D+1), USBC.B6 (D+2)
DSP_RES: IC2.34 (GPIO22)
EXP_RST: IC2.35 (GPIO23)
GND: C19.2, C20.2, C21.2, C22.2, C23.2, C24.2, C25.2, C26.2, C27.2, C28.2, C29.2, C30.2, C31.2, C32.2, C33.2, C34.2, C35.2, C37.2, C38.2, C39.2, C54.2, DBG1.2, DBG1.4, DBG2.2, DBG2.4, ESD1.1 (A), IC2.19 (TESTEN), IC2.57 (GND), IC3.5 (V-), IC4.4 (GND), IC6.2 (A1), IC6.3 (A2), IC6.4 (GND), IC6.7 (WP), R20.2, R23.2, R24.2, R26.2, R28.1, R39.2, R49.1, REF1.2 (A), RESET.2 (S), USBC.A1 (GND), USBC.A12 (GND1), USBC.B1 (GND3), USBC.B12 (GND2), USB_BOOT.2 (S), X2.2 (VSS), X2.4 (VDD)
I2C0_SCL: IC2.7 (GPIO5), R38.1
I2C0_SDA: IC2.6 (GPIO4), R38.2
I2C1_SCL: IC2.5 (GPIO3), IC6.6 (SCL), R38.3
I2C1_SDA: IC2.4 (GPIO2), IC6.5 (SDA), R38.4
I_MEA/TX: IC2.40 (GPIO28/ADC2), R46.1
KEY_0: IC2.15 (GPIO12)
KEY_1: IC2.16 (GPIO13)
KEY_2: IC2.17 (GPIO14)
KEY_3: IC2.18 (GPIO15)
unnamed: C20.1, R15.2, R16.1, X2.3 (OUT)
unnamed: IC2.26 (RUN), R50.2, RESET.1
unnamed: IC6.1 (A0), R27.1, R28.2
PWR_DETECT: 12VFB.TP, IC2.41 (GPIO29/ADC3), R48.1, R49.2
QSPI_SCLK: IC2.52 (QSPI_SCLK), IC4.6 (CLK)
QSPI_SD0: IC2.53 (QSPI_SD0), IC4.5 (DI/IO0)
QSPI_SD1: IC2.55 (QSPI_SD1), IC4.2 (DO/IO1)
QSPI_SD2: IC2.54 (QSPI_SD2), IC4.3 (!WP!/IO2)
QSPI_SD3: IC2.51 (QSPI_SD3), IC4.7 (!HOLD!/IO3)
RP_XI: C19.1, IC2.20 (XIN), R15.1, X2.1 (CON)
RP_XO: IC2.21 (XOUT), R16.2
SPI0_MISO: IC2.27 (GPIO16)
SPI0_MOSI: IC2.30 (GPIO19)
SPI0_SCK: IC2.29 (GPIO18)
SPI1_MISO: IC2.11 (GPIO8)
SPI1_MOSI: IC2.14 (GPIO11)
SPI1_SCK: IC2.13 (GPIO10)
SWCLK: DBG2.1, IC2.24 (SWCLK)
SWDIO: DBG2.3, IC2.25 (SWDIO)
UART0_RX: DBG1.1, IC2.2 (GPIO0), R47.2
UART0_TX: DBG1.3, IC2.3 (GPIO1), R46.2
USB_BOOT: R19.1, USB_BOOT.1
USB_DP_N: IC2.46 (USB_DM), R21.2
USB_DP_P: IC2.47 (USB_DP), R22.2
USB_SHIELD: C54.1, R39.1, USBC.S1 (SHIELD)
VBUS: C26.1, C27.1, ESD1.4 (C3), R20.1, R25.1, USBC.A4 (VBUS), USBC.A9 (VBUS1), USBC.B4 (VBUS3), USBC.B9 (VBUS2), VBUS.TP
VREF: C21.1, C22.1, IC3.3 (+IN), R17.1, REF1.1 (C), VREF.TP
V_MEA/RX: IC2.39 (GPIO27/ADC1), R47.1
V_USB: IC2.38 (GPIO26/ADC0), R25.2, R26.1

Notes on the sheet:
USB-C CONNECTOR
DECOUPLING
12MHZ CRYSTAL
RP2040 MCU
RP2040 FLASH
USER MEMORY
ADC VREF
DEBUG
Controller Board
Rev 1.0
David Sipos / DvidMakesThings

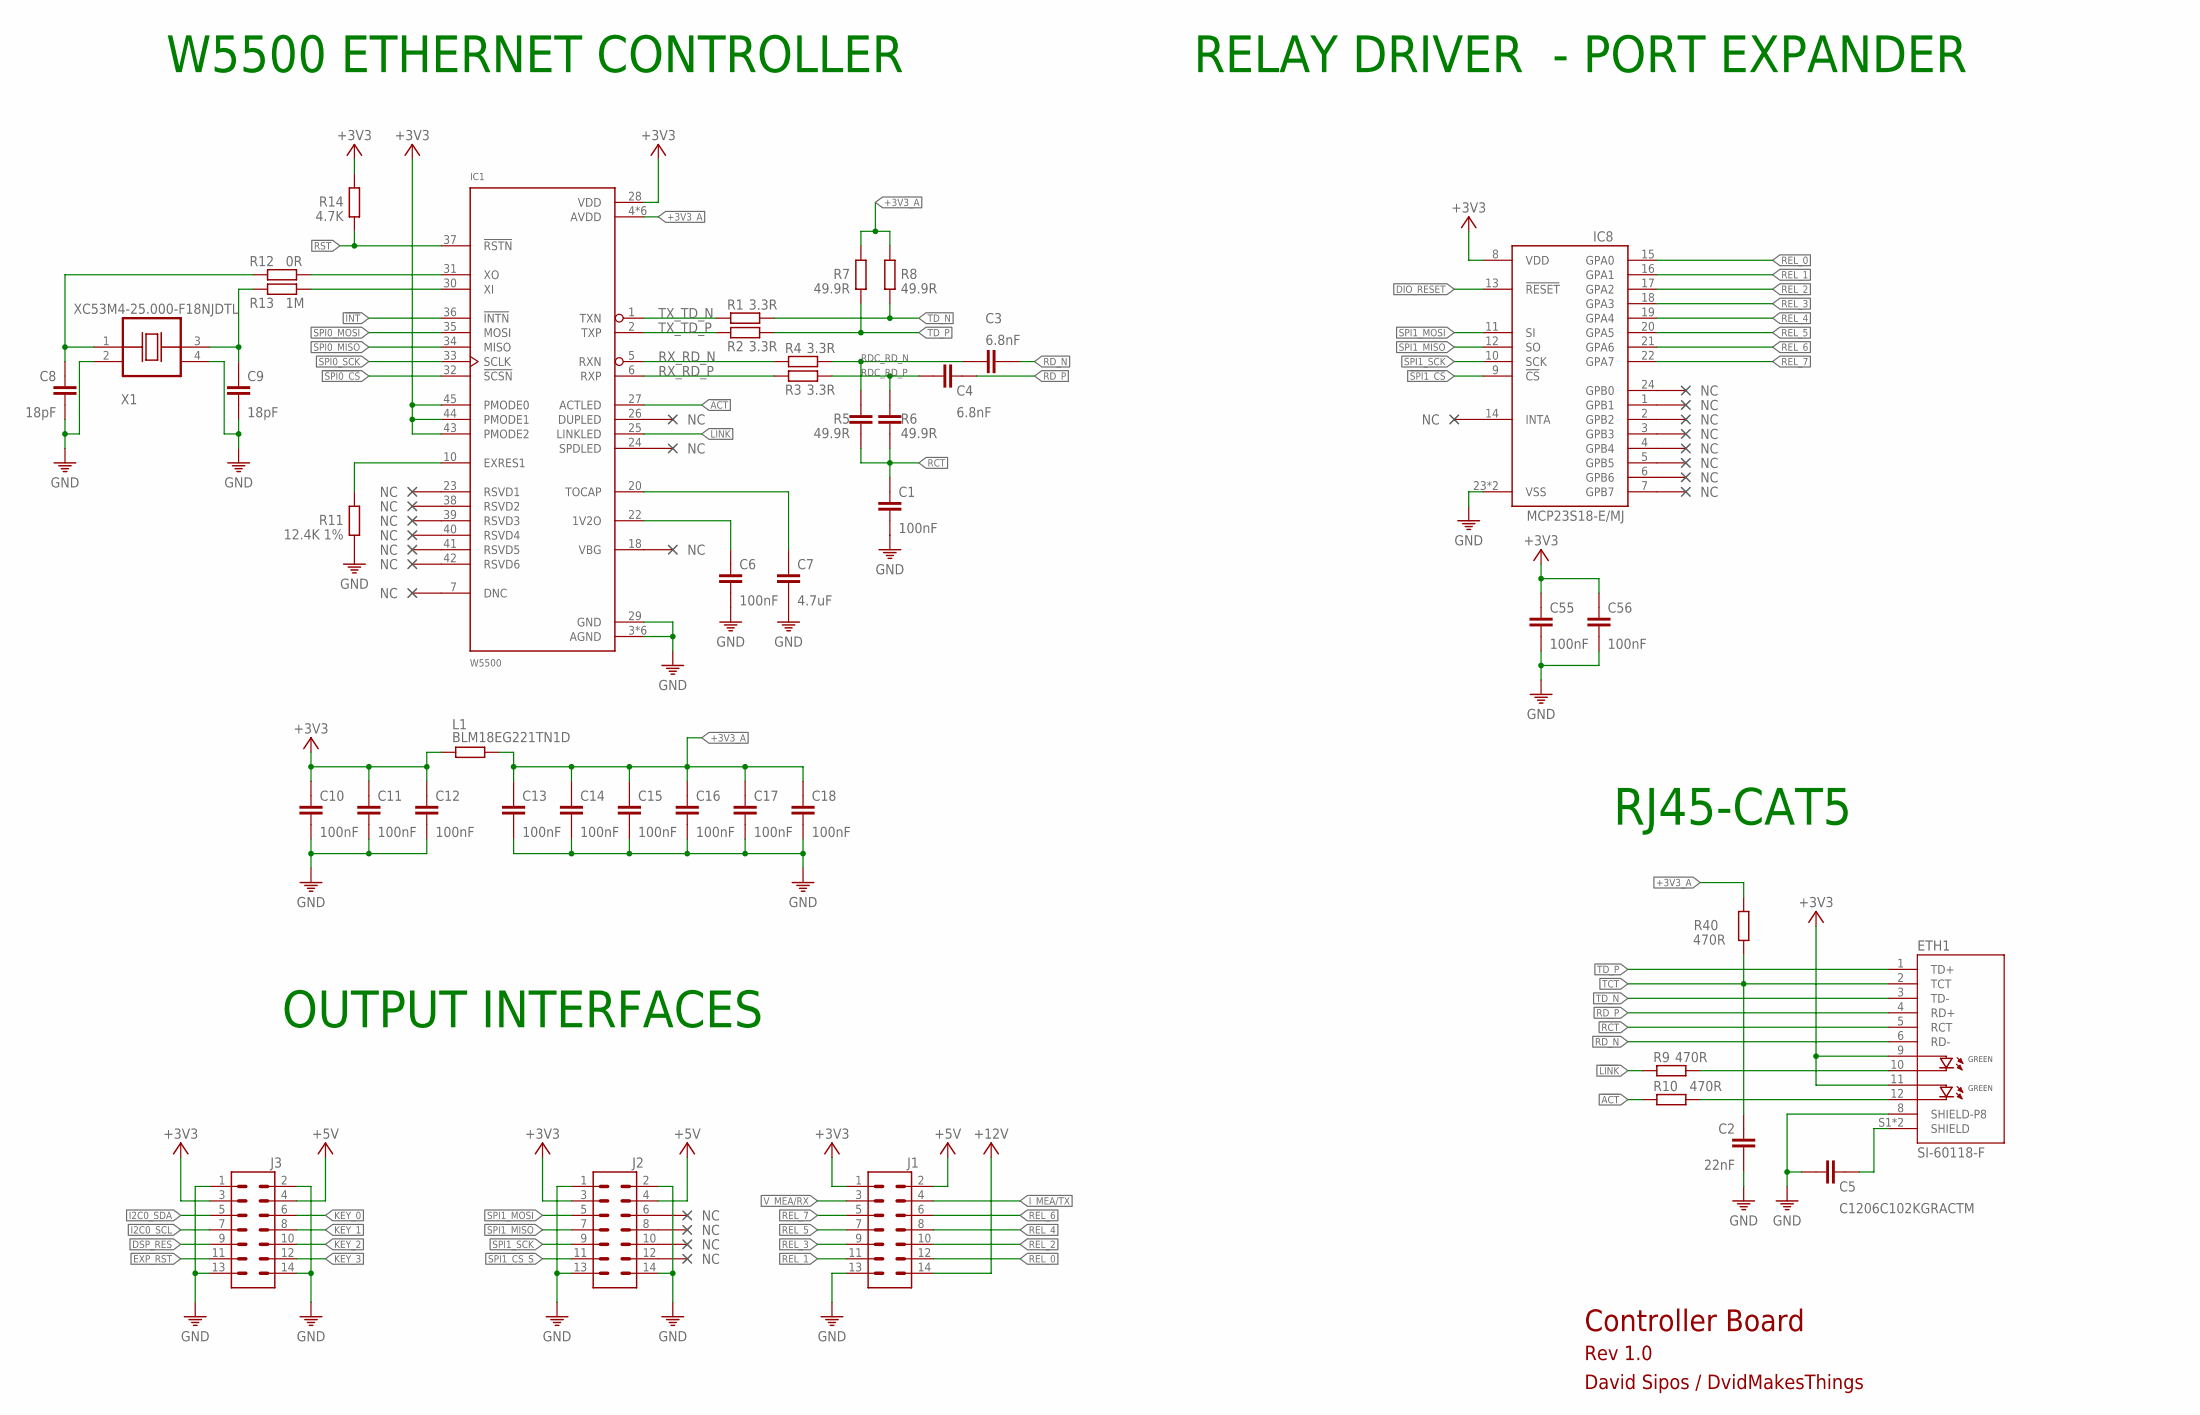
[picture p209: schematic Controller-Board_Rack-PDU.sch, sheet 2]

Parts:
C1, C6, C10, C11, C12, C13, C14, C15, C16, C17, C18, C55, C56: 100nF; C0402
C2: 22nF; C0402
C3, C4: 6.8nF; C0402
C5: C1206C102KGRACTM; C1206
C7: 4.7uF; C0402
C8, C9: 18pF; C0402
ETH1: SI-60118-F; RJ45-CAT5
IC1: W5500; LQFP48
IC8: MCP23S18-E/MJ; QFN50P400X400X100-25T265
J1, J2, J3: CON-2X7; 2X7
L1: BLM18EG221TN1D; 0603
R1, R2, R3, R4: 3.3R; 0402
R5, R6: 49.9R; C0402
R7, R8: 49.9R; 0402
R9, R10, R40: 470R; 0402
R11: 12.4K 1%; 0402
R12: 0R; 0402
R13: 1M; 0402
R14: 4.7K; 0402
X1: XC53M4-25.000-F18NJDTL; OSCCC500X320X130

Connections:
!ACT: IC1.27 (ACTLED), R10.1
!INT: IC1.36 (!INTN)
!LINK: IC1.25 (LINKLED), R9.1
!RST: IC1.37 (!RSTN), R14.1
!SPI0_CS: IC1.32 (!SCSN)
!SPI1_CS: IC8.9 (!CS)
!SPI1_CS_S: J2.11
+3V3: C10.1, C11.1, C12.1, C55.1, C56.1, ETH1.9 (GA1), ETH1.11 (GA2), IC1.28 (VDD), IC1.43 (PMODE2), IC1.44 (PMODE1), IC1.45 (PMODE0), IC8.8 (VDD), J1.1, J2.3, J3.3, L1.1, R14.2
+3V3_A: C13.1, C14.1, C15.1, C16.1, C17.1, C18.1, IC1.4 (AVDD), L1.2, R7.2, R8.2, R40.2
+5V: J1.2, J2.4, J3.4
+12V: J1.14
CHASSIS: C5.2, ETH1.S1 (SHIELD)
DIO_RESET: IC8.13 (!RESET)
DSP_RES: J3.9
EXP_RST: J3.11
GND: C1.2, C2.2, C5.1, C6.2, C7.2, C8.2, C9.2, C10.2, C11.2, C12.2, C13.2, C14.2, C15.2, C16.2, C17.2, C18.2, C55.2, C56.2, ETH1.8 (SHIELD-P8), IC1.3 (AGND), IC1.29 (GND), IC8.23 (VSS), J1.13, J2.1, J2.2, J2.13, J2.14, J3.1, J3.2, J3.13, J3.14, R11.1, X1.2 (VSS), X1.4 (VDD)
I2C0_SCL: J3.7
I2C0_SDA: J3.5
I_MEA/TX: J1.4
KEY_0: J3.6
KEY_1: J3.8
KEY_2: J3.10
KEY_3: J3.12
unnamed: IC1.10 (EXRES1), R11.2
unnamed: ETH1.10 (GK1), R9.2
unnamed: ETH1.12 (GK2), R10.2
unnamed: C6.1, IC1.22 (1V2O)
unnamed: C7.1, IC1.20 (TOCAP)
unnamed: C8.1, R12.1, X1.1 (CON)
unnamed: C9.1, R13.1, X1.3 (OUT)
unnamed: IC1.31 (XO), R12.2
unnamed: IC1.30 (XI), R13.2
RCT: C1.1, ETH1.5 (RCT), R5.1, R6.1
RDC_RD_N: C3.1, R4.2, R5.2
RDC_RD_P: C4.1, R3.2, R6.2
RD_N: C3.2, ETH1.6 (RD-)
RD_P: C4.2, ETH1.4 (RD+)
REL_0: IC8.15 (GPA0), J1.12
REL_1: IC8.16 (GPA1), J1.11
REL_2: IC8.17 (GPA2), J1.10
REL_3: IC8.18 (GPA3), J1.9
REL_4: IC8.19 (GPA4), J1.8
REL_5: IC8.20 (GPA5), J1.7
REL_6: IC8.21 (GPA6), J1.6
REL_7: IC8.22 (GPA7), J1.5
RX_RD_N: IC1.5 (RXN), R4.1
RX_RD_P: IC1.6 (RXP), R3.1
SPI0_MISO: IC1.34 (MISO)
SPI0_MOSI: IC1.35 (MOSI)
SPI0_SCK: IC1.33 (SCLK)
SPI1_MISO: IC8.12 (SO), J2.7
SPI1_MOSI: IC8.11 (SI), J2.5
SPI1_SCK: IC8.10 (SCK), J2.9
TCT: C2.1, ETH1.2 (TCT), R40.1
TD_N: ETH1.3 (TD-), R1.2, R8.1
TD_P: ETH1.1 (TD+), R2.2, R7.1
TX_TD_N: IC1.1 (TXN), R1.1
TX_TD_P: IC1.2 (TXP), R2.1
V_MEA/RX: J1.3

Notes on the sheet:
W5500 ETHERNET CONTROLLER
RJ45-CAT5
OUTPUT INTERFACES
RELAY DRIVER - PORT EXPANDER
Controller Board
Rev 1.0
David Sipos / DvidMakesThings

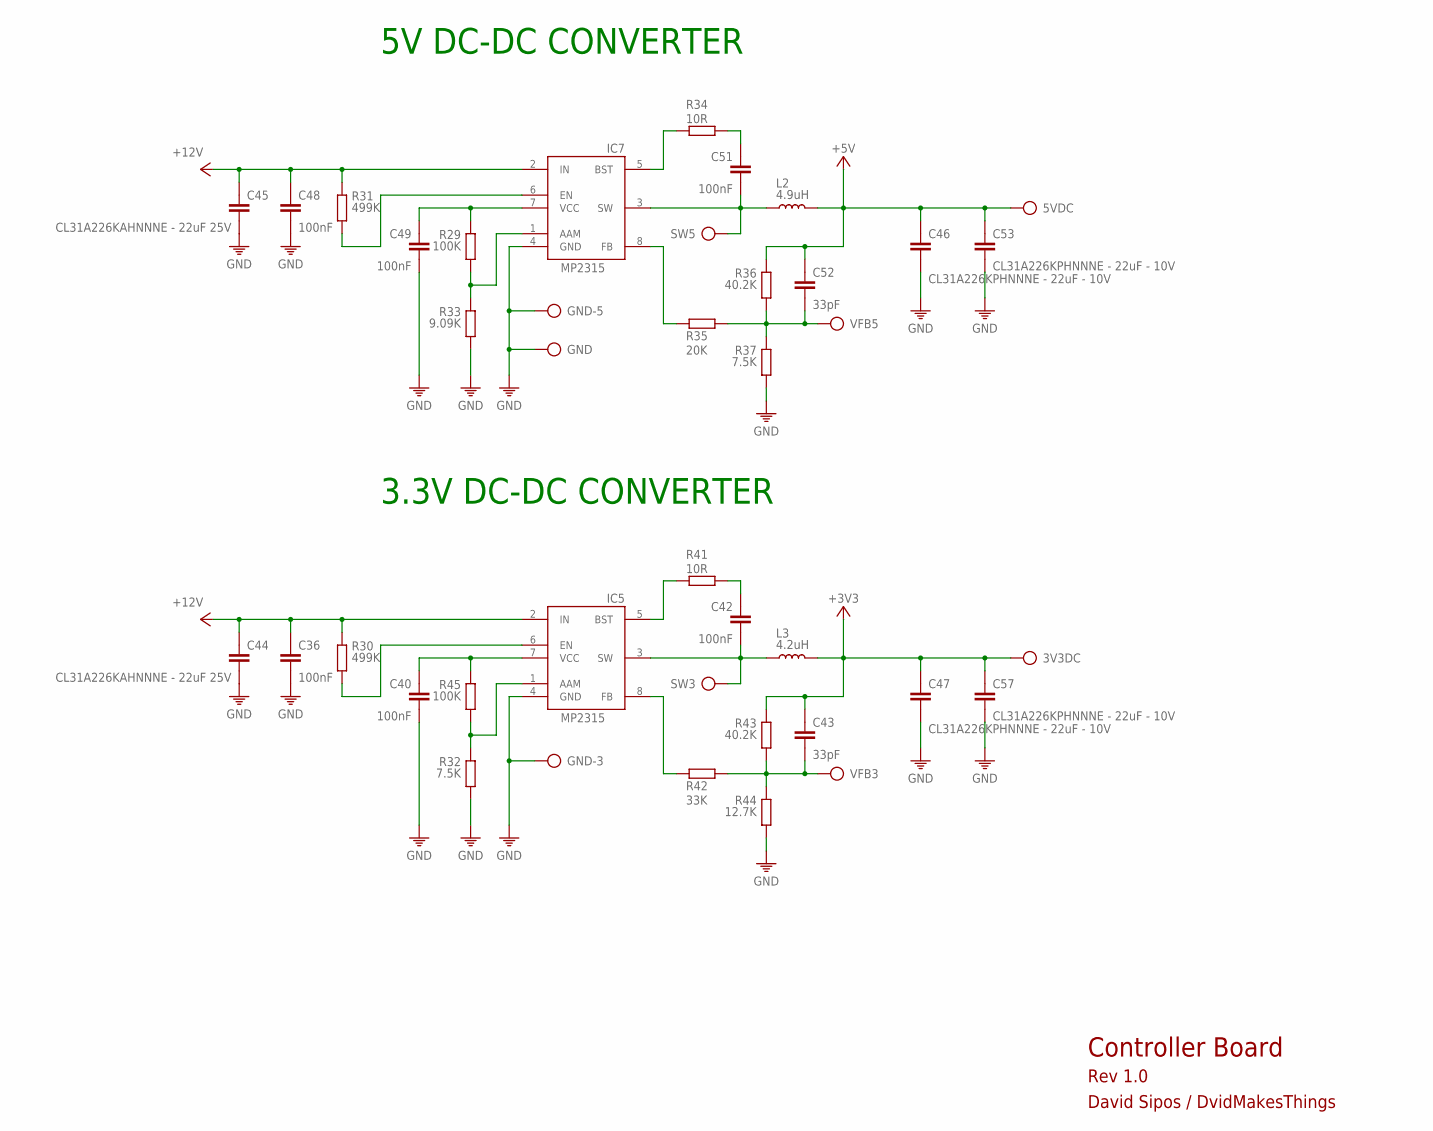
[picture p210: schematic Controller-Board_Rack-PDU.sch, sheet 3]

Parts:
3V3DC, 5VDC: TP
C36, C40, C42, C48, C49, C51: 100nF; 0402
C43, C52: 33pF; 0402
C44, C45: CL31A226KAHNNNE - 22uF 25V; C1206
C46, C47, C53, C57: CL31A226KPHNNNE - 22uF - 10V; C1206
GND: TP
GND-3, GND-5: TP
IC5: MP2315S; SOT65P280X110-8N
IC7: MP2315GJ-Z; SOT65P280X110-8N
L2: 4.9uH; SRR5228A
L3: 4.2uH; SRR5228A
R29, R45: 100K; 0402
R30, R31: 499K; 0402
R32, R37: 7.5K; 0402
R33: 9.09K; 0402
R34, R41: 10R; 0402
R35: 20K; 0402
R36, R43: 40.2K; 0402
R42: 33K; 0402
R44: 12.7K; 0402
SW3, SW5: TP
VFB3, VFB5: TP

Connections:
+3V3: 3V3DC.TP, C43.1, C47.1, C57.1, L3.2, R43.1
+5V: 5VDC.TP, C46.1, C52.1, C53.1, L2.2, R36.1
+12V: C36.1, C44.1, C45.1, C48.1, IC5.2 (IN), IC7.2 (IN), R30.1, R31.1
GND: C36.2, C40.2, C44.2, C45.2, C46.2, C47.2, C48.2, C49.2, C53.2, C57.2, GND.TP, GND-3.TP, GND-5.TP, IC5.4 (GND), IC7.4 (GND), R32.2, R33.2, R37.2, R44.2
unnamed: IC5.5 (BST), R41.2
unnamed: IC5.1 (AAM), R32.1, R45.2
unnamed: IC7.1 (AAM), R29.2, R33.1
unnamed: IC7.6 (EN), R31.2
unnamed: C49.1, IC7.7 (VCC), R29.1
unnamed: IC5.8 (FB), R42.1
unnamed: C42.2, IC5.3 (SW), L3.1, SW3.TP
unnamed: C42.1, R41.1
unnamed: C43.2, R42.2, R43.2, R44.1, VFB3.TP
unnamed: IC5.6 (EN), R30.2
unnamed: C40.1, IC5.7 (VCC), R45.1
unnamed: IC7.5 (BST), R34.2
unnamed: IC7.8 (FB), R35.1
unnamed: C51.2, IC7.3 (SW), L2.1, SW5.TP
unnamed: C51.1, R34.1
unnamed: C52.2, R35.2, R36.2, R37.1, VFB5.TP

Notes on the sheet:
5V DC-DC CONVERTER
Controller Board
Rev 1.0
David Sipos / DvidMakesThings
3.3V DC-DC CONVERTER
