DvidMakesThings/HW_10-In-Rack_PDU/src/HardwareDesign/Display-Board_Rack-PDU.sch

## EAGLE design src/HardwareDesign/Display-Board_Rack-PDU.sch (2025-02-18)

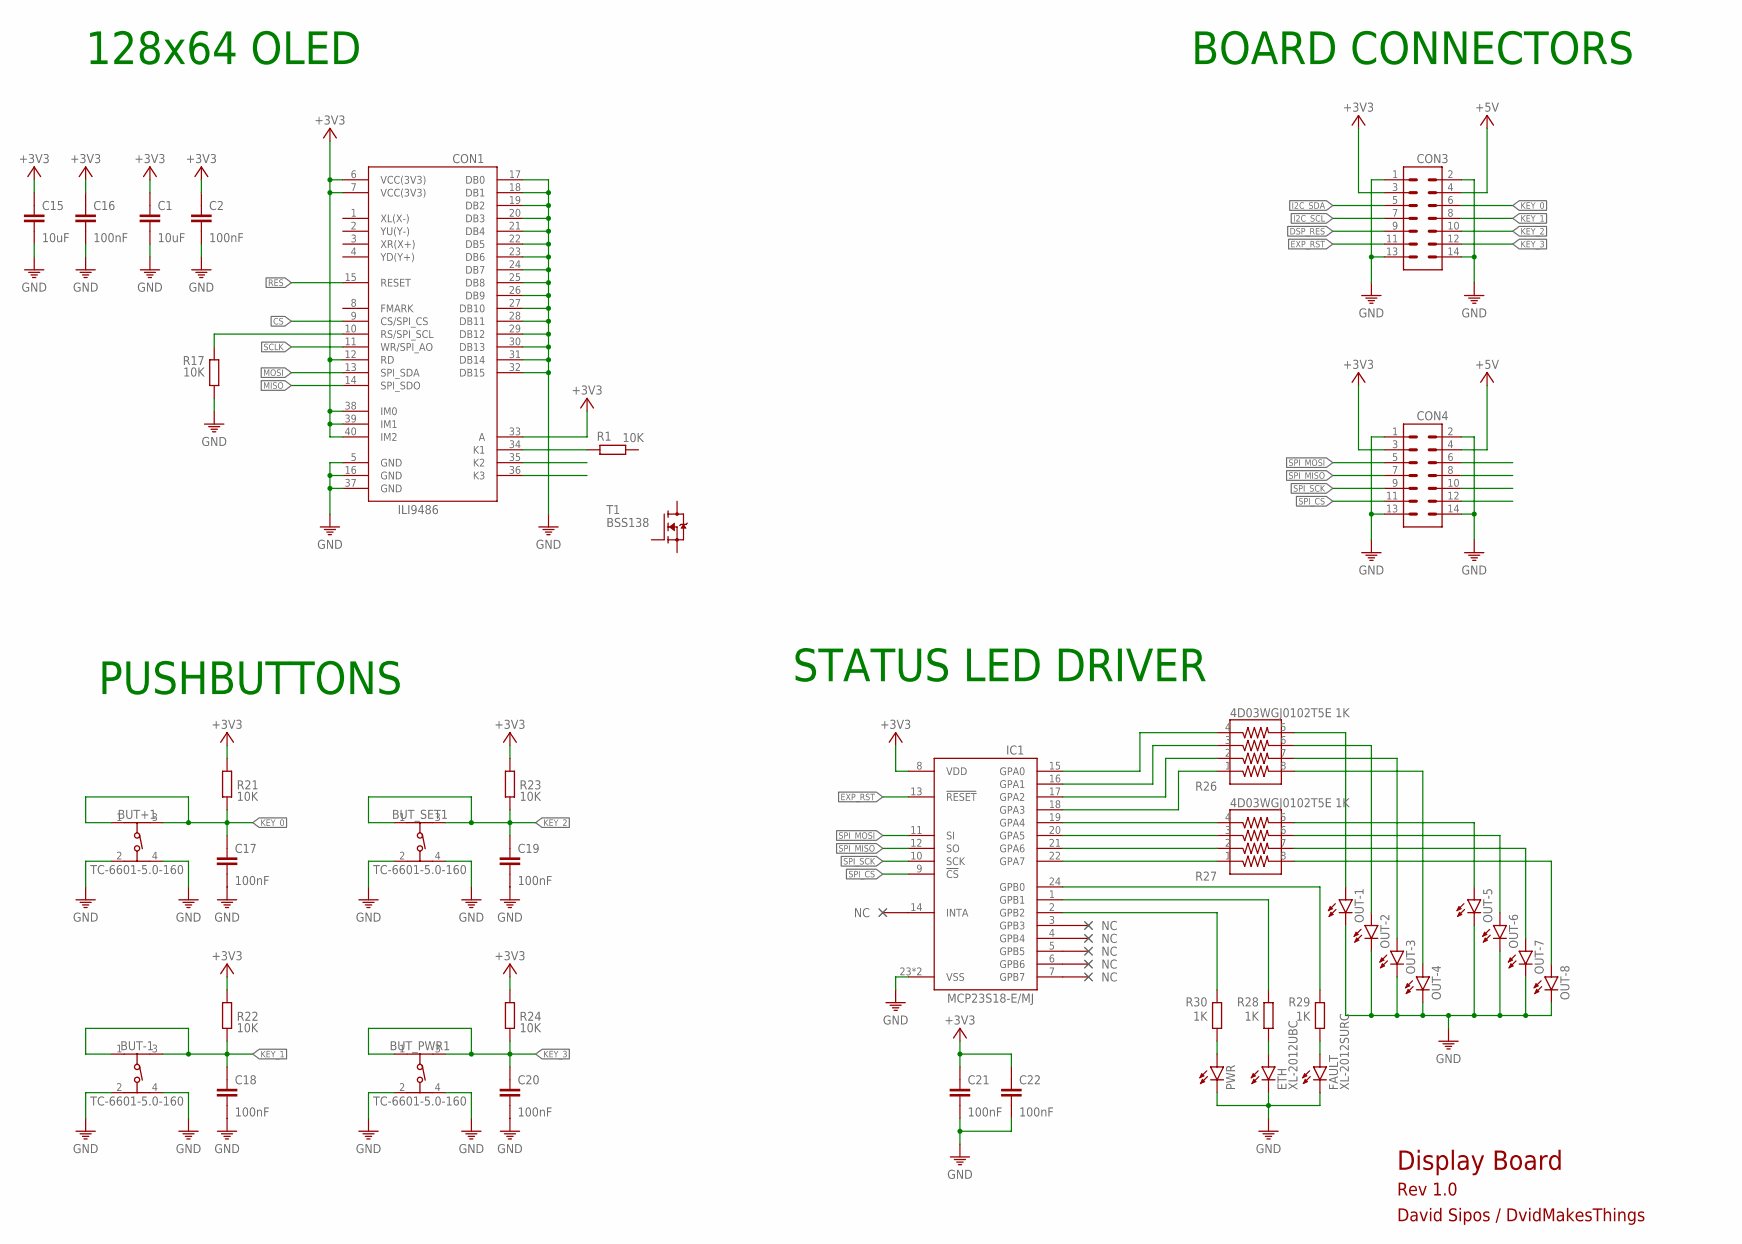
[picture p211: schematic Display-Board_Rack-PDU.sch]

Parts:
BUT+1: TC-6601-5.0-160; 430182043816
BUT-1: TC-6601-5.0-160; 430182043816
BUT_PWR1: TC-6601-5.0-160; 430182043816
BUT_SET1: TC-6601-5.0-160; 430182043816
C1, C15: 10uF; C0402
C2, C16, C17, C18, C19, C20, C21, C22: 100nF; C0402
CON1: 3.5IN_TFTLCD; FPC40
CON3, CON4: CON-2X72; 2X7-SIDE
ETH: XL-2012UBC; CHIP-LED0805
FAULT: XL-2012SURC; CHIP-LED0805
IC1: MCP23S18-E/MJ; QFN50P400X400X100-25T265
OUT-1, OUT-2, OUT-3, OUT-4, OUT-5, OUT-6, OUT-7, OUT-8: LEDCHIP-LED0805; CHIP-LED0805
PWR: LEDCHIP-LED0805; CHIP-LED0805
R1, R17, R21, R22, R23, R24: 10K; 0402
R26, R27: 4D03WGJ0102T5E 1K; 742C083103JP
R28, R29, R30: 1K; 0402
T1: BSS138; SOT23

Connections:
+3V3: C1.1, C2.1, C15.1, C16.1, C21.1, C22.1, CON1.6 (VCC(3V3)), CON1.7 (VCC(3V3)), CON1.12 (RD), CON1.33 (A), CON1.38 (IM0), CON1.39 (IM1), CON1.40 (IM2), CON3.3, CON4.3, IC1.8 (VDD), R21.1, R22.1, R23.1, R24.1
+5V: CON3.4, CON4.4
CS: CON1.9 (CS/SPI_CS)
DSP_RES: CON3.9
EXP_RST: CON3.11, IC1.13 (!RESET)
GND: BUT+1.2, BUT+1.4, BUT-1.2, BUT-1.4, BUT_PWR1.2, BUT_PWR1.4, BUT_SET1.2, BUT_SET1.4, C1.2, C2.2, C15.2, C16.2, C17.2, C18.2, C19.2, C20.2, C21.2, C22.2, CON1.5 (GND), CON1.16 (GND), CON1.17 (DB0), CON1.18 (DB1), CON1.19 (DB2), CON1.20 (DB3), CON1.21 (DB4), CON1.22 (DB5), CON1.23 (DB6), CON1.24 (DB7), CON1.25 (DB8), CON1.26 (DB9), CON1.27 (DB10), CON1.28 (DB11), CON1.29 (DB12), CON1.30 (DB13), CON1.31 (DB14), CON1.32 (DB15), CON1.37 (GND), CON3.1, CON3.2, CON3.13, CON3.14, CON4.1, CON4.2, CON4.13, CON4.14, ETH.C, FAULT.C, IC1.23 (VSS), OUT-1.C, OUT-2.C, OUT-3.C, OUT-4.C, OUT-5.C, OUT-6.C, OUT-7.C, OUT-8.C, PWR.C, R17.1
I2C_SCL: CON3.7
I2C_SDA: CON3.5
KEY_0: BUT+1.1, BUT+1.3, C17.1, CON3.6, R21.2
KEY_1: BUT-1.1, BUT-1.3, C18.1, CON3.8, R22.2
KEY_2: BUT_SET1.1, BUT_SET1.3, C19.1, CON3.10, R23.2
KEY_3: BUT_PWR1.1, BUT_PWR1.3, C20.1, CON3.12, R24.2
MISO: CON1.14 (SPI_SDO)
MOSI: CON1.13 (SPI_SDA)
unnamed: CON1.10 (RS/SPI_SCL), R17.2
unnamed: CON1.34 (K1), R1.2
unnamed: IC1.1 (GPB1), R28.1
unnamed: IC1.2 (GPB2), R30.1
unnamed: IC1.24 (GPB0), R29.1
unnamed: IC1.15 (GPA0), R26.4
unnamed: IC1.16 (GPA1), R26.3
unnamed: IC1.17 (GPA2), R26.2
unnamed: IC1.18 (GPA3), R26.1
unnamed: IC1.19 (GPA4), R27.4
unnamed: IC1.20 (GPA5), R27.3
unnamed: IC1.21 (GPA6), R27.2
unnamed: IC1.22 (GPA7), R27.1
unnamed: OUT-1.A, R26.5
unnamed: OUT-2.A, R26.6
unnamed: OUT-3.A, R26.7
unnamed: OUT-4.A, R26.8
unnamed: OUT-5.A, R27.5
unnamed: OUT-6.A, R27.6
unnamed: OUT-7.A, R27.7
unnamed: OUT-8.A, R27.8
unnamed: FAULT.A, R29.2
unnamed: ETH.A, R28.2
unnamed: PWR.A, R30.2
RES: CON1.15 (RESET)
SCLK: CON1.11 (WR/SPI_AO)
SPI_CS: CON4.11, IC1.9 (!CS)
SPI_MISO: CON4.7, IC1.12 (SO)
SPI_MOSI: CON4.5, IC1.11 (SI)
SPI_SCK: CON4.9, IC1.10 (SCK)

Notes on the sheet:
BOARD CONNECTORS
128x64 OLED
PUSHBUTTONS
STATUS LED DRIVER
Display Board
Rev 1.0
David Sipos / DvidMakesThings
