DvidMakesThings/HW_10-In-Rack_PDU/src/Software/ENERGIS/misc/uart_command_handler.c

/**
 * @file uart_command_handler.c
 * @author David Sipos (DvidMakesThings)
 * @defgroup uart UART Command Handler
 * @brief UART command handler for ENERGIS PDU (10-Inch Rack).
 * @{
 * @version 1.0
 * @date 2025-03-03
 *
 * Implements command parsing and execution over UART (USB-CDC).
 * Provides network, system, and EEPROM control via textual commands.
 *
 * @project ENERGIS - The Managed PDU Project for 10-Inch Rack
 * @github https://github.com/DvidMakesThings/HW_10-In-Rack_PDU
 */

#include "CONFIG.h"
#include <ctype.h>
#include <stdio.h>
#include <stdlib.h>
#include <string.h>

extern volatile uint32_t bootloader_trigger;
extern wiz_NetInfo g_net_info; // current network info in RAM

/**
 * @brief Remove leading/trailing whitespace and non-printable characters from a string.
 *
 * Cleans the input string in-place, removing unwanted characters and whitespace.
 *
 * @param s Pointer to the string to be trimmed.
 * @return Pointer to the cleaned string.
 */
static char *trim(char *s) {
    // Skip leading whitespace
    while (*s && isspace((unsigned char)*s))
        s++;

    // Early out if string is empty after trim
    if (*s == '\0')
        return s;

    // Remove trailing whitespace + non-printables
    char *end = s + strlen(s) - 1;
    while (end > s && (isspace((unsigned char)*end) || !isprint((unsigned char)*end))) {
        *end-- = '\0';
    }

    // Clean inline non-printables / control characters
    char *read = s;
    char *write = s;
    while (*read) {
        unsigned char c = *read++;
        if (isprint(c)) {
            *write++ = c;
        }
        // else: skip glitch byte silently
    }
    *write = '\0';

    return s;
}

/**
 * @brief Parse and execute a received UART command string.
 *
 * Handles all supported commands, dispatching to the appropriate handler.
 *
 * @param cmd_in The input command string.
 */
static void process_command(const char *cmd_in) {
    char cmd[128];
    strncpy(cmd, cmd_in, sizeof(cmd) - 1);
    cmd[sizeof(cmd) - 1] = '\0';

    // Trim and uppercase
    char *trimmed = trim(cmd);
    for (char *p = trimmed; *p; ++p)
        *p = toupper(*p);

    ECHO("Received CMD: \"%s\"\r\n", cmd);
    if (strcmp(trimmed, "HELP") == 0) {
        printHelp();
    } else if (strcmp(trimmed, "BOOTSEL") == 0) {
        bootsel_trigger();
    } else if (strcmp(trimmed, "REBOOT") == 0) {
        reboot();
    } else if (strcmp(trimmed, "DUMP_EEPROM") == 0) {
        dump_eeprom();
    } else if (strcmp(trimmed, "RFS") == 0) {
        EEPROM_WriteFactoryDefaults();
        watchdog_reboot(0, 0, 0);
    } else if (strncmp(trimmed, "SET_IP ", 7) == 0) {
        set_ip(trimmed + 7, trimmed);
    } else if (strncmp(trimmed, "SET_DNS ", 7) == 0) {
        set_dns(trimmed + 7, trimmed);
    } else if (strncmp(trimmed, "SET_GW ", 7) == 0) {
        set_gateway(trimmed + 7, trimmed);
    } else if (strncmp(trimmed, "SET_SN ", 7) == 0) {
        set_subnet(trimmed + 7, trimmed);
    } else if (strncmp(trimmed, "CONFIG_NETWORK ", 15) == 0) {
        set_network(trimmed + 15, trimmed);
    } else if (strcmp(trimmed, "NETINFO") == 0) {
        ECHO("NETWORK INFORMATION:\r\n");
        print_network_information(g_net_info);
    } else if (strcmp(trimmed, "SYSINFO") == 0) {
        ECHO("SYSTEM INFORMATION:\r\n");
        getSysInfo();
    } else if (strcmp(trimmed, "BAADCAFE") == 0) {
        EEPROM_EraseAll();
    } else if (strcmp(trimmed, "READ_HLW8032") == 0) {
        hlw8032_readings();
    } else if (strncmp(trimmed, "READ_HLW8032 ", 13) == 0) {
        int ch = atoi(trimmed + 13);
        if (ch >= 1 && ch <= 8) {
            hlw8032_read_channel((uint8_t)ch);
        } else {
            setError(false);
            ERROR_PRINT("Invalid channel: %d\r\n", ch);
        }
    } else if (strcmp(trimmed, "GET_TEMP") == 0) {
        read_dieTemp();
    } else if (strncmp(trimmed, "SET_CH ", 7) == 0) {
        handle_uart_set_ch_command(trimmed);
    } else if (strncmp(trimmed, "GET_CH ", 7) == 0) {
        handle_uart_get_ch_command(trimmed);
    } else if (strcmp(trimmed, "CLR_ERR") == 0) {
        setError(false);
    } else if (strcmp(trimmed, "GET_SUPPLY") == 0) {
        float voltage = get_Voltage(V_SUPPLY) * (110000.0f / 10000.0f);
        ECHO("12V SUPPLY VOLTAGE: %.3f V\r\n", voltage);
    } else if (strcmp(trimmed, "GET_USB") == 0) {
        float voltage = get_Voltage(V_USB) * (20000.0f / 10000.0f);
        ECHO("USB SUPPLY VOLTAGE: %.3f V\r\n", voltage);
    } else if (strncmp(trimmed, "CALIBRATE ", 10) == 0) {
        handle_calibrate_command(trimmed + 10);
    } else if (strncmp(trimmed, "SHOW_CALIB ", 11) == 0) {
        int ch = atoi(trimmed + 11);
        if (ch >= 1 && ch <= 8) {
            hlw8032_print_calibration((uint8_t)(ch - 1));
        } else {
            ERROR_PRINT("Invalid channel: %d (must be 1-8)\r\n", ch);
        }
    } else if (strcmp(trimmed, "SHOW_CALIB") == 0) {
        for (uint8_t i = 0; i < 8; i++) {
            hlw8032_print_calibration(i);
        }
    } else if (strcmp(trimmed, "AUTO_CALIBRATE_ZERO") == 0) {
        handle_auto_calibrate_zero();
    } else if (strncmp(trimmed, "AUTO_CALIBRATE_VOLTAGE ", 23) == 0) {
        float ref_voltage = atof(trimmed + 23);
        handle_auto_calibrate_voltage(ref_voltage);
    } else {
        setError(true);
        ERROR_PRINT("Unknown command \"%s\"\r\n", trimmed);
        printHelp();
    }
}

/**
 * @brief Main loop for reading and processing UART commands.
 *
 * Reads characters from UART, assembles lines, and executes commands.
 */
void uart_command_loop(void) {
    static char line[UART_CMD_BUF_LEN];
    static size_t idx = 0;

    int c;
    // Read all available chars without blocking
    while ((c = getchar_timeout_us(0)) != PICO_ERROR_TIMEOUT) {
        if (c == '\r' || c == '\n') {
            if (idx) {
                line[idx] = '\0';
                char *cmd = trim(line);
                if (*cmd)
                    process_command(cmd);
                idx = 0;
            }
        } else {
            // store printable non-null chars
            if (idx < sizeof(line) - 1 && c >= 32 && c < 127) {
                line[idx++] = (char)c;
            }
        }
    }
}

/**
 * @brief Set flag to enter BOOTSEL mode on next reboot.
 *
 * Triggers the bootloader for firmware update via BOOTSEL.
 */
void bootsel_trigger(void) {
    // trigger BOOTSEL on next reboot
    bootloader_trigger = 0xDEADBEEF;
    ECHO("OK: ENTERING BOOTSEL\r\n");
    watchdog_reboot(0, 0, 0);
}

/**
 * @brief Immediately reboot the system.
 *
 * Performs a software reset using the watchdog.
 */
void reboot(void) {
    ECHO("OK: REBOOTING\r\n");
    watchdog_reboot(0, 0, 0);
}
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
